jreuteler/bahareque-modular/de/14-akustik-upgrade.md

# Akustik-Upgrade — Lärmexponierte Wände

> *Dieses Kapitel wurde durch einen Vorschlag von Kim Hansson angeregt — vielen Dank für den Anstoss, das Design an reale städtische Bedingungen anzupassen.*

Das Standardpaneel (STC 40–45) ist für ruhige Wohngebiete ausreichend. Für Gebäude an stark befahrenen Strassen, in der Nähe von Autobahnen oder neben Gewerbe- und Industriezonen können die lärmexponierten Wände einzeln aufgerüstet werden. Es ist nicht nötig, jede Wand aufzurüsten — die meisten Gebäude haben nur eine oder zwei Seiten, die starkem Lärm ausgesetzt sind. Die ruhigen Wände bleiben Standardpaneele.

## Lärmexpositions-Leitfaden

| Situation | Empfohlene Massnahme | Ziel-STC |
|---|---|---|
| Ruhige Wohnstrasse | Standardpaneel — kein Upgrade nötig | 40–45 |
| Mässiger Strassenverkehr | Dichter Mörtel + Lehm-Dämpfungsschicht | 48–52 |
| Stark befahrene Stadtstrasse, Buslinien | Doppelpaneel mit Faser-Hohlraum | 55–62 |
| Autobahn, Industrie, Ausgehviertel | Doppelpaneel mit Faser-Hohlraum + Lehmschicht | 58–65 |

**Das Upgrade nur dort anwenden, wo es nötig ist.** Ein typisches Haus an einer belebten Strasse hat ein oder zwei lärmexponierte Wände (10–15 m²). Die übrigen Wände zeigen zum Garten, Innenhof oder zur ruhigen Seite und verwenden Standardpaneele. So bleibt der Mehraufwand proportional zum tatsächlichen Lärmproblem.

## Option 1: Dichtere Mörtelmischung (günstigste Variante, +3–5 STC)

Der Standard-Flusssand wird durch schwerere Zuschlagstoffe in der Mörtelmischung ersetzt. Gleicher Produktionsprozess, gleicher Rahmen, gleicher Rütteltisch-Guss. Das Paneel ist einfach schwerer.

| Zuschlagstoff | Dichtezunahme | Kosten vs. Standardsand | Verfügbarkeit |
|---|---|---|---|
| Gebrochener Basalt oder Granitfeinteile | +15–20% | Ähnlich | Überall — jeder Steinbruch |
| Eisenschlacke (*escoria*) | +25–30% | Oft gratis | In der Nähe von Stahlwerken, Giessereien |
| Magnetitsand (*arena negra*) | +40% | Gering | Vulkanische Flussbetten (Anden, Zentralamerika) |

- **Paneelgewicht:** fertig ~490–530 kg Basismischung (vs. ~440 kg Standard-Basis) / ~405–440 kg optimierte Mischung (vs. ~360 kg Standard-optimiert). Trockenmontage-Gewicht unverändert bei ~75 kg (dichter Zuschlagstoff wird beim Vor-Ort-Guss zugegeben, nicht in der Werkstattmontage)
- **Mehrkosten:** ~$1–2 pro Paneel
- **STC:** ~43–48
- **Produktionsänderung:** Keine — nur den Zuschlagstoff austauschen. Mischverhältnis bleibt 1:4 Zement:Zuschlag.

**Ideal für:** Seitenwände, die eine moderate Verbesserung brauchen, ohne die Wandstärke oder den Bauprozess zu ändern.

## Option 2: Lehm-Dämpfungsschicht (+5–8 STC)

Eine 10–15 mm dicke Schicht aus **Lehm-Stroh-Putz** wird auf der Innenseite der lärmexponierten Wand aufgetragen, vor Ort zwischen der Mörteloberfläche und dem Kalkputz-Finish.

### Warum Lehm funktioniert

Lehm hat eine überlegene akustische Dämpfung im Vergleich zu Zementmörtel. Wenn Schallwellen auf eine Lehmschicht treffen, wird mehr Energie in Wärme umgewandelt (innere Reibung in den Lehmpartikeln), statt durch die Wand übertragen zu werden. Gehäckselte Strohfasern im Lehm erzeugen zusätzliche innere Reibung.

Das ist die traditionellste Bahareque-Technik — Lehmputz (*pañete de tierra*) wird seit Jahrhunderten auf Bambuswänden eingesetzt. Er funktioniert akustisch aus dem gleichen Grund wie thermisch: Lehm ist ein natürlicher Energieabsorber.

### Verarbeitung

1. Lehm-Stroh-Mischung herstellen: lokaler Lehm + gehäckseltes trockenes Gras oder Stroh (5–10 cm Länge), zu einer dicken Paste gemischt
2. 10–15 mm auf die Innenseite der lärmexponierten Wand auftragen, über der Mörteloberfläche
3. Trocknen lassen (3–7 Tage je nach Luftfeuchtigkeit)
4. Kalkputz (3–5 mm) als Deckschicht über die Lehmschicht auftragen
5. Kalkanstrich wie gewohnt

### Spezifikationen

- **Gesamtwandstärke:** ~100 mm (vs. 85 mm Standard)
- **Mehrkosten:** ~$2–4 pro Paneelfläche (Lehm ist normalerweise gratis — beim Aushub der Fundamente gewonnen)
- **STC:** ~45–50
- **Produktionsänderung:** Keine am Paneel selbst. Die Lehmschicht wird vor Ort nach der Montage aufgetragen.

**Ideal für:** Kostengünstiges Upgrade. Verwendet kostenloses lokales Material. Keine Änderung der Paneelproduktion. Verbessert nebenbei die Feuchtigkeitsregulierung.

## Option 3: Doppelpaneel mit Faser-Hohlraum (beste Akustikleistung, +15–20 STC)

Zwei Standardpaneele mit einem 50–100 mm Hohlraum dazwischen, gefüllt mit loser organischer Faser. Das ist die Hochleistungsoption für wirklich laute Umgebungen.

### Warum das funktioniert

Drei akustische Prinzipien wirken zusammen:

1. **Doppelte Masse** — zwei Mörtelwände statt einer. Das Massegesetz besagt, dass eine Verdoppelung der Masse ~6 dB Schalldämmung hinzufügt.
2. **Entkopplung** — der Lufthohlraum unterbricht den Schwingungsweg. Schall überträgt sich effizient durch feste Materialien, aber schlecht über einen Luftspalt. Die beiden Paneele schwingen unabhängig voneinander.
3. **Absorption** — lose Faser im Hohlraum absorbiert Schallenergie, die sonst zwischen den beiden Paneelen hin- und herreflektiert würde (stehende Wellenresonanz).

### Hohlraumfüllung

Verwenden Sie, was lokal verfügbar und günstig ist. Die Füllung sollte **lose, nicht verdichtet** sein — die Lufteinschlüsse in der Faser sind es, die den Schall absorbieren.

| Material | Akustische Qualität | Kosten | Regionale Verfügbarkeit |
|---|---|---|---|
| **Reishülsen** (*cascarilla de arroz*) | Hervorragend | Gratis–$2/Sack | Reisanbaugebiete (Asien, Lateinamerika) |
| **Kokosfaser** (*fibra de coco*) | Hervorragend | $3–5/Sack | Tropische Küstenregionen |
| **Getrocknetes Sterngras** (*pasto estrella*) | Gut | Gratis | Tropisches Amerika (invasiv, wird von Feldern entfernt) |
| **Holzspäne** (*viruta*) | Gut | Gratis–$1/Sack | Schreinereien |
| **Loser Vulkankies** (*gravilla volcánica*) | Gut (massebasiert) | $2–3/Sack | Vulkanregionen (Anden, Zentralamerika, SO-Asien) |
| **Getrocknete Bananblattfaser** | Gut | Gratis | Bananenanbaugebiete |

**Reishülsen sind die beste Allround-Option**, wo verfügbar: leicht, verdichten sich nicht über die Zeit, von Natur aus feuerbeständig (hoher Siliziumgehalt) und extrem günstig oder gratis von Reismühlen.

### Konstruktion

1. Das äussere Paneel wie gewohnt montieren (an Gebäuderahmen oder Ringbalken verschraubt)
2. Einen 50–100 mm Spalt lassen (durch Abstandhalter oder eine breitere Stütze/Montagehalterung)
3. Den Hohlraum lose mit Fasermaterial füllen — nicht verdichten
4. Das innere Paneel montieren und den Hohlraum schliessen
5. Beide Paneele werden an derselben Tragstruktur verschraubt

Die Hohlraumbreite hängt vom verfügbaren Platz und der gewünschten Leistung ab:

| Hohlraumbreite | STC-Verbesserung | Gesamtwandstärke |
|---|---|---|
| 50 mm | +12–15 STC | ~220 mm |
| 75 mm | +15–18 STC | ~245 mm |
| 100 mm | +18–20 STC | ~270 mm |

### Spezifikationen

- **Gesamtwandstärke:** 220–270 mm (vs. 85 mm Standard)
- **Mehrkosten:** ~$65–70 pro m² (ein zusätzliches Paneel) + $2–5 für Hohlraumfüllung = ~$70–75 extra pro m²
- **STC:** 55–62
- **Produktionsänderung:** Keine — verwendet zwei Standardpaneele

**Ideal für:** Strassenfronten an belebten Strassen, Gebäude an Autobahnen, Schlafzimmer an lauten Strassen, Musikräume, Werkstätten neben Wohnräumen.

## Kombinierte Optionen

Die Optionen lassen sich stapeln. Für maximale Akustikleistung an einer kritischen Wand:

| Kombination | STC | Mehrkosten/m² | Einsatzfall |
|---|-----|---|---|
| Standardpaneel | 40–45 | Basis | Ruhige Seite |
| Nur dichter Mörtel | 43–48 | +$1–2 | Leichter Lärm, günstigstes Upgrade |
| Dichter Mörtel + Lehmschicht | 48–52 | +$3–6 | Mässiger Strassenlärm, Einzelwand |
| Doppelpaneel + Faser-Hohlraum | 55–62 | +$70–75 | Stark befahrene Strasse |
| Doppelpaneel (dichter Mörtel) + Faser-Hohlraum + Lehm innen | 58–65 | +$75–80 | Autobahn, Industrie, Nachtclub nebenan |

## Typisches Gebäudebeispiel

Ein einstöckiges Haus an einer belebten Strassenecke, mit Garten auf zwei Seiten:

| Wand | Ausrichtung | Massnahme | STC | Mehrkosten |
|---|---|---|-----|---|
| Nordwand (10 m²) | Stark befahrene Strasse | Doppelpaneel + Reishülsen | 55–60 | ~$700–750 |
| Ostwand (6 m²) | Nebenstrasse | Dichter Mörtel + Lehmschicht | 48–52 | ~$20–36 |
| Südwand (10 m²) | Garten | Standardpaneel | 42–45 | $0 |
| Westwand (6 m²) | Nachbargarten | Standardpaneel | 42–45 | $0 |
| **Gesamte Mehrkosten** | | | | **~$720–790** |

Für ~$750 erhält die lauteste Wand eine professionelle Schalldämmung, während die ruhigen Wände Standard bleiben. Das Akustik-Upgrade macht weniger als 10% der Gesamthauskosten aus der [Kostenschätzung](09-kostenschaetzung.md) aus.

## Materialhinweise

### Brandschutz der Hohlraumfüllung

- **Reishülsen:** Hoher Siliziumgehalt, von Natur aus feuerbeständig. Unterhält keine Flamme. Glimmt, erlischt aber von selbst.
- **Kokosfaser:** Entzündet sich langsam, erlischt von selbst wenn lose.
- **Getrocknetes Gras/Stroh:** Leichter entflammbar. Mit Boratlösung behandeln (gleiche Behandlung wie für Bambus) für Feuerbeständigkeit bei Verwendung im Hohlraum. Der Hohlraum ist zwischen zwei Mörtelpaneelen versiegelt, daher ist das Entzündungsrisiko ohnehin sehr gering.
- **Vulkankies:** Nicht brennbar.

### Feuchtigkeit im Hohlraum

Der Hohlraum muss trocken bleiben. Beide Paneele sind mörtelversiegelt und kalkverputzt — Feuchtigkeit sollte nicht eindringen. Trotzdem:

- Das Doppelpaneel-System nicht unter Geländeniveau oder in hochwassergefährdeten Bereichen verwenden
- Sicherstellen, dass die Oberseite des Hohlraums versiegelt ist (Ringbalken oder Mörtelkappe)
- In extrem feuchten Klimazonen kleine Belüftungsöffnungen oben und unten am Hohlraum lassen (mit Gitter gegen Insekten abgedeckt), um Luftzirkulation zu ermöglichen

### Nachrüstung

Das Akustik-Upgrade kann **nachträglich** an einer bestehenden Standardpaneel-Wand angebracht werden:

1. Eine zweite Paneelwand 50–100 mm innerhalb der bestehenden Wand errichten
2. Den Hohlraum mit Faser füllen
3. Der Innenraum verkleinert sich um die Hohlraumbreite + Paneelstärke (~135–185 mm pro aufgerüsteter Wand)

So ist es möglich, jetzt Standardpaneele zu bauen und bestimmte Wände später aufzurüsten, falls Lärm zum Problem wird — zum Beispiel, wenn eine ruhige Strasse nach einer Erschliessung stark befahren wird.
