jreuteler/bahareque-modular/en/01-philosophy.md

# BaharequeModular — Design Philosophy

## Origin — Learning by Doing

This system was not designed at a desk. It grew out of hands-on experience with permaculture and bioconstruction courses in rural Colombia — building with guadua, mixing mortar, plastering walls, and seeing firsthand what works, what fails, and why.

In those courses, you learn to appreciate the extraordinary qualities of natural materials: the strength of guadua bamboo, the breathability of lime, the thermal comfort of earthen walls, the beauty of hand-finished surfaces. You also learn the limits. Bioconstruction projects — however well-intentioned — often struggle with:

- **Durability.** Earth walls erode in heavy tropical rain. Untreated bamboo is eaten by insects within years. Buildings that took months of community effort start degrading within a decade.
- **Structural safety.** Traditional bahareque and adobe perform poorly in earthquakes unless carefully engineered. Most community-built projects don't have access to structural engineers. The 1999 Armenia earthquake in Colombia killed over 1,000 people — many in unreinforced masonry and poorly built traditional structures.
- **Building permits and insurance.** In most countries, earth and bamboo buildings cannot be formally permitted or insured. Families who build with natural materials often have no legal protection for their home.
- **Finish quality.** Bioconstruction workshops produce beautiful demonstration walls. But scaling to a full house — with consistent surfaces, integrated electrical, plumbing, and a finish that withstands years of weather — is a different challenge. Many projects look rough compared to conventional construction, reinforcing the perception that "natural = poor quality."
- **Reproducibility.** Each bioconstruction project depends on the skill of the builders present. There is no standardized panel, no production line, no quality control process. When the experienced builder leaves, the quality drops.

These are not failures of the materials or the philosophy — they are failures of the system around them. Guadua is as strong as steel in tension. Lime plaster has protected buildings for millennia. The problem is not the ingredients. The problem is that no one had packaged them into a **repeatable, quality-controlled, structurally engineered, code-compliant system** that a community can produce without depending on a master builder.

That is what this project attempts to solve.

## The Problem

Most "affordable housing" in the developing world faces a difficult trade-off:

- **Traditional construction** (bamboo, adobe, wattle-and-daub) is beautiful, breathable, culturally meaningful, and uses local materials — but it cracks in earthquakes, degrades in heavy rain, and rarely gets building permits or insurance.
- **Modern construction** (concrete block, reinforced concrete frame) gets permits and survives earthquakes — but it's expensive, requires specialized labor, looks identical everywhere, and has no connection to place or culture.

The result: billions live in buildings that either fail structurally or fail the people who inhabit them.

## A Worldwide Tradition

This system stands on the shoulders of millennia of building knowledge. Across every continent, cultures developed frame-and-infill construction — a structural frame filled with natural materials. These techniques evolved independently because they work. They are earthquake-resistant, thermally comfortable, repairable, and beautiful.

### Bahareque (Colombia, Ecuador, Central America)

Bamboo frame (guadua) filled with mud, mortar, or wattle. The traditional building method of Colombia's Eje Cafetero region, recognized by UNESCO as cultural heritage. Bahareque buildings survived the 1999 Armenia earthquake far better than unreinforced masonry. The Coffee Cultural Landscape of Colombia — a UNESCO World Heritage site — is defined by its bahareque architecture. This panel system is a direct evolution of bahareque: same materials, same philosophy, engineered for modern performance.

### Quincha (Peru, Chile, Argentina)

Bamboo or cane frame with mud plaster, used since pre-Columbian times. Lima's colonial center was rebuilt in quincha after the 1746 earthquake — the flexible frames survived subsequent earthquakes that destroyed rigid masonry buildings. Quincha is still used in rural Peru and is experiencing a revival in sustainable architecture circles.

### Wattle-and-Daub (Global — Europe, Africa, Asia, Americas)

The oldest known building technique, dating back 6,000+ years. Woven sticks (wattle) coated with mud or clay (daub). Found in medieval English cottages, West African compounds, Japanese *tsuchikabe* walls, and Mesoamerican structures. Many wattle-and-daub buildings in Europe have stood for 500+ years. The principle — a lattice of organic material encased in a mineral matrix — is exactly what this panel system uses.

### Fachwerk / Colombage (Germany, France, Northern Europe)

Timber frame with infill panels (brick, straw, or mud). Known as *Fachwerk* in Germany, *colombage* in France, *half-timbering* in England. Thousands of buildings from the 14th–18th century still stand and are inhabited today. The key insight: the frame carries the structure, the infill provides enclosure. This is the same principle as the steel frame + bahareque panel.

### Dhajji-Dewari (Kashmir, Pakistan, Northern India)

Timber frame with stone or mud infill, used in the Himalayan seismic zone. The word means "patchwork quilt wall" in Kashmiri. Dhajji-dewari buildings survived the devastating 2005 Kashmir earthquake while modern concrete structures collapsed. The closely spaced timber members and diagonal bracing create a ductile, energy-absorbing structure — the same principle behind the diagonal bamboo bracing in this panel system.

### Gaiola Pombalina (Lisbon, Portugal)

After the catastrophic 1755 Lisbon earthquake and tsunami, the Marquis of Pombal commissioned a new building system: a timber cage (*gaiola*) with diagonal bracing inside masonry walls. This was the world's first engineered seismic construction standard. The diagonal bracing — converting shear forces to tension — is a direct ancestor of the diagonal bamboo strips in this panel system. Buildings with the Pombaline cage survived subsequent earthquakes for over 250 years.

### Bajareque (Honduras, El Salvador, Guatemala)

Central American variant of bahareque, using local bamboo or cane with mud infill. Bajareque is experiencing renewed interest as communities seek earthquake-resistant, affordable alternatives to concrete block.

### Taquezal (Nicaragua)

Similar to bahareque — timber or bamboo frame filled with mud/straw mixture. Traditional in Nicaraguan colonial architecture. León and Granada's historic centers feature taquezal construction.

### Tabique (Mexico, Philippines)

In Mexico: bamboo or reed frame (*carrizo*) with mud plaster, common in Oaxaca, Guerrero, and Chiapas. In the Philippines: bamboo-framed walls (*tabique pampanga*) used in colonial-era buildings. Both demonstrate the universality of bamboo-frame construction across tropical regions.

### Tsuchikabe (Japan)

Traditional Japanese earthen walls built on a bamboo lattice (*komai*). Multiple layers of earth plaster are applied over the woven bamboo — coarse base coat, intermediate coat, and fine finish coat. The same layered approach (structural lattice + mineral encasement + fine plaster finish) used in this panel system.

### Pau-a-Pique (Brazil)

Brazilian wattle-and-daub using wooden stakes (*paus*) woven with bamboo or vines and plastered with earth. Common in rural Brazil since colonial times. Known for thermal comfort in Brazil's varied climates.

---

**This panel system takes the core insight shared by all these traditions — a lattice of organic material encased in a mineral matrix, supported by a structural frame — and engineers it for modern performance: galvanized steel instead of raw timber, treated bamboo instead of untreated cane, pozzolanic mortar instead of raw mud, screw-clamping instead of rope binding. The wisdom is ancient. The execution is modern. The result lasts 80–100 years.**

## The Hybrid Approach

This panel system resolves the trade-off between traditional and modern construction:

**Traditional where it's seen.** The exterior surface is lime plaster over bamboo and mortar — the same materials used in bahareque, quincha, wattle-and-daub, and tsuchikabe for centuries. The texture is handmade. The surface breathes. The building belongs to its place.

**Modern where it matters.** Inside each panel is a hot-dip galvanized steel L-angle frame engineered for seismic loads. This frame is invisible once the panel is finished. It carries the structural reality while the traditional materials carry the human experience.

## Permaculture Integration

The system embodies permaculture principles:

- **Use local resources:** Guadua angustifolia grows naturally across tropical Latin America at 0–2,000 m altitude. It reaches harvest size in 4–5 years. One hectare can supply enough guadua for dozens of panels annually.
- **Turn problems into solutions:** Invasive star grass (*Cynodon nlemfuensis*), a common agricultural pest, is dried, chopped, and used as fiber reinforcement in lime plaster. Removing the invasive species improves the land; using it in construction closes the loop.
- **Build soil, not waste:** Excavated volcanic ash soil (Andisol) from foundations becomes premium growing medium for raised beds and food forest terracing.
- **Design for succession:** An 80–100 year building outlasts the builder. The next generation inherits a home, not a rebuild project.

## Bioconstruction, Engineered

Bioconstruction is not nostalgia. It is the recognition that natural materials — bamboo, lime, earth, stone — have physical properties that modern materials struggle to match:

- **Lime plaster** is antifungal, breathable, self-healing (carbonation fills micro-cracks), and beautiful. No paint needed.
- **Guadua bamboo** has a tensile strength comparable to mild steel, grows without irrigation, and sequesters carbon as it grows.
- **Mortar with pozzolanic admixture** (volcanic ash, rice husk ash, or metakaolin) reduces alkalinity over time, extending the life of embedded organic materials.

The steel frame doesn't replace these materials — it supports them. The frame handles what bamboo and mortar cannot: concentrated point loads, moment connections, and code-compliant seismic resistance.

## Not Just Affordable — Beautiful

This is not a compromise system. The finished wall — hand-troweled lime plaster over dense mortar — produces a surface quality that competes with construction techniques costing 5–10× more.

- **Lime plaster** has been the finish of choice for palaces, cathedrals, and luxury villas for millennia. The same material covering a Tuscan farmhouse or a Colombian hacienda covers these panels. Each wall has the subtle texture of handwork — no two surfaces are identical.
- **Lime wash** develops a depth and warmth that paint cannot match. It interacts with light differently at every hour. It ages gracefully — gathering a patina rather than peeling.
- **The wall is solid.** Knock on it — it sounds and feels like stone. There is no hollow cavity, no drywall flex. The 85 mm mortar core gives the wall a permanence that lightweight construction cannot replicate.
- **No visible fasteners, joints, or seams.** Once plastered, the wall is continuous. No one can tell where one panel ends and the next begins. No one can tell there is a steel frame inside. The building looks and feels like traditional masonry construction.

Someone entering a building made with these panels would not know — or care — that the walls were prefabricated in a workshop by a community team. They would see smooth plaster, feel solid walls, and experience a building with the character of handmade construction. That the building also survives earthquakes, lasts 80–100 years, and was built at a fraction of the cost of conventional construction is invisible.

**This is the point:** affordable and beautiful are not opposites. The same techniques that kept the cost low — lime instead of paint, mortar instead of drywall, bamboo instead of steel studs — are the techniques that produce the most beautiful result.

## Build Once — 80–100 Year Lifespan

A house that lasts 15 years is not affordable. It is a debt trap with a roof.

A house that lasts 80–100 years is built once. The family invests once. The community builds once. The materials are consumed once. Everything after that is maintenance — lime wash every 5–10 years, plaster inspection every 15–20 years.

The cost per year of a 100-year building is a fraction of a 15-year building, even if the initial construction costs more.

## Community Production

The screw-clamping system was designed specifically for community production:

- **No welding required** during panel assembly (frames are pre-welded in a workshop, but assembly is screws only)
- **No specialized tools** — drill, screwdriver, basic hand tools
- **Self-adjusting** — the clamping strip flexes to accommodate natural thickness variation in guadua strips
- **Teachable in days** — a community team can learn to produce panels with 2–3 days of training
- **Production rate** — a team of 4–6 people with 2 vibration tables produces 3–4 panels per day

## Prior Art & Related Systems

This project does not exist in a vacuum. Several systems have explored bamboo-based prefabricated or engineered construction. We build on their work and acknowledge their contributions.

### Engineered Bahareque — Sebastian Kaminski (Arup / INBAR)

The most cited academic work on modern bahareque. Kaminski's [Design Guide for Engineered Bahareque Housing](https://www.researchgate.net/publication/311583390_Design_Guide_for_Engineered_Bahareque_Housing) (published with INBAR and Fundación Redes) provides the structural engineering foundation for cemented bahareque walls — guadua skeleton frames with bamboo mat infill, wire mesh reinforcement, and cement mortar render. His work underpins the Colombian NSR-10 building code for bahareque encementado (Chapter G-1). Over 4,000 homes built across Colombia, Costa Rica, Nepal, Ecuador, Peru, Mexico, El Salvador, and the Philippines.

**How this system differs:** Kaminski's approach is in-situ construction — walls are built on-site by skilled craftspeople, one layer at a time. The finish depends heavily on workmanship. Our system industrializes this into standardized prefabricated panels: steel T-bar frame (not timber/bamboo), screw-clamped strips (not nailed mats), vibration-table mortar pour (not troweled on-site), and integrated snap-connect electrical. The goal is consistent quality at community-production speed, with a finished wall surface suitable for residential and commercial buildings.

### Cement Bamboo Frame Technology (CBFT) — BASE Bahay / Hilti Foundation

The most scaled bamboo construction system in the world: 2,400+ housing units built in the Philippines, Nepal, India, and Sri Lanka. CBFT uses treated bamboo frames with metal connections, flattened bamboo (esterilla) infill, wire mesh, and cement mortar. Panels are prefabricated in workshops. Designed for typhoon winds up to 300 km/h and earthquakes up to magnitude 7–8. Target lifespan: ~60 years. Training provided through the Bamboo Academy.

**How this system differs:** CBFT uses bamboo/wood as the frame structure. Our system uses galvanized steel L-angle — providing higher axial capacity, longer corrosion-protected lifespan (80–100 years vs. 60), and a consistent clamping surface for the screw system. CBFT does not include integrated electrical. CBFT is proprietary (training-based access); our system is open hardware.

- [BASE Bahay — Hilti Foundation](https://www.hiltifoundation.org/basebahaybamboo)
- [BASE Builds](https://base-builds.com/tag/cement-bamboo-frame-technology-2/)

### Bamboo Composite Shear Walls — Chinese Academic Research

Recent research from Chinese universities has tested sprayed composite mortar walls with original bamboo studs and **diagonal bamboo bracing** — structurally the closest match to our panel's diagonal bracing concept. Quasi-static cyclic loading tests showed good energy dissipation and ductile failure behavior with diagonal strips. The mortar is sprayed rather than vibration-poured, and there is no steel frame.

**How this system differs:** Our in-situ vertical pour (or optional workshop vibration-table pour) achieves more complete mortar fill (zero voids) without spray equipment. The steel L-angle frame adds axial load capacity and provides a standardized clamping surface. However, the Chinese research provides the best published validation that diagonal bamboo bracing in mortar composite works structurally — we build on this evidence.

- [Diagonal bamboo strips seismic study (ScienceDirect)](https://www.sciencedirect.com/science/article/abs/pii/S2352710223020090)

### Housing NOW / Blue Temple — Myanmar

Modular bamboo housing using interlocking arched bundled bamboo frames. 26 homes built with community labor at ~$1,000 per unit. In March 2025, all 26 survived a magnitude 7.7 earthquake with **zero structural damage** — the most impressive real-world seismic validation of any bamboo housing system to date.

**How this system differs:** Completely different structural approach (arched bundled bamboo, no mortar, no steel). But their community-production model and proven earthquake survival are powerful validation of bamboo's seismic potential. If bundled bamboo arches survive M7.7, mortar-encased bamboo strips in a steel frame should perform at least as well.

- [Housing NOW](https://www.housing-now.org/)
- [Dezeen — Blue Temple bamboo housing](https://www.dezeen.com/2025/12/30/blue-temple-housing-now-bamboo-housing-myanmar/)

### WikiHouse — UK

Open-source CNC-cut plywood construction system. Creative Commons licensed blueprints on GitHub. Community-assembled. Not bamboo-based, but the closest model for how an open-source construction system can be documented, licensed, and distributed. WikiHouse demonstrates that open-source building is viable.

**How this system differs:** Different materials (plywood vs. bamboo+mortar+steel), different climate target (temperate vs. tropical), different production method (CNC vs. workshop). But WikiHouse's licensing approach (CC files on GitHub) and community model informed the structure of this repository.

- [WikiHouse](https://www.wikihouse.cc/faq)

### Quincha Prefabricada — Peru

Prefabricated quincha panels — sawn timber frames filled with woven round cane in interlocking patterns (no nails needed for infill), plastered with mud-straw mix. Construction manuals publicly available (PREDES). Lima's colonial center was rebuilt in quincha after the 1746 earthquake — these flexible frames survived subsequent earthquakes that destroyed rigid masonry.

**How this system differs:** Quincha uses timber frames (not steel), mud plaster (not pozzolanic mortar), and woven cane (not screw-clamped strips). No integrated electrical. But quincha prefabricada proves that prefabricated bamboo/cane panels with plaster infill are a viable, earthquake-resistant construction method — a direct ancestral validation of this system's approach.

- [Quincha Prefabricada (ResearchGate)](https://www.researchgate.net/publication/270074951_Sistema_constructivo_Quincha_Prefabricada)
- [Manual Quincha Mejorada (PREDES)](https://www.predes.org.pe/wp-content/uploads/2017/11/manual_quincha_mejorada.pdf)

### Colombian NSR-10 — Bahareque Encementado Standard

Not a system but the regulatory framework: Colombian seismic code NSR-10, Chapter G-1 (formerly E-7), governs cemented bahareque construction. Any building using this panel system in Colombia would reference this standard. The code recognizes guadua frame + bamboo mat + wire mesh + cement mortar as a code-compliant wall system.

- [Manual Bahareque Encementado (PDF)](https://www.desenredando.org/public/libros/2001/csrvbe/guadua_lared.pdf)

---

### What's New in This System

For clarity, the following features have **no documented equivalent** in any existing system:

| Feature | Status |
|---|---|
| Galvanized steel L-angle frame for bamboo panels (commodity stock profile) | Novel |
| Screw-clamping system (self-adjusting for thickness variation) | Novel |
| Vibration table mortar pour on sand bed | Novel |
| Integrated 12V + 120V snap-connect electrical | Novel |
| Open hardware license (CERN-OHL-S) for bamboo construction | Novel |
| 80–100 year design lifespan for bamboo-mortar panels | Novel (CBFT targets 60) |
| )( flex profile from HDPE spacer blocks | Novel |
| Diagonal bamboo bracing through corner-notched spacer blocks | Novel combination |

This system is an evolution, not an invention from scratch. It combines proven principles from bahareque, quincha, Fachwerk, and Pombaline construction with modern engineering, materials science, and open-source distribution.

## Open Source

This system is open source because:

1. Housing is a human right. The knowledge to build safe, dignified shelter should not be a commercial secret.
2. The system gets better with every community that builds. A carpenter in Manizales, a builder in Indonesia, an engineer in Nepal — each can improve the design and share it back.
3. Patents on construction techniques create artificial scarcity of knowledge. Publishing the design as open hardware creates permanent prior art that no one can close.
4. The best construction systems in history spread through open sharing — vernacular architecture evolved over centuries through exactly this process. We're just doing it with version control.

This project is licensed under CERN-OHL-S v2 (hardware) and CC BY-SA 4.0 (documentation). This means all derivatives must remain open. The knowledge stays free, forever.
