jreuteler/bahareque-modular/en/11-transport-handling.md

# Transport & Handling

## Panel Specifications for Handling

| Property | Value |
|---|---|
| Dimensions | 1.0 m × 2.5 m × 85 mm |
| Dry assembly weight (as shipped to site) | **~75 kg** |
| Finished panel weight (baseline mix, after in-situ pour + cure + plaster) | ~440 kg |
| Finished panel weight (optimized bahareque mix) | ~360 kg |
| Center of gravity | Center (symmetric construction) |
| Fragile areas | Corners, edges (mortar can chip if impacted once poured) |
| Minimum cure before handling | 7 days after in-situ pour |
| Minimum cure before installation | 14 days recommended — but note: in the in-situ pour model, the panel is erected and mortar is poured in place, so "installation" and "pour" happen together on-site, not sequentially |

## Primary Production Model: In-Situ Pour

**The primary production model is to ship the dry assembly (~75 kg) to the site and pour mortar in-situ against formwork.** The finished ~440 kg panel is never moved as a unit — it becomes part of the building wall directly, saving heavy-lift equipment cost and eliminating transport-cracking risk. See [Construction Process](04-construction-process.md) for the vertical in-situ pour protocol.

Cured-panel handling (sections below) applies to the alternative production model: workshop mortar-pour on a vibration table, with fully cured panels shipped to site as finished elements. This approach is retained as a documented option for builders who prefer workshop production, but adds significant lifting, transport, and rejection-rate overhead.

## Carrying by Hand — Dry Assembly (~75 kg)

The dry assembly (steel L-angle frame + bamboo esterilla + mesh + services, pre-mortar) is lifted and positioned by **2 people with a simple webbing strap**. No carrying jig, no crane, no forklift required — this is one of the core operational advantages of the in-situ pour production model.

### Simple webbing-strap carry (dry assembly)

1. Wrap a single 50 mm × 500+ kg rated webbing strap around the dry panel at mid-height (~125 cm from the bottom)
2. Each carrier grips one end of the strap with both hands, standing on opposite long sides of the panel
3. Lift together; the panel hangs vertically between them
4. Walk at normal pace; panel can be carried 30–50 m before a rest is needed

**Weight per person: ~38 kg** — entirely manageable for short-distance carries typical of workshop-to-truck, truck-to-site-storage, and storage-to-installation moves.

## Carrying by Hand — Cured Finished Panel (alternative workshop-pour model)

A finished panel at ~360–440 kg **cannot be carried by hand**. It requires mechanical lift (chain hoist, skid-steer, or small mobile crane). This is the core reason the in-situ pour model is preferred.

If workshop-poured panels must be moved (e.g., pilot-phase production before the in-situ protocol is validated), use:

### Simple Carrying Jig (cured panel, ~360–440 kg)

Two bamboo poles (3 m long, 8–10 cm diameter) threaded through loops of heavy webbing strap wrapped around the panel at 1/4 and 3/4 height:

1. Lay panel flat
2. Wrap two webbing straps (50 mm wide, rated 1 000+ kg) around the panel at ~60 cm and ~190 cm from the bottom
3. Thread a bamboo pole through both strap loops on each side
4. **4 people per pole, 8 carriers total** for a baseline-mix panel at ~440 kg, or 6 carriers for an optimized-mix panel at ~360 kg
5. Panel hangs vertically between the poles

**Weight per person: ~55 kg (baseline) / ~45 kg (optimized)** — at the upper edge of safe manual handling. Long distances or stairs should use mechanical lift instead.

For any routine production workflow, **use a forklift, skid-steer, or chain hoist rather than manual carry** for cured panels. Manual carry of cured panels is an emergency/pilot-only option.

### Lifting and Tilting

- **Never lift a panel by one edge** — the mortar can crack under its own weight if cantilevered
- **Always lift from two points** symmetrically, or from the bottom while supported at the back
- **Tilting from flat to vertical:** Two people hold the top edge, two people lift the bottom. Rotate slowly. Support the bottom on a padded block during rotation.

## Workshop Storage

After curing, panels are stored **vertically (on edge)** in an A-frame rack:

- Lean panels against both sides of an angled frame (like an open book)
- 10–15 panels per side of the rack
- Separate panels with small wooden spacers to allow air circulation
- Cover with tarp or roof to protect from direct rain (curing mortar can be washed out if hit by heavy rain before full cure)
- Keep off the ground — place bottom edge on gravel or wooden rail

**Space required:** ~3 m × 1 m floor area per 20–30 panels stored.

## Truck Transport

### Loading

1. Stand panels vertically in the truck bed, leaning against one side wall
2. Place wooden spacers (offcuts, bamboo, or foam) between each panel
3. Strap panels to the truck side wall using ratchet straps at 1/3 and 2/3 height
4. Never stack panels flat on top of each other — the bottom panel will crack under the weight of the stack
5. Maximum ~15–20 panels per standard pickup truck (depending on truck capacity and road conditions)

### Road Considerations

- **Paved roads:** No special precautions beyond strapping
- **Unpaved/rough roads:** Reduce speed. Add foam or cardboard padding between panels. Strap tightly — panels can shift and chip edges on bumps.
- **Steep grades:** Ensure panels lean into the hill (not away from it) to prevent toppling
- **Distance:** No limit. Panels are fully cured and self-contained. They can travel any distance.

### Unloading

1. Remove straps from the top down
2. Two people per panel — one at top edge, one supporting bottom
3. Walk each panel to the A-frame storage rack at the site
4. Never drop or slide panels — mortar edges chip easily

## Crane / Hoist (for upper floors)

For two-story buildings, panels must be lifted to the second floor:

- **Simple gin pole:** A bamboo or steel pole with a rope and pulley. Two people pull the rope, one guides the panel. Works for low volumes.
- **Chain hoist on beam:** Attach a **1 000 kg** chain hoist to the building's steel beam (500 kg hoists are insufficient for cured-panel lifts). Clip to the panel's carrying strap. One person operates, one guides. Fast and controlled. For dry-assembly lifts (~75 kg) a 500 kg hoist is ample.
- **Forklift (if available):** Fork under the panel (protected with cardboard). Lift and place directly into position.

**Do not throw, roll, or drag panels.** The mortar is strong in compression but can crack on point impact.

## Damage and Repair

| Damage type | Cause | Repair |
|---|---|---|
| Corner chip (small) | Impact during transport | Fill with mortar, plaster over. Cosmetic only. |
| Edge crack (surface) | Bumping during handling | Fill with lime plaster. Does not affect structure. |
| Through-crack (mortar) | Dropped or severe impact | Panel may be compromised. Assess: if steel frame is intact and crack is <2 mm, mortar-fill and monitor. If crack is >5 mm or frame is bent, reject panel. |
| Broken snap connector | Snagged during transport | Replace connector (soldered or crimped). |

**Rejection rate:** With reasonable care, expect <5% of panels to suffer any damage during transport and handling, and <1% to require rejection. Rejected panels can be stripped of electrical components and recycled as fill material.

## Checklist Before Transport

- [ ] Panel cured minimum 7 days (14 recommended)
- [ ] Panel marked with type (P/O/S/W) and production date
- [ ] Electrical circuits tested (12V + 120V continuity check)
- [ ] No visible cracks >1 mm
- [ ] Corners intact
- [ ] Carrying straps or jig prepared
- [ ] Truck bed clean, spacers ready, straps available
- [ ] Route checked for road conditions (bridges, clearance, grade)
