jreuteler/bahareque-modular/en/14-acoustic-upgrade.md

# Acoustic Upgrade — Noise-Facing Walls

> *This chapter was inspired by a suggestion from Kim Hansson — thank you for pushing the design to address real-world urban conditions.*

The standard panel (STC 40–45) is adequate for quiet residential areas. For buildings on busy streets, near highways, or adjacent to commercial/industrial zones, the noise-facing walls can be upgraded individually. There is no need to upgrade every wall — most buildings only have one or two sides exposed to significant noise. The quiet-facing walls remain standard panels.

## Noise Exposure Guide

| Situation | Recommended treatment | Target STC |
|---|---|---|
| Quiet residential street | Standard panel — no upgrade needed | 40–45 |
| Moderate street traffic | Dense mortar + clay damping layer | 48–52 |
| Busy urban road, bus routes | Double panel with fiber cavity | 55–62 |
| Highway, industrial, nightlife district | Double panel with fiber cavity + clay layer | 58–65 |

**Apply the upgrade only where needed.** A typical house on a busy street has one or two noise-facing walls (10–15 m²). The remaining walls face a garden, courtyard, or quiet side and use standard panels. This keeps the cost increase proportional to the actual noise problem.

## Option 1: Denser Mortar Mix (cheapest, +3–5 STC)

Replace standard river sand with heavier aggregates in the mortar mix. Same production process, same frame, same vibration table pour. The panel is simply heavier.

| Aggregate | Density increase | Cost vs standard sand | Availability |
|---|---|---|---|
| Crushed basalt or granite fines | +15–20% | Similar | Universal — any quarry |
| Iron slag (*escoria*) | +25–30% | Often free | Near steel mills, foundries |
| Magnetite sand (*arena negra*) | +40% | Low | Volcanic river beds (Andes, Central America) |

- **Panel weight:** finished ~490–530 kg baseline mix (vs ~440 kg standard baseline) / ~405–440 kg optimized mix (vs ~360 kg standard optimized). Dry assembly weight unchanged at ~75 kg (dense aggregate added at in-situ pour, not at workshop assembly)
- **Extra cost:** ~$1–2 per panel
- **STC:** ~43–48
- **Production change:** None — just substitute the aggregate. Mix ratio remains 1:4 cement:aggregate.

**Best for:** Side walls that need a modest improvement without any change to wall thickness or construction process.

## Option 2: Clay Damping Layer (+5–8 STC)

Add a 10–15 mm layer of **clay-straw plaster** on the interior face of the noise-facing wall, applied on-site between the mortar surface and the lime plaster finish.

### Why Clay Works

Clay has superior acoustic damping compared to cement mortar. When sound waves hit a clay layer, more energy is converted to heat (internal friction in the clay particles) rather than being transmitted through the wall. Chopped straw fibers within the clay add additional internal friction.

This is the most traditional bahareque technique — clay plaster (*pañete de tierra*) has been used on bamboo walls for centuries. It works acoustically for the same reason it works thermally: clay is a natural energy absorber.

### Application

1. Prepare a clay-straw mix: local clay + chopped dried grass or straw (5–10 cm lengths), mixed to a thick paste
2. Apply 10–15 mm to the interior face of the noise-facing wall, over the mortar surface
3. Allow to dry (3–7 days depending on humidity)
4. Apply lime plaster (3–5 mm) over the clay layer as the finish coat
5. Lime wash as usual

### Specifications

- **Total wall thickness:** ~100 mm (vs 85 mm standard)
- **Extra cost:** ~$2–4 per panel area (clay is typically free — excavated during foundation work)
- **STC:** ~45–50
- **Production change:** None to the panel itself. Clay layer is applied on-site after installation.

**Best for:** Budget-conscious upgrade. Uses free local material. No change to panel production. Adds humidity regulation as a bonus.

## Option 3: Double Panel with Fiber Cavity (best acoustic performance, +15–20 STC)

Two standard panels with a 50–100 mm cavity between them, filled with loose organic fiber. This is the high-performance option for genuinely noisy environments.

### Why This Works

Three acoustic principles combine:

1. **Double mass** — two mortar walls instead of one. The mass law says doubling mass adds ~6 dB of sound reduction.
2. **Decoupling** — the air cavity breaks the vibration path. Sound transmits efficiently through solid materials but poorly across an air gap. The two panels vibrate independently.
3. **Absorption** — loose fiber inside the cavity absorbs sound energy that would otherwise bounce between the two panels (standing wave resonance).

### Cavity Fill Materials

Use whatever is locally available and cheap. The fill should be **loose, not compacted** — air pockets within the fiber are what absorb sound.

| Material | Acoustic quality | Cost | Regional availability |
|---|---|---|---|
| **Rice husk** (*cascarilla de arroz*) | Excellent | Free–$2/bag | Rice-growing regions (Asia, Latin America) |
| **Coconut coir** (*fibra de coco*) | Excellent | $3–5/bag | Tropical coastal regions |
| **Dried star grass** (*pasto estrella*) | Good | Free | Tropical Americas (invasive, removed from fields) |
| **Wood shavings** (*viruta*) | Good | Free–$1/bag | Carpentry workshops |
| **Loose volcanic gravel** (*gravilla volcánica*) | Good (mass-based) | $2–3/bag | Volcanic regions (Andes, Central America, SE Asia) |
| **Dried banana leaf fiber** | Good | Free | Banana-growing regions |

**Rice husk is the best all-round option** where available: lightweight, doesn't compact over time, naturally fire-resistant (high silica content), and extremely cheap or free from rice mills.

### Construction

1. Install the exterior panel as usual (bolted to building frame or ring beam)
2. Leave a 50–100 mm gap (set by spacers or a wider column/mounting bracket)
3. Fill the cavity loosely with fiber material — do not compact
4. Install the interior panel, closing the cavity
5. Both panels bolt to the same structural frame

The cavity width depends on the available space and desired performance:

| Cavity width | STC improvement | Total wall thickness |
|---|---|---|
| 50 mm | +12–15 STC | ~220 mm |
| 75 mm | +15–18 STC | ~245 mm |
| 100 mm | +18–20 STC | ~270 mm |

### Specifications

- **Total wall thickness:** 220–270 mm (vs 85 mm standard)
- **Extra cost:** ~$65–70 per m² (one additional panel) + $2–5 for cavity fill = ~$70–75 extra per m²
- **STC:** 55–62
- **Panel production change:** None — uses two standard panels

**Best for:** Busy street frontage, highway-adjacent buildings, bedrooms facing noisy roads, music rooms, workshops adjacent to living spaces.

## Combined Options

The options stack. For maximum acoustic performance on a critical wall:

| Combination | STC | Extra cost/m² | Use case |
|---|-----|---|---|
| Standard panel | 40–45 | Baseline | Quiet side |
| Dense mortar only | 43–48 | +$1–2 | Mild noise, cheapest upgrade |
| Dense mortar + clay layer | 48–52 | +$3–6 | Moderate street noise, single wall |
| Double panel + fiber cavity | 55–62 | +$70–75 | Busy road |
| Double panel (dense mortar) + fiber cavity + clay interior | 58–65 | +$75–80 | Highway, industrial, nightclub next door |

## Typical Building Example

A single-story house on a busy street corner, with garden on two sides:

| Wall | Faces | Treatment | STC | Extra cost |
|---|---|---|-----|---|
| North wall (10 m²) | Busy road | Double panel + rice husk | 55–60 | ~$700–750 |
| East wall (6 m²) | Side street | Dense mortar + clay layer | 48–52 | ~$20–36 |
| South wall (10 m²) | Garden | Standard panel | 42–45 | $0 |
| West wall (6 m²) | Neighbor's garden | Standard panel | 42–45 | $0 |
| **Total extra cost** | | | | **~$720–790** |

For ~$750, the noisiest wall gets professional-grade sound insulation while the quiet walls stay standard. The acoustic upgrade adds less than 10% to the total house cost from the [cost estimate](09-cost-estimate.md).

## Material Notes

### Fire Safety of Cavity Fill

- **Rice husk:** High silica content, naturally fire-resistant. Does not sustain flame. Smolders but self-extinguishes.
- **Coconut coir:** Slow to ignite, self-extinguishing when loose.
- **Dried grass/straw:** More flammable. Treat with borate solution (same as bamboo treatment) for fire resistance if using in the cavity. The cavity is sealed between two mortar panels, so ignition risk is very low regardless.
- **Volcanic gravel:** Non-combustible.

### Moisture in the Cavity

The cavity must stay dry. Both panels are mortar-sealed and lime-plastered — moisture should not enter. However:

- Do not use the double-panel system below grade or in flood-prone areas
- Ensure the top of the cavity is sealed (ring beam or mortar cap)
- In extremely humid climates, leave small ventilation gaps at the top and bottom of the cavity (covered with mesh to prevent insect entry) to allow air circulation

### Retrofit

The acoustic upgrade can be **added later** to an existing standard-panel wall:

1. Build a second panel wall 50–100 mm inside the existing wall
2. Fill the cavity with fiber
3. The interior room shrinks by the cavity width + panel thickness (~135–185 mm per upgraded wall)

This makes it possible to build standard panels now and upgrade specific walls later if noise becomes a problem — for example, if a quiet road becomes busy after development.
