jreuteler/bahareque-modular/es/05-desempeno-estructural.md

# Desempeño Estructural

## Arquitectura del Sistema

Este sistema de paneles fue diseñado para funcionar **con un marco de acero de columnas y vigas** — la configuración que recomendamos para edificaciones de varios pisos en zonas sísmicas. En esa configuración, el marco de acero soporta las cargas gravitacionales y sísmicas mientras los paneles proporcionan arriostramiento lateral, cerramiento climático, masa térmica y servicios integrados.

Sin embargo, los paneles son **estructuralmente capaces de funcionar sin un marco de acero**. Con capacidad de compresión que excede ampliamente las cargas residenciales típicas (dos postes laterales de ángulo L L 40×40×4), una fila de paneles puede soportar cómodamente un segundo piso y techo sin una estructura de acero independiente. Una viga de coronación simple de madera o bambú en la parte superior conecta los paneles y distribuye la carga del techo.

**Dos configuraciones:**

| Configuración | Caso de uso | Rol del panel |
|---|---|---|
| **Con marco de acero** (recomendado) | Varios pisos, zonas de alta sismicidad, comercial/institucional | Relleno — los paneles se empernan al marco, el acero soporta las cargas principales |
| **Sin marco de acero** (más simple, menor costo) | Un piso + altillo/mezzanine, zonas de sismicidad moderada, residencial | Portante — los paneles soportan el techo y el piso superior directamente |

Las estimaciones de capacidad de carga a continuación aplican para ambas configuraciones. El marco de acero agrega redundancia y resistencia a momento, pero no es requerido para que los paneles funcionen estructuralmente.

## Desempeño Sísmico

### Arriostramiento Diagonal

Cada panel contiene dos tiras diagonales de bambú (una por lado, en esquinas opuestas), formando una X vista de frente. Bajo carga sísmica:

1. **Conversión de corte a tracción:** Cuando el marco de la edificación se desplaza lateralmente, una diagonal entra en tracción mientras la opuesta entra en compresión. La diagonal de bambú en tracción resiste la fuerza de desplazamiento eficientemente — el bambú tiene excelente resistencia a la tracción (150–200 MPa para Guadua angustifolia).
2. **Pre-tensión:** Las diagonales se instalan con ligera pre-tensión, eliminando la holgura y asegurando activación inmediata bajo carga.
3. **Cuadrícula de amarres de alambre:** Los amarres de alambre galvanizado en cada cruce diagonal-vertical (~16–20 amarres en total) distribuyen la fuerza diagonal a lo largo de toda la cara del panel, previniendo falla localizada.

**Mejora estimada: 3–5× en resistencia al volcamiento** comparado con paneles sin arriostramiento diagonal.

### El Perfil )(

Los bloques de HDPE mantienen las tiras de bambú a 30 mm del alma en la parte superior e inferior. A media altura, las tiras se flexionan hacia adentro acercándose al alma. El mortero llena este espacio variable, creando una sección transversal de arco natural:

- **Resistencia fuera de plano:** El arco de mortero actúa como una bóveda poco profunda, distribuyendo eficientemente las cargas de viento o impacto hacia los bordes rígidos del marco.
- **Traba mecánica:** El mortero de espesor variable traba las tiras de bambú en su posición — no se pueden sacar sin romper el mortero.

### Modo de Falla Dúctil

La combinación de tiras de bambú, amarres de alambre y mortero crea un compuesto que falla gradualmente:

1. Primero: el mortero se agrieta (advertencia visible)
2. Luego: los amarres de alambre se estiran (absorción de energía)
3. Luego: las tiras de bambú se deforman (alta ductilidad)
4. El marco de acero permanece intacto durante todo el proceso — la edificación no colapsa

Esto es fundamentalmente diferente de la mampostería sin refuerzo, que falla de forma frágil (colapso súbito sin advertencia).

## Resistencia al Fuego

- **Encapsulamiento en mortero:** Las tiras de bambú están completamente encapsuladas en mortero (~85 mm de espesor de muro). El mortero es incombustible y actúa como aislante térmico para el bambú.
- **Carbonización del bambú:** Incluso si el fuego penetra el mortero, el bambú se carboniza lenta y predeciblemente (similar a la construcción en madera). El marco de acero detrás mantiene la integridad estructural.
- **Acabado de pañete de cal:** Incombustible. Proporciona protección adicional contra incendios.
- **Sin bambú expuesto:** Una vez instalado y terminado, ningún bambú es visible o accesible a las llamas.

## Desempeño Térmico

- **Masa térmica:** ~85 mm de mortero proporcionan masa térmica significativa — absorbe calor durante el día, lo libera de noche. Reduce las oscilaciones de temperatura en climas tropicales.
- **Transpirabilidad:** El pañete de cal es permeable al vapor. La humedad pasa a través del muro en vez de quedar atrapada, previniendo condensación y moho.
- **Sin capa de aislamiento:** El sistema no incluye una capa de aislamiento térmico. En climas tropicales (el objetivo principal), la masa térmica es más valiosa que el aislamiento. Para climas templados, se puede agregar una capa de aislamiento exterior por fuera del pañete de cal.

## Desempeño Acústico

El núcleo denso de mortero proporciona buena atenuación sonora:

- **STC estimado (Sound Transmission Class):** 40–45 para un muro de un solo panel
- **Con pañete de cal en ambos lados:** STC 42–48
- **Comparación:** Muro estándar de bloque de concreto: STC 40–45. El sistema de paneles es comparable.

## Capacidad de Carga

> **Advertencia:** Los valores a continuación son estimaciones analíticas conservadoras basadas en propiedades de materiales y geometría. NO están basados en pruebas de laboratorio. No use estos valores para ingeniería estructural sin verificación independiente. El desempeño real depende de la calidad de los materiales, la mano de obra y los detalles de conexión. Ver [Pruebas Necesarias](#pruebas-necesarias) más adelante.

### Peso Propio del Panel

| Componente | Peso |
|---|---|
| Marco de acero ángulo L (L 40×40×4, 7 m a 2,42 kg/m + tiras de sujeción + cartelas) | ~22 kg |
| Mortero del núcleo (base: cemento-arena, ~0,147 m³, densidad curada ~2 000 kg/m³) | ~294 kg |
| Tiras de bambú + diagonales (~30 % densidad de cavidad) | ~38 kg |
| Bloques de HDPE, alambre, malla, conducto, cables | ~6 kg |
| Pañete de cal (10 mm en ambas caras) | ~100 kg |
| **Peso total del panel, mezcla base** | **~460 kg** |
| **Peso por m² de muro, base** | **~184 kg/m²** |
| Peso total del panel, mezcla bahareque optimizada (cal puzolánica + pasto estrella + 5 mm de pañete) | ~380 kg |
| Peso por m² de muro, optimizado | ~152 kg/m² |
| Peso de envío del montaje en seco (marco + bambú + malla + instalaciones, antes del vertido del mortero) | ~75 kg |

Para comparación: muro de bloque de concreto de 150 mm ≈ 180 kg/m². El sistema de paneles (mezcla base) tiene aproximadamente el mismo peso que la mampostería convencional por unidad de área, y la mezcla bahareque optimizada es ~15 % más ligera. Crítico para la logística: el **peso de envío del montaje en seco (~75 kg)** es la forma en la que el panel se transporta del taller a la obra (el mortero se vierte in situ).

### Carga Axial (Vertical)

Cada panel tiene dos postes laterales verticales de ángulo L que pueden soportar cargas de compresión significativas:

| Elemento | Sección transversal | Capacidad axial conservadora |
|---|---|---|
| Poste lateral de ángulo L (L 40×40×4 mm) | A ≈ 304 mm² | ~36 kN por poste (a σ = 120 MPa, ~50 % de la fluencia A36) |
| Dos postes laterales por panel | 2 × 304 mm² | ~72 kN por panel (~7 200 kg) |

**Qué significa esto en la práctica:**

Una casa típica de un piso con altillo y techo de teja de barro impone aproximadamente 200–400 kg de carga por metro lineal de muro (techo + cielo raso + entrepiso del altillo + carga viva). Un solo panel de 1 m puede soportar **18–36× este requerimiento**. **Los paneles no necesitan un marco de acero separado para soportar un segundo piso y techo.**

Cuando se usan **con un marco de acero**, esta capacidad axial es puro margen de reserva — el acero soporta las cargas gravitacionales. Cuando se usan **sin un marco de acero**, los paneles son la estructura portante. En ese caso, una viga de coronación de madera o bambú en la parte superior del muro distribuye la carga del techo uniformemente entre todos los paneles y los amarra.

El pandeo no es una preocupación a estos niveles de carga **cuando el ángulo L está embebido en el composite del panel**: el espesor del muro de mortero de 85 mm proporciona al marco de ángulo rigidez lateral continua, y la relación altura-espesor del panel (~2 500/85 ≈ 29) está bien dentro de los límites de esbeltez aceptados para muros reforzados.

**Importante: limitación del eje débil de perfiles abiertos.** Los perfiles estructurales abiertos — ángulos L, perfiles T, perfiles C — tienen rigidez mínima alrededor de su eje débil. Un poste L 40×40×4 independiente sin arriostramiento del panel (I_min ≈ 3,8 × 10⁴ mm⁴ alrededor del eje débil que pasa por el talón) pandearía bajo carga moderada. La capacidad de 36 kN por ángulo L indicada arriba es la **capacidad axial de fluencia** y SOLO es alcanzable cuando el ángulo está continuamente arriostrado por el relleno del panel (mortero + guadua). Esta distinción es crítica para la secuencia constructiva — el marco de ángulo L no debe cargarse axialmente antes de que los paneles sean vertidos, curados y carguen como composite. Para columnas independientes en edificios de varios pisos los perfiles abiertos no son apropiados — usar perfil hueco cuadrado (SHS) en su lugar.

### Carga Lateral (En Plano / Volcamiento)

Esta es la contribución estructural principal del panel — resistir fuerzas horizontales de viento y sismos.

**Sin arriostramiento diagonal (solo mortero + tiras verticales):**

Estimación conservadora basada en la resistencia al corte del mortero (τ ≈ 0,3 MPa para mortero 1:4 cemento:arena) a lo largo de la sección transversal del panel:

- Área de corte: ~85 mm × 1.000 mm = 85.000 mm²
- Capacidad conservadora de corte: 85.000 × 0,3 = ~25 kN por panel
- Con factor de seguridad 3: **~8 kN de carga de trabajo por panel**

**Con arriostramiento diagonal (la configuración diseñada):**

La tira diagonal de bambú (60 × 20 mm, Guadua angustifolia) en tracción:

- Sección transversal: 1.200 mm²
- Resistencia a tracción conservadora: 80 MPa (usando ~50% de los 150–200 MPa publicados)
- Capacidad de tracción de la diagonal: 1.200 × 80 = ~96 kN
- Componente horizontal (cos 69°): ~96 × 0,36 = ~34 kN por diagonal
- Dos diagonales (una por lado, una en tracción): ~34 kN
- Los amarres de alambre y la traba del mortero agregan resistencia adicional
- Con factor de seguridad 3: **~12–15 kN de carga de trabajo de volcamiento por panel**

**Para contexto:** Una sección de muro de 3 m de ancho (3 paneles) proporciona ~36–45 kN de resistencia al volcamiento. Una edificación residencial de un piso en una zona sísmica moderada (PGA 0,2g) con 30 kN de masa sísmica sobre el muro necesita aproximadamente 6 kN de resistencia al corte basal por metro lineal de muro. Tres paneles por metro proporcionan 4–5× este requerimiento.

Estos son números muy conservadores. La matriz de mortero, la cuadrícula de amarres de alambre y el perfil )( contribuyen resistencia adicional no contemplada arriba.

### Carga Fuera de Plano (Viento / Impacto)

El panel resiste presión perpendicular a la cara del muro (succión/presión de viento, impacto):

- El arco de mortero creado por el perfil )( actúa como una bóveda poco profunda entre los perfiles T superior e inferior rígidos
- Estimación conservadora para presión uniforme de viento, tratando el panel como una losa simplemente apoyada:

| Parámetro | Valor |
|---|---|
| Luz del panel (entre perfiles T superior/inferior) | 2,5 m |
| Ancho del panel | 1,0 m |
| Espesor del mortero (mínimo, en el centro) | ~55 mm |
| Resistencia a flexión del mortero (conservadora) | 1,0 MPa |
| Capacidad estimada a presión uniforme | ~0,7 kPa |
| Con factor de seguridad 2 | **~0,35 kPa carga de trabajo** |

**Para contexto:** 0,35 kPa ≈ velocidad de viento ~25 m/s (90 km/h). Para zonas de viento más alto, el marco de acero (no el panel) soporta la carga de viento a través de las conexiones viga-columna. El panel solo necesita resistir la presión local entre los elementos de su propio marco.

La cuadrícula de tiras de bambú y los amarres de alambre proporcionan resistencia fuera de plano adicional significativa no capturada en el modelo simple de losa — el panel es un compuesto, no una losa de mortero simple.

### Cargas Puntuales (Accesorios, Repisas, Gabinetes)

| Tipo de accesorio | Método de anclaje | Capacidad conservadora |
|---|---|---|
| Elementos livianos (cuadros, relojes, ganchos de toalla) | Clavo de mampostería o tornillo en mortero | 5–10 kg por anclaje |
| Elementos medianos (repisas, espejos, gabinetes pequeños) | Anclaje de expansión plástico en mortero (6–8 mm) | 15–25 kg por anclaje |
| Elementos pesados (gabinetes de cocina, calentador de agua, soporte de TV) | Perno pasante al alma del ángulo L de acero | 50–100 kg por anclaje |
| Elementos muy pesados (biblioteca, alacena llena) | Múltiples pernos pasantes al ángulo L + placa de distribución | 200+ kg por punto de montaje |

**Consejo:** El alma del ángulo L está en una posición conocida (a lo largo de un costado del panel, en la profundidad del muro). Un detector de vigas o imán la localiza fácilmente. El empernado pasante al alma proporciona anclaje confiable y de alta capacidad comparable a la estructura de perfiles de acero.

### Resumen — Capacidad Conservadora en kg por Panel

Para constructores y no ingenieros, aquí están los mismos números expresados en kilogramos. Estas son **cargas de trabajo muy conservadoras** (ya divididas por factores de seguridad de 2–3). Las cargas reales de falla son 2–3× mayores.

| Tipo de carga | Dirección | Capacidad conservadora de trabajo | Qué significa en la práctica |
|---|---|---|---|
| **Volcamiento (sismo/viento)** | Horizontal, en el plano del muro | **~1.200–1.500 kg por panel** | Una fuerza horizontal de 1,2–1,5 toneladas aplicada en la parte superior de un solo panel antes de que deba considerarse en su límite de trabajo. Una casa típica de un piso necesita ~600 kg de resistencia al volcamiento por metro de muro — un panel proporciona 2× eso. |
| **Fuera de plano (presión de viento)** | Perpendicular a la cara del muro | **~90 kg distribuidos sobre la cara del panel** | Equivalente a ~36 kg/m² de presión uniforme. Una persona recargándose con fuerza contra el muro (~80 kg en ~0,3 m²) está bien dentro de la capacidad. |
| **Axial (vertical)** | Hacia abajo, a través del panel | **Excede ampliamente las cargas residenciales (~7 200 kg de fluencia axial por panel en composite)** | Los dos ángulos L laterales soportan mucho más que un techo típico + piso superior por metro de muro. Los paneles pueden soportar un segundo piso y techo sin marco de acero separado. |
| **Carga puntual en mortero** | Extracción / corte en anclaje | **~15–25 kg por anclaje** | Una ménsula de repisa con 2 anclajes sostiene 30–50 kg de forma segura. |
| **Carga puntual en ángulo L** | Perno pasante | **~50–100 kg por perno** | Un gabinete de cocina con 4 pernos pasantes sostiene 200–400 kg de forma segura. |

> **Importante:** Estas son estimaciones, no valores probados. Serán validadas mediante pruebas físicas. No usar para ingeniería estructural sin verificación independiente. En caso de duda, fijar los elementos pesados al marco de acero de la edificación, no al panel.

## Durabilidad (Vida Útil de Diseño de 80–100 Años)

| Componente | Mecanismo de degradación | Prevención | Vida esperada |
|---|---|---|---|
| Marco de acero | Corrosión | Galvanizado en caliente (85 μm+) | 80–100 años (no costero) |
| Tiras de bambú | Ataque de insectos, descomposición fúngica | Tratamiento con borato + encapsulamiento en mortero (alcalino, anaeróbico) | 80+ años |
| Mortero | Carbonatación, meteorización | Protegido por pañete de cal (capa sacrificial) | 100+ años |
| Pañete de cal | Erosión superficial, microfisuración | Autoreparable (la carbonatación rellena las grietas), lechada de cal renovable | Indefinido con mantenimiento |
| Lechada de cal | Degradación UV, erosión por lluvia | Reaplicar cada 5–10 años | 5–10 años por capa |
| Instalación eléctrica | Degradación del aislamiento | El conducto de PVC permite reemplazo de cables sin abrir el muro | Cables: 30–50 años, reemplazables |
| Bloques de HDPE | Ninguno significativo | Protegido de UV (dentro del muro) | 100+ años |

### Programa de Mantenimiento

| Intervalo | Acción | Costo estimado |
|---|---|---|
| Cada 5–10 años | Renovación de lechada de cal | $50–100 por edificación |
| Cada 15–20 años | Inspeccionar pañete de cal, reparar grietas | $100–300 por edificación |
| Cada 30–40 años | Inspeccionar instalación eléctrica, reemplazar cables si es necesario | $200–500 por edificación |
| A los 40 años | Inspeccionar marco de acero en puntos accesibles (re-galvanizar puntualmente si es necesario) | $200–400 |
| **Total en vida útil** | | **$1.400–2.000** |

## Pruebas Necesarias

**Todos los valores de capacidad de carga anteriores son estimaciones analíticas.** Serán validados mediante pruebas físicas como parte del desarrollo de este proyecto. Los primeros paneles serán construidos y probados antes de que se ocupe cualquier edificación.

Programa de pruebas planificado:

- [ ] **Pruebas de corte por volcamiento** (ASTM E564 o equivalente) — paneles con y sin diagonales, para validar la mejora estimada de 3–5×
- [ ] **Pruebas de carga fuera de plano** — presión uniforme e impacto puntual, para validar el beneficio del perfil )(
- [ ] **Pruebas de resistencia al fuego** (ASTM E119 o equivalente) — tiempo hasta falla estructural
- [ ] **Pruebas sísmicas cíclicas** — mesa de vibración a escala real o carga cíclica cuasiestática, para verificar el modo de falla dúctil
- [ ] **Pruebas de conexiones** — capacidad de la pestaña de perno panel-columna, durabilidad del conector rápido
- [ ] **Pruebas de envejecimiento a largo plazo** — envejecimiento acelerado de muestras de bambú encapsulado en mortero
- [ ] **Pruebas de transmisión acústica** (ASTM E90) — medición de STC
- [ ] **Pruebas de extracción de carga puntual** — capacidad de anclaje de mampostería y perno pasante en mortero + ángulo L

Los resultados de las pruebas se publicarán en este repositorio a medida que estén disponibles. Si tiene acceso a instalaciones de prueba y quiere contribuir, contáctenos — las pruebas colaborativas con diferentes especies de bambú y mezclas de mortero harán este sistema más robusto para todos.
