jreuteler/bahareque-modular/es/09-estimacion-costos.md

# Estimación de Costos

> **Aviso:** Estas son estimaciones de costos de materiales únicamente, basadas en precios de 2025 en Colombia (región del Eje Cafetero). La mano de obra no está incluida — el sistema está diseñado para producción comunitaria donde la mano de obra se aporta, no se compra. Los precios varían significativamente por región, moneda y cadena de suministro. Use estos como punto de partida, no como presupuesto.

A lo largo de este proyecto se documentan dos especificaciones de mezcla de mortero: la **mezcla base** (mortero de cemento-arena + 30 % de contenido de guadua + pañete de cal de 10 mm en ambas caras) y la **mezcla bahareque optimizada** (cal puzolánica + fibras de pasto estrella + 30 % de guadua + pañete de cal de 5 mm). Ambas estimaciones se muestran a continuación.

## Costo Por Panel — Mezcla Base (solo materiales)

| Material | Especificación | Cant. por panel | Costo unitario (USD) | Total (USD) |
|---|---|---|---|---|
| Ángulo L de acero | L 40×40×4 mm, ASTM A36 | 7,0 m | $4,00/m | $28,00 |
| Galvanizado | En caliente, proceso por lotes | 1 marco | $2,00 | $2,00 |
| Tiras de sujeción | Platina 40×3 mm, galv. | 4,0 m | $1,00/m | $4,00 |
| Cartelas + tornillería de esquina | Platina + M12/M8 | 1 juego | $3,00 | $3,00 |
| Tornillos inox. | Autorroscantes, A2 | 40 pzas | $0,08 | $3,20 |
| Bloques de HDPE | Reciclado, 30×30 mm | 2,0 m | $1,50/m | $3,00 |
| Tiras de bambú (verticales + horizontales, 30 % densidad de cavidad) | Guadua tratada con borato | ~400 m en total | $0,05/m | $20,00 |
| Tiras de bambú (diagonal) | 60×20 mm, tratada | ~5,4 m | $0,30/m | $1,60 |
| Amarres de alambre | Galvanizado | 5 m | $0,10/m | $0,50 |
| Conducto de PVC | Eléctrico 16 mm | 5 m | $0,30/m | $1,50 |
| Cable 12V + portalámparas | 2 conductores + 6× E10 | 1 juego | $3,00 | $3,00 |
| Cable 120V + conectores | 3 conductores + conectores rápidos | 1 juego | $4,00 | $4,00 |
| Malla de gallinero | Hexagonal galv., 25 mm | 5,5 m² | $0,80/m² | $4,40 |
| Cemento | Portland Tipo I | ~54 kg | $0,15/kg | $8,10 |
| Arena (mortero) | Arena de río limpia | ~240 kg | $0,02/kg | $4,80 |
| Fibra de PP | Picada 6–12 mm | 200 g | $5,00/kg | $1,00 |
| Adición puzolánica | Ceniza volcánica o CCA | 2 kg | $0,50/kg | $1,00 |
| **Subtotal panel — base** | | | | **~$93** |

### Acabado en obra, base (por área de panel)

| Material | Cant. por panel | Costo (USD) |
|---|---|---|
| Pañete de cal (10 mm en cada cara) | ~25 kg de cal + ~65 kg de arena | $6,50 |
| Lechada de cal (ambas caras) | ~2 kg de cal | $0,50 |
| **Subtotal acabado — base** | | **$7,00** |

### **Costo total de materiales por panel — base: ~$100 USD**

### Costo por m² de muro terminado — base

- Área del panel: 1,0 m × 2,5 m = 2,5 m²
- Costo de materiales por m²: **~$40 USD/m²**

## Costo Por Panel — Mezcla Bahareque Optimizada (solo materiales)

La mezcla optimizada reemplaza el mortero de cemento Portland-arena con cal hidráulica + puzolana, reemplaza la fibra de PP con pasto estrella (gratis, recolectado en sitio) y usa pañete de cal más delgado de 5 mm. Mismo marco de ángulo L, mismo contenido de bambú, mismos componentes eléctricos y estructurales.

| Material | Especificación | Cant. por panel | Costo unitario (USD) | Total (USD) |
|---|---|---|---|---|
| Ángulo L de acero + galvanizado + tiras de sujeción + cartelas | (igual que base) | | | $37,20 |
| Tornillos inox., HDPE, bambú, alambres, conducto, cables, malla | (igual que base) | | | $41,20 |
| Cal hidráulica (aglutinante principal) | NHL 3.5 o NHL 5 | ~42 kg | $0,30/kg | $12,60 |
| Cenizas volantes o cascarilla de arroz (puzolana, 30 % equivalente a cemento) | FA o CCA | ~15 kg | $0,10/kg | $1,50 |
| Arena (mortero) | Arena de río limpia | ~200 kg | $0,02/kg | $4,00 |
| Fibra de pasto estrella (seca) | Recolectada en sitio | ~3 kg | gratis | $0,00 |
| **Subtotal panel — optimizado** | | | | **~$96** |

### Acabado en obra, optimizado (por área de panel)

| Material | Cant. por panel | Costo (USD) |
|---|---|---|
| Pañete de cal (5 mm en cada cara) | ~12 kg de cal + ~33 kg de arena | $3,30 |
| Lechada de cal (ambas caras) | ~2 kg de cal | $0,50 |
| **Subtotal acabado — optimizado** | | **$3,80** |

### **Costo total de materiales por panel — optimizado: ~$100 USD**

### Costo por m² de muro terminado — optimizado

- Costo de materiales por m²: **~$40 USD/m²**

> **Ambas mezclas tienen aproximadamente el mismo costo de materiales** (~$100/panel, ~$40/m²). La mezcla optimizada cambia un costo de ingredientes ligeramente más alto en cal/puzolana (vs. cemento Portland más barato) por menor costo de pañete de cal (más delgado), cero costo de fibra de PP y CO₂ embebido sustancialmente menor (ver [Impacto Ambiental](10-impacto-ambiental.md)). La mezcla optimizada es por lo tanto **una clara ganancia en carbono y autenticidad patrimonial a costo prácticamente igual**.

## Comparación con Construcción Convencional

| Sistema de muro | Costo de materiales por m² (USD) | Vida útil | Notas |
|---|---|---|---|
| **Este sistema de paneles — base** | **~$40** | **80–100 años** | Incluye estructura, eléctrica, acabado |
| **Este sistema de paneles — optimizado** | **~$40** | **80–100 años** | Mismo precio, menos carbono |
| Bloque de concreto (15 cm) | $25–35 | 40–60 años | Requiere varilla, concreto de relleno, pañete, pintura, eléctrica aparte |
| Ladrillo cocido | $30–45 | 60–80 años | Requiere mortero, pañete, pintura, eléctrica aparte |
| Drywall sobre perfiles de acero | $20–30 | 20–30 años | Sin masa térmica, no portante, requiere pintura, eléctrica aparte |
| Bahareque convencional (in situ) | $15–25 | 15–30 años | Sin eléctrica, calidad de acabado variable, vida útil corta sin ingeniería |
| Adobe | $10–20 | 20–40 años | Mal desempeño sísmico, sin eléctrica, requiere muros gruesos |

**Idea clave:** El sistema de paneles cuesta aproximadamente **20–35 % más por m² que el bloque de concreto** — pero incluye instalación eléctrica integrada, tiene 1,5–2× la vida útil, proporciona mejor desempeño térmico y acústico, y produce un acabado superior. Cuando se suma el costo de cablear una casa de bloque de concreto por separado (~$8–15/m² para conductos, cables, tomacorrientes y su instalación), el sistema de paneles es competitivo en costo en una base de muro-completo-listo-para-habitar.

## Costo Por Casa (estimación aproximada)

Una casa sencilla de un piso con altillo (50 m² de huella, ~70 m² habitables incluyendo altillo):

| Componente | Cantidad | Costo (USD) |
|---|---|---|
| Paneles de muro | ~40 paneles (100 m² de muro) | $2.600–2.800 |
| Cimentación (concreto, varilla) | ~5 m³ de concreto | $800–1.200 |
| Viga de coronación (madera/bambú) | ~30 m | $200–400 |
| Techo (teja de barro + correas) | ~65 m² | $1.200–1.800 |
| Piso (losa de concreto o de tierra) | ~50 m² | $400–800 |
| Ventanas + puertas | ~8 aberturas | $600–1.200 |
| Tablero eléctrico + transformador | 1 juego | $200–400 |
| Plomería (básica) | Cocina + baño | $300–600 |
| **Total materiales** | | **$6.300–9.200** |

Esto es solo materiales. En un modelo de construcción comunitaria, la mano de obra se aporta. En un modelo de contratista, agregue 40–60% por mano de obra.

**Para contexto:** Una casa comparable de bloque de concreto en la Colombia rural cuesta $12.000–20.000 (materiales + mano de obra) y dura 40–60 años. Este sistema logra calidad similar o mejor a aproximadamente la mitad del costo con el doble de vida útil.

## Estrategias de Reducción de Costos

| Estrategia | Ahorro | Notas |
|---|---|---|
| Cosechar bambú propio | 30–40% del costo de bambú | Requiere 1+ hectáreas de guadual, 4–5 años de maduración |
| Reciclar HDPE de residuos | 100% del costo de HDPE | Tablas de cortar, retazos de tubería, residuos industriales |
| Usar ceniza volcánica (gratis) | 100% del costo de puzolana | Disponible en regiones andinas, recolectar y tamizar |
| Usar fibra de pasto estrella en vez de PP | 100% del costo de fibra | Pasto invasivo, gratis, uso circular |
| Galvanizado por lotes (50+ marcos) | 15–20% del costo de galv. | Descuento por volumen en planta de galvanizado |
| Cantera comunitaria de arena | 50–80% del costo de arena | Si hay acceso local a arena de río |
| Producir cal propia de piedra caliza | 50–70% del costo de cal | Requiere horno (construcción única), piedra caliza local |

## Variaciones Regionales de Precio

Los costos de materiales varían dramáticamente por región. Las estimaciones anteriores son para Colombia. Multiplicadores aproximados:

| Región | Multiplicador | Notas |
|---|---|---|
| Colombia (Eje Cafetero) | 1,0× (línea base) | Guadua abundante, ceniza volcánica disponible |
| Ecuador, Perú | 0,8–1,1× | Materiales similares, caña guadua disponible |
| Centroamérica | 1,0–1,3× | Bambú disponible, acero puede costar más |
| Filipinas, Indonesia | 0,7–1,0× | Bambú abundante y barato, mano de obra muy baja |
| India | 0,6–0,9× | Bambú y mano de obra muy bajos, acero asequible |
| África Subsahariana | 0,8–1,2× | Especies de bambú varían, cemento puede ser costoso |
| Sur de Europa | 2,0–3,0× | Materiales disponibles pero más costosos |

Estos multiplicadores son guías aproximadas. La mayor variable es el costo del bambú — si cultiva el propio, es casi gratis.
