jreuteler/bahareque-modular/es/10-impacto-ambiental.md

# Impacto Ambiental

## Huella de Carbono Por Panel — Mezcla Base

Las cifras a continuación reflejan la especificación base actual: marco de acero L 40×40×4 + 30 % de contenido de guadua en la cavidad + mortero de cemento-arena (base) + pañete de cal de 10 mm en ambas caras. Ver [Anatomía del Panel](02-anatomia-del-panel.md) y [Materiales](03-materiales.md) para detalles.

| Material | Cant. por panel | CO₂ incorporado (kg) | Fuente de emisión |
|---|---|---|---|
| Cemento Portland (~18 % de la masa del mortero) | ~54 kg | 43,2 | Calcinación + combustible del horno (~0,8 kg CO₂/kg cemento) |
| Marco de acero ángulo L + tiras de sujeción | ~22 kg de acero | 39,6 | Producción de acero (~1,8 kg CO₂/kg acero) |
| Galvanizado (zinc) | ~0,7 kg de zinc | 2,8 | Fundición de zinc (~4 kg CO₂/kg zinc) |
| Arena (~82 % de la masa del mortero) | ~240 kg | 1,2 | Extracción + transporte |
| Malla de gallinero + malla de aluminio | ~2 kg | 3,6 | Producción de alambre de acero |
| Conducto de PVC | ~0,3 kg | 0,6 | Manufactura de PVC (~2 kg CO₂/kg) |
| Cables + conectores | ~0,5 kg | 1,5 | Cobre + plástico |
| Bloques de HDPE | ~0,5 kg | 0,5 | Si es reciclado: ~1 kg CO₂/kg (vs 3 para virgen) |
| Cal (en pañete, calcinación) | ~22 kg de cal | 18,0 | Calcinación de piedra caliza (~0,8 kg CO₂/kg cal) |
| Fibra de PP (aditivo del mortero) | ~0,2 kg | 0,4 | Producción de polipropileno |
| **Subtotal emisiones** | | **~111 kg CO₂** | |
| Bambú (carbono capturado durante crecimiento) | ~38 kg peso seco (30 % contenido cavidad) | **−60 a −75 kg CO₂** | El bambú captura ~1,6–2,0 kg CO₂ por kg de masa seca |
| Pañete de cal (reabsorbe CO₂ durante carbonatación) | ~22 kg de cal | **−6 a −9 kg CO₂** | La carbonatación de la cal recaptura ~30–50 % del CO₂ de calcinación a lo largo de décadas |
| **CO₂ neto por panel, mezcla base** | | **~30–45 kg CO₂** | |
| **CO₂ neto por m² de muro, base** | | **~12–18 kg CO₂/m²** | |

## Huella de Carbono Por Panel — Mezcla Bahareque Optimizada

La mezcla optimizada (cal puzolánica + pasto estrella + 30 % de guadua + pañete de 5 mm) entrega menor carbono incorporado a través de múltiples palancas:

| Palanca | CO₂ delta por panel vs base |
|---|---|
| Reemplazar 30 % del cemento con cenizas volantes o CCA | −10 a −13 kg |
| Reemplazar mortero de cemento Portland con base de cal hidráulica + puzolana | −8 a −12 kg |
| Reemplazar fibra de PP con pasto estrella | −0,5 kg |
| Pañete de cal más delgado de 5 mm en ambas caras (−50 % volumen de cal) | −9 kg de calcinación, +4 kg de menor recuperación por carbonatación = **−5 kg neto** |
| **Reducción total** | **−24 a −30 kg CO₂ por panel** |
| **CO₂ neto por panel, mezcla optimizada** | **~6 a 20 kg CO₂** |
| **CO₂ neto por m² de muro, optimizada** | **~3 a 8 kg CO₂/m²** |

Con puzolanas disponibles localmente (ceniza volcánica en la región cafetera colombiana, cascarilla de arroz de Tolima/Valle del Cauca) y fibra de pasto estrella de la propia finca, la mezcla bahareque optimizada se acerca a **carbono-neutra** por panel. Si el guadual se maneja como sumidero de carbono gestionado (rotación de rebrotes con permanencia de biomasa), el sistema se vuelve **carbono-negativo**: el muro absorbe más CO₂ durante su vida que el que se emitió para construirlo.

## Comparación con Sistemas de Muro Convencionales

| Sistema de muro | kg CO₂ por m² | Proporción vs panel base |
|---|---|---|
| **Este sistema de paneles — mezcla base** | **12–18** | **1× (línea base)** |
| **Este sistema de paneles — mezcla bahareque optimizada** | **3–8** | **~0,4× base** |
| Bloque de concreto (15 cm, pañetado) | 40–60 | 3–4× base |
| Ladrillo de arcilla cocida (pañetado) | 50–80 | 3–5× base |
| Muro de concreto reforzado (15 cm) | 70–100 | 5–7× base |
| Drywall sobre perfiles de acero | 15–25 | 1–1,5× base |
| Bahareque convencional (revoque de barro, sin marco de acero) | 3–8 | 0,3–0,5× base |
| Adobe | 5–10 | 0,4–0,7× base |

La mezcla base del sistema de paneles produce **~3× menos CO₂ que el bloque de concreto o el ladrillo** — los dos materiales de muro más comunes en los países en desarrollo. La mezcla bahareque optimizada se acerca a los niveles de la construcción tradicional en tierra, proporcionando desempeño estructural y vida útil vastamente superiores.

## Carbono Por Año de Servicio

Cuando se incluye la vida útil, la comparación se vuelve aún más favorable (a 80–100 años de vida útil de diseño para este sistema):

| Sistema de muro | kg CO₂/m² | Vida útil (años) | kg CO₂/m²/año |
|---|---|---|---|
| **Este sistema de paneles — base** | 15 | 90 | **0,17** |
| **Este sistema de paneles — optimizado** | 5 | 90 | **0,06** |
| Bloque de concreto | 50 | 50 | 1,00 |
| Ladrillo cocido | 65 | 70 | 0,93 |
| Drywall sobre perfiles de acero | 20 | 25 | 0,80 |
| Bahareque convencional | 5 | 20 | 0,25 |

**A lo largo de su vida útil, este sistema de paneles produce ~5–15× menos carbono por año de servicio que el bloque de concreto.**

## Camino hacia la Neutralidad o Negatividad en Carbono

El sistema de paneles ya es bajo en carbono en la base. Con la mezcla bahareque optimizada y las siguientes sustituciones adicionales, se vuelve **carbono-negativo**:

| Sustitución | CO₂ ahorrado por panel | Viabilidad |
|---|---|---|
| Usar mortero de cal puzolánica (mezcla optimizada) | −20 a −25 kg | Especificación central — ver arriba |
| Usar acero reciclado (horno de arco eléctrico) | −8 a −12 kg | Depende de la cadena de suministro local de acero |
| Aumentar contenido de bambú aún más (45 % de cavidad) | −5 a −8 kg de captura adicional | Material gratis/económico |
| Usar cal artesanal (horno de leña con manejo de rebrotes) | −5 kg | Método tradicional de producción de cal |
| Pañete más delgado (5 mm → 3 mm) | −5 kg | Práctica tradicional bahareque |
| **Reducción potencial total más allá del optimizado** | **−43 a −55 kg** | |

A reducción máxima, el CO₂ neto por panel cae al rango de **−5 a +5 kg** — carbono-neutro a ligeramente negativo. Si el guadual se maneja como sumidero permanente de carbono, el sistema es confiablemente **carbono-negativo a lo largo de su vida útil**.

## Uso de Agua

- **Mezcla de mortero:** ~15–20 litros por panel (agua de curado reutilizada donde sea posible)
- **Curado:** ~50 litros durante 7 días (método de nebulización/arpillera)
- **Mezcla de pañete de cal:** ~10 litros por panel
- **Total:** ~75–80 litros por panel, o ~30 litros por m² de muro

Para comparación: la producción de bloque de concreto usa ~40–50 litros por m² de muro. La producción de ladrillo cocido usa ~100+ litros por m² (incluyendo enfriamiento del horno).

## Residuos

- **Retazos de acero:** Reciclados (valor como chatarra)
- **Retazos de bambú:** Compostados o usados como tutores de jardín/mulch
- **Residuos de mortero:** Mínimos — el vertido en mesa vibradora es preciso. Cualquier exceso se reutiliza en el siguiente panel.
- **Cama de arena:** Se reutiliza indefinidamente (la arena no se consume, solo se comprime y afloja)
- **Retazos de HDPE:** Reciclados o reutilizados para bloques más pequeños
- **Residuos de empaque:** Mínimos — la mayoría de los materiales llegan a granel

El sistema produce **casi cero residuos de construcción**. Esta es una consecuencia directa de la prefabricación en taller — cada corte se planifica, cada material se mide.

## Fin de Vida (después de 80–100 años)

Cuando un panel eventualmente llega al fin de su vida útil:

| Material | Disposición | Impacto ambiental |
|---|---|---|
| Marco de acero | Reciclar (100% reciclable) | Positivo — la chatarra de acero tiene valor |
| Mortero + bambú | Triturar y usar como agregado o relleno | Inerte — el mortero es calcio/sílice/arena, el bambú es orgánico |
| Pañete de cal | Retorna a carbonato de calcio (piedra caliza) | Carbono-neutro — el CO₂ absorbido durante la carbonatación se re-libera, neto cero |
| Bloques de HDPE | Reciclar | Reciclable |
| Cables de cobre | Reciclar (alto valor como chatarra) | Positivo |
| Conducto de PVC | Reciclar donde existan instalaciones | Reciclable en principio |

**Sin residuos peligrosos.** Sin asbesto, sin pintura con plomo, sin espuma de aislamiento sintético, sin químicos de madera tratada a presión. El panel está hecho de acero, bambú, arena, cemento y cal — retorna a la tierra o al flujo de reciclaje de forma limpia.
