jreuteler/bahareque-modular/es/11-transporte-manejo.md

# Transporte y Manejo

## Especificaciones del Panel para Manejo

| Propiedad | Valor |
|---|---|
| Dimensiones | 1,0 m × 2,5 m × 85 mm |
| Peso del montaje en seco (tal como se envía a obra) | **~75 kg** |
| Peso del panel terminado (mezcla base, después de vertido in situ + curado + pañete) | ~440 kg |
| Peso del panel terminado (mezcla bahareque optimizada) | ~360 kg |
| Centro de gravedad | Centro (construcción simétrica) |
| Áreas frágiles | Esquinas, bordes (el mortero puede astillarse con impacto una vez vertido) |
| Curado mínimo antes de manipular | 7 días después del vertido in situ |
| Curado mínimo antes de instalación | 14 días recomendado — nota: en el modelo de vertido in situ el panel se erige y el mortero se vierte en el lugar, así que "instalación" y "vertido" ocurren juntos en obra, no secuencialmente |

## Modelo de Producción Primario: Vertido In Situ

**El modelo de producción primario es enviar el montaje en seco (~75 kg) a la obra y verter el mortero in situ contra encofrado.** El panel terminado de ~440 kg nunca se mueve como unidad — se convierte directamente en parte del muro de la edificación, ahorrando costos de equipos de izaje pesado y eliminando el riesgo de fisuración por transporte. Ver [Proceso Constructivo](04-proceso-constructivo.md) para el protocolo de vertido vertical in situ.

El manejo de paneles curados (secciones siguientes) aplica al modelo de producción alternativo: vertido del mortero en taller sobre mesa vibradora, con paneles totalmente curados enviados a obra como elementos terminados. Este enfoque se conserva como opción documentada para constructores que prefieren producción en taller, pero añade un sobrecoste significativo de izaje, transporte y tasa de rechazo.

## Transporte Manual — Montaje en Seco (~75 kg)

El montaje en seco (marco de acero ángulo L + esterilla de bambú + malla + instalaciones, antes del mortero) lo levantan y posicionan **2 personas con una simple correa de cinta**. Sin plantilla de carga, sin grúa, sin montacarga — esta es una de las ventajas operativas centrales del modelo de producción de vertido in situ.

### Carga sencilla con correa (montaje en seco)

1. Enrollar una sola correa de 50 mm × capacidad 500+ kg alrededor del panel seco a media altura (~125 cm desde la base)
2. Cada cargador agarra un extremo de la correa con ambas manos, parados en lados largos opuestos del panel
3. Levantar juntos; el panel cuelga verticalmente entre ellos
4. Caminar a paso normal; el panel puede llevarse 30–50 m antes de necesitar un descanso

**Peso por persona: ~38 kg** — completamente manejable para los acarreos cortos típicos de taller-a-camión, camión-a-acopio-en-obra y acopio-a-instalación.

## Transporte Manual — Panel Terminado Curado (modelo alternativo de vertido en taller)

Un panel terminado de ~360–440 kg **no puede llevarse a mano**. Requiere izaje mecánico (polipasto de cadena, minicargador o pequeña grúa móvil). Esta es la razón central por la que se prefiere el modelo de vertido in situ.

Si los paneles vertidos en taller deben moverse (p. ej. producción en fase piloto antes de validar el protocolo in situ), use:

### Plantilla de Carga Sencilla (panel curado, ~360–440 kg)

Dos varas de bambú (3 m de largo, 8–10 cm de diámetro) pasadas a través de lazos de cinta de carga pesada enrollados alrededor del panel a 1/4 y 3/4 de la altura:

1. Colocar el panel plano
2. Enrollar dos cintas de carga (50 mm de ancho, capacidad 1 000+ kg) alrededor del panel a ~60 cm y ~190 cm desde la base
3. Pasar una vara de bambú por los lazos de las cintas a cada lado
4. **4 personas por vara, 8 cargadores en total** para un panel de mezcla base a ~440 kg, o 6 cargadores para un panel de mezcla optimizada a ~360 kg
5. El panel queda colgando verticalmente entre las varas

**Peso por persona: ~55 kg (base) / ~45 kg (optimizada)** — al borde superior del manejo manual seguro. Distancias largas o escaleras deben usar izaje mecánico en su lugar.

Para cualquier flujo de producción rutinario, **use montacarga, minicargador o polipasto de cadena en lugar del transporte manual** para paneles curados. El transporte manual de paneles curados es solo una opción para emergencias/piloto.

### Levantamiento e Inclinación

- **Nunca levante un panel por un solo borde** — el mortero puede agrietarse bajo su propio peso si queda en voladizo
- **Siempre levante desde dos puntos** simétricamente, o desde la base mientras se soporta por la espalda
- **Inclinación de plano a vertical:** Dos personas sostienen el borde superior, dos personas levantan la base. Rotar lentamente. Soportar la base sobre un bloque acolchado durante la rotación.

## Almacenamiento en Taller

Después del curado, los paneles se almacenan **verticalmente (de canto)** en un bastidor en A:

- Inclinar paneles contra ambos lados de un marco inclinado (como un libro abierto)
- 10–15 paneles por lado del bastidor
- Separar paneles con pequeños espaciadores de madera para permitir circulación de aire
- Cubrir con lona o techo para proteger de la lluvia directa (el mortero en curado puede lavarse si recibe lluvia fuerte antes del curado completo)
- Mantener fuera del suelo — colocar el borde inferior sobre gravilla o riel de madera

**Espacio requerido:** ~3 m × 1 m de área de piso por cada 20–30 paneles almacenados.

## Transporte en Camión

### Carga

1. Parar los paneles verticalmente en la cama del camión, recostados contra un costado
2. Colocar separadores de madera (retazos, bambú o espuma) entre cada panel
3. Asegurar paneles al costado del camión usando correas con trinquete a 1/3 y 2/3 de la altura
4. Nunca apilar paneles planos uno encima de otro — el panel inferior se agrietará bajo el peso de la pila
5. Máximo ~15–20 paneles por camioneta estándar (dependiendo de la capacidad del vehículo y las condiciones del camino)

### Consideraciones del Camino

- **Carreteras pavimentadas:** Sin precauciones especiales aparte de las correas
- **Carreteras destapadas:** Reducir velocidad. Agregar acolchamiento de espuma o cartón entre paneles. Asegurar bien — los paneles pueden desplazarse y astillar bordes con los baches.
- **Pendientes fuertes:** Asegurar que los paneles se inclinen hacia la montaña (no hacia el vacío) para evitar volcamiento
- **Distancia:** Sin límite. Los paneles están completamente curados y son autosuficientes. Pueden viajar cualquier distancia.

### Descarga

1. Quitar correas de arriba hacia abajo
2. Dos personas por panel — una en el borde superior, otra soportando la base
3. Llevar cada panel al bastidor de almacenamiento en A del sitio
4. Nunca dejar caer ni deslizar paneles — los bordes de mortero se astillan fácilmente

## Grúa / Polipasto (para pisos superiores)

Para edificaciones de dos pisos, los paneles deben levantarse al segundo piso:

- **Poste de carga simple:** Una vara de bambú o acero con cuerda y polea. Dos personas jalan la cuerda, una guía el panel. Funciona para volúmenes bajos.
- **Polipasto de cadena en viga:** Fijar un polipasto de cadena de **1 000 kg** a la viga de acero de la edificación (los polipastos de 500 kg son insuficientes para izajes de paneles curados). Enganchar a la cinta de carga del panel. Una persona opera, una guía. Rápido y controlado. Para izajes del montaje en seco (~75 kg) basta un polipasto de 500 kg.
- **Montacarga (si está disponible):** Horquilla debajo del panel (protegido con cartón). Levantar y colocar directamente en posición.

**No lance, ruede ni arrastre los paneles.** El mortero es fuerte en compresión pero puede agrietarse con impacto puntual.

## Daños y Reparación

| Tipo de daño | Causa | Reparación |
|---|---|---|
| Astillamiento de esquina (pequeño) | Impacto durante transporte | Rellenar con mortero, pañetar encima. Solo cosmético. |
| Grieta de borde (superficial) | Golpe durante manejo | Rellenar con pañete de cal. No afecta la estructura. |
| Grieta pasante (mortero) | Caída o impacto severo | El panel puede estar comprometido. Evaluar: si el marco de acero está intacto y la grieta es <2 mm, rellenar con mortero y monitorear. Si la grieta es >5 mm o el marco está torcido, rechazar el panel. |
| Conector rápido roto | Enganche durante transporte | Reemplazar conector (soldado o crimpado). |

**Tasa de rechazo:** Con cuidado razonable, espere <5% de paneles con algún daño durante transporte y manejo, y <1% que requiera rechazo. Los paneles rechazados pueden despojarse de componentes eléctricos y reciclarse como material de relleno.

## Lista de Verificación Antes del Transporte

- [ ] Panel curado mínimo 7 días (14 recomendado)
- [ ] Panel marcado con tipo (P/O/S/W) y fecha de producción
- [ ] Circuitos eléctricos probados (verificación de continuidad 12V + 120V)
- [ ] Sin grietas visibles >1 mm
- [ ] Esquinas intactas
- [ ] Cintas de carga o plantilla preparadas
- [ ] Cama del camión limpia, separadores listos, correas disponibles
- [ ] Ruta verificada en cuanto a condiciones del camino (puentes, gálibo, pendiente)
