jreuteler/bahareque-modular/es/14-mejora-acustica.md

# Mejora acústica — Muros expuestos al ruido

> *Este capítulo fue inspirado por una sugerencia de Kim Hansson — gracias por impulsar el diseño para abordar condiciones urbanas reales.*

El panel estándar (STC 40–45) es adecuado para zonas residenciales tranquilas. Para edificaciones en calles concurridas, cerca de autopistas o junto a zonas comerciales o industriales, los muros expuestos al ruido pueden mejorarse individualmente. No es necesario mejorar todos los muros — la mayoría de las edificaciones solo tienen uno o dos lados expuestos a ruido significativo. Los muros que dan al lado tranquilo se mantienen con paneles estándar.

## Guía de exposición al ruido

| Situación | Tratamiento recomendado | STC objetivo |
|---|---|---|
| Calle residencial tranquila | Panel estándar — no requiere mejora | 40–45 |
| Tráfico vehicular moderado | Mortero denso + capa de amortiguación en arcilla | 48–52 |
| Vía urbana concurrida, rutas de bus | Panel doble con cavidad de fibra | 55–62 |
| Autopista, zona industrial, zona de rumba | Panel doble con cavidad de fibra + capa de arcilla | 58–65 |

**Aplique la mejora solo donde sea necesario.** Una casa típica sobre una calle concurrida tiene uno o dos muros expuestos al ruido (10–15 m²). Los muros restantes dan al jardín, patio o lado tranquilo y usan paneles estándar. Esto mantiene el sobrecosto proporcional al problema real de ruido.

## Opción 1: Mezcla de mortero más densa (la más económica, +3–5 STC)

Se reemplaza la arena de río estándar por agregados más pesados en la mezcla de mortero. Mismo proceso de producción, mismo marco, mismo vaciado en mesa vibratoria. El panel simplemente queda más pesado.

| Agregado | Aumento de densidad | Costo vs. arena estándar | Disponibilidad |
|---|---|---|---|
| Triturado de basalto o finos de granito | +15–20% | Similar | Universal — cualquier cantera |
| Escoria de hierro | +25–30% | A menudo gratis | Cerca de siderúrgicas, fundiciones |
| Arena magnetítica (arena negra) | +40% | Bajo | Lechos de ríos volcánicos (Andes, Centroamérica) |

- **Peso del panel:** terminado ~490–530 kg mezcla base (vs. ~440 kg base estándar) / ~405–440 kg mezcla optimizada (vs. ~360 kg optimizada estándar). Peso de ensamble en seco sin cambios a ~75 kg (el agregado denso se añade en el vertido in-situ, no en el ensamble en taller)
- **Sobrecosto:** ~$1–2 por panel
- **STC:** ~43–48
- **Cambio en producción:** Ninguno — solo se sustituye el agregado. La proporción de mezcla se mantiene en 1:4 cemento:agregado.

**Ideal para:** Muros laterales que necesitan una mejora modesta sin cambiar el espesor del muro ni el proceso constructivo.

## Opción 2: Capa de amortiguación en arcilla (+5–8 STC)

Se agrega una capa de 10–15 mm de **pañete de tierra con paja** en la cara interior del muro expuesto al ruido, aplicada en obra entre la superficie de mortero y el acabado de pañete de cal.

### Por qué funciona la arcilla

La arcilla tiene una amortiguación acústica superior al mortero de cemento. Cuando las ondas sonoras golpean una capa de arcilla, más energía se convierte en calor (fricción interna en las partículas de arcilla) en lugar de transmitirse a través del muro. Las fibras de paja picada dentro de la arcilla generan fricción interna adicional.

Esta es la técnica de bahareque más tradicional — el pañete de tierra se ha usado sobre muros de guadua durante siglos. Funciona acústicamente por la misma razón que funciona térmicamente: la arcilla es un absorbente natural de energía.

### Aplicación

1. Preparar la mezcla de arcilla y paja: arcilla local + pasto seco o paja picada (trozos de 5–10 cm), mezclados hasta obtener una pasta espesa
2. Aplicar 10–15 mm en la cara interior del muro expuesto al ruido, sobre la superficie de mortero
3. Dejar secar (3–7 días dependiendo de la humedad)
4. Aplicar pañete de cal (3–5 mm) sobre la capa de arcilla como acabado final
5. Encalar como de costumbre

### Especificaciones

- **Espesor total del muro:** ~100 mm (vs. 85 mm estándar)
- **Sobrecosto:** ~$2–4 por área de panel (la arcilla normalmente es gratis — se extrae durante la excavación de cimentaciones)
- **STC:** ~45–50
- **Cambio en producción:** Ninguno al panel mismo. La capa de arcilla se aplica en obra después de la instalación.

**Ideal para:** Mejora económica. Usa material local gratuito. Sin cambios en la producción del panel. Además mejora la regulación de humedad.

## Opción 3: Panel doble con cavidad de fibra (mejor desempeño acústico, +15–20 STC)

Dos paneles estándar con una cavidad de 50–100 mm entre ellos, rellena con fibra orgánica suelta. Esta es la opción de alto rendimiento para ambientes realmente ruidosos.

### Por qué funciona

Se combinan tres principios acústicos:

1. **Doble masa** — dos muros de mortero en vez de uno. La ley de masa dice que duplicar la masa agrega ~6 dB de reducción sonora.
2. **Desacoplamiento** — la cavidad de aire interrumpe la trayectoria de vibración. El sonido se transmite eficientemente a través de materiales sólidos pero con dificultad a través de una cámara de aire. Los dos paneles vibran de forma independiente.
3. **Absorción** — la fibra suelta dentro de la cavidad absorbe la energía sonora que de otro modo rebotaría entre los dos paneles (resonancia de onda estacionaria).

### Materiales de relleno para la cavidad

Use lo que esté disponible localmente y sea económico. El relleno debe estar **suelto, no compactado** — las bolsas de aire dentro de la fibra son las que absorben el sonido.

| Material | Calidad acústica | Costo | Disponibilidad regional |
|---|---|---|---|
| **Cascarilla de arroz** | Excelente | Gratis–$2/bulto | Zonas arroceras (Asia, Latinoamérica) |
| **Fibra de coco** | Excelente | $3–5/bulto | Regiones costeras tropicales |
| **Pasto estrella seco** | Buena | Gratis | América tropical (invasivo, se retira de los potreros) |
| **Viruta de madera** | Buena | Gratis–$1/bulto | Carpinterías |
| **Gravilla volcánica suelta** | Buena (por masa) | $2–3/bulto | Regiones volcánicas (Andes, Centroamérica, SE asiático) |
| **Fibra de hoja de plátano seca** | Buena | Gratis | Zonas plataneras y bananeras |

**La cascarilla de arroz es la mejor opción general** donde esté disponible: liviana, no se compacta con el tiempo, naturalmente resistente al fuego (alto contenido de sílice) y extremadamente económica o gratis en los molinos arroceros.

### Construcción

1. Instalar el panel exterior como de costumbre (empernado al marco de la estructura o viga de amarre)
2. Dejar un espacio de 50–100 mm (definido por separadores o una columna/soporte de montaje más ancho)
3. Rellenar la cavidad con el material de fibra de forma suelta — no compactar
4. Instalar el panel interior, cerrando la cavidad
5. Ambos paneles se empernan a la misma estructura portante

El ancho de la cavidad depende del espacio disponible y del desempeño deseado:

| Ancho de cavidad | Mejora STC | Espesor total del muro |
|---|---|---|
| 50 mm | +12–15 STC | ~220 mm |
| 75 mm | +15–18 STC | ~245 mm |
| 100 mm | +18–20 STC | ~270 mm |

### Especificaciones

- **Espesor total del muro:** 220–270 mm (vs. 85 mm estándar)
- **Sobrecosto:** ~$65–70 por m² (un panel adicional) + $2–5 para relleno de cavidad = ~$70–75 extra por m²
- **STC:** 55–62
- **Cambio en producción:** Ninguno — usa dos paneles estándar

**Ideal para:** Fachadas sobre calles concurridas, edificaciones junto a autopistas, alcobas frente a vías ruidosas, salones de música, talleres adyacentes a espacios de vivienda.

## Opciones combinadas

Las opciones se acumulan. Para el máximo desempeño acústico en un muro crítico:

| Combinación | STC | Sobrecosto/m² | Caso de uso |
|---|-----|---|---|
| Panel estándar | 40–45 | Base | Lado tranquilo |
| Solo mortero denso | 43–48 | +$1–2 | Ruido leve, mejora más económica |
| Mortero denso + capa de arcilla | 48–52 | +$3–6 | Ruido de tráfico moderado, muro individual |
| Panel doble + cavidad de fibra | 55–62 | +$70–75 | Vía concurrida |
| Panel doble (mortero denso) + cavidad de fibra + arcilla interior | 58–65 | +$75–80 | Autopista, industria, discoteca al lado |

## Ejemplo típico de edificación

Una casa de un piso en una esquina concurrida, con jardín por dos lados:

| Muro | Da hacia | Tratamiento | STC | Sobrecosto |
|---|---|---|-----|---|
| Muro norte (10 m²) | Vía concurrida | Panel doble + cascarilla de arroz | 55–60 | ~$700–750 |
| Muro este (6 m²) | Calle secundaria | Mortero denso + capa de arcilla | 48–52 | ~$20–36 |
| Muro sur (10 m²) | Jardín | Panel estándar | 42–45 | $0 |
| Muro oeste (6 m²) | Jardín del vecino | Panel estándar | 42–45 | $0 |
| **Sobrecosto total** | | | | **~$720–790** |

Por ~$750, el muro más ruidoso obtiene aislamiento acústico de nivel profesional mientras los muros tranquilos se mantienen estándar. La mejora acústica agrega menos del 10% al costo total de la casa según el [presupuesto estimado](09-presupuesto-estimado.md).

## Notas sobre materiales

### Seguridad contra incendio del relleno de cavidad

- **Cascarilla de arroz:** Alto contenido de sílice, naturalmente resistente al fuego. No sostiene la llama. Se carboniza pero se autoextingue.
- **Fibra de coco:** Lenta para encenderse, se autoextingue cuando está suelta.
- **Pasto/paja seca:** Más inflamable. Tratar con solución de borato (mismo tratamiento que para la guadua) para resistencia al fuego si se usa en la cavidad. La cavidad está sellada entre dos paneles de mortero, por lo que el riesgo de ignición es muy bajo de todas formas.
- **Gravilla volcánica:** Incombustible.

### Humedad en la cavidad

La cavidad debe mantenerse seca. Ambos paneles están sellados con mortero y pañete de cal — la humedad no debería entrar. Sin embargo:

- No usar el sistema de panel doble bajo el nivel del terreno o en zonas inundables
- Asegurar que la parte superior de la cavidad esté sellada (viga de amarre o remate en mortero)
- En climas extremadamente húmedos, dejar pequeñas aberturas de ventilación arriba y abajo de la cavidad (cubiertas con malla para evitar el ingreso de insectos) para permitir circulación de aire

### Instalación posterior

La mejora acústica se puede **agregar después** a un muro existente de panel estándar:

1. Construir un segundo muro de panel 50–100 mm por dentro del muro existente
2. Rellenar la cavidad con fibra
3. El espacio interior se reduce por el ancho de la cavidad + el espesor del panel (~135–185 mm por muro mejorado)

Esto permite construir con paneles estándar ahora y mejorar muros específicos después si el ruido se vuelve un problema — por ejemplo, si una calle tranquila se vuelve concurrida después de una urbanización.
