jreuteler/bahareque-modular/fr/03-materiaux.md

# Materiaux

## Liste des materiaux (par panneau)

| Materiau | Specification | Quantite | Notes |
|---|---|---|---|
| Corniere L en acier | L 40x40x4 mm, galvanise a chaud (ASTM A36 / equivalent ICONTEC NTC 2542) | 2x 1,0 m + 2x 2,5 m = 7,0 m | Stock courant colombien (Gerdau Diaco, Aceros Arequipa, Acesco, Ferrasa). Barres standard de 6 m, decoupe a la tronconneuse |
| Bandes de serrage | Plat 40x3 mm, galvanise, trous correspondants | 4x 1,0 m = 4,0 m | Haut + bas, les deux faces |
| Goussets d'angle + boulonnerie | Plat de renfort + boulons M12/M8 | 1 jeu | Liaison d'angle plus rigide qu'une simple soudure |
| Vis | Acier inoxydable, autotaraudeuses | ~28 par panneau | A travers bande de serrage → bambou → PEHD → ame (tous les ~70 mm, une pour deux lattes) |
| Blocs en PEHD | Section 30x30 mm, recycle | 2x 1,0 m = 2,0 m | Sur les ames des cornieres L superieure + inferieure |
| Lattes de bambou (verticales) | Traitees au borate, ~20 mm de large | ~54 lattes x 2,5 m | ~27 par face |
| Latte de bambou (diagonale) | Traitee au borate, 60x20 mm | 2x ~2,69 m | 1 par face, coins opposes |
| Fil galvanise | Fil de ligature | ~5 m | ~16-20 ligatures aux croisements |
| Gaine PVC | Electrique 16 mm | ~5 m | Protection des cables |
| Cable 12V | Bipolaire | ~6 m | Circuit d'eclairage |
| Cable 120V | Tripolaire (P+N+T) | ~6 m | Circuit secteur |
| Douilles E10 | Supports de lampe a vis | 6 | 3 par face |
| Connecteurs rapides | 2 broches (12V) + 3 broches (120V) | 2 + 2 | Aux deux bords verticaux |
| Grillage a poule | Grillage hexagonal galvanise, 25 mm | ~5,5 m2 | Les deux faces + recouvrement |
| Mortier de ciment (de base) | 1:4 ciment:sable + additifs | ~0,147 m3 cavite nette (apres 30 % guadua + acier) | ~310 kg humide / ~294 kg durci (densite ~2 000 kg/m3) |
| Mortier a la chaux pouzzolanique au pasto estrella (optimise) | Chaux hydraulique + 30 % cendres volantes/RHA + fibres pasto estrella | ~0,147 m3 meme cavite | ~270 kg humide / ~257 kg durci (densite ~1 750 kg/m3) |
| Fibre PP | Hachee 6-12 mm | ~200 g | Prevention des fissures de retrait |
| Adjuvant pouzzolanique | Cendre volcanique / cendre de balle de riz / metakaolin | ~2 kg | Reduction du pH, durabilite |

**L'enduit a la chaux et le badigeon de chaux sont appliques sur site apres l'installation du panneau -- ils ne font pas partie du panneau lui-meme.**

---

## Details des materiaux

### Bambou structurel

Le systeme utilise des lattes de bambou structurel fendu comme materiau de remplissage principal. L'espece de reference est la **Guadua angustifolia** (connue sous le nom de *guadua* en Amerique latine, *cana guadua* en Equateur, *tacuara* dans certaines regions) -- le bambou structurel le plus resistant des Ameriques. Cependant, toute espece de bambou structurel a grand diametre peut etre adaptee.

Proprietes cles de la Guadua angustifolia :

- **Resistance en traction :** 150-200 MPa (comparable a l'acier doux)
- **Croissance :** Atteint le diametre de recolte (10-15 cm) en 4 a 5 ans
- **Aire de repartition :** 0-2 000 m d'altitude dans les Ameriques tropicales (Colombie, Equateur, Amerique centrale)
- **Recolte :** Coupee a 4-6 ans (lignification maximale). Les chaumes plus jeunes sont trop tendres ; les plus vieux deviennent cassants.
- **Traitement :** Solution de borate (borax + acide borique) par methode Boucherie modifiee ou trempage. Previent les attaques d'insectes et la degradation fongique. Non toxique, efficace pendant plus de 20 ans lorsqu'enrobe dans le mortier.

#### Alternatives pour d'autres regions

| Espece | Region | Notes |
|---|---|---|
| *Dendrocalamus asper* | Asie du Sud-Est | Grand diametre, resistant. Substitut direct. |
| *Bambusa bambos* | Asie du Sud/Sud-Est | Epineux, resistant. Necessite des lattes plus larges. |
| *Phyllostachys edulis* (Moso) | Chine, zones temperees | Plus petit diametre. Utiliser des lattes plus larges et plus fines. |
| *Phyllostachys bambusoides* | Japon, zones temperees | Bonne resistance. Chaumes plus petits. |
| *Guadua chacoensis* | Argentine, Paraguay | Proche parente de G. angustifolia. |

Le systeme fonctionne avec tout bambou structurel pouvant etre fendu en lattes. Ajuster la largeur et l'espacement des lattes selon l'espece disponible.

### Cadre en corniere L en acier

- **Profil :** L 40x40x4 mm corniere a ailes egales (ASTM A36 / ICONTEC NTC 2542)
- **Masse :** ~2,42 kg/m ; cadre du panneau au total ~17 kg + ~4 kg de bandes de serrage + ~1 kg de goussets/boulonnerie = **~22 kg par panneau**
- **Galvanisation :** A chaud selon ISO 1461, revetement de zinc minimum de 85 um
- **Duree de vie :** 80-100 ans en environnement tropical non cotier a l'epaisseur de zinc specifiee (le panneau en service est continument contrevente dans la matrice alcaline du mortier, qui auto-passive l'acier expose)
- **Approvisionnement :** Article courant a l'echelle mondiale. En Colombie : Gerdau Diaco, Aceros Arequipa, Acesco, Ferrasa, Colmena/Sidenal, Perfilamos del Cauca. Stock en barres de 6 m chez pratiquement tout marchand d'acier de construction. Pas de commande speciale, pas de fabrication sur mesure, pas d'ame asymetrique
- **Profils alternatifs :** L 50x50x4 ou L 50x50x5 (un peu plus lourds, egalement stock courant) sont des substituts directs. Le tube carre (SHS) 40x40x2 fonctionne aussi structurellement, mais necessite que les bandes de serrage soient soudees plutot que vissees a travers l'ame
- **Pourquoi pas un profile en T ?** Les versions anterieures de ce document specifiaient T 60×60×7 mm (~45 kg par panneau). Le panneau en service continument contrevente n'a pas besoin de l'ame symetrique du profile en T -- une ame de corniere L unilaterale est structurellement equivalente avec environ la moitie de la masse d'acier, la moitie du cout et une disponibilite radicalement meilleure. Les profiles en T ouverts restent le bon choix uniquement la ou la resistance au flambage selon l'axe faible compte (par ex. colonnes autoportantes -- le tube carre ferme est prefere au profile en T dans ce systeme).

### Blocs d'espacement en PEHD

- **Source :** Planches a decouper en PEHD recycle, sections de tuyaux, ou plaques
- **Proprietes :** Zero absorption d'eau, imputrescible, dimensionnellement stable, facile a usiner
- **Usinage :** Scie a table ou scie a ruban pour la decoupe. Defonceuse ou ciseau pour les encoches d'angle.

#### Alternatives au PEHD

| Materiau | Avantages | Inconvenients |
|---|---|---|
| **PEHD recycle** (prefere) | Imputrescible, zero absorption d'eau, largement disponible a partir du flux de dechets | Necessite des outils de coupe |
| **Bois dur de qualite marine** (teck, ipe, greenheart) | Resistant, naturellement imputrescible, facile a usiner | Couteux, se degrade tout de meme sur des decennies en milieu humide |
| **Bois tendre traite** (pin traite au CCA ou au borate) | Bon marche, largement disponible | Duree de vie plus courte (20-40 ans), peut necessiter un remplacement |
| **Blocs de caoutchouc dense** (caoutchouc de pneus recycles) | Imputrescible, amortissant, gratuit a partir de pneus usages | Plus difficile a usiner avec precision, peut se comprimer avec le temps |
| **Blocs de beton/mortier** | Cout nul, coules dans des moules, permanents | Fragiles, plus difficiles a entailler pour les diagonales, lourds |
| **Blocs imprimes en 3D** (PETG ou ASA) | Geometrie precise incluant les encoches, reproductible | Necessite une imprimante 3D, degradation UV si expose |

L'exigence critique est : le bloc doit maintenir sa dimension de 30 mm pendant toute la duree de vie du batiment pour preserver le profil )( des lattes. Le PEHD remplit le mieux cette condition, mais tout materiau resistant a l'humidite et a la compression fonctionnera.

### Mortier

- **Dosage de base :** 1 part de ciment Portland type I : 4 parts de sable de riviere propre (bien gradue, 0-4 mm)
- **Fibre PP :** 200 g par panneau (~1 kg par m3). Previent les fissures de retrait plastique pendant le durcissement.
- **Adjuvant pouzzolanique :** 5-10% de remplacement du ciment.
  - **Cendre volcanique** -- disponible dans les regions andines, naturellement pouzzolanique
  - **Cendre de balle de riz (CBR)** -- disponible dans les regions rizieres (Asie, Amerique latine)
  - **Metakaolin** -- argile kaolinique transformee, disponible mondialement mais plus couteux
  - **Fonction :** Reagit avec l'hydroxyde de calcium du ciment, reduisant le pH de ~12,5 a ~10-11 au fil du temps. Cela ralentit la degradation de la guadua enrobee.
- **Eau :** Propre, potable. Rapport E/C ~0,45-0,50 pour une consistance coulable sur table vibrante.

### Enduit a la chaux (sur site)

- **Type :** Chaux hydraulique (NHL 3,5 ou NHL 5) ou chaux eteinte (chaux en pate) + sable
- **Dosage :** 1:2,5 a 1:3 chaux:sable
- **Fibre optionnelle :** Herbe sechee hachee (herbe etoile, sisal, chanvre) a ~1 cm de longueur. Ajoute de la resistance en traction et aux fissures. La cellulose naturelle dure plus de 30 ans dans la chaux (pH ~10, bien moins agressif que le ciment).
- **Application :** A la truelle, 3-5 mm. La texture fait la beaute -- la perfection mecanique n'est pas l'objectif.

### Badigeon de chaux (sur site)

- Chaux eteinte + eau, applique au pinceau en couches fines
- Penetre et se lie chimiquement a l'enduit a la chaux (carbonatation)
- Renouveler tous les 5 a 10 ans en entretien
- Peut etre teinte avec des pigments naturels (oxydes de terre) pour la couleur

### Grillage a poule

- Grillage hexagonal galvanise, ouverture de 25 mm, fil de 0,7-0,9 mm
- Agrafe ou ligature sur la face du panneau avant l'application du mortier
- Fournit un accrochage mecanique pour l'adherence du mortier
- Les deux faces

### Grillage fin en aluminium (optionnel)

- Moustiquaire standard anti-insectes/poussieres, ouverture de 1-1,5 mm, aluminium
- Place sous le grillage a poule sur les deux faces
- Bloque insectes, poussieres fines et pollen
- Comme propriete secondaire, fournit egalement une attenuation mesurable des radiofrequences
- Non requis pour la fonction structurelle -- a ajouter selon les conditions locales d'insectes/poussieres
