jreuteler/bahareque-modular/fr/09-estimation-couts.md

# Estimation des couts

> **Avertissement :** Il s'agit d'estimations de couts de materiaux uniquement, basees sur les prix de 2025 en Colombie (region du Eje Cafetero). La main-d'oeuvre n'est pas incluse -- le systeme est concu pour la production communautaire ou la main-d'oeuvre est contribuee, non achetee. Les prix varient significativement selon la region, la devise et la chaine d'approvisionnement. Utilisez ces chiffres comme point de depart, pas comme un budget.

Deux specifications de melange de mortier sont documentees dans ce projet : le **melange de base** (mortier ciment-sable + 30 % de teneur en guadua + enduit a la chaux 10 mm les deux faces) et le **melange bahareque optimise** (chaux pouzzolanique + fibres pasto estrella + 30 % de guadua + enduit a la chaux 5 mm). Les deux ventilations de couts sont presentees ci-dessous.

## Cout par panneau -- melange de base (materiaux uniquement)

| Materiau | Specification | Qte par panneau | Cout unitaire (USD) | Total (USD) |
|---|---|---|---|---|
| Acier en corniere L | L 40x40x4 mm, ASTM A36 | 7,0 m | 4,00 $/m | 28,00 $ |
| Galvanisation | A chaud, processus par lot | 1 cadre | 2,00 $ | 2,00 $ |
| Bandes de serrage | Plat 40x3 mm, galv. | 4,0 m | 1,00 $/m | 4,00 $ |
| Goussets d'angle + boulonnerie | Plat + M12/M8 | 1 jeu | 3,00 $ | 3,00 $ |
| Vis inox | Autotaraudeuses, A2 | 40 pcs | 0,08 $ | 3,20 $ |
| Blocs en PEHD | Recycle, 30x30 mm | 2,0 m | 1,50 $/m | 3,00 $ |
| Lattes de bambou (verticales + horizontales, 30 % densite de cavite) | Guadua traitee au borate | ~400 m au total | 0,05 $/m | 20,00 $ |
| Lattes de bambou (diagonales) | 60x20 mm, traitee | ~5,4 m | 0,30 $/m | 1,60 $ |
| Ligatures en fil | Galvanise | 5 m | 0,10 $/m | 0,50 $ |
| Gaine PVC | Electrique 16 mm | 5 m | 0,30 $/m | 1,50 $ |
| Cable 12V + douilles | Bipolaire + 6x E10 | 1 ensemble | 3,00 $ | 3,00 $ |
| Cable 120V + connecteurs | Tripolaire + connecteurs rapides | 1 ensemble | 4,00 $ | 4,00 $ |
| Grillage a poule | Hex. galv., 25 mm | 5,5 m2 | 0,80 $/m2 | 4,40 $ |
| Ciment | Portland type I | ~54 kg | 0,15 $/kg | 8,10 $ |
| Sable (mortier) | Sable de riviere propre | ~240 kg | 0,02 $/kg | 4,80 $ |
| Fibre PP | Hachee 6-12 mm | 200 g | 5,00 $/kg | 1,00 $ |
| Adjuvant pouzzolanique | Cendre volcanique ou CBR | 2 kg | 0,50 $/kg | 1,00 $ |
| **Sous-total panneau -- base** | | | | **~93 $** |

### Finitions sur site, base (par surface de panneau)

| Materiau | Qte par panneau | Cout (USD) |
|---|---|---|
| Enduit a la chaux (10 mm chaque face) | ~25 kg chaux + ~65 kg sable | 6,50 $ |
| Badigeon de chaux (les deux faces) | ~2 kg chaux | 0,50 $ |
| **Sous-total finitions -- base** | | **7,00 $** |

### **Cout total des materiaux par panneau -- base : ~100 USD**

### Cout par m2 de mur fini -- base

- Surface du panneau : 1,0 m x 2,5 m = 2,5 m2
- Cout des materiaux par m2 : **~40 USD/m2**

## Cout par panneau -- melange bahareque optimise (materiaux uniquement)

Le melange optimise remplace le mortier ciment Portland-sable par une chaux hydraulique + pouzzolane, remplace la fibre PP par du pasto estrella (gratuit, collecte sur place) et utilise un enduit a la chaux plus mince de 5 mm. Meme cadre en corniere L, meme contenu de bambou, memes composants electriques et structurels.

| Materiau | Specification | Qte par panneau | Cout unitaire (USD) | Total (USD) |
|---|---|---|---|---|
| Acier en corniere L + galvanisation + bandes de serrage + goussets | (comme la base) | | | 37,20 $ |
| Vis inox, PEHD, bambou, ligatures, gaine, cables, grillage | (comme la base) | | | 41,20 $ |
| Chaux hydraulique (liant principal) | NHL 3.5 ou NHL 5 | ~42 kg | 0,30 $/kg | 12,60 $ |
| Cendres volantes ou cendre de balle de riz (pouzzolane, 30 % equivalent ciment) | FA ou CBR | ~15 kg | 0,10 $/kg | 1,50 $ |
| Sable (mortier) | Sable de riviere propre | ~200 kg | 0,02 $/kg | 4,00 $ |
| Fibre de pasto estrella (herbe etoile sechee) | Collectee sur place | ~3 kg | gratuit | 0,00 $ |
| **Sous-total panneau -- optimise** | | | | **~96 $** |

### Finitions sur site, optimise (par surface de panneau)

| Materiau | Qte par panneau | Cout (USD) |
|---|---|---|
| Enduit a la chaux (5 mm chaque face) | ~12 kg chaux + ~33 kg sable | 3,30 $ |
| Badigeon de chaux (les deux faces) | ~2 kg chaux | 0,50 $ |
| **Sous-total finitions -- optimise** | | **3,80 $** |

### **Cout total des materiaux par panneau -- optimise : ~100 USD**

### Cout par m2 de mur fini -- optimise

- Cout des materiaux par m2 : **~40 USD/m2**

> **Les deux melanges aboutissent au meme cout materiaux** (~100 $/panneau, ~40 $/m2). Le melange optimise echange un cout d'ingredients chaux/pouzzolane legerement superieur (vs. ciment Portland moins cher) contre un cout d'enduit moindre (plus mince), un cout nul de fibre PP et un CO₂ incorpore nettement inferieur (voir [Impact environnemental](10-impact-environnemental.md)). Le melange optimise est donc un **gain net en carbone et en authenticite patrimoniale a cout pratiquement equivalent**.

## Comparaison avec la construction conventionnelle

| Systeme de mur | Cout materiaux par m2 (USD) | Duree de vie | Notes |
|---|---|---|---|
| **Ce systeme de panneaux -- base** | **~40 $** | **80-100 ans** | Inclut structure, electricite, finition |
| **Ce systeme de panneaux -- optimise** | **~40 $** | **80-100 ans** | Meme prix, moins de carbone |
| Bloc de beton (15 cm) | 25-35 $ | 40-60 ans | Necessite armature, coulis, enduit, peinture, electricite separee |
| Brique cuite | 30-45 $ | 60-80 ans | Necessite mortier, enduit, peinture, electricite separee |
| Plaques de platre sur montants acier | 20-30 $ | 20-30 ans | Pas de masse thermique, non porteur, necessite peinture, electricite separee |
| Bahareque conventionnel (in situ) | 15-25 $ | 15-30 ans | Pas d'electricite, qualite de finition variable, duree de vie courte sans ingenierie |
| Bloc d'adobe | 10-20 $ | 20-40 ans | Mauvaise performance sismique, pas d'electricite, murs epais necessaires |

**Constat cle :** Le systeme de panneaux coute **20-35 % de plus par m2 que le bloc de beton** -- mais inclut l'electricite integree, a une duree de vie 1,5-2 fois superieure, offre de meilleures performances thermiques et acoustiques, et produit une finition superieure. Lorsqu'on prend en compte le cout du cablage electrique separee d'une maison en bloc de beton (~8-15 $/m2 pour gaines, cables, prises et leur pose), le systeme de panneaux est competitif sur la base mur-complet-pret-a-occuper.

## Cout par maison (estimation approximative)

Une maison simple a un etage avec mezzanine (50 m2 d'emprise au sol, ~70 m2 habitables mezzanine incluse) :

| Composant | Quantite | Cout (USD) |
|---|---|---|
| Panneaux muraux | ~40 panneaux (100 m2 de mur) | 2 600-2 800 $ |
| Fondation (beton, armature) | ~5 m3 de beton | 800-1 200 $ |
| Lisse haute (bois/bambou) | ~30 m | 200-400 $ |
| Toiture (tuiles terre cuite + pannes) | ~65 m2 | 1 200-1 800 $ |
| Plancher (dalle beton ou terre battue) | ~50 m2 | 400-800 $ |
| Fenetres + portes | ~8 ouvertures | 600-1 200 $ |
| Tableau electrique + transformateur | 1 ensemble | 200-400 $ |
| Plomberie (basique) | Cuisine + salle de bain | 300-600 $ |
| **Total materiaux** | | **6 300-9 200 $** |

Il s'agit uniquement des materiaux. Dans un modele de construction communautaire, la main-d'oeuvre est contribuee. Dans un modele avec entrepreneur, ajouter 40-60% pour la main-d'oeuvre.

**En contexte :** Une maison comparable en bloc de beton en Colombie rurale coute 12 000-20 000 $ (materiaux + main-d'oeuvre) et dure 40-60 ans. Ce systeme atteint une qualite similaire ou superieure a environ la moitie du cout avec le double de la duree de vie.

## Strategies de reduction des couts

| Strategie | Economies | Notes |
|---|---|---|
| Recolter son propre bambou | 30-40% du cout du bambou | Necessite 1+ hectares de peuplement de guadua, 4-5 ans de maturite |
| Recycler le PEHD a partir de dechets | 100% du cout du PEHD | Planches a decouper, chutes de tuyaux, dechets industriels |
| Utiliser de la cendre volcanique (gratuite) | 100% du cout de la pouzzolane | Disponible dans les regions andines, collecter et tamiser |
| Utiliser de la fibre d'herbe etoile au lieu du PP | 100% du cout de la fibre | Herbe invasive, gratuite, utilisation circulaire |
| Galvanisation par lots (50+ cadres) | 15-20% du cout de galv. | Remise de volume aupres de l'usine de galvanisation |
| Carriere de sable communautaire | 50-80% du cout du sable | Si un acces au sable de riviere est disponible localement |
| Produire sa propre chaux a partir de calcaire | 50-70% du cout de la chaux | Necessite un four (construction unique), calcaire local |

## Variations regionales des prix

Les couts des materiaux varient considerablement selon les regions. Les estimations ci-dessus concernent la Colombie. Multiplicateurs approximatifs :

| Region | Multiplicateur | Notes |
|---|---|---|
| Colombie (Eje Cafetero) | 1,0x (reference) | Guadua abondante, cendre volcanique disponible |
| Equateur, Perou | 0,8-1,1x | Materiaux similaires, cana guadua disponible |
| Amerique centrale | 1,0-1,3x | Bambou disponible, l'acier peut couter plus cher |
| Philippines, Indonesie | 0,7-1,0x | Bambou abondant et bon marche, main-d'oeuvre tres faible |
| Inde | 0,6-0,9x | Bambou et main-d'oeuvre tres faibles, acier abordable |
| Afrique subsaharienne | 0,8-1,2x | Especes de bambou variables, le ciment peut etre cher |
| Europe du Sud | 2,0-3,0x | Materiaux disponibles mais plus chers |

Ces multiplicateurs sont des guides approximatifs. La variable la plus importante est le cout du bambou -- si vous cultivez le votre, il est pratiquement gratuit.
