jreuteler/bahareque-modular/fr/10-impact-environnemental.md

# Impact environnemental

## Empreinte carbone par panneau -- melange de base

Les chiffres ci-dessous refletent la specification de base actuelle : cadre acier L 40x40x4 + 30 % de teneur en guadua dans la cavite + mortier ciment-sable (de base) + enduit a la chaux 10 mm sur les deux faces. Voir [Anatomie du panneau](02-anatomie-du-panneau.md) et [Materiaux](03-materiaux.md) pour les details.

| Materiau | Qte par panneau | CO2 incorpore (kg) | Source d'emission |
|---|---|---|---|
| Ciment Portland (~18 % de la masse du mortier) | ~54 kg | 43,2 | Calcination + combustible du four (~0,8 kg CO2/kg ciment) |
| Cadre acier en corniere L + bandes de serrage | ~22 kg acier | 39,6 | Siderurgie (~1,8 kg CO2/kg acier) |
| Galvanisation (zinc) | ~0,7 kg zinc | 2,8 | Fonderie de zinc (~4 kg CO2/kg zinc) |
| Sable (~82 % de la masse du mortier) | ~240 kg | 1,2 | Extraction + transport |
| Grillage a poule + grillage aluminium | ~2 kg | 3,6 | Production de fil d'acier |
| Gaine PVC | ~0,3 kg | 0,6 | Fabrication PVC (~2 kg CO2/kg) |
| Cables + connecteurs | ~0,5 kg | 1,5 | Cuivre + plastique |
| Blocs en PEHD | ~0,5 kg | 0,5 | Si recycle : ~1 kg CO2/kg (contre 3 pour le vierge) |
| Chaux (dans l'enduit, calcination) | ~22 kg chaux | 18,0 | Calcination du calcaire (~0,8 kg CO2/kg chaux) |
| Fibre PP (additif du mortier) | ~0,2 kg | 0,4 | Production de polypropylene |
| **Sous-total emissions** | | **~111 kg CO2** | |
| Bambou (carbone sequestre pendant la croissance) | ~38 kg poids sec (30 % cavite) | **-60 a -75 kg CO2** | Le bambou sequestre ~1,6-2,0 kg CO2 par kg de masse seche |
| Enduit a la chaux (reabsorbe le CO2 par carbonatation) | ~22 kg chaux | **-6 a -9 kg CO2** | La carbonatation de la chaux recapture ~30-50 % du CO2 de calcination sur des decennies |
| **CO2 net par panneau, melange de base** | | **~30-45 kg CO2** | |
| **CO2 net par m2 de mur, base** | | **~12-18 kg CO2/m2** | |

## Empreinte carbone par panneau -- melange bahareque optimise

Le melange optimise (chaux pouzzolanique + pasto estrella + 30 % guadua + enduit 5 mm) abaisse le carbone incorpore par plusieurs leviers cumules :

| Levier | Delta CO2 par panneau vs base |
|---|---|
| Remplacer 30 % du ciment par cendres volantes ou CBR | -10 a -13 kg |
| Remplacer le mortier de ciment Portland par chaux hydraulique + pouzzolane | -8 a -12 kg |
| Remplacer la fibre PP par du pasto estrella | -0,5 kg |
| Enduit a la chaux 5 mm les deux faces (-50 % de volume de chaux) | -9 kg de calcination, +4 kg de moindre recuperation par carbonatation = **-5 kg net** |
| **Reduction totale** | **-24 a -30 kg CO2 par panneau** |
| **CO2 net par panneau, melange optimise** | **~6 a 20 kg CO2** |
| **CO2 net par m2 de mur, optimise** | **~3 a 8 kg CO2/m2** |

Avec des pouzzolanes disponibles localement (cendre volcanique dans la region cafetiere colombienne, cendre de balle de riz du Tolima/Valle del Cauca) et de la fibre de pasto estrella issue de la propriete elle-meme, le melange bahareque optimise s'approche du **neutre carbone** par panneau. Si le peuplement de bambou est gere comme puits de carbone (rotation par taillis avec permanence de la biomasse), le systeme devient **carbone-negatif** : le mur absorbe plus de CO2 sur sa duree de vie qu'il n'en a fallu pour le construire.

## Comparaison avec les systemes de murs conventionnels

| Systeme de mur | kg CO2 par m2 | Ratio par rapport au panneau de base |
|---|---|---|
| **Ce systeme de panneaux -- melange de base** | **12-18** | **1x (reference)** |
| **Ce systeme de panneaux -- melange bahareque optimise** | **3-8** | **~0,4x base** |
| Bloc de beton (15 cm, enduit) | 40-60 | 3-4x base |
| Brique cuite (enduite) | 50-80 | 3-5x base |
| Mur en beton arme (15 cm) | 70-100 | 5-7x base |
| Plaques de platre sur montants acier | 15-25 | 1-1,5x base |
| Bahareque conventionnel (enduit terre, sans cadre acier) | 3-8 | 0,3-0,5x base |
| Bloc d'adobe | 5-10 | 0,4-0,7x base |

Le melange de base du systeme de panneaux produit **~3 fois moins de CO2 que le bloc de beton ou la brique** -- les deux materiaux de mur les plus courants dans le monde en developpement. Le melange bahareque optimise s'approche des niveaux de la construction traditionnelle en terre tout en offrant des performances structurelles et une duree de vie tres superieures.

## Carbone par annee de service

Lorsque la duree de vie est prise en compte, la comparaison devient encore plus favorable (a 80-100 ans de duree de vie de conception pour ce systeme) :

| Systeme de mur | kg CO2/m2 | Duree de vie (annees) | kg CO2/m2/an |
|---|---|---|---|
| **Ce systeme de panneaux -- base** | 15 | 90 | **0,17** |
| **Ce systeme de panneaux -- optimise** | 5 | 90 | **0,06** |
| Bloc de beton | 50 | 50 | 1,00 |
| Brique cuite | 65 | 70 | 0,93 |
| Plaques de platre sur montants acier | 20 | 25 | 0,80 |
| Bahareque conventionnel | 5 | 20 | 0,25 |

**Sur sa duree de vie, ce systeme de panneaux produit ~10 fois moins de carbone par annee de service que le bloc de beton.**

## Vers la neutralite ou la negativite carbone

Le systeme de panneaux est deja a faible empreinte carbone. Avec les substitutions suivantes, il approche la neutralite carbone :

| Substitution | CO2 economise par panneau | Faisabilite |
|---|---|---|
| Remplacer 50% du ciment par de la pouzzolane (cendre volcanique, CBR) | -10 kg | Disponible dans les regions volcaniques et rizieres |
| Utiliser de l'acier recycle (four a arc electrique) | -7 kg | Depend de la chaine d'approvisionnement locale en acier |
| Remplacer la fibre PP par de l'herbe etoile | -0,5 kg | Disponible partout ou l'herbe pousse |
| Augmenter la teneur en bambou (lattes plus epaisses, plus de diagonales) | -3 a -5 kg sequestration supplementaire | Materiau gratuit/bon marche |
| Utiliser de la chaux bio (four a bois avec combustible de taillis) | -3 kg | Methode traditionnelle de production de chaux |
| **Reduction potentielle totale** | **-20 a -25 kg** | |

Avec ces substitutions, le CO2 net par panneau descend a **~0-5 kg** -- effectivement neutre en carbone. Si la teneur en bambou est encore augmentee ou si le peuplement de bambou est gere comme un puits de carbone, le systeme devient **negatif en carbone** : le mur absorbe plus de CO2 pendant sa vie que n'en a emis sa construction.

## Utilisation de l'eau

- **Preparation du mortier :** ~15-20 litres par panneau (eau de cure reutilisee autant que possible)
- **Cure :** ~50 litres sur 7 jours (methode par brumisation/toile de jute)
- **Preparation de l'enduit a la chaux :** ~10 litres par panneau
- **Total :** ~75-80 litres par panneau, soit ~30 litres par m2 de mur

Pour comparaison : la production de blocs de beton utilise ~40-50 litres par m2 de mur. La production de briques cuites utilise ~100+ litres par m2 (refroidissement du four inclus).

## Dechets

- **Chutes d'acier :** Recyclees (valeur de ferraille)
- **Chutes de bambou :** Compostees ou utilisees comme tuteurs de jardin/paillis
- **Dechets de mortier :** Minimaux -- le coulage sur table vibrante est precis. Tout exces est reutilise pour le panneau suivant.
- **Lit de sable :** Reutilise indefiniment (le sable n'est pas consomme, juste comprime et aere)
- **Chutes de PEHD :** Recyclees ou reutilisees pour des blocs plus petits
- **Dechets d'emballage :** Minimaux -- la plupart des materiaux arrivent en vrac

Le systeme produit **quasi zero dechet de construction**. C'est une consequence directe de la prefabrication en atelier -- chaque coupe est planifiee, chaque materiau est mesure.

## Fin de vie (apres 80-100 ans)

Lorsqu'un panneau atteint sa fin de vie :

| Materiau | Elimination | Impact environnemental |
|---|---|---|
| Ossature en acier | Recyclage (100% recyclable) | Positif -- la ferraille a de la valeur |
| Mortier + bambou | Concasser et utiliser comme granulat ou remblai | Inerte -- le mortier est du calcium/silice/sable, le bambou est organique |
| Enduit a la chaux | Retourne au carbonate de calcium (calcaire) | Neutre en carbone -- le CO2 absorbe pendant la carbonatation est re-emis, bilan net zero |
| Blocs en PEHD | Recyclage | Recyclable |
| Cables en cuivre | Recyclage (haute valeur de ferraille) | Positif |
| Gaines PVC | Recyclage la ou des installations existent | Recyclable en principe |

**Aucun dechet dangereux.** Pas d'amiante, pas de peinture au plomb, pas de mousse isolante synthetique, pas de produits chimiques de bois traite sous pression. Le panneau est fait d'acier, de bambou, de sable, de ciment et de chaux -- il retourne a la terre ou au circuit de recyclage proprement.
