jreuteler/bahareque-modular/fr/11-transport-manutention.md

# Transport et manutention

## Specifications du panneau pour la manutention

| Propriete | Valeur |
|---|---|
| Dimensions | 1,0 m x 2,5 m x 85 mm |
| Poids de l'assemblage a sec (tel qu'expedie sur site) | **~75 kg** |
| Poids du panneau fini (melange de base, apres coulage in situ + cure + enduit) | ~440 kg |
| Poids du panneau fini (melange bahareque optimise) | ~360 kg |
| Centre de gravite | Centre (construction symetrique) |
| Zones fragiles | Angles, aretes (le mortier peut s'ecailler une fois coule en cas d'impact) |
| Cure minimale avant manutention | 7 jours apres coulage in situ |
| Cure minimale avant installation | 14 jours recommandes -- noter qu'en modele de coulage in situ, le panneau est dresse et le mortier coule sur place, donc « installation » et « coulage » se font ensemble sur site |

## Modele de production primaire : coulage in situ

**Le modele de production primaire consiste a expedier l'assemblage a sec (~75 kg) sur site et a couler le mortier in situ contre coffrage.** Le panneau fini de ~440 kg n'est jamais deplace en tant qu'unite -- il devient directement partie du mur, evitant les couts d'engins de levage lourds et le risque de fissuration au transport. Voir [Processus de construction](04-processus-construction.md) pour le protocole de coulage vertical in situ.

La manutention de panneaux durcis (sections suivantes) s'applique au modele alternatif : coulage du mortier en atelier sur table vibrante, panneaux entierement durcis livres comme elements finis. Cette approche reste documentee comme option pour les constructeurs preferant la production en atelier, mais ajoute des couts significatifs de levage, transport et taux de rebut.

## Portage a la main -- assemblage a sec (~75 kg)

L'assemblage a sec (cadre acier corniere L + esterilla de bambou + grillage + equipements, avant mortier) est leve et positionne par **2 personnes avec une simple sangle**. Aucun dispositif de portage, pas de grue, pas de chariot elevateur -- c'est l'un des avantages operationnels centraux du modele de coulage in situ.

### Sangle simple (assemblage a sec)

1. Enrouler une seule sangle (50 mm x capacite 500+ kg) autour du panneau a mi-hauteur (~125 cm du bas)
2. Chaque porteur saisit une extremite de la sangle a deux mains, sur les longs cotes opposes
3. Soulever ensemble ; le panneau pend verticalement entre eux
4. Marcher a allure normale ; le panneau peut etre porte 30-50 m avant pause

**Poids par personne : ~38 kg** -- entierement gerable pour les portages courts typiques atelier-camion, camion-stock-site, stock-pose.

## Portage a la main -- panneau fini durci (modele atelier alternatif)

Un panneau fini a ~360-440 kg **ne peut pas etre porte a la main**. Levage mecanique requis (palan a chaine, mini-pelle, ou petite grue mobile). C'est la raison principale pour laquelle le modele de coulage in situ est prefere.

Si des panneaux coules en atelier doivent etre deplaces (par ex. production de phase pilote avant validation du protocole in situ), utiliser :

### Dispositif de portage (panneau durci, ~360-440 kg)

Deux perches de bambou (3 m de long, 8-10 cm de diametre) passees dans des boucles de sangle robuste enroulees autour du panneau a 1/4 et 3/4 de la hauteur :

1. Poser le panneau a plat
2. Enrouler deux sangles (50 mm de large, capacite 1 000+ kg) autour du panneau a ~60 cm et ~190 cm du bas
3. Passer une perche de bambou dans les boucles de sangle de chaque cote
4. **4 personnes par perche, 8 porteurs au total** pour un panneau melange de base a ~440 kg, ou 6 porteurs pour un panneau melange optimise a ~360 kg
5. Le panneau pend verticalement entre les perches

**Poids par personne : ~55 kg (base) / ~45 kg (optimise)** -- au bord superieur de la manutention manuelle sure. Longues distances ou escaliers : utiliser plutot un levage mecanique.

### Levage et basculement

- **Ne jamais soulever un panneau par un seul bord** -- le mortier peut fissurer sous son propre poids en porte-a-faux
- **Toujours soulever depuis deux points** symetriques, ou depuis le bas en soutenant l'arriere
- **Basculement de l'horizontale a la verticale :** Deux personnes tiennent le bord superieur, deux personnes soulevent le bas. Pivoter lentement. Soutenir le bas sur une cale rembourree pendant la rotation.

## Stockage en atelier

Apres durcissement, les panneaux sont stockes **verticalement (sur chant)** dans un ratelier en A :

- Appuyer les panneaux des deux cotes d'un cadre incline (comme un livre ouvert)
- 10-15 panneaux par cote du ratelier
- Separer les panneaux avec de petites cales en bois pour permettre la circulation d'air
- Couvrir avec une bache ou un toit pour proteger de la pluie directe (le mortier en cours de durcissement peut etre lessiver par la pluie forte avant la cure complete)
- Maintenir hors du sol -- poser le bord inferieur sur du gravier ou un rail en bois

**Espace necessaire :** ~3 m x 1 m de surface au sol pour 20-30 panneaux stockes.

## Transport par camion

### Chargement

1. Mettre les panneaux debout verticalement dans la benne du camion, appuyes contre un cote
2. Placer des cales en bois (chutes, bambou ou mousse) entre chaque panneau
3. Sangles les panneaux a la paroi laterale du camion avec des sangles a cliquet a 1/3 et 2/3 de la hauteur
4. Ne jamais empiler les panneaux a plat les uns sur les autres -- le panneau du bas se fissurera sous le poids de la pile
5. Maximum ~15-20 panneaux par camionnette standard (selon la capacite du vehicule et l'etat des routes)

### Considerations routieres

- **Routes goudronnees :** Pas de precautions particulieres au-dela du sanglage
- **Routes non goudronnees/difficiles :** Reduire la vitesse. Ajouter du rembourrage en mousse ou carton entre les panneaux. Sangler fermement -- les panneaux peuvent glisser et s'ecailler sur les bosses.
- **Pentes raides :** S'assurer que les panneaux penchent vers le haut de la pente (pas en sens inverse) pour eviter le basculement
- **Distance :** Pas de limite. Les panneaux sont entierement durcis et autonomes. Ils peuvent voyager sur n'importe quelle distance.

### Dechargement

1. Retirer les sangles de haut en bas
2. Deux personnes par panneau -- une au bord superieur, une soutenant le bas
3. Accompagner chaque panneau jusqu'au ratelier de stockage en A sur le site
4. Ne jamais laisser tomber ou faire glisser les panneaux -- les aretes de mortier s'ecaillent facilement

## Grue / palan (pour les etages superieurs)

Pour les batiments a deux etages, les panneaux doivent etre hisses au deuxieme etage :

- **Mat de levage simple :** Un poteau en bambou ou en acier avec une corde et une poulie. Deux personnes tirent la corde, une guide le panneau. Convient pour de faibles volumes.
- **Palan a chaine sur poutre :** Fixer un palan a chaine de 500 kg a la poutre en acier du batiment. Accrocher a la sangle de portage du panneau. Une personne opere, une guide. Rapide et controle.
- **Chariot elevateur (si disponible) :** Fourches sous le panneau (protege avec du carton). Lever et placer directement en position.

**Ne pas jeter, rouler ou trainer les panneaux.** Le mortier est resistant en compression mais peut se fissurer sur un impact ponctuel.

## Dommages et reparation

| Type de dommage | Cause | Reparation |
|---|---|---|
| Ecaillage d'angle (petit) | Impact pendant le transport | Reboucher au mortier, enduire par-dessus. Cosmetique uniquement. |
| Fissure d'arete (surface) | Choc pendant la manutention | Reboucher a l'enduit a la chaux. N'affecte pas la structure. |
| Fissure traversante (mortier) | Chute ou impact severe | Le panneau peut etre compromis. Evaluer : si l'ossature en acier est intacte et la fissure est <2 mm, reboucher au mortier et surveiller. Si la fissure est >5 mm ou l'ossature est deformee, rejeter le panneau. |
| Connecteur rapide casse | Accrochage pendant le transport | Remplacer le connecteur (soude ou serti). |

**Taux de rejet :** Avec un soin raisonnable, prevoir <5% des panneaux subissant un dommage quelconque pendant le transport et la manutention, et <1% necessitant un rejet. Les panneaux rejetes peuvent etre depouilles de leurs composants electriques et recycles comme materiau de remblai.

## Liste de controle avant transport

- [ ] Panneau durci depuis minimum 7 jours (14 recommandes)
- [ ] Panneau marque avec le type (P/O/S/W) et la date de production
- [ ] Circuits electriques testes (verification de continuite 12V + 120V)
- [ ] Pas de fissures visibles >1 mm
- [ ] Angles intacts
- [ ] Sangles ou dispositif de portage prepares
- [ ] Benne du camion propre, cales pretes, sangles disponibles
- [ ] Itineraire verifie pour l'etat des routes (ponts, gabarits, pentes)
