jreuteler/bahareque-modular/it/03-materiali.md

# Materiali

## Distinta dei Materiali (per pannello)

| Materiale | Specifica | Quantità | Note |
|---|---|---|---|
| Acciaio angolare L | L 40×40×4 mm, zincato a caldo (ASTM A36 / ICONTEC NTC 2542) | 2× 1,0 m + 2× 2,5 m = 7,0 m | Stock commerciale colombiano (Gerdau Diaco, Aceros Arequipa, Acesco, Ferrasa). Barre da 6 m, taglio con troncatrice |
| Barre di serraggio | Piatto 40×3 mm, zincato, fori corrispondenti | 4× 1,0 m = 4,0 m | Superiore + inferiore, entrambi i lati |
| Cartelle d'angolo + bulloneria | Piatto di rinforzo + bulloni M12/M8 | 1 set | Connessione d'angolo più rigida della sola saldatura |
| Viti | Acciaio inossidabile, autoperforanti | ~28 per pannello | Attraverso barra di serraggio → bambù → HDPE → anima (ogni ~70 mm, una ogni due listelli) |
| Distanziatori in HDPE | Sezione 30×30 mm, riciclati | 2× 1,0 m = 2,0 m | Sulle anime degli angolari L superiore + inferiore |
| Listelli di bambù (verticali) | Trattati con borato, ~20 mm di larghezza | ~54 listelli × 2,5 m | ~27 per lato |
| Listello di bambù (diagonale) | Trattato con borato, 60×20 mm | 2× ~2,69 m | 1 per lato, angoli opposti |
| Filo zincato | Filo per legature | ~5 m | ~16–20 legature agli incroci |
| Tubazione PVC | Elettrica 16 mm | ~5 m | Protezione cavi |
| Cavo 12V | Bipolare | ~6 m | Circuito illuminazione |
| Cavo 120V | Tripolare (L+N+T) | ~6 m | Circuito rete |
| Portalampada E10 | A vite | 6 | 3 per lato |
| Connettori a scatto | Bipolari (12V) + tripolari (120V) | 2 + 2 | Entrambi i bordi verticali |
| Rete a maglia esagonale | Zincata, 25 mm | ~5,5 m² | Entrambe le facce + sovrapposizione |
| Malta cementizia (base) | 1:4 cemento:sabbia + additivi | ~0,147 m³ cavità netta | ~310 kg umida / ~294 kg indurita (densità ~2 000 kg/m³) |
| Malta di calce pozzolanica con pasto estrella (ottimizzata) | Calce idraulica + 30 % cenere volante/CCR + fibre pasto estrella | ~0,147 m³ stessa cavità | ~270 kg umida / ~257 kg indurita (densità ~1 750 kg/m³) |
| Fibra PP | Tagliata 6–12 mm | ~200 g | Prevenzione fessurazioni in presa |
| Aggiunta pozzolanica | Cenere vulcanica / cenere di lolla di riso / metacaolino | ~2 kg | Riduzione pH, durabilità |

**L'intonaco di calce e il latte di calce vengono applicati in cantiere dopo l'installazione del pannello — non fanno parte del pannello stesso.**

---

## Dettagli dei Materiali

### Bambù Strutturale

Il sistema utilizza listelli di bambù strutturale spaccato come materiale di tamponamento primario. La specie di riferimento è la **Guadua angustifolia** (conosciuta come *guadua* in tutta l'America Latina, *caña guadua* in Ecuador, *tacuara* in alcune regioni) — il bambù strutturale più resistente delle Americhe. Tuttavia, qualsiasi specie di bambù strutturale di grande diametro può essere adattata.

Proprietà chiave della Guadua angustifolia:

- **Resistenza a trazione:** 150–200 MPa (paragonabile all'acciaio dolce)
- **Crescita:** Raggiunge il diametro di raccolta (10–15 cm) in 4–5 anni
- **Areale:** 0–2.000 m di altitudine nelle Americhe tropicali (Colombia, Ecuador, America Centrale)
- **Raccolta:** Taglio a 4–6 anni (massima lignificazione). I culmi più giovani sono troppo teneri; quelli più vecchi diventano fragili.
- **Trattamento:** Soluzione di borato (borace + acido borico) con metodo Boucherie modificato o immersione. Previene l'attacco degli insetti e il degrado fungino. Non tossico, efficace per oltre 20 anni quando inglobato nella malta.

#### Alternative per Altre Regioni

| Specie | Regione | Note |
|---|---|---|
| *Dendrocalamus asper* | Sud-est asiatico | Grande diametro, resistente. Sostituto diretto. |
| *Bambusa bambos* | Asia meridionale/sud-orientale | Spinoso, resistente. Richiede listelli più larghi. |
| *Phyllostachys edulis* (Moso) | Cina, zone temperate | Diametro minore. Usare listelli più larghi e sottili. |
| *Phyllostachys bambusoides* | Giappone, zone temperate | Buona resistenza. Culmi più piccoli. |
| *Guadua chacoensis* | Argentina, Paraguay | Parente stretta della G. angustifolia. |

Il sistema funziona con qualsiasi bambù strutturale che possa essere spaccato in listelli. Regolare la larghezza e la spaziatura dei listelli per la specie disponibile.

### Telaio in Angolare L in Acciaio

- **Profilo:** L 40×40×4 mm angolare ad ali uguali (ASTM A36 / ICONTEC NTC 2542)
- **Massa:** ~2,42 kg/m; telaio del pannello totale ~17 kg + ~4 kg barre di serraggio + ~1 kg cartelle/bulloneria = **~22 kg per pannello**
- **Zincatura:** A caldo secondo ISO 1461, rivestimento minimo 85 μm di zinco
- **Durata:** 80–100 anni in ambienti tropicali non costieri allo spessore di zinco specificato (il pannello in servizio è continuamente controventato nella matrice alcalina della malta, che auto-passiva l'acciaio esposto)
- **Approvvigionamento:** Articolo commerciale a livello mondiale. In Colombia: Gerdau Diaco, Aceros Arequipa, Acesco, Ferrasa, Colmena/Sidenal. Stock in barre da 6 m presso praticamente ogni fornitore di acciaio strutturale. Nessun ordine speciale, nessuna fabbricazione su misura, nessuna anima asimmetrica
- **Profili alternativi:** L 50×50×4 o L 50×50×5 (leggermente più pesanti, anch'essi stock commerciale) sono sostituti diretti. Tubo cavo quadrato (SHS) 40×40×2 funziona anche strutturalmente, ma richiede che le barre di serraggio siano saldate invece che avvitate attraverso l'anima
- **Perché non profilo a T:** Versioni precedenti di questo documento specificavano T 60×60×7 mm (~45 kg per pannello). Il pannello in servizio continuamente controventato non richiede l'anima simmetrica del profilo a T — un'anima ad angolare L unilaterale è strutturalmente equivalente con circa metà della massa d'acciaio, metà del costo e disponibilità drammaticamente migliore. I profili a T aperti restano la scelta corretta solo dove conta la resistenza all'instabilità sull'asse debole (es. colonne indipendenti — il tubo quadrato chiuso è preferito al profilo a T in questo sistema).

### Distanziatori in HDPE

- **Provenienza:** Taglieri in HDPE riciclato, sezioni di tubo o lastre
- **Proprietà:** Zero assorbimento d'acqua, non marcescibile, dimensionalmente stabile, facile da lavorare
- **Lavorazione:** Sega circolare o sega a nastro per il taglio. Fresa o scalpello per gli intagli angolari.

#### Alternative all'HDPE

| Materiale | Vantaggi | Svantaggi |
|---|---|---|
| **HDPE riciclato** (preferito) | Non marcescibile, zero assorbimento d'acqua, ampiamente disponibile dal flusso di rifiuti | Richiede utensili da taglio |
| **Legno duro uso marino** (teak, ipe, greenheart) | Resistente, naturalmente resistente alla marcescenza, facile da lavorare | Costoso, si degrada comunque nel corso dei decenni in ambienti umidi |
| **Legno tenero trattato** (pino trattato CCA o con borato) | Economico, ampiamente disponibile | Durata inferiore (20–40 anni), potrebbe richiedere sostituzione |
| **Blocchi di gomma densa** (gomma da pneumatici riciclati) | Non marcescibile, ammortizzante, gratuito dai pneumatici usati | Più difficile da lavorare con precisione, potrebbe comprimersi nel tempo |
| **Blocchi di calcestruzzo/malta** | Costo zero, gettati in stampi, permanenti | Fragili, più difficili da intagliare per le diagonali, pesanti |
| **Blocchi stampati in 3D** (PETG o ASA) | Geometria precisa inclusi gli intagli, riproducibili | Richiede stampante 3D, degrado UV se esposti |

Il requisito critico è: il blocco deve mantenere la sua dimensione di 30 mm per tutta la vita dell'edificio per preservare il profilo )( dei listelli. L'HDPE soddisfa meglio questo requisito, ma qualsiasi materiale che resista all'umidità e alla compressione funzionerà.

### Malta

- **Miscela base:** 1 parte cemento Portland Tipo I : 4 parti sabbia di fiume pulita (ben assortita, 0–4 mm)
- **Fibra PP:** 200 g per pannello (~1 kg per m³). Previene le fessurazioni da ritiro plastico durante la presa.
- **Aggiunta pozzolanica:** 5–10% di sostituzione del cemento.
  - **Cenere vulcanica** — disponibile nelle regioni andine, naturalmente pozzolanica
  - **Cenere di lolla di riso (RHA)** — disponibile nelle regioni risicole (Asia, America Latina)
  - **Metacaolino** — argilla caolinitica lavorata, disponibile globalmente ma più costosa
  - **Funzione:** Reagisce con l'idrossido di calcio nel cemento, riducendo il pH da ~12,5 a ~10–11 nel tempo. Questo rallenta il degrado della guadua incorporata.
- **Acqua:** Pulita, potabile. Rapporto A/C ~0,45–0,50 per consistenza gettabile su tavolo vibrante.

### Intonaco di Calce (in cantiere)

- **Tipo:** Calce idraulica (NHL 3.5 o NHL 5) o calce spenta (calce in pasta) + sabbia
- **Miscela:** 1:2,5 a 1:3 calce:sabbia
- **Fibra opzionale:** Erba essiccata sminuzzata (erba stella, sisal, canapa) a ~1 cm di lunghezza. Aggiunge resistenza a trazione e alle fessurazioni. La cellulosa naturale dura oltre 30 anni nella calce (pH ~10, molto meno aggressivo del cemento).
- **Applicazione:** A cazzuola, 3–5 mm. La texture è la bellezza — la perfezione meccanica non è l'obiettivo.

### Latte di Calce (in cantiere)

- Calce spenta + acqua, applicato a pennello in strati sottili
- Penetra e si lega chimicamente con l'intonaco di calce (carbonatazione)
- Riapplicare ogni 5–10 anni per manutenzione
- Può essere tinto con pigmenti naturali (ossidi di terra) per il colore

### Rete a Maglia Esagonale

- Rete esagonale zincata, apertura 25 mm, filo 0,7–0,9 mm
- Graffettata o legata alla faccia del pannello prima dell'applicazione della malta
- Fornisce aggancio meccanico per l'aderenza della malta
- Entrambe le facce

### Rete Fine in Alluminio (opzionale)

- Rete standard anti-insetti/polvere, apertura 1–1,5 mm, alluminio
- Posizionata sotto la rete a maglia esagonale su entrambe le facce
- Blocca insetti, polvere fine e polline dall'ingresso attraverso la matrice di malta
- Come proprietà secondaria, fornisce anche un'attenuazione misurabile delle radiofrequenze
- Non necessaria per la funzione strutturale — aggiungere in base alle condizioni locali di insetti/polvere
