jreuteler/bahareque-modular/it/04-processo-costruttivo.md

# Processo Costruttivo

> **Aggiornamento SVG in sospeso:** alcuni diagrammi di questo capitolo sono stati generati per la precedente specifica del telaio in profilo a T e sono stati temporaneamente scollegati in attesa di rigenerazione per l'attuale specifica di **angolare L 40×40×4 mm**. Vedere [`SVG-STATUS.md`](../SVG-STATUS.md) nella radice del repository.

## Allestimento del Laboratorio

Tutti i pannelli vengono costruiti in un laboratorio coperto — indipendente dalle condizioni meteorologiche, a qualità controllata, efficiente come una catena di montaggio. Requisiti minimi del laboratorio:

- Area coperta: ~6 × 4 m (tetto, lati aperti accettabili)
- Postazione di saldatura (solo per fabbricazione telai)
- Trapano a colonna o trapano manuale
- 2× tavoli vibranti (~1,2 × 2,7 m ciascuno)
- Fornitura di sabbia per il letto
- Betoniera (elettrica o manuale)
- Utensili manuali di base: cacciaviti, tronchesi, pinze, spillatrice

Sequenza di Assemblaggio

## Fasi di Produzione

### Fase 1: Fabbricazione del Telaio

1. Tagliare l'angolare L 40×40×4 a misura: 2× 1,0 m (superiore/inferiore) + 2× 2,5 m (laterali). Stock commerciale, barre da 6 m
2. Tagliare gli angoli a 45° (oppure tagliare diritti con un'ala sovrapposta all'altra). Saldare in dima — tutti i telai identici. Cartelle d'angolo opzionali per rigidità in fase di movimentazione
3. Forare i fori di serraggio ogni ~70 mm lungo le anime superiore e inferiore dell'angolare (uno ogni due listelli di bambù, ~14 fori per barra, ~28 totali)
4. Zincare a caldo il telaio completato (processo a lotti — inviare 20–50 telai alla volta)

**Tutti i telai sono identici indipendentemente dalla variante del pannello.** La dima garantisce dimensioni costanti. Una dima, un telaio, per sempre.

### Fase 2: Distanziatori in HDPE

1. Tagliare il materiale HDPE a 30 × 30 mm × 1.000 mm (2 per pannello)
2. Tagliare gli intagli angolari: 10 × 10 mm ad ogni estremità (4 intagli per blocco, 8 per pannello)
3. Montare i blocchi sulle anime degli angolari L superiore e inferiore con viti o adesivo

### Fase 3: Impianto Elettrico

1. Infilare il cavo 12V nella tubazione PVC
2. Infilare il cavo 120V in una tubazione PVC separata
3. Montare i portalampada E10 (3 in alto, su ogni lato)
4. Per il Tipo O/S: montare la scatola presa, collegare la derivazione al cavo principale
5. Per il Tipo S: montare la scatola interruttore a 120 cm di altezza
6. Per il Tipo W: montare le colonne montanti dell'acqua (alimentazione CPVC/PEX, scarico PVC) con uscite tappate
7. Fissare i connettori a scatto su entrambi i bordi verticali (bipolari per 12V, tripolari per 120V)

### Fase 4: Listelli di Bambù (Lato 1)

1. Posizionare il telaio del pannello in piano sul tavolo di lavoro, lato 1 in su
2. Disporre i listelli verticali di bambù contro l'anima, tra i distanziatori in HDPE
3. Lasciare ~20 mm di distanza tra i listelli per la penetrazione della malta
4. Posizionare la tubazione PVC con i cavi tra i listelli, contro l'anima
5. Infilare il listello diagonale attraverso l'intaglio in HDPE in basso a sinistra, fino all'intaglio in alto a destra (a livello dell'anima)
6. Pre-tensionare la diagonale e fissare ad entrambe le estremità

Sistema di Serraggio a Vite

### Fase 5: Serraggio a Vite (Lato 1)

1. Posizionare la barra di serraggio in acciaio (2 mm × 30 mm × 1.000 mm) sui listelli di bambù al angolare L superiore
2. Allineare i fori della barra di serraggio con i fori nell'anima del angolare L
3. Avvitare le viti in acciaio inossidabile attraverso: barra di serraggio → listelli di bambù → fori dell'anima
4. La barra di serraggio si flette per adattarsi alla variazione naturale di spessore — autoregolante
5. Ripetere al angolare L inferiore
6. Legare con filo la diagonale ad ogni listello verticale agli incroci (~8–10 legature)

**Tempo: ~5 minuti per lato per il serraggio, ~3 minuti per le legature in filo**

### Fase 6: Capovolgere e Ripetere (Lato 2)

1. Capovolgere il pannello
2. Ripetere le fasi 4–5 sull'altro lato
3. La diagonale sul lato 2 va dall'alto a sinistra al basso a destra (opposta alla diagonale del lato 1 — insieme formano una X)

### Fase 7: Rete

1. Stendere la rete a maglia esagonale sul lato 1, estendendola 20 mm oltre i bordi del telaio (per sovrapposizione con i pannelli adiacenti)
2. Graffettare o legare con filo al telaio e ai listelli di bambù
3. Se si usa la rete anti-insetti in alluminio: posizionarla sotto la rete a maglia esagonale
4. Capovolgere e ripetere sul lato 2

### Fase 8: Getto della Malta

Processo di Getto della Malta

Questa è l'innovazione chiave nel metodo di applicazione:

1. **Preparare il tavolo vibrante:** Superficie livellata, motore montato sotto
2. **Stendere il letto di sabbia:** ~30 mm di sabbia asciutta pulita sulla superficie del tavolo. La sabbia si adatta a qualsiasi irregolarità della faccia del pannello e impedisce l'aderenza della malta al tavolo.
3. **Posizionare il pannello a faccia in giù** sul letto di sabbia (lato rete a maglia esagonale che tocca la sabbia)
4. **Miscelare la malta:** 1:4 cemento:sabbia + fibra PP + aggiunta pozzolanica, A/C ~0,45–0,50 (gettabile ma non liquida)
5. **Versare la malta** sul retro esposto del pannello, riempiendo tra i listelli e coprendo la rete
6. **Avviare la vibrazione:** Far funzionare il tavolo per 30–60 secondi. La vibrazione:
   - Spinge la malta attraverso le fessure tra i listelli
   - Riempie completamente la cavità centrale
   - Elimina i vuoti e le bolle d'aria
   - La malta penetra fino alla rete sulla faccia anteriore (ora appoggiata sulla sabbia)
7. **Staggiare** la malta in eccesso a filo con i bordi del telaio
8. **Lisciare con la cazzuola** (questa diventa la faccia interna)

> **Guida alla costruzione del tavolo vibrante:** Un progetto per un tavolo vibrante fai da te (motore, piattaforma, molle) sarà pubblicato in questo repository una volta che il design sarà stato testato e dimostrato sicuro nella pratica. Fino ad allora, qualsiasi piattaforma piana con un vibratore per calcestruzzo fissato al bordo funzionerà per i primi esperimenti.

**Perché il tavolo vibrante su letto di sabbia?**
- Gravità + vibrazione = riempimento completo, zero vuoti
- Letto di sabbia = nessuna cassaforma necessaria, la sabbia si adatta alla forma del pannello
- Nessuna attrezzatura di spruzzatura necessaria (più economica della malta spruzzata)
- Getto da un solo lato riempie entrambi i lati — la malta fluisce attraverso le fessure tra i listelli
- Qualità costante — la vibrazione elimina l'errore umano

### Fase 9: Stagionatura

1. Coprire il pannello con un telo di plastica per trattenere l'umidità
2. Mantenere umido per almeno 7 giorni (nebulizzazione o tela di juta bagnata)
3. Resistenza piena a 28 giorni
4. I pannelli possono essere impilati verticalmente (di taglio) dopo 7 giorni per risparmiare spazio
5. Marcare ogni pannello con il tipo di variante e la data di produzione

**Ritmo di produzione: 3–4 pannelli al giorno** con 2 tavoli vibranti in parallelo, team di 4–6 persone. Lavoro attivo per pannello: ~15–20 minuti. Stagionatura passiva: 7–28 giorni (i pannelli stagionano mentre se ne producono di nuovi).

### Fase 10: Trasporto e Installazione

1. Trasportare i pannelli al cantiere utilizzando un semplice carrello a cavalletto o un camion
2. Imbullonare i pannelli nel telaio in acciaio dell'edificio alle posizioni dei pilastri (alette imbullonate pre-saldate sui pilastri)
3. I pannelli adiacenti si toccano malta contro malta
4. Connettere a scatto l'impianto elettrico tra pannelli adiacenti (12V + 120V)
5. Testare i circuiti prima della finitura

### Fase 11: Finitura in Cantiere

1. Riempire eventuali giunti tra i pannelli con malta
2. Applicare striscia di rete a maglia esagonale sui giunti (se non già sovrapposta dai bordi del pannello)
3. Applicare intonaco di calce: 3–5 mm, a cazzuola, entrambe le facce
4. Lasciar stagionare (mantenere umido per 3–5 giorni)
5. Applicare latte di calce: 2–3 strati sottili a pennello

La parete finita è continua — nessun giunto visibile, nessun acciaio visibile, nessuna vite visibile. Solo intonaco di calce liscio con la texture di una parete fatta a mano.

## Lista di Controllo Qualità

- [ ] Dimensioni del telaio entro ±2 mm
- [ ] Tutti i fori di serraggio forati e allineati
- [ ] Listelli di bambù trattati con borato (sfumatura verde/blu visibile)
- [ ] Diagonale pre-tensionata (dovrebbe risuonare se colpita)
- [ ] Tutte le legature in filo tese
- [ ] Circuiti elettrici testati prima della malta (12V e 120V)
- [ ] Consistenza della malta corretta (prova di abbassamento)
- [ ] Vibrazione eseguita per tutti i 30–60 secondi
- [ ] Nessun vuoto visibile sulla faccia di getto dopo la vibrazione
- [ ] Pannello marcato con tipo e data
- [ ] Stagionatura di almeno 7 giorni prima della movimentazione
