jreuteler/bahareque-modular/it/05-prestazioni-strutturali.md

# Prestazioni Strutturali

## Architettura del Sistema

Questo sistema di pannelli è stato progettato per funzionare **con un telaio in acciaio a pilastri e travi** — la configurazione che raccomandiamo per edifici multipiano in zone sismiche. In questa configurazione, il telaio in acciaio porta i carichi gravitazionali e sismici mentre i pannelli forniscono controventatura laterale, chiusura alle intemperie, massa termica e servizi integrati.

Tuttavia, i pannelli sono **strutturalmente capaci di funzionare senza un telaio in acciaio**. Con una capacità di compressione che supera ampiamente i carichi residenziali tipici (due montanti laterali in angolare L L 40×40×4), una fila di pannelli può comodamente portare un secondo piano e un tetto senza una struttura in acciaio indipendente. Una semplice trave di coronamento in legno o bambù in sommità collega i pannelli e distribuisce il carico del tetto.

**Due configurazioni:**

| Configurazione | Caso d'uso | Ruolo del pannello |
|---|---|---|
| **Con telaio in acciaio** (raccomandato) | Multipiano, zone ad alta sismicità, commerciale/istituzionale | Tamponamento — i pannelli si imbullonano nel telaio, l'acciaio porta i carichi primari |
| **Senza telaio in acciaio** (più semplice, costo inferiore) | Monoplanare + soppalco/mezzanino, zone a sismicità moderata, residenziale | Portante — i pannelli portano direttamente il tetto e il piano superiore |

Le stime di capacità di carico sotto riportate si applicano a entrambe le configurazioni. Il telaio in acciaio aggiunge ridondanza e resistenza al momento flettente, ma non è necessario perché i pannelli funzionino strutturalmente.

## Prestazioni Sismiche

### Controventatura Diagonale

Ogni pannello contiene due listelli diagonali di bambù (uno per lato, angoli opposti), che formano una X visti frontalmente. Sotto carico sismico:

1. **Conversione taglio → trazione:** Quando il telaio dell'edificio oscilla lateralmente, una diagonale va in trazione mentre l'opposta va in compressione. La diagonale di bambù in trazione resiste alla forza di scorrimento in modo efficiente — il bambù ha un'eccellente resistenza a trazione (150–200 MPa per la Guadua angustifolia).
2. **Pre-tensione:** Le diagonali vengono installate con leggera pre-tensione, eliminando il gioco e garantendo un ingaggio immediato sotto carico.
3. **Reticolo di legature:** Le legature in filo zincato ad ogni incrocio diagonale-verticale (~16–20 legature totali) distribuiscono la forza della diagonale su tutta la faccia del pannello, prevenendo rotture localizzate.

**Miglioramento stimato: 3–5 volte la resistenza al taglio orizzontale** rispetto ai pannelli senza controventatura diagonale.

### Il Profilo )(

I distanziatori in HDPE mantengono i listelli di bambù a 30 mm dall'anima in alto e in basso. A mezza altezza, i listelli si flettono verso l'interno contro l'anima. La malta riempie questa distanza variabile, creando una sezione trasversale ad arco naturale:

- **Resistenza fuori piano:** L'arco di malta agisce come una volta ribassata, distribuendo efficientemente i carichi di vento o impatto verso i bordi rigidi del telaio.
- **Incastro meccanico:** La malta a spessore variabile blocca i listelli di bambù in posizione — non possono essere estratti senza rompere la malta.

### Modalità di Rottura Duttile

La combinazione di listelli di bambù, legature in filo e malta crea un composito che cede gradualmente:

1. Prima: la malta si fessura (segnale di allarme visibile)
2. Poi: le legature in filo si allungano (assorbimento di energia)
3. Poi: i listelli di bambù si deformano (alta duttilità)
4. Il telaio in acciaio resta intatto per tutto il processo — l'edificio non crolla

Questo è fondamentalmente diverso dalla muratura non armata, che cede in modo fragile (crollo improvviso senza preavviso).

## Resistenza al Fuoco

- **Inglobamento nella malta:** I listelli di bambù sono completamente inglobati nella malta (~85 mm di spessore di parete). La malta è incombustibile e funge da isolante termico per il bambù.
- **Carbonizzazione del bambù:** Anche se il fuoco penetra la malta, il bambù carbonizza lentamente e in modo prevedibile (simile alla costruzione in legno). Il telaio in acciaio retrostante mantiene l'integrità strutturale.
- **Finitura in intonaco di calce:** Incombustibile. Fornisce protezione antincendio aggiuntiva.
- **Nessun bambù esposto:** Una volta installato e finito, nessun bambù è visibile o accessibile alla fiamma.

## Prestazioni Termiche

- **Massa termica:** ~85 mm di malta forniscono una significativa massa termica — assorbe il calore durante il giorno, lo rilascia di notte. Riduce le escursioni termiche nei climi tropicali.
- **Traspirabilità:** L'intonaco di calce è permeabile al vapore. L'umidità passa attraverso la parete anziché restare intrappolata, prevenendo condensa e muffe.
- **Nessuno strato isolante:** Il sistema non include uno strato di isolamento termico. Nei climi tropicali (l'obiettivo primario), la massa termica è più preziosa dell'isolamento. Per i climi temperati, è possibile aggiungere uno strato di isolamento esterno sopra l'intonaco di calce.

## Prestazioni Acustiche

Il nucleo denso di malta fornisce una buona attenuazione acustica:

- **STC stimato (Classe di Trasmissione Sonora):** 40–45 per una parete a pannello singolo
- **Con intonaco di calce su entrambi i lati:** STC 42–48
- **Confronto:** Parete standard in blocchi di cemento: STC 40–45. Il sistema a pannelli è comparabile.

## Capacità di Carico

> **Avvertenza:** I valori sotto riportati sono stime analitiche conservative basate sulle proprietà dei materiali e sulla geometria. NON sono basati su test di laboratorio. Non utilizzare questi valori per l'ingegneria strutturale senza verifica indipendente. Le prestazioni effettive dipendono dalla qualità dei materiali, dalla lavorazione e dai dettagli delle connessioni. Vedi [Test Necessari](#test-necessari) qui sotto.

### Peso Proprio del Pannello

| Componente | Peso |
|---|---|
| Telaio in acciaio (angolare L 40×40×4, 7 m totali a 2,42 kg/m + barre di serraggio + cartelle) | ~22 kg |
| Malta del nucleo (cavità ~0,147 m³, indurita, densità ~2 000 kg/m³) | ~294 kg |
| Listelli di bambù + diagonali (~30 % cavità) | ~38 kg |
| Distanziatori HDPE, filo, rete, tubazione, cavi | ~6 kg |
| Intonaco di calce (10 mm su entrambi i lati) | ~100 kg |
| **Peso totale del pannello, miscela base** | **~460 kg** |
| **Peso per m² di parete, base** | **~184 kg/m²** |
| Peso totale del pannello, miscela bahareque ottimizzata (calce pozzolanica + pasto estrella + intonaco 5 mm) | ~380 kg |
| Peso di spedizione dell'assemblaggio a secco (telaio + bambù + rete + impianti, prima del getto) | ~75 kg |

Per confronto: parete in blocchi di cemento da 150 mm ≈ 180 kg/m². Il sistema a pannelli (miscela base) pesa circa quanto la muratura convenzionale per unità di superficie; la miscela bahareque ottimizzata è ~15 % più leggera. Critico per la logistica: il **peso di spedizione dell'assemblaggio a secco (~75 kg)** è la forma in cui il pannello viene trasportato dal laboratorio al cantiere (la malta viene gettata in opera).

### Carico Assiale (Verticale)

Ogni pannello ha due montanti laterali verticali in angolare L che possono portare carichi di compressione significativi:

| Elemento | Sezione trasversale | Capacità assiale conservativa |
|---|---|---|
| Montante laterale in angolare L (L 40×40×4 mm) | A ≈ 304 mm² | ~36 kN per montante (a σ = 120 MPa, ~50 % dello snervamento A36) |
| Due montanti laterali per pannello | 2 × 304 mm² | ~72 kN per pannello (~7 200 kg) |

**Cosa significa nella pratica:**

Una tipica casa monopiano con soppalco e tetto in tegole impone circa 200–400 kg di carico per metro lineare di parete (tetto + soffitto + solaio del mezzanino + carico vivo). Un singolo pannello da 1 m può portare **18–36 volte questo requisito**. **I pannelli non necessitano di un telaio in acciaio separato per portare un secondo piano e un tetto.**

Quando usati **con un telaio in acciaio**, questa capacità assiale è puro margine di riserva — l'acciaio porta i carichi gravitazionali. Quando usati **senza telaio in acciaio**, i pannelli sono la struttura portante. In quel caso, una trave di coronamento in legno o bambù in cima alla parete distribuisce il carico del tetto uniformemente su tutti i pannelli e li lega insieme.

L'instabilità per carico di punta non è una preoccupazione a questi livelli di carico **quando l'angolare L è annegato nel composito del pannello**: lo spessore di 85 mm della parete in malta fornisce al telaio angolare una rigidezza laterale continua. Il rapporto altezza-spessore (~2.500/85 ≈ 29) è ben entro i limiti di snellezza per pareti armate.

**Importante: limitazione dell'asse debole dei profili aperti.** Gli angolari L, profili a T e profili a C hanno rigidezza minima sul loro asse debole. Un montante L 40×40×4 indipendente senza controventatura del pannello (I_min ≈ 3,8 × 10⁴ mm⁴) si svergerebbe sotto carico modesto. La capacità di 36 kN per angolare L è la **capacità di snervamento assiale** ed è raggiungibile SOLO quando l'angolare è continuamente controventato dal riempimento del pannello (malta + guadua). Per colonne indipendenti in edifici multipiano, i profili aperti non sono adatti — usare invece tubo cavo quadrato (SHS).

### Carico Laterale (Nel Piano / Taglio Orizzontale)

Questo è il contributo strutturale primario del pannello — resistere alle forze orizzontali da vento e terremoti.

**Senza controventatura diagonale (solo malta + listelli verticali):**

Stima conservativa basata sulla resistenza al taglio della malta (τ ≈ 0,3 MPa per malta 1:4 cemento:sabbia) sulla sezione trasversale del pannello:

- Area di taglio: ~85 mm × 1.000 mm = 85.000 mm²
- Capacità di taglio conservativa: 85.000 × 0,3 = ~25 kN per pannello
- Con fattore di sicurezza 3: **~8 kN carico di esercizio per pannello**

**Con controventatura diagonale (la configurazione progettata):**

Il listello diagonale di bambù (60 × 20 mm, Guadua angustifolia) in trazione:

- Sezione trasversale: 1.200 mm²
- Resistenza a trazione conservativa: 80 MPa (usando ~50% del valore pubblicato di 150–200 MPa)
- Capacità di trazione della diagonale: 1.200 × 80 = ~96 kN
- Componente orizzontale (cos 69°): ~96 × 0,36 = ~34 kN per diagonale
- Due diagonali (una per lato, una in trazione): ~34 kN
- Le legature in filo e l'incastro della malta aggiungono ulteriore resistenza
- Con fattore di sicurezza 3: **~12–15 kN carico di taglio orizzontale di esercizio per pannello**

**Per contesto:** Una sezione di parete larga 3 m (3 pannelli) fornisce ~36–45 kN di resistenza al taglio orizzontale. Un edificio residenziale monopiano in una zona sismica moderata (PGA 0,2g) con 30 kN di massa sismica sopra la parete necessita di circa 6 kN di resistenza al taglio alla base per metro lineare di parete. Tre pannelli per metro forniscono 4–5 volte questo requisito.

Questi sono numeri molto conservativi. La matrice di malta, il reticolo di legature in filo e il profilo )( contribuiscono tutti con resistenza aggiuntiva non contabilizzata sopra.

### Carico Fuori Piano (Vento / Impatto)

Il pannello resiste alla pressione perpendicolare alla faccia della parete (aspirazione/pressione del vento, impatto):

- L'arco di malta creato dal profilo )( agisce come una volta ribassata tra i angolari L rigidi superiore e inferiore
- Stima conservativa per pressione uniforme del vento, trattando il pannello come una lastra su due appoggi:

| Parametro | Valore |
|---|---|
| Luce del pannello (tra angolari L superiore/inferiore) | 2,5 m |
| Larghezza del pannello | 1,0 m |
| Spessore della malta (minimo, al centro) | ~55 mm |
| Resistenza a flessione della malta (conservativa) | 1,0 MPa |
| Capacità stimata di pressione uniforme | ~0,7 kPa |
| Con fattore di sicurezza 2 | **~0,35 kPa carico di esercizio** |

**Per contesto:** 0,35 kPa ≈ velocità del vento ~25 m/s (90 km/h). Per zone a vento più forte, il telaio in acciaio (non il pannello) porta il carico del vento attraverso le connessioni trave-pilastro. Il pannello deve solo resistere alla pressione locale tra i propri elementi del telaio.

Il reticolo di listelli di bambù e le legature in filo forniscono una significativa resistenza fuori piano aggiuntiva non catturata nel semplice modello a lastra — il pannello è un composito, non una semplice lastra di malta.

### Carichi Puntuali (Accessori, Mensole, Mobili)

| Tipo di accessorio | Metodo di ancoraggio | Capacità conservativa |
|---|---|---|
| Oggetti leggeri (quadri, orologi, portasciugamani) | Chiodo o vite da muratura nella malta | 5–10 kg per ancoraggio |
| Oggetti medi (mensole, specchi, mobiletti) | Tassello a espansione in plastica nella malta (6–8 mm) | 15–25 kg per ancoraggio |
| Oggetti pesanti (pensili da cucina, scaldabagno, supporto TV) | Bullone passante all'anima del angolare L in acciaio | 50–100 kg per ancoraggio |
| Oggetti molto pesanti (libreria, dispensa piena) | Bulloni passanti multipli al angolare L + piastra di distribuzione | 200+ kg per punto di fissaggio |

**Consiglio:** L'anima del angolare L corre in una posizione nota (centro dello spessore della parete). Un cercametalli o una calamita la localizzano facilmente. Il bullonaggio passante all'anima fornisce un ancoraggio affidabile e ad alta capacità paragonabile all'intelaiatura con montanti in acciaio.

### Riepilogo — Capacità Conservativa in kg per Pannello

Per costruttori e non ingegneri, ecco gli stessi numeri espressi in chilogrammi. Questi sono **carichi di esercizio molto conservativi** (già divisi per fattori di sicurezza di 2–3). I carichi di rottura effettivi sono 2–3 volte superiori.

| Tipo di carico | Direzione | Capacità di esercizio conservativa | Cosa significa nella pratica |
|---|---|---|---|
| **Taglio orizzontale (sismico/vento)** | Orizzontale, nel piano della parete | **~1.200–1.500 kg per pannello** | Una forza orizzontale di 1,2–1,5 tonnellate applicata in cima a un singolo pannello prima che debba essere considerato al suo limite di esercizio. Una tipica casa monopiano necessita di ~600 kg di resistenza al taglio per metro di parete — un pannello ne fornisce il doppio. |
| **Fuori piano (pressione del vento)** | Perpendicolare alla faccia della parete | **~90 kg distribuiti sulla faccia del pannello** | Equivalente a ~36 kg/m² di pressione uniforme. Una persona che spinge forte contro la parete (~80 kg su ~0,3 m²) è ben entro la capacità. |
| **Assiale (verticale)** | Verso il basso, attraverso il pannello | **Supera ampiamente i carichi residenziali (~7 200 kg di snervamento assiale per pannello in composito)** | I due angolari L laterali portano molto più del tipico tetto + piano superiore per metro di parete. I pannelli possono portare un secondo piano e un tetto senza telaio in acciaio separato. |
| **Carico puntuale nella malta** | Estrazione / taglio all'ancoraggio | **~15–25 kg per ancoraggio** | Una staffa per mensola con 2 ancoraggi regge 30–50 kg in sicurezza. |
| **Carico puntuale al angolare L** | Bullone passante | **~50–100 kg per bullone** | Un pensile da cucina con 4 bulloni passanti regge 200–400 kg in sicurezza. |

> **Importante:** Queste sono stime, non valori testati. Saranno validate attraverso test fisici. Non utilizzare per l'ingegneria strutturale senza verifica indipendente. In caso di dubbio, fissare gli oggetti pesanti al telaio in acciaio dell'edificio, non al pannello.

## Durabilità (Vita Utile di Progetto 80–100 Anni)

| Componente | Meccanismo di degrado | Prevenzione | Vita attesa |
|---|---|---|---|
| Telaio in acciaio | Corrosione | Zincatura a caldo (85 μm+) | 80–100 anni (non costiero) |
| Listelli di bambù | Attacco insetti, degrado fungino | Trattamento con borato + inglobamento nella malta (alcalino, anaerobico) | 80+ anni |
| Malta | Carbonatazione, aggressione atmosferica | Protetta dall'intonaco di calce (strato sacrificale) | 100+ anni |
| Intonaco di calce | Erosione superficiale, microfessurazione | Autoriparante (la carbonatazione chiude le fessure), latte di calce rinnovabile | Indefinita con manutenzione |
| Latte di calce | Degrado UV, erosione da pioggia | Riapplicare ogni 5–10 anni | 5–10 anni per strato |
| Impianto elettrico | Degrado dell'isolamento | La tubazione PVC consente la sostituzione dei cavi senza aprire la parete | Cavi: 30–50 anni, sostituibili |
| Distanziatori in HDPE | Nessuno significativo | Protetto dai UV (dentro la parete) | 100+ anni |

### Programma di Manutenzione

| Intervallo | Azione | Costo stimato |
|---|---|---|
| Ogni 5–10 anni | Rinnovo del latte di calce | $50–100 per edificio |
| Ogni 15–20 anni | Ispezione dell'intonaco di calce, stuccatura fessure | $100–300 per edificio |
| Ogni 30–40 anni | Ispezione impianto elettrico, sostituzione cavi se necessario | $200–500 per edificio |
| A 40 anni | Ispezione del telaio in acciaio nei punti accessibili (ri-zincatura puntuale se necessario) | $200–400 |
| **Totale sulla vita utile** | | **$1.400–2.000** |

## Test Necessari

**Tutti i valori di capacità di carico sopra riportati sono stime analitiche.** Saranno validati attraverso test fisici come parte dello sviluppo di questo progetto. I primi pannelli saranno costruiti e testati prima che qualsiasi edificio venga occupato.

Programma di test pianificato:

- [ ] **Test di taglio orizzontale** (ASTM E564 o equivalente) — pannelli con e senza diagonali, per validare la stima di miglioramento di 3–5 volte
- [ ] **Test di carico fuori piano** — pressione uniforme e impatto puntuale, per validare il beneficio del profilo )(
- [ ] **Test di resistenza al fuoco** (ASTM E119 o equivalente) — tempo alla rottura strutturale
- [ ] **Test sismici ciclici** — tavola vibrante a scala reale o carico ciclico quasi-statico, per verificare la modalità di rottura duttile
- [ ] **Test delle connessioni** — capacità dell'aletta imbullonata pannello-pilastro, durabilità del connettore a scatto
- [ ] **Test di invecchiamento accelerato** — invecchiamento accelerato di campioni di bambù inglobato nella malta
- [ ] **Test di trasmissione acustica** (ASTM E90) — misura STC
- [ ] **Test di estrazione carichi puntuali** — capacità di tasselli da muratura e bulloni passanti in malta + angolare L

I risultati dei test saranno pubblicati in questo repository man mano che diventano disponibili. Se avete accesso a strutture di test e volete contribuire, fatevi vivo — test collaborativi con diverse specie di bambù e miscele di malta renderanno questo sistema più robusto per tutti.
