jreuteler/bahareque-modular/it/09-stima-costi.md

# Stima dei Costi

> **Avvertenza:** Queste sono stime dei soli costi dei materiali, basate sui prezzi 2025 in Colombia (regione dell'Eje Cafetero). La manodopera non è inclusa — il sistema è progettato per la produzione comunitaria dove il lavoro è contribuito, non acquistato. I prezzi variano significativamente per regione, valuta e catena di approvvigionamento. Usare questi dati come punto di partenza, non come budget.

In questo progetto sono documentate due specifiche di miscela di malta: la **miscela base** (malta cemento-sabbia + 30 % di guadua + intonaco di calce 10 mm su entrambi i lati) e la **miscela bahareque ottimizzata** (calce pozzolanica + fibre pasto estrella + 30 % guadua + intonaco di calce 5 mm).

## Costo per Pannello — miscela base (solo materiali)

| Materiale | Specifica | Qtà per pannello | Costo unitario (USD) | Totale (USD) |
|---|---|---|---|---|
| Acciaio angolare L | L 40×40×4 mm, ASTM A36 | 7,0 m | $4,00/m | $28,00 |
| Zincatura | A caldo, processo a lotti | 1 telaio | $2,00 | $2,00 |
| Barre di serraggio | Piatto 40×3 mm, zinc. | 4,0 m | $1,00/m | $4,00 |
| Cartelle d'angolo + bulloneria | Piatto + M12/M8 | 1 set | $3,00 | $3,00 |
| Viti inox | Autoperforanti, A2 | 40 pz | $0,08 | $3,20 |
| Distanziatori HDPE | Riciclati, 30×30 mm | 2,0 m | $1,50/m | $3,00 |
| Listelli bambù (verticali + orizzontali, 30 % densità cavità) | Guadua trattata con borato | ~400 m totali | $0,05/m | $20,00 |
| Listelli bambù (diagonali) | 60×20 mm, trattato | ~5,4 m | $0,30/m | $1,60 |
| Legature in filo | Zincato | 5 m | $0,10/m | $0,50 |
| Tubazione PVC | Elettrica 16 mm | 5 m | $0,30/m | $1,50 |
| Cavo 12V + portalampada | Bipolare + 6× E10 | 1 set | $3,00 | $3,00 |
| Cavo 120V + connettori | Tripolare + connettori a scatto | 1 set | $4,00 | $4,00 |
| Rete a maglia esagonale | Zincata, 25 mm | 5,5 m² | $0,80/m² | $4,40 |
| Cemento | Portland Tipo I | ~54 kg | $0,15/kg | $8,10 |
| Sabbia (malta) | Sabbia di fiume pulita | ~240 kg | $0,02/kg | $4,80 |
| Fibra PP | Tagliata 6–12 mm | 200 g | $5,00/kg | $1,00 |
| Aggiunta pozzolanica | Cenere vulcanica o RHA | 2 kg | $0,50/kg | $1,00 |
| **Subtotale pannello — base** | | | | **~$93** |

### Finitura in cantiere, base (per area di pannello)

| Materiale | Qtà per pannello | Costo (USD) |
|---|---|---|
| Intonaco di calce (10 mm su ciascuna faccia) | ~25 kg calce + ~65 kg sabbia | $6,50 |
| Latte di calce (entrambe le facce) | ~2 kg calce | $0,50 |
| **Subtotale finitura — base** | | **$7,00** |

### **Costo totale materiali per pannello — base: ~$100 USD**

### Costo per m² di parete finita — base

- Area del pannello: 1,0 m × 2,5 m = 2,5 m²
- Costo dei materiali per m²: **~$40 USD/m²**

## Costo per Pannello — miscela bahareque ottimizzata (solo materiali)

La miscela ottimizzata sostituisce la malta cemento Portland-sabbia con calce idraulica + pozzolana, sostituisce la fibra PP con pasto estrella (gratis, raccolto in loco) e usa intonaco di calce più sottile da 5 mm. Stesso telaio in angolare L, stesso contenuto di bambù, stessi componenti elettrici e strutturali.

| Materiale | Specifica | Qtà per pannello | Costo unitario (USD) | Totale (USD) |
|---|---|---|---|---|
| Acciaio angolare L + zincatura + barre di serraggio + cartelle | (come base) | | | $37,20 |
| Viti inox, HDPE, bambù, legature, tubazione, cavi, rete | (come base) | | | $41,20 |
| Calce idraulica (legante principale) | NHL 3.5 o NHL 5 | ~42 kg | $0,30/kg | $12,60 |
| Cenere volante o di lolla di riso (pozzolana, 30 % equivalente cemento) | FA o RHA | ~15 kg | $0,10/kg | $1,50 |
| Sabbia (malta) | Sabbia di fiume pulita | ~200 kg | $0,02/kg | $4,00 |
| Fibra di pasto estrella (essiccata) | Raccolta in loco | ~3 kg | gratis | $0,00 |
| **Subtotale pannello — ottimizzato** | | | | **~$96** |

### Finitura in cantiere, ottimizzato (per area di pannello)

| Materiale | Qtà per pannello | Costo (USD) |
|---|---|---|
| Intonaco di calce (5 mm su ciascuna faccia) | ~12 kg calce + ~33 kg sabbia | $3,30 |
| Latte di calce (entrambe le facce) | ~2 kg calce | $0,50 |
| **Subtotale finitura — ottimizzato** | | **$3,80** |

### **Costo totale materiali per pannello — ottimizzato: ~$100 USD**

### Costo per m² di parete finita — ottimizzato

- Costo dei materiali per m²: **~$40 USD/m²**

> **Le due miscele costano circa lo stesso in materiali** (~$100/pannello, ~$40/m²). La miscela ottimizzata scambia ingredienti calce/pozzolana leggermente più costosi (vs. cemento Portland più economico) per intonaco di calce meno costoso (più sottile), zero costo di fibra PP, e CO₂ incorporata sostanzialmente inferiore (vedi [Impatto Ambientale](10-impatto-ambientale.md)). La miscela ottimizzata è quindi un **chiaro vantaggio in carbonio e autenticità patrimoniale a costo praticamente uguale**.

## Confronto con l'Edilizia Convenzionale

| Sistema murario | Costo materiali per m² (USD) | Durata | Note |
|---|---|---|---|
| **Questo sistema a pannelli** | **$26–28** | **80–100 anni** | Include struttura, impianto elettrico, finitura |
| Blocchi di cemento (15 cm) | $25–35 | 40–60 anni | Richiede armatura, getto, intonaco, pittura, impianto elettrico separato |
| Mattone cotto | $30–45 | 60–80 anni | Richiede malta, intonaco, pittura, impianto elettrico separato |
| Cartongesso su montanti in acciaio | $20–30 | 20–30 anni | Nessuna massa termica, non portante, richiede pittura, impianto elettrico separato |
| Bahareque convenzionale (in opera) | $15–25 | 15–30 anni | Nessun impianto elettrico, qualità della finitura variabile, breve durata senza ingegnerizzazione |
| Blocco in adobe | $10–20 | 20–40 anni | Scarse prestazioni sismiche, nessun impianto elettrico, richiede pareti spesse |

**Punto chiave:** Il sistema a pannelli costa circa come i blocchi di cemento al m² — ma include impianto elettrico integrato, ha il doppio della durata, offre migliori prestazioni termiche e acustiche e produce una finitura superiore. Considerando il costo dell'impianto elettrico separato di una casa in blocchi di cemento, il sistema a pannelli è più economico.

## Costo per Casa (stima indicativa)

Una semplice casa monopiano con soppalco (50 m² di impronta, ~70 m² abitabili incluso il soppalco):

| Componente | Quantità | Costo (USD) |
|---|---|---|
| Pannelli di parete | ~40 pannelli (100 m² di parete) | $2.600–2.800 |
| Fondazione (calcestruzzo, armatura) | ~5 m³ di calcestruzzo | $800–1.200 |
| Trave di coronamento (legno/bambù) | ~30 m | $200–400 |
| Tetto (tegole in cotto + arcarecci) | ~65 m² | $1.200–1.800 |
| Pavimento (soletta in cls o terra battuta) | ~50 m² | $400–800 |
| Finestre + porte | ~8 aperture | $600–1.200 |
| Quadro elettrico + trasformatore | 1 set | $200–400 |
| Impianto idraulico (base) | Cucina + bagno | $300–600 |
| **Totale materiali** | | **$6.300–9.200** |

Questo comprende solo i materiali. In un modello di costruzione comunitaria, la manodopera è contribuita. In un modello con impresa, aggiungere il 40–60% per la manodopera.

**Per contesto:** Una casa comparabile in blocchi di cemento nella Colombia rurale costa $12.000–20.000 (materiali + manodopera) e dura 40–60 anni. Questo sistema raggiunge una qualità simile o migliore a circa la metà del costo con il doppio della durata.

## Strategie di Riduzione dei Costi

| Strategia | Risparmio | Note |
|---|---|---|
| Raccogliere il proprio bambù | 30–40% del costo del bambù | Richiede 1+ ettari di bambuseto, maturità 4–5 anni |
| Riciclare HDPE dai rifiuti | 100% del costo HDPE | Taglieri, ritagli di tubi, scarti industriali |
| Usare cenere vulcanica (gratuita) | 100% del costo della pozzolana | Disponibile nelle regioni andine, raccogliere e setacciare |
| Usare fibra di erba stella invece di PP | 100% del costo della fibra | Erba invasiva, gratuita, uso circolare |
| Zincatura a lotti (50+ telai) | 15–20% del costo di zincatura | Sconto quantità dall'impianto di zincatura |
| Cava di sabbia comunitaria | 50–80% del costo della sabbia | Se disponibile accesso locale alla sabbia di fiume |
| Produrre la propria calce dal calcare | 50–70% del costo della calce | Richiede forno (costruzione una tantum), calcare locale |

## Variazioni Regionali dei Prezzi

I costi dei materiali variano drasticamente per regione. Le stime sopra sono per la Colombia. Moltiplicatori indicativi:

| Regione | Moltiplicatore | Note |
|---|---|---|
| Colombia (Eje Cafetero) | 1,0× (riferimento) | Guadua abbondante, cenere vulcanica disponibile |
| Ecuador, Perù | 0,8–1,1× | Materiali simili, caña guadua disponibile |
| America Centrale | 1,0–1,3× | Bambù disponibile, acciaio può costare di più |
| Filippine, Indonesia | 0,7–1,0× | Bambù abbondante e economico, manodopera molto bassa |
| India | 0,6–0,9× | Bambù e manodopera molto bassi, acciaio accessibile |
| Africa subsahariana | 0,8–1,2× | Specie di bambù variabili, cemento può essere costoso |
| Europa meridionale | 2,0–3,0× | Materiali disponibili ma più costosi |

Questi moltiplicatori sono indicazioni approssimative. La singola variabile più importante è il costo del bambù — se lo coltivate voi stessi, è quasi gratuito.
