jreuteler/bahareque-modular/it/10-impatto-ambientale.md

# Impatto Ambientale

## Impronta di Carbonio per Pannello — miscela base

I valori sotto riflettono la specifica base attuale: telaio acciaio L 40×40×4 + 30 % di guadua nella cavità + malta cemento-sabbia (base) + intonaco di calce 10 mm su entrambi i lati. Vedere [Anatomia del Pannello](02-anatomia-del-pannello.md) e [Materiali](03-materiali.md) per i dettagli.

| Materiale | Qtà per pannello | CO₂ incorporata (kg) | Fonte dell'emissione |
|---|---|---|---|
| Cemento Portland (~18 % della massa di malta) | ~54 kg | 43,2 | Calcinazione + combustibile del forno (~0,8 kg CO₂/kg cemento) |
| Telaio acciaio angolare L + barre di serraggio | ~22 kg acciaio | 39,6 | Produzione dell'acciaio (~1,8 kg CO₂/kg acciaio) |
| Zincatura (zinco) | ~0,7 kg zinco | 2,8 | Fusione dello zinco (~4 kg CO₂/kg zinco) |
| Sabbia (~82 % della massa di malta) | ~240 kg | 1,2 | Estrazione + trasporto |
| Rete a maglia esagonale + rete in alluminio | ~2 kg | 3,6 | Produzione filo d'acciaio |
| Tubazione PVC | ~0,3 kg | 0,6 | Produzione PVC (~2 kg CO₂/kg) |
| Cavi + connettori | ~0,5 kg | 1,5 | Rame + plastica |
| Distanziatori HDPE | ~0,5 kg | 0,5 | Se riciclato: ~1 kg CO₂/kg (contro 3 per vergine) |
| Calce (in intonaco, calcinazione) | ~22 kg calce | 18,0 | Calcinazione del calcare (~0,8 kg CO₂/kg calce) |
| Fibra PP (additivo malta) | ~0,2 kg | 0,4 | Produzione polipropilene |
| **Subtotale emissioni** | | **~111 kg CO₂** | |
| Bambù (carbonio sequestrato durante la crescita) | ~38 kg peso secco (30 % cavità) | **−60 a −75 kg CO₂** | Il bambù sequestra ~1,6–2,0 kg CO₂ per kg di massa secca |
| Intonaco di calce (riassorbe CO₂ durante la carbonatazione) | ~22 kg calce | **−6 a −9 kg CO₂** | La carbonatazione della calce ricattura ~30–50 % della CO₂ di calcinazione nel corso di decenni |
| **CO₂ netta per pannello, miscela base** | | **~30–45 kg CO₂** | |
| **CO₂ netta per m² di parete, base** | | **~12–18 kg CO₂/m²** | |

## Impronta di Carbonio per Pannello — miscela bahareque ottimizzata

La miscela ottimizzata (calce pozzolanica + pasto estrella + 30 % guadua + intonaco 5 mm) riduce il carbonio incorporato attraverso più leve cumulative:

| Leva | Delta CO₂ per pannello vs base |
|---|---|
| Sostituire 30 % del cemento con cenere volante o RHA | −10 a −13 kg |
| Sostituire malta cemento Portland con calce idraulica + pozzolana | −8 a −12 kg |
| Sostituire fibra PP con pasto estrella | −0,5 kg |
| Intonaco di calce 5 mm su entrambi i lati (−50 % volume calce) | −9 kg di calcinazione, +4 kg di minore recupero da carbonatazione = **−5 kg netto** |
| **Riduzione totale** | **−24 a −30 kg CO₂ per pannello** |
| **CO₂ netta per pannello, miscela ottimizzata** | **~6 a 20 kg CO₂** |
| **CO₂ netta per m² di parete, ottimizzata** | **~3 a 8 kg CO₂/m²** |

Con pozzolane disponibili localmente (cenere vulcanica nella regione caffè colombiana, cenere di lolla di riso da Tolima/Valle del Cauca) e fibra di pasto estrella dalla proprietà stessa, la miscela bahareque ottimizzata si avvicina a **carbonio-neutra** per pannello. Se il bambuseto è gestito come pozzo di carbonio (rotazione con permanenza della biomassa), il sistema diventa **carbonio-negativo**: la parete assorbe più CO₂ nella sua vita di quanto ne sia stato emesso per costruirla.

## Confronto con Sistemi Murari Convenzionali

| Sistema murario | kg CO₂ per m² | Rapporto vs pannello base |
|---|---|---|
| **Questo sistema a pannelli — miscela base** | **12–18** | **1× (riferimento)** |
| **Questo sistema a pannelli — miscela bahareque ottimizzata** | **3–8** | **~0,4× base** |
| Blocchi di cemento (15 cm, intonacati) | 40–60 | 3–4× base |
| Mattone in argilla cotto (intonacato) | 50–80 | 3–5× base |
| Parete in calcestruzzo armato (15 cm) | 70–100 | 5–7× base |
| Cartongesso su montanti in acciaio | 15–25 | 1–1,5× base |
| Bahareque convenzionale (intonaco di fango, senza telaio acciaio) | 3–8 | 0,3–0,5× base |
| Blocco in adobe | 5–10 | 0,4–0,7× base |

La miscela base del sistema a pannelli produce **~3 volte meno CO₂ rispetto ai blocchi di cemento o ai mattoni** — i due materiali murari più comuni nel mondo in via di sviluppo. La miscela bahareque ottimizzata si avvicina ai livelli dell'edilizia tradizionale in terra fornendo prestazioni strutturali e durata enormemente superiori.

## Carbonio per Anno di Servizio

Quando si considera la durata, il confronto diventa ancora più netto:

| Sistema murario | kg CO₂/m² | Durata (anni) | kg CO₂/m²/anno |
|---|---|---|---|
| **Questo sistema a pannelli** | 8 | 90 | **0,09** |
| Blocchi di cemento | 50 | 50 | 1,00 |
| Mattone cotto | 65 | 70 | 0,93 |
| Cartongesso su montanti in acciaio | 20 | 25 | 0,80 |
| Bahareque convenzionale | 5 | 20 | 0,25 |

**Nell'arco della sua vita utile, questo sistema a pannelli produce ~10 volte meno carbonio per anno di servizio rispetto ai blocchi di cemento.**

## Percorso verso la Neutralità o la Negatività Carbonica

Il sistema a pannelli è già a basso impatto carbonico. Con le seguenti sostituzioni, si avvicina alla neutralità carbonica:

| Sostituzione | CO₂ risparmiata per pannello | Fattibilità |
|---|---|---|
| Sostituire il 50% del cemento con pozzolana (cenere vulcanica, RHA) | −10 kg | Disponibile in regioni vulcaniche e risicole |
| Usare acciaio riciclato (forno ad arco elettrico) | −7 kg | Dipende dalla catena di approvvigionamento locale dell'acciaio |
| Sostituire la fibra PP con erba stella | −0,5 kg | Disponibile ovunque cresca l'erba |
| Aumentare il contenuto di bambù (listelli più spessi, più diagonali) | −3 a −5 kg di sequestro aggiuntivo | Il materiale è gratuito/economico |
| Usare calce biologica (forno a legna con combustibile da ceduo) | −3 kg | Metodo tradizionale di produzione della calce |
| **Riduzione potenziale totale** | **−20 a −25 kg** | |

Con queste sostituzioni, la CO₂ netta per pannello scende a **~0–5 kg** — effettivamente neutro in termini di carbonio. Se il contenuto di bambù viene ulteriormente aumentato o il bambuseto viene gestito come pozzo di carbonio, il sistema diventa **carbonio-negativo**: la parete assorbe più CO₂ durante la sua vita di quanta ne sia stata emessa per costruirla.

## Consumo d'Acqua

- **Miscelazione malta:** ~15–20 litri per pannello (acqua di stagionatura riutilizzata dove possibile)
- **Stagionatura:** ~50 litri in 7 giorni (metodo a nebulizzazione/tela di juta)
- **Miscelazione intonaco di calce:** ~10 litri per pannello
- **Totale:** ~75–80 litri per pannello, ovvero ~30 litri per m² di parete

Per confronto: la produzione di blocchi di cemento usa ~40–50 litri per m² di parete. La produzione di mattoni cotti usa ~100+ litri per m² (incluso il raffreddamento del forno).

## Rifiuti

- **Ritagli di acciaio:** Riciclati (valore come rottame)
- **Ritagli di bambù:** Compostati o usati come tutori da giardino/pacciamatura
- **Scarti di malta:** Minimi — il getto su tavolo vibrante è preciso. Eventuali eccedenze vengono riutilizzate nel pannello successivo.
- **Letto di sabbia:** Riutilizzato indefinitamente (la sabbia non viene consumata, solo compressa e smossa)
- **Ritagli di HDPE:** Riciclati o riutilizzati per blocchi più piccoli
- **Rifiuti di imballaggio:** Minimi — la maggior parte dei materiali arriva sfusa

Il sistema produce **rifiuti di costruzione quasi nulli**. Questa è una conseguenza diretta della prefabbricazione in laboratorio — ogni taglio è pianificato, ogni materiale è misurato.

## Fine Vita (dopo 80–100 anni)

Quando un pannello raggiunge eventualmente la fine della sua vita:

| Materiale | Smaltimento | Impatto ambientale |
|---|---|---|
| Telaio in acciaio | Riciclo (100% riciclabile) | Positivo — l'acciaio da rottame ha valore |
| Malta + bambù | Frantumare e usare come aggregato o riempimento | Inerte — la malta è calcio/silice/sabbia, il bambù è organico |
| Intonaco di calce | Ritorna a carbonato di calcio (calcare) | Neutro in carbonio — la CO₂ assorbita durante la carbonatazione viene rilasciata, bilancio netto zero |
| Distanziatori HDPE | Riciclo | Riciclabile |
| Cavi in rame | Riciclo (alto valore come rottame) | Positivo |
| Tubazione PVC | Riciclo dove esistono gli impianti | Riciclabile in principio |

**Nessun rifiuto pericoloso.** Nessun amianto, nessuna vernice al piombo, nessuna schiuma isolante sintetica, nessun legno trattato con sostanze chimiche. Il pannello è fatto di acciaio, bambù, sabbia, cemento e calce — ritorna alla terra o al flusso del riciclo in modo pulito.
