jreuteler/bahareque-modular/it/11-trasporto-movimentazione.md

# Trasporto e Movimentazione

## Specifiche del Pannello per la Movimentazione

| Proprietà | Valore |
|---|---|
| Dimensioni | 1,0 m × 2,5 m × 85 mm |
| Peso dell'assemblaggio a secco (così come spedito in cantiere) | **~75 kg** |
| Peso del pannello finito (miscela base, dopo getto in opera + stagionatura + intonaco) | ~440 kg |
| Peso del pannello finito (miscela bahareque ottimizzata) | ~360 kg |
| Baricentro | Centro (costruzione simmetrica) |
| Zone fragili | Angoli, bordi (la malta può scheggiarsi una volta gettata in caso di impatto) |
| Stagionatura minima prima della movimentazione | 7 giorni dopo il getto in opera |
| Stagionatura minima prima dell'installazione | 14 giorni raccomandati — nota: nel modello di getto in opera il pannello è eretto e la malta gettata sul posto, quindi «installazione» e «getto» avvengono insieme in cantiere |

## Modello di Produzione Primario: Getto in Opera

**Il modello di produzione primario consiste nello spedire l'assemblaggio a secco (~75 kg) in cantiere e gettare la malta in opera contro casseforme.** Il pannello finito da ~440 kg non viene mai spostato come unità — diventa direttamente parte della parete dell'edificio, risparmiando i costi di mezzi di sollevamento pesanti ed eliminando il rischio di fessurazione da trasporto. Vedere [Processo Costruttivo](04-processo-costruttivo.md) per il protocollo di getto verticale in opera.

La movimentazione di pannelli stagionati (sezioni seguenti) si applica al modello alternativo: getto della malta in laboratorio su tavolo vibrante, con pannelli totalmente stagionati spediti in cantiere come elementi finiti. Quest'approccio è mantenuto come opzione documentata per chi preferisce la produzione in laboratorio, ma aggiunge significativi costi di sollevamento, trasporto e tasso di scarto.

## Trasporto a Mano — assemblaggio a secco (~75 kg)

L'assemblaggio a secco (telaio acciaio angolare L + esterilla di bambù + rete + impianti, prima della malta) viene sollevato e posizionato da **2 persone con una semplice cinghia**. Nessuna dima di trasporto, nessuna gru, nessun muletto necessario — è uno dei vantaggi operativi centrali del modello di produzione con getto in opera.

### Cinghia singola (assemblaggio a secco)

1. Avvolgere una singola cinghia (50 mm × portata 500+ kg) attorno al pannello a metà altezza (~125 cm dal basso)
2. Ogni portatore afferra un'estremità della cinghia con entrambe le mani, sui lati lunghi opposti del pannello
3. Sollevare insieme; il pannello pende verticalmente tra loro
4. Camminare a passo normale; il pannello può essere portato 30–50 m prima di una pausa

**Peso per persona: ~38 kg** — completamente gestibile per i trasporti brevi tipici del laboratorio-camion, camion-deposito-cantiere e deposito-installazione.

## Trasporto a Mano — pannello finito stagionato (modello laboratorio alternativo)

Un pannello finito a ~360–440 kg **non può essere portato a mano**. Richiede sollevamento meccanico (paranco a catena, mini-pala o piccola gru mobile). Questo è il motivo principale per cui il modello di getto in opera è preferito.

Se i pannelli gettati in laboratorio devono essere spostati (ad es. produzione in fase pilota prima della validazione del protocollo in opera), usare:

### Dima di Trasporto (pannello stagionato, ~360–440 kg)

Due pali di bambù (3 m di lunghezza, 8–10 cm di diametro) infilati in asole di cinghia pesante avvolte attorno al pannello a 1/4 e 3/4 dell'altezza:

1. Stendere il pannello in piano
2. Avvolgere due cinghie (50 mm di larghezza, portata 1 000+ kg) attorno al pannello a ~60 cm e ~190 cm dal basso
3. Infilare un palo di bambù nelle due asole delle cinghie su ogni lato
4. **4 persone per palo, 8 portatori in totale** per un pannello miscela base a ~440 kg, oppure 6 portatori per un pannello miscela ottimizzata a ~360 kg
5. Il pannello pende verticalmente tra i pali

**Peso per persona: ~55 kg (base) / ~45 kg (ottimizzato)** — al limite superiore della movimentazione manuale sicura. Per lunghe distanze o scale, usare invece sollevamento meccanico.

### Sollevamento e Ribaltamento

- **Non sollevare mai un pannello da un solo bordo** — la malta può fessurarsi sotto il proprio peso se a sbalzo
- **Sollevare sempre da due punti** simmetrici, o dal basso con il retro appoggiato
- **Ribaltamento da orizzontale a verticale:** Due persone reggono il bordo superiore, due persone sollevano il fondo. Ruotare lentamente. Appoggiare il fondo su un blocco imbottito durante la rotazione.

## Stoccaggio in Laboratorio

Dopo la stagionatura, i pannelli vengono stoccati **verticalmente (di taglio)** in una rastrelliera a cavalletto:

- Appoggiare i pannelli su entrambi i lati di un telaio inclinato (come un libro aperto)
- 10–15 pannelli per lato della rastrelliera
- Separare i pannelli con piccoli distanziatori in legno per consentire la circolazione dell'aria
- Coprire con telo o tetto per proteggere dalla pioggia diretta (la malta in stagionatura può essere dilavata da pioggia forte prima della presa completa)
- Tenere sollevati da terra — appoggiare il bordo inferiore su ghiaia o guida in legno

**Spazio necessario:** ~3 m × 1 m di superficie a terra per 20–30 pannelli stoccati.

## Trasporto su Camion

### Caricamento

1. Posizionare i pannelli verticalmente nel cassone del camion, appoggiati a una parete laterale
2. Mettere distanziatori in legno (ritagli, bambù o schiuma) tra ogni pannello
3. Fissare i pannelli alla parete laterale del camion con cinghie a cricchetto a 1/3 e 2/3 dell'altezza
4. Non impilare mai i pannelli in piano uno sull'altro — il pannello inferiore si fessurerà sotto il peso della pila
5. Massimo ~15–20 pannelli per pickup standard (a seconda della capacità del camion e delle condizioni stradali)

### Considerazioni Stradali

- **Strade asfaltate:** Nessuna precauzione speciale oltre al fissaggio
- **Strade sterrate/accidentate:** Ridurre la velocità. Aggiungere imbottitura in schiuma o cartone tra i pannelli. Fissare saldamente — i pannelli possono spostarsi e scheggiarsi ai bordi sulle buche.
- **Pendenze ripide:** Assicurarsi che i pannelli si appoggino verso la salita (non verso il vuoto) per prevenire il ribaltamento
- **Distanza:** Nessun limite. I pannelli sono completamente stagionati e autonomi. Possono viaggiare qualsiasi distanza.

### Scaricamento

1. Rimuovere le cinghie dall'alto verso il basso
2. Due persone per pannello — una al bordo superiore, una a sostenere il fondo
3. Portare ogni pannello alla rastrelliera di stoccaggio in cantiere
4. Non far mai cadere o trascinare i pannelli — i bordi di malta si scheggiano facilmente

## Gru / Paranco (per i piani superiori)

Per edifici a due piani, i pannelli devono essere sollevati al secondo piano:

- **Semplice palo di sollevamento:** Un palo di bambù o acciaio con corda e puleggia. Due persone tirano la corda, una guida il pannello. Funziona per piccoli volumi.
- **Paranco a catena su trave:** Fissare un paranco a catena da 500 kg alla trave in acciaio dell'edificio. Agganciare alla cinghia di trasporto del pannello. Una persona manovra, una guida. Veloce e controllato.
- **Carrello elevatore (se disponibile):** Forche sotto il pannello (protetto con cartone). Sollevare e posizionare direttamente in posizione.

**Non lanciare, rotolare o trascinare i pannelli.** La malta è resistente a compressione ma può fessurarsi per impatto puntuale.

## Danni e Riparazioni

| Tipo di danno | Causa | Riparazione |
|---|---|---|
| Scheggiatura angolo (piccola) | Impatto durante il trasporto | Riempire con malta, intonacare sopra. Solo estetico. |
| Fessura al bordo (superficiale) | Urto durante la movimentazione | Riempire con intonaco di calce. Non influisce sulla struttura. |
| Fessura passante (malta) | Caduta o impatto severo | Pannello potenzialmente compromesso. Valutare: se il telaio in acciaio è intatto e la fessura è <2 mm, riempire con malta e monitorare. Se la fessura è >5 mm o il telaio è piegato, scartare il pannello. |
| Connettore a scatto rotto | Impigliato durante il trasporto | Sostituire il connettore (saldato a stagno o crimpato). |

**Tasso di scarto:** Con ragionevole cura, aspettarsi <5% dei pannelli con danni durante trasporto e movimentazione, e <1% che richiedano lo scarto. I pannelli scartati possono essere privati dei componenti elettrici e riciclati come materiale di riempimento.

## Lista di Controllo Prima del Trasporto

- [ ] Pannello stagionato almeno 7 giorni (14 raccomandati)
- [ ] Pannello marcato con tipo (P/O/S/W) e data di produzione
- [ ] Circuiti elettrici testati (verifica continuità 12V + 120V)
- [ ] Nessuna fessura visibile >1 mm
- [ ] Angoli integri
- [ ] Cinghie di trasporto o dima preparate
- [ ] Cassone del camion pulito, distanziatori pronti, cinghie disponibili
- [ ] Percorso verificato per le condizioni stradali (ponti, altezze di passaggio, pendenze)
