jreuteler/bahareque-modular/it/14-miglioramento-acustico.md

# Miglioramento acustico — Pareti esposte al rumore

> *Questo capitolo è stato ispirato da un suggerimento di Kim Hansson — grazie per aver spinto il design ad affrontare le condizioni urbane reali.*

Il pannello standard (STC 40–45) è adeguato per zone residenziali tranquille. Per edifici su strade trafficate, vicino ad autostrade o adiacenti a zone commerciali/industriali, le pareti esposte al rumore possono essere migliorate singolarmente. Non è necessario migliorare ogni parete — la maggior parte degli edifici ha solo uno o due lati esposti a rumore significativo. Le pareti sul lato tranquillo rimangono con pannelli standard.

## Guida all'esposizione al rumore

| Situazione | Trattamento consigliato | STC obiettivo |
|---|---|---|
| Strada residenziale tranquilla | Pannello standard — nessun miglioramento necessario | 40–45 |
| Traffico stradale moderato | Malta densa + strato smorzante in argilla | 48–52 |
| Strada urbana trafficata, linee autobus | Doppio pannello con cavità in fibra | 55–62 |
| Autostrada, zona industriale, quartiere della vita notturna | Doppio pannello con cavità in fibra + strato di argilla | 58–65 |

**Applicare il miglioramento solo dove necessario.** Una casa tipica su una strada trafficata ha una o due pareti esposte al rumore (10–15 m²). Le pareti rimanenti affacciano su giardino, cortile o lato tranquillo e usano pannelli standard. Questo mantiene il sovracosto proporzionale al problema reale di rumore.

## Opzione 1: Miscela di malta più densa (la più economica, +3–5 STC)

La sabbia di fiume standard viene sostituita con aggregati più pesanti nella miscela di malta. Stesso processo produttivo, stesso telaio, stesso getto su tavola vibrante. Il pannello è semplicemente più pesante.

| Aggregato | Aumento di densità | Costo vs. sabbia standard | Disponibilità |
|---|---|---|---|
| Basalto frantumato o granito fine | +15–20% | Simile | Universale — qualsiasi cava |
| Scoria di ferro (*escoria*) | +25–30% | Spesso gratuita | Vicino ad acciaierie, fonderie |
| Sabbia magnetitica (*arena negra*) | +40% | Basso | Letti fluviali vulcanici (Ande, America Centrale) |

- **Peso del pannello:** finito ~490–530 kg miscela di base (vs. ~440 kg base standard) / ~405–440 kg miscela ottimizzata (vs. ~360 kg ottimizzata standard). Peso di assemblaggio a secco invariato a ~75 kg (l'aggregato denso viene aggiunto durante il getto in-situ, non durante l'assemblaggio in officina)
- **Costo aggiuntivo:** ~$1–2 per pannello
- **STC:** ~43–48
- **Modifica alla produzione:** Nessuna — si sostituisce solo l'aggregato. Il rapporto di miscela rimane 1:4 cemento:aggregato.

**Ideale per:** Pareti laterali che necessitano di un miglioramento modesto senza modificare lo spessore della parete o il processo costruttivo.

## Opzione 2: Strato smorzante in argilla (+5–8 STC)

Si aggiunge uno strato di 10–15 mm di **intonaco di argilla e paglia** sulla faccia interna della parete esposta al rumore, applicato in cantiere tra la superficie di malta e la finitura in intonaco di calce.

### Perché l'argilla funziona

L'argilla ha uno smorzamento acustico superiore rispetto alla malta cementizia. Quando le onde sonore colpiscono uno strato di argilla, più energia viene convertita in calore (attrito interno nelle particelle di argilla) anziché essere trasmessa attraverso la parete. Le fibre di paglia tritata nell'argilla aggiungono ulteriore attrito interno.

Questa è la tecnica bahareque più tradizionale — l'intonaco di argilla (*pañete de tierra*) è stato usato sulle pareti di bambù per secoli. Funziona acusticamente per la stessa ragione per cui funziona termicamente: l'argilla è un assorbitore naturale di energia.

### Applicazione

1. Preparare la miscela di argilla e paglia: argilla locale + erba secca o paglia tritata (pezzi da 5–10 cm), miscelati fino a ottenere una pasta densa
2. Applicare 10–15 mm sulla faccia interna della parete esposta al rumore, sopra la superficie di malta
3. Lasciare asciugare (3–7 giorni a seconda dell'umidità)
4. Applicare intonaco di calce (3–5 mm) sopra lo strato di argilla come finitura
5. Tinteggiatura a calce come di consueto

### Specifiche

- **Spessore totale della parete:** ~100 mm (vs. 85 mm standard)
- **Costo aggiuntivo:** ~$2–4 per area di pannello (l'argilla è normalmente gratuita — scavata durante i lavori di fondazione)
- **STC:** ~45–50
- **Modifica alla produzione:** Nessuna al pannello stesso. Lo strato di argilla viene applicato in cantiere dopo l'installazione.

**Ideale per:** Miglioramento a basso costo. Usa materiale locale gratuito. Nessuna modifica alla produzione del pannello. Migliora anche la regolazione dell'umidità.

## Opzione 3: Doppio pannello con cavità in fibra (migliore prestazione acustica, +15–20 STC)

Due pannelli standard con una cavità di 50–100 mm tra loro, riempita con fibra organica sciolta. Questa è l'opzione ad alte prestazioni per ambienti davvero rumorosi.

### Perché funziona

Si combinano tre principi acustici:

1. **Doppia massa** — due pareti in malta invece di una. La legge della massa dice che raddoppiare la massa aggiunge ~6 dB di riduzione sonora.
2. **Disaccoppiamento** — la cavità d'aria interrompe il percorso della vibrazione. Il suono si trasmette efficientemente attraverso i materiali solidi ma con difficoltà attraverso un'intercapedine d'aria. I due pannelli vibrano indipendentemente.
3. **Assorbimento** — la fibra sciolta nella cavità assorbe l'energia sonora che altrimenti rimbalzerebbe tra i due pannelli (risonanza a onda stazionaria).

### Materiali di riempimento della cavità

Usate ciò che è disponibile localmente ed economico. Il riempimento deve essere **sciolto, non compattato** — le sacche d'aria all'interno della fibra sono quelle che assorbono il suono.

| Materiale | Qualità acustica | Costo | Disponibilità regionale |
|---|---|---|---|
| **Lolla di riso** (*cascarilla de arroz*) | Eccellente | Gratis–$2/sacco | Regioni risicole (Asia, America Latina) |
| **Fibra di cocco** (*fibra de coco*) | Eccellente | $3–5/sacco | Regioni costiere tropicali |
| **Erba stella essiccata** (*pasto estrella*) | Buona | Gratis | Americhe tropicali (invasiva, rimossa dai campi) |
| **Trucioli di legno** (*viruta*) | Buona | Gratis–$1/sacco | Falegnamerie |
| **Ghiaia vulcanica sciolta** (*gravilla volcánica*) | Buona (per massa) | $2–3/sacco | Regioni vulcaniche (Ande, America Centrale, Sud-est asiatico) |
| **Fibra di foglia di banano essiccata** | Buona | Gratis | Regioni bananiere |

**La lolla di riso è la migliore opzione complessiva** dove disponibile: leggera, non si compatta nel tempo, naturalmente resistente al fuoco (alto contenuto di silice) ed estremamente economica o gratuita dalle riserie.

### Costruzione

1. Installare il pannello esterno come di consueto (imbullonato al telaio strutturale o cordolo perimetrale)
2. Lasciare uno spazio di 50–100 mm (definito da distanziali o colonna/staffa di montaggio più larga)
3. Riempire la cavità in modo sciolto con il materiale fibroso — non compattare
4. Installare il pannello interno, chiudendo la cavità
5. Entrambi i pannelli si imbullonano alla stessa struttura portante

La larghezza della cavità dipende dallo spazio disponibile e dalla prestazione desiderata:

| Larghezza cavità | Miglioramento STC | Spessore totale parete |
|---|---|---|
| 50 mm | +12–15 STC | ~220 mm |
| 75 mm | +15–18 STC | ~245 mm |
| 100 mm | +18–20 STC | ~270 mm |

### Specifiche

- **Spessore totale della parete:** 220–270 mm (vs. 85 mm standard)
- **Costo aggiuntivo:** ~$65–70 per m² (un pannello aggiuntivo) + $2–5 per riempimento cavità = ~$70–75 extra per m²
- **STC:** 55–62
- **Modifica alla produzione:** Nessuna — usa due pannelli standard

**Ideale per:** Fronti su strade trafficate, edifici adiacenti ad autostrade, camere da letto su strade rumorose, sale musicali, laboratori adiacenti a spazi abitativi.

## Opzioni combinate

Le opzioni si sommano. Per la massima prestazione acustica su una parete critica:

| Combinazione | STC | Costo extra/m² | Caso d'uso |
|---|-----|---|---|
| Pannello standard | 40–45 | Base | Lato tranquillo |
| Solo malta densa | 43–48 | +$1–2 | Rumore lieve, miglioramento più economico |
| Malta densa + strato di argilla | 48–52 | +$3–6 | Rumore stradale moderato, parete singola |
| Doppio pannello + cavità in fibra | 55–62 | +$70–75 | Strada trafficata |
| Doppio pannello (malta densa) + cavità in fibra + argilla interna | 58–65 | +$75–80 | Autostrada, industria, locale notturno accanto |

## Esempio tipico di edificio

Una casa a un piano su un angolo trafficato, con giardino su due lati:

| Parete | Affaccia su | Trattamento | STC | Costo extra |
|---|---|---|-----|---|
| Parete nord (10 m²) | Strada trafficata | Doppio pannello + lolla di riso | 55–60 | ~$700–750 |
| Parete est (6 m²) | Strada secondaria | Malta densa + strato di argilla | 48–52 | ~$20–36 |
| Parete sud (10 m²) | Giardino | Pannello standard | 42–45 | $0 |
| Parete ovest (6 m²) | Giardino del vicino | Pannello standard | 42–45 | $0 |
| **Costo extra totale** | | | | **~$720–790** |

Per ~$750, la parete più rumorosa ottiene un isolamento acustico di livello professionale mentre le pareti tranquille restano standard. Il miglioramento acustico aggiunge meno del 10% al costo totale della casa dal [preventivo di spesa](09-preventivo-spesa.md).

## Note sui materiali

### Sicurezza antincendio del riempimento della cavità

- **Lolla di riso:** Alto contenuto di silice, naturalmente resistente al fuoco. Non alimenta la fiamma. Si carbonizza ma si autoestingue.
- **Fibra di cocco:** Lenta ad accendersi, si autoestingue quando sciolta.
- **Erba/paglia secca:** Più infiammabile. Trattare con soluzione di borato (stesso trattamento del bambù) per la resistenza al fuoco se utilizzata nella cavità. La cavità è sigillata tra due pannelli di malta, quindi il rischio di innesco è comunque molto basso.
- **Ghiaia vulcanica:** Incombustibile.

### Umidità nella cavità

La cavità deve rimanere asciutta. Entrambi i pannelli sono sigillati con malta e intonacati a calce — l'umidità non dovrebbe entrare. Tuttavia:

- Non utilizzare il sistema a doppio pannello sotto il livello del terreno o in zone soggette ad allagamento
- Assicurarsi che la parte superiore della cavità sia sigillata (cordolo perimetrale o cappetta in malta)
- In climi estremamente umidi, lasciare piccole aperture di ventilazione nella parte superiore e inferiore della cavità (coperte con rete per impedire l'ingresso di insetti) per consentire la circolazione dell'aria

### Retrofit

Il miglioramento acustico può essere **aggiunto in seguito** a una parete esistente con pannello standard:

1. Costruire una seconda parete di pannelli 50–100 mm all'interno della parete esistente
2. Riempire la cavità con fibra
3. Lo spazio interno si riduce della larghezza della cavità + spessore del pannello (~135–185 mm per parete migliorata)

Questo permette di costruire con pannelli standard ora e migliorare pareti specifiche in seguito se il rumore diventa un problema — ad esempio, se una strada tranquilla diventa trafficata dopo un intervento di sviluppo urbano.
