jreuteler/bahareque-modular/pt/04-processo-construtivo.md

# Processo Construtivo

> **Atualização de SVG pendente:** alguns diagramas deste capítulo foram gerados para a especificação anterior de estrutura em cantoneira L e foram temporariamente desvinculados até serem regenerados para a especificação atual de **cantoneira L 40×40×4 mm**. Veja [`SVG-STATUS.md`](../SVG-STATUS.md) na raiz do repositório.

## Configuração da Oficina

Todos os painéis são construídos em uma oficina coberta — independente do clima, com controle de qualidade, eficiência de linha de montagem. Requisitos mínimos da oficina:

- Área coberta: ~6 × 4 m (telhado, laterais abertas aceitável)
- Estação de soldagem (apenas para fabricação das estruturas)
- Furadeira de bancada ou furadeira manual
- 2× mesas vibratórias (~1,2 × 2,7 m cada)
- Suprimento de areia para o leito
- Betoneira (elétrica ou manual)
- Ferramentas manuais básicas: chaves de fenda, alicates de corte, alicates, grampeador

Sequência de Montagem

## Etapas de Produção

### Etapa 1: Fabricação da Estrutura

1. Cortar a cantoneira L 40×40×4 no comprimento: 2× 1,0 m (superior/inferior) + 2× 2,5 m (laterais). Estoque comercial em barras de 6 m
2. Cortar os cantos em meia-esquadria a 45° (ou cortar reto com uma aba sobreposta à outra). Soldar em gabarito — todas as estruturas idênticas. Cartelas de canto opcionais para rigidez no manuseio
3. Furar os orifícios de fixação a cada ~70 mm ao longo das almas das cantoneiras L superior e inferior (um para cada duas tiras de bambu, ~14 furos por barra, ~28 no total)
4. Galvanizar a quente a estrutura completa (processo em lote — enviar 20–50 estruturas de uma vez)

**Todas as estruturas são idênticas independentemente da variante do painel.** O gabarito garante dimensões consistentes. Um gabarito, uma estrutura, para sempre.

### Etapa 2: Blocos de PEAD

1. Cortar o PEAD em peças de 30 × 30 mm × 1.000 mm (2 por painel)
2. Cortar entalhes nos cantos: 10 × 10 mm em cada extremidade (4 entalhes por bloco, 8 por painel)
3. Montar os blocos nas almas dos cantoneiras L superior e inferior usando parafusos ou adesivo

### Etapa 3: Instalação Elétrica

1. Passar o cabo 12V pelo eletroduto de PVC
2. Passar o cabo 120V por eletroduto de PVC separado
3. Montar os soquetes E10 (3 próximos ao topo, cada lado)
4. Para Tipo T: montar caixa de tomada, conectar rabicho ao cabo principal
5. Para Tipo I: montar caixa de interruptor a 120 cm de altura
6. Para Tipo H: montar tubulações de água (CPVC/PEX para abastecimento, PVC para esgoto) com esperas tamponadas
7. Fixar conectores rápidos em ambas as bordas verticais (2 pinos para 12V, 3 pinos para 120V)

### Etapa 4: Tiras de Bambu (Lado 1)

1. Colocar a estrutura do painel deitada na mesa de trabalho, lado 1 para cima
2. Dispor as tiras verticais de bambu contra a alma, entre os blocos de PEAD
3. Deixar ~20 mm de espaço entre tiras para penetração da argamassa
4. Colocar o eletroduto de PVC com cabos entre as tiras, contra a alma
5. Passar a tira diagonal pelo entalhe inferior esquerdo do PEAD, cruzando até o entalhe superior direito (no nível da alma)
6. Pré-tensionar a diagonal e fixar em ambas as extremidades

Sistema de Fixação por Parafusos

### Etapa 5: Fixação por Parafusos (Lado 1)

1. Colocar a tira de fixação de aço (2 mm × 30 mm × 1.000 mm) sobre as tiras de bambu no cantoneira L superior
2. Alinhar os furos da tira de fixação com os furos da alma do cantoneira L
3. Parafusar com parafusos de aço inoxidável através de: tira de fixação → tiras de bambu → furos da alma
4. A tira de fixação flexiona para acomodar a variação natural de espessura — autoajustável
5. Repetir no cantoneira L inferior
6. Amarrar a diagonal a cada tira vertical nos cruzamentos com arame (~8–10 amarrações)

**Tempo: ~5 minutos por lado para fixação, ~3 minutos para amarrações**

### Etapa 6: Virar e Repetir (Lado 2)

1. Virar o painel
2. Repetir as etapas 4–5 no outro lado
3. A diagonal do lado 2 vai do canto superior esquerdo ao inferior direito (oposta à diagonal do lado 1 — juntas formam um X)

### Etapa 7: Tela

1. Colocar tela de galinheiro sobre o lado 1, estendendo 20 mm além das bordas da estrutura (para sobreposição com painéis adjacentes)
2. Grampear ou amarrar com arame à estrutura e às tiras de bambu
3. Se usar tela de alumínio contra insetos: colocar sob a tela de galinheiro
4. Virar e repetir no lado 2

### Etapa 8: Vertimento da Argamassa

Processo de Vertimento da Argamassa

Esta é a inovação principal no método de aplicação:

1. **Preparar a mesa vibratória:** Superfície nivelada, motor montado embaixo
2. **Espalhar leito de areia:** ~30 mm de areia limpa e seca na superfície da mesa. A areia se acomoda a quaisquer irregularidades da face do painel e impede a aderência da argamassa à mesa.
3. **Colocar o painel com a face para baixo** sobre o leito de areia (lado da tela de galinheiro tocando a areia)
4. **Misturar a argamassa:** 1:4 cimento:areia + fibra de PP + aditivo pozolânico, A/C ~0,45–0,50 (consistência de vertimento mas não líquida)
5. **Verter argamassa** sobre a parte traseira exposta do painel, preenchendo entre as tiras e cobrindo a tela
6. **Ligar a vibração:** Operar a mesa por 30–60 segundos. A vibração:
   - Empurra a argamassa através dos espaços entre as tiras
   - Preenche completamente a cavidade central
   - Elimina vazios e bolsas de ar
   - A argamassa penetra até a tela da face frontal (agora apoiada sobre a areia)
7. **Nivelar** o excesso de argamassa rente às bordas da estrutura
8. **Alisar** com desempenadeira (isto se torna a face interna)

> **Guia de construção da mesa vibratória:** Um projeto de mesa vibratória DIY (motor, plataforma, molas) será publicado neste repositório assim que o projeto tiver sido testado e comprovado seguro na prática. Até lá, qualquer plataforma plana com um vibrador de concreto fixado na borda funcionará para experimentos iniciais.

**Por que mesa vibratória sobre leito de areia?**
- Gravidade + vibração = preenchimento completo, sem vazios
- Leito de areia = sem necessidade de forma, a areia se acomoda ao formato do painel
- Sem necessidade de equipamento de pulverização (mais barato que argamassa pulverizada)
- Vertimento por um lado preenche ambos os lados — a argamassa flui pelos espaços entre as tiras
- Qualidade consistente — a vibração elimina erro humano

### Etapa 9: Cura

1. Cobrir o painel com lona plástica para reter umidade
2. Manter úmido por no mínimo 7 dias (borrifação ou estopa úmida)
3. Resistência total em 28 dias
4. Os painéis podem ser empilhados verticalmente (de lado) após 7 dias para economizar espaço
5. Marcar cada painel com tipo de variante e data de produção

**Taxa de produção: 3–4 painéis por dia** com 2 mesas vibratórias operando em paralelo, equipe de 4–6 pessoas. Trabalho ativo por painel: ~15–20 minutos. Cura passiva: 7–28 dias (painéis curam enquanto novos são produzidos).

### Etapa 10: Transporte e Instalação

1. Transportar painéis ao canteiro usando carrinho de transporte tipo A ou caminhão
2. Parafusar painéis na estrutura metálica da edificação nas posições dos pilares (abas de fixação pré-soldadas nos pilares)
3. Painéis adjacentes encostam argamassa com argamassa
4. Conectar eletricamente entre painéis adjacentes (12V + 120V por conexão rápida)
5. Testar circuitos antes do acabamento

### Etapa 11: Acabamento no Local

1. Preencher quaisquer juntas entre painéis com argamassa
2. Aplicar tela de galinheiro sobre as juntas (se ainda não houver sobreposição das bordas dos painéis)
3. Aplicar reboco de cal: 3–5 mm, aplicado à mão, ambas as faces
4. Deixar curar (manter úmido por 3–5 dias)
5. Aplicar caiação: 2–3 demãos finas com broxa

A parede acabada é contínua — sem juntas visíveis, sem aço visível, sem parafusos visíveis. Apenas reboco de cal liso com a textura de uma parede feita à mão.

## Lista de Verificação de Qualidade

- [ ] Dimensões da estrutura dentro de ±2 mm
- [ ] Todos os furos de fixação perfurados e alinhados
- [ ] Tiras de bambu tratadas com borato (tonalidade verde/azulada visível)
- [ ] Diagonal pré-tensionada (deve ressoar quando batida)
- [ ] Todas as amarrações de arame apertadas
- [ ] Circuitos elétricos testados antes da argamassa (12V e 120V)
- [ ] Consistência da argamassa correta (teste de abatimento)
- [ ] Vibração operada por 30–60 segundos completos
- [ ] Sem vazios visíveis na face de vertimento após vibração
- [ ] Painel marcado com tipo e data
- [ ] Curado no mínimo 7 dias antes do manuseio
