jreuteler/bahareque-modular/pt/05-desempenho-estrutural.md

# Desempenho Estrutural

## Arquitetura do Sistema

Este sistema de painéis foi projetado para funcionar **com uma estrutura de aço pilar-viga** — a configuração que recomendamos para edificações de múltiplos pavimentos em zonas sísmicas. Nessa configuração, a estrutura de aço suporta cargas gravitacionais e sísmicas enquanto os painéis fornecem contraventamento lateral, fechamento contra intempéries, massa térmica e serviços integrados.

No entanto, os painéis são **estruturalmente capazes de funcionar sem uma estrutura de aço**. Com capacidade de compressão que excede amplamente as cargas residenciais típicas (dois montantes laterais em cantoneira L L 40×40×4), uma fileira de painéis pode confortavelmente suportar um segundo pavimento e telhado sem uma estrutura de aço independente. Uma viga de cintamento simples de madeira ou bambu no topo conecta os painéis e distribui a carga do telhado.

**Duas configurações:**

| Configuração | Caso de uso | Função do painel |
|---|---|---|
| **Com estrutura de aço** (recomendada) | Múltiplos pavimentos, zonas de alta sismicidade, comercial/institucional | Preenchimento — painéis são parafusados na estrutura, o aço suporta as cargas primárias |
| **Sem estrutura de aço** (mais simples, menor custo) | Térreo + mezanino, sismicidade moderada, residencial | Autoportante — painéis suportam o telhado e pavimento superior diretamente |

As estimativas de capacidade de carga abaixo se aplicam a ambas as configurações. A estrutura de aço adiciona redundância e resistência a momento, mas não é necessária para os painéis funcionarem estruturalmente.

## Desempenho Sísmico

### Contraventamento Diagonal

Cada painel contém duas tiras diagonais de bambu (uma por lado, cantos opostos), formando um X quando visto de frente. Sob carregamento sísmico:

1. **Conversão cisalhamento → tração:** Quando a estrutura da edificação se deforma lateralmente, uma diagonal entra em tração enquanto a oposta entra em compressão. A diagonal de bambu em tração resiste à força de deformação eficientemente — o bambu tem excelente resistência à tração (150–200 MPa para Guadua angustifolia).
2. **Pré-tensão:** As diagonais são instaladas com leve pré-tensão, eliminando folga e garantindo engajamento imediato sob carga.
3. **Grade de amarrações de arame:** Amarrações de arame galvanizado em cada cruzamento diagonal-vertical (~16–20 amarrações no total) distribuem a força diagonal por toda a face do painel, prevenindo falha localizada.

**Melhoria estimada: 3–5× na resistência ao esforço cortante** comparado a painéis sem contraventamento diagonal.

### O Perfil )(

Os blocos de PEAD mantêm as tiras de bambu a 30 mm da alma nas partes superior e inferior. Na meia-altura, as tiras flexionam para dentro em direção à alma. A argamassa preenche esse espaço variável, criando uma seção transversal natural em arco:

- **Resistência fora do plano:** O arco de argamassa funciona como uma abóbada rasa, distribuindo eficientemente cargas de vento ou impacto para as bordas rígidas da estrutura.
- **Travamento mecânico:** A argamassa de espessura variável trava as tiras de bambu no lugar — elas não podem ser arrancadas sem quebrar a argamassa.

### Modo de Falha Dúctil

A combinação de tiras de bambu, amarrações de arame e argamassa cria um compósito que falha gradualmente:

1. Primeiro: a argamassa fissura (aviso visível)
2. Depois: as amarrações de arame se esticam (absorção de energia)
3. Depois: as tiras de bambu se deformam (alta ductilidade)
4. A estrutura de aço permanece intacta durante todo o processo — a edificação não colapsa

Isso é fundamentalmente diferente da alvenaria sem reforço, que falha de forma frágil (colapso súbito sem aviso).

## Resistência ao Fogo

- **Encapsulamento em argamassa:** As tiras de bambu são totalmente encapsuladas em argamassa (~85 mm de espessura de parede). A argamassa é não combustível e funciona como isolamento térmico para o bambu.
- **Carbonização do bambu:** Mesmo que o fogo penetre a argamassa, o bambu carboniza lenta e previsivelmente (similar à construção em madeira). A estrutura de aço por trás mantém a integridade estrutural.
- **Acabamento de reboco de cal:** Não combustível. Proporciona proteção adicional contra fogo.
- **Nenhum bambu exposto:** Uma vez instalado e acabado, nenhum bambu é visível ou acessível à chama.

## Desempenho Térmico

- **Massa térmica:** ~85 mm de argamassa proporcionam massa térmica significativa — absorve calor durante o dia, libera à noite. Reduz oscilações de temperatura em climas tropicais.
- **Respirabilidade:** O reboco de cal é permeável ao vapor. A umidade passa através da parede em vez de ficar presa, prevenindo condensação e mofo.
- **Sem camada de isolamento:** O sistema não inclui uma camada de isolamento térmico. Em climas tropicais (o alvo principal), a massa térmica é mais valiosa que o isolamento. Para climas temperados, uma camada de isolamento externo pode ser adicionada sobre o reboco de cal.

## Desempenho Acústico

O núcleo denso de argamassa proporciona boa atenuação sonora:

- **STC estimado (Classe de Transmissão Sonora):** 40–45 para uma parede de painel simples
- **Com reboco de cal em ambos os lados:** STC 42–48
- **Comparação:** Parede de bloco de concreto padrão: STC 40–45. O sistema de painéis é comparável.

## Capacidade de Carga

> **Aviso:** Os valores abaixo são estimativas analíticas conservadoras baseadas em propriedades dos materiais e geometria. NÃO são baseados em testes laboratoriais. Não utilize esses valores para engenharia estrutural sem verificação independente. O desempenho real depende da qualidade dos materiais, da mão de obra e dos detalhes de conexão. Veja [Testes Necessários](#testes-necessários) abaixo.

### Peso Próprio do Painel

| Componente | Peso |
|---|---|
| Estrutura de aço (cantoneira L 40×40×4, 7 m total a 2,42 kg/m + tiras de fixação + cartelas) | ~22 kg |
| Argamassa do núcleo (cavidade ~0,147 m³, curada, densidade ~2 000 kg/m³) | ~294 kg |
| Tiras de bambu + diagonais (~30 % cavidade) | ~38 kg |
| Blocos de PEAD, arame, tela, eletroduto, cabos | ~6 kg |
| Reboco de cal (10 mm em ambas as faces) | ~100 kg |
| **Peso total do painel, mistura base** | **~460 kg** |
| **Peso por m² de parede, base** | **~184 kg/m²** |
| Peso total do painel, mistura bahareque otimizada (cal pozolânica + capim-estrela + reboco 5 mm) | ~380 kg |
| Peso de envio da montagem a seco (estrutura + bambu + tela + instalações, antes do despejo) | ~75 kg |

Para comparação: parede de bloco de concreto de 150 mm ≈ 180 kg/m². O sistema de painéis (mistura base) pesa aproximadamente o mesmo que a alvenaria convencional por unidade de área; a mistura bahareque otimizada é ~15 % mais leve. Crítico para a logística: o **peso de envio da montagem a seco (~75 kg)** é a forma em que o painel é transportado da oficina ao canteiro (a argamassa é despejada in loco).

### Carga Axial (Vertical)

Cada painel possui dois montantes laterais verticais em cantoneira L que podem suportar cargas compressivas significativas:

| Elemento | Seção transversal | Capacidade axial conservadora |
|---|---|---|
| Montante lateral em cantoneira L (L 40×40×4 mm) | A ≈ 304 mm² | ~36 kN por montante (a σ = 120 MPa, ~50 % do escoamento A36) |
| Dois montantes laterais por painel | 2 × 304 mm² | ~72 kN por painel (~7 200 kg) |

**O que isso significa na prática:**

Uma casa típica de um pavimento com mezanino e telha cerâmica impõe aproximadamente 200–400 kg de carga por metro linear de parede (telhado + forro + piso do mezanino + carga viva). Um único painel de 1 m pode suportar **18–36× esse requisito**. **Os painéis não precisam de uma estrutura de aço separada para suportar um segundo pavimento e telhado.**

Quando usados **com uma estrutura de aço**, essa capacidade axial é pura margem de reserva — o aço suporta as cargas gravitacionais. Quando usados **sem uma estrutura de aço**, os painéis são a estrutura portante. Nesse caso, uma viga de cintamento de madeira ou bambu no topo da parede distribui a carga do telhado uniformemente por todos os painéis e os amarra.

A flambagem não é uma preocupação nesses níveis de carga **quando a cantoneira L está embebida no compósito do painel**: a espessura de parede de 85 mm de argamassa proporciona à estrutura angular rigidez lateral contínua. A relação altura/espessura do painel (~2 500/85 ≈ 29) está bem dentro dos limites de esbeltez aceitos para paredes armadas.

**Importante: limitação do eixo fraco de perfis abertos.** Perfis estruturais abertos — cantoneiras L, perfis T, perfis C — têm rigidez mínima em torno de seu eixo fraco. Um montante L 40×40×4 independente sem contraventamento do painel (I_min ≈ 3,8 × 10⁴ mm⁴) flambaria sob carga modesta. A capacidade de 36 kN por cantoneira L acima é a **capacidade de escoamento axial** e SÓ é alcançável quando a cantoneira está continuamente contraventada pelo preenchimento do painel (argamassa + guadua). Para colunas independentes em edificações de múltiplos pavimentos, perfis abertos não são apropriados — usar tubo quadrado oco (SHS).

### Carga Lateral (No Plano / Esforço Cortante)

Esta é a principal contribuição estrutural do painel — resistir a forças horizontais de vento e terremotos.

**Sem contraventamento diagonal (apenas argamassa + tiras verticais):**

Estimativa conservadora baseada na resistência ao cisalhamento da argamassa (τ ≈ 0,3 MPa para argamassa de cimento:areia 1:4) na seção transversal do painel:

- Área de cisalhamento: ~85 mm × 1.000 mm = 85.000 mm²
- Capacidade conservadora de cisalhamento: 85.000 × 0,3 = ~25 kN por painel
- Com fator de segurança 3: **~8 kN de carga de trabalho por painel**

**Com contraventamento diagonal (a configuração projetada):**

A tira diagonal de bambu (60 × 20 mm, Guadua angustifolia) em tração:

- Seção transversal: 1.200 mm²
- Resistência à tração conservadora: 80 MPa (usando ~50% dos 150–200 MPa publicados)
- Capacidade de tração diagonal: 1.200 × 80 = ~96 kN
- Componente horizontal (cos 69°): ~96 × 0,36 = ~34 kN por diagonal
- Duas diagonais (uma por lado, uma em tração): ~34 kN
- Amarrações de arame e travamento da argamassa adicionam resistência adicional
- Com fator de segurança 3: **~12–15 kN de carga de trabalho ao esforço cortante por painel**

**Para contexto:** Uma seção de parede de 3 m de largura (3 painéis) fornece ~36–45 kN de resistência ao esforço cortante. Uma edificação residencial de um pavimento em zona sísmica moderada (PGA 0,2g) com 30 kN de massa sísmica acima da parede necessita de aproximadamente 6 kN de resistência ao cisalhamento na base por metro linear de parede. Três painéis por metro fornecem 4–5× esse requisito.

Esses são números muito conservadores. A matriz de argamassa, a grade de amarrações e o perfil )( todos contribuem com resistência adicional não contabilizada acima.

### Carga Fora do Plano (Vento / Impacto)

O painel resiste à pressão perpendicular à face da parede (sucção/pressão de vento, impacto):

- O arco de argamassa criado pelo perfil )( funciona como uma abóbada rasa entre os cantoneiras L rígidos superior e inferior
- Estimativa conservadora para pressão uniforme de vento, tratando o painel como uma laje simplesmente apoiada:

| Parâmetro | Valor |
|---|---|
| Vão do painel (entre cantoneiras L superior/inferior) | 2,5 m |
| Largura do painel | 1,0 m |
| Espessura da argamassa (mínima, no centro) | ~55 mm |
| Resistência à flexão da argamassa (conservadora) | 1,0 MPa |
| Capacidade estimada de pressão uniforme | ~0,7 kPa |
| Com fator de segurança 2 | **~0,35 kPa carga de trabalho** |

**Para contexto:** 0,35 kPa ≈ velocidade de vento ~25 m/s (90 km/h). Para zonas de vento mais elevado, a estrutura de aço (não o painel) suporta a carga de vento através das conexões viga-pilar. O painel só precisa resistir à pressão local entre seus próprios elementos de estrutura.

A grade de tiras de bambu e as amarrações de arame proporcionam resistência adicional significativa fora do plano não capturada no modelo simples de laje — o painel é um compósito, não uma laje de argamassa simples.

### Cargas Pontuais (Fixações, Prateleiras, Armários)

| Tipo de fixação | Método de ancoragem | Capacidade conservadora |
|---|---|---|
| Itens leves (quadros, relógios, ganchos de toalha) | Prego ou parafuso para alvenaria na argamassa | 5–10 kg por ancoragem |
| Itens médios (prateleiras, espelhos, armários pequenos) | Bucha de expansão plástica na argamassa (6–8 mm) | 15–25 kg por ancoragem |
| Itens pesados (armários de cozinha, aquecedor de água, suporte de TV) | Parafuso passante na alma do cantoneira L | 50–100 kg por ancoragem |
| Itens muito pesados (estante, despensa cheia) | Múltiplos parafusos passantes no cantoneira L + placa de distribuição | 200+ kg por ponto de fixação |

**Dica:** A alma do cantoneira L está em uma posição conhecida (centro da espessura da parede). Um detector de metais ou ímã a localiza facilmente. O parafuso passante na alma proporciona ancoragem confiável e de alta capacidade comparável à estrutura de montantes de aço.

### Resumo — Capacidade Conservadora em kg por Painel

Para construtores e não-engenheiros, aqui estão os mesmos números expressos em quilogramas. Estas são **cargas de trabalho muito conservadoras** (já divididas por fatores de segurança de 2–3). As cargas reais de falha são 2–3× maiores.

| Tipo de carga | Direção | Capacidade conservadora de trabalho | O que isso significa na prática |
|---|---|---|---|
| **Esforço cortante (sismo/vento)** | Horizontal, no plano da parede | **~1.200–1.500 kg por painel** | Uma força horizontal de 1,2–1,5 toneladas aplicada no topo de um único painel antes de ser considerado no seu limite de trabalho. Uma casa típica de um pavimento precisa de ~600 kg de resistência ao esforço cortante por metro de parede — um painel fornece 2× isso. |
| **Fora do plano (pressão de vento)** | Perpendicular à face da parede | **~90 kg distribuídos pela face do painel** | Equivalente a ~36 kg/m² de pressão uniforme. Uma pessoa se apoiando com força na parede (~80 kg em ~0,3 m²) está bem dentro da capacidade. |
| **Axial (vertical)** | Para baixo, através do painel | **Excede amplamente as cargas residenciais (~7 200 kg de escoamento axial por painel em compósito)** | Os dois cantoneiras L laterais suportam muito mais do que um telhado + pavimento superior típico por metro de parede. Os painéis podem suportar um segundo pavimento e telhado sem estrutura de aço separada. |
| **Carga pontual na argamassa** | Arrancamento / cisalhamento na ancoragem | **~15–25 kg por ancoragem** | Um suporte de prateleira com 2 ancoragens segura 30–50 kg com segurança. |
| **Carga pontual no cantoneira L** | Parafuso passante | **~50–100 kg por parafuso** | Um armário de cozinha com 4 parafusos passantes segura 200–400 kg com segurança. |

> **Importante:** Estas são estimativas, não valores testados. Serão validadas através de testes físicos. Não utilize para engenharia estrutural sem verificação independente. Em caso de dúvida, fixe itens pesados na estrutura metálica da edificação, não no painel.

## Durabilidade (Vida Útil de Projeto de 80–100 Anos)

| Componente | Mecanismo de degradação | Prevenção | Vida útil esperada |
|---|---|---|---|
| Estrutura de aço | Corrosão | Galvanização a quente (85 μm+) | 80–100 anos (não costeiro) |
| Tiras de bambu | Ataque de insetos, decomposição fúngica | Tratamento com borato + encapsulamento em argamassa (alcalina, anaeróbica) | 80+ anos |
| Argamassa | Carbonatação, intemperismo | Protegida por reboco de cal (camada sacrificial) | 100+ anos |
| Reboco de cal | Erosão superficial, microfissuração | Autorregenerante (carbonatação preenche fissuras), caiação renovável | Indefinida com manutenção |
| Caiação | Degradação UV, erosão pluvial | Reaplicar a cada 5–10 anos | 5–10 anos por demão |
| Instalação elétrica | Degradação do isolamento | Eletroduto de PVC permite substituição de cabos sem abrir a parede | Cabos: 30–50 anos, substituíveis |
| Blocos de PEAD | Nenhum significativo | Protegidos de UV (dentro da parede) | 100+ anos |

### Cronograma de Manutenção

| Intervalo | Ação | Custo estimado |
|---|---|---|
| A cada 5–10 anos | Renovação da caiação | $50–100 por edificação |
| A cada 15–20 anos | Inspecionar reboco de cal, preencher fissuras | $100–300 por edificação |
| A cada 30–40 anos | Inspecionar instalação elétrica, substituir cabos se necessário | $200–500 por edificação |
| Aos 40 anos | Inspecionar estrutura de aço em pontos acessíveis (re-galvanizar pontualmente se necessário) | $200–400 |
| **Total na vida útil** | | **$1.400–2.000** |

## Testes Necessários

**Todos os valores de capacidade de carga acima são estimativas analíticas.** Serão validados através de testes físicos como parte do desenvolvimento deste projeto. Os primeiros painéis serão construídos e testados antes que qualquer edificação seja ocupada.

Programa de testes planejado:

- [ ] **Testes de cisalhamento no plano** (ASTM E564 ou equivalente) — painéis com e sem diagonais, para validar a estimativa de melhoria de 3–5×
- [ ] **Testes de carga fora do plano** — pressão uniforme e impacto pontual, para validar o benefício do perfil )(
- [ ] **Testes de resistência ao fogo** (ASTM E119 ou equivalente) — tempo até falha estrutural
- [ ] **Testes sísmicos cíclicos** — mesa vibratória em escala real ou carregamento cíclico quase estático, para verificar modo de falha dúctil
- [ ] **Testes de conexão** — capacidade da aba de fixação painel-pilar, durabilidade dos conectores rápidos
- [ ] **Testes de intemperismo de longo prazo** — envelhecimento acelerado de amostras de bambu encapsulado em argamassa
- [ ] **Testes de transmissão acústica** (ASTM E90) — medição de STC
- [ ] **Testes de arrancamento de carga pontual** — capacidade de ancoragem em alvenaria e parafuso passante na argamassa + cantoneira L

Os resultados dos testes serão publicados neste repositório à medida que ficarem disponíveis. Se você tem acesso a instalações de teste e quer contribuir, entre em contato — testes colaborativos com diferentes espécies de bambu e traços de argamassa tornarão este sistema mais forte para todos.
