jreuteler/bahareque-modular/pt/09-estimativa-custos.md

# Estimativa de Custos

> **Aviso:** Estas são estimativas apenas de custo de materiais, baseadas em preços de 2025 na Colômbia (região do Eje Cafetero). A mão de obra não está incluída — o sistema é projetado para produção comunitária onde a mão de obra é contribuída, não comprada. Os preços variam significativamente por região, moeda e cadeia de suprimentos. Use estas como ponto de partida, não como orçamento.

Neste projeto são documentadas duas especificações de mistura de argamassa: a **mistura base** (argamassa cimento-areia + 30 % de guadua + reboco de cal de 10 mm em ambas as faces) e a **mistura bahareque otimizada** (cal pozolânica + fibras de capim-estrela + 30 % de guadua + reboco de cal de 5 mm).

## Custo por Painel — mistura base (apenas materiais)

| Material | Especificação | Qtd por painel | Custo unitário (USD) | Total (USD) |
|---|---|---|---|---|
| Cantoneira L de aço | L 40×40×4 mm, ASTM A36 | 7,0 m | $4,00/m | $28,00 |
| Galvanização | A quente, processo em lote | 1 estrutura | $2,00 | $2,00 |
| Tiras de fixação | Chato 40×3 mm, galv. | 4,0 m | $1,00/m | $4,00 |
| Cartelas de canto + parafusos | Chato + M12/M8 | 1 conj. | $3,00 | $3,00 |
| Parafusos inox | Autoperfurantes, A2 | 40 pçs | $0,08 | $3,20 |
| Blocos de PEAD | Reciclado, 30×30 mm | 2,0 m | $1,50/m | $3,00 |
| Tiras de bambu (verticais + horizontais, 30 % densidade de cavidade) | Guadua tratada com borato | ~400 m total | $0,05/m | $20,00 |
| Tiras de bambu (diagonais) | 60×20 mm, tratada | ~5,4 m | $0,30/m | $1,60 |
| Amarrações de arame | Galvanizado | 5 m | $0,10/m | $0,50 |
| Eletroduto de PVC | 16 mm elétrico | 5 m | $0,30/m | $1,50 |
| Cabo 12V + soquetes | 2 condutores + 6× E10 | 1 conj. | $3,00 | $3,00 |
| Cabo 120V + conectores | 3 condutores + conectores rápidos | 1 conj. | $4,00 | $4,00 |
| Tela de galinheiro | Hexagonal galv., 25 mm | 5,5 m² | $0,80/m² | $4,40 |
| Cimento | Portland Tipo I | ~54 kg | $0,15/kg | $8,10 |
| Areia (argamassa) | Areia de rio limpa | ~240 kg | $0,02/kg | $4,80 |
| Fibra de PP | Picada 6–12 mm | 200 g | $5,00/kg | $1,00 |
| Aditivo pozolânico | Cinza vulcânica ou CCA | 2 kg | $0,50/kg | $1,00 |
| **Subtotal do painel — base** | | | | **~$93** |

### Acabamento no local, base (por área de painel)

| Material | Qtd por painel | Custo (USD) |
|---|---|---|
| Reboco de cal (10 mm em cada face) | ~25 kg cal + ~65 kg areia | $6,50 |
| Caiação (ambas as faces) | ~2 kg cal | $0,50 |
| **Subtotal acabamento — base** | | **$7,00** |

### **Custo total de material por painel — base: ~$100 USD**

### Custo por m² de parede acabada — base

- Área do painel: 1,0 m × 2,5 m = 2,5 m²
- Custo de material por m²: **~$40 USD/m²**

## Custo por Painel — mistura bahareque otimizada (apenas materiais)

A mistura otimizada substitui a argamassa de cimento Portland-areia por cal hidráulica + pozolana, substitui a fibra de PP por capim-estrela (grátis, coletado in loco) e usa reboco de cal mais fino de 5 mm. Mesma estrutura em cantoneira L, mesmo conteúdo de bambu, mesmos componentes elétricos e estruturais.

| Material | Especificação | Qtd por painel | Custo unitário (USD) | Total (USD) |
|---|---|---|---|---|
| Cantoneira L de aço + galvanização + tiras de fixação + cartelas | (igual à base) | | | $37,20 |
| Parafusos inox, PEAD, bambu, arames, eletroduto, cabos, tela | (igual à base) | | | $41,20 |
| Cal hidráulica (aglomerante principal) | NHL 3.5 ou NHL 5 | ~42 kg | $0,30/kg | $12,60 |
| Cinzas volantes ou cinza de casca de arroz (pozolana, 30 % equivalente cimento) | FA ou CCA | ~15 kg | $0,10/kg | $1,50 |
| Areia (argamassa) | Areia de rio limpa | ~200 kg | $0,02/kg | $4,00 |
| Fibra de capim-estrela (seca) | Coletada in loco | ~3 kg | grátis | $0,00 |
| **Subtotal do painel — otimizado** | | | | **~$96** |

### Acabamento no local, otimizado (por área de painel)

| Material | Qtd por painel | Custo (USD) |
|---|---|---|
| Reboco de cal (5 mm em cada face) | ~12 kg cal + ~33 kg areia | $3,30 |
| Caiação (ambas as faces) | ~2 kg cal | $0,50 |
| **Subtotal acabamento — otimizado** | | **$3,80** |

### **Custo total de material por painel — otimizado: ~$100 USD**

### Custo por m² de parede acabada — otimizado

- Custo de material por m²: **~$40 USD/m²**

> **As duas misturas custam aproximadamente o mesmo em materiais** (~$100/painel, ~$40/m²). A mistura otimizada troca um custo de ingredientes cal/pozolana ligeiramente mais alto (vs. cimento Portland mais barato) por menor custo de reboco de cal (mais fino), zero custo de fibra de PP, e CO₂ incorporado substancialmente menor (ver [Impacto Ambiental](10-impacto-ambiental.md)). A mistura otimizada é, portanto, **um claro ganho em carbono e autenticidade patrimonial a custo praticamente igual**.

## Comparação com Construção Convencional

| Sistema de parede | Custo de material por m² (USD) | Vida útil | Observações |
|---|---|---|---|
| **Este sistema de painéis** | **$26–28** | **80–100 anos** | Inclui estrutura, elétrica, acabamento |
| Bloco de concreto (15 cm) | $25–35 | 40–60 anos | Requer armadura, graute, reboco, tinta, elétrica separada |
| Tijolo cerâmico | $30–45 | 60–80 anos | Requer argamassa, reboco, tinta, elétrica separada |
| Drywall sobre montantes de aço | $20–30 | 20–30 anos | Sem massa térmica, não autoportante, requer tinta, elétrica separada |
| Bahareque convencional (in-situ) | $15–25 | 15–30 anos | Sem elétrica, qualidade de acabamento variável, vida útil curta sem engenharia |
| Bloco de adobe | $10–20 | 20–40 anos | Baixo desempenho sísmico, sem elétrica, requer paredes espessas |

**Percepção fundamental:** O sistema de painéis custa aproximadamente o mesmo que bloco de concreto por m² — mas inclui instalação elétrica integrada, tem o dobro da vida útil, proporciona melhor desempenho térmico e acústico, e produz um acabamento superior. Quando se contabiliza o custo de fazer a instalação elétrica de uma casa de bloco de concreto separadamente, o sistema de painéis é mais barato.

## Custo por Casa (estimativa aproximada)

Uma casa simples de um pavimento com mezanino (50 m² de área, ~70 m² habitáveis incluindo mezanino):

| Componente | Quantidade | Custo (USD) |
|---|---|---|
| Painéis de parede | ~40 painéis (100 m² de parede) | $2.600–2.800 |
| Fundação (concreto, armadura) | ~5 m³ de concreto | $800–1.200 |
| Viga de cintamento (madeira/bambu) | ~30 m | $200–400 |
| Telhado (telhas cerâmicas + terças) | ~65 m² | $1.200–1.800 |
| Piso (laje de concreto ou terra) | ~50 m² | $400–800 |
| Janelas + portas | ~8 aberturas | $600–1.200 |
| Quadro elétrico + transformador | 1 conj. | $200–400 |
| Hidráulica (básica) | Cozinha + banheiro | $300–600 |
| **Total de materiais** | | **$6.300–9.200** |

Isso é apenas materiais. No modelo de construção comunitária, a mão de obra é contribuída. No modelo de empreiteiro, adicione 40–60% para mão de obra.

**Para contexto:** Uma casa comparável de bloco de concreto na Colômbia rural custa $12.000–20.000 (materiais + mão de obra) e dura 40–60 anos. Este sistema alcança qualidade similar ou superior pela metade do custo com o dobro da vida útil.

## Estratégias de Redução de Custo

| Estratégia | Economia | Observações |
|---|---|---|
| Colher o próprio bambu | 30–40% do custo do bambu | Requer 1+ hectares de guadual, 4–5 anos de maturação |
| Reciclar PEAD de resíduos | 100% do custo do PEAD | Tábuas de corte, sobras de tubos, resíduos industriais |
| Usar cinza vulcânica (grátis) | 100% do custo da pozolana | Disponível em regiões andinas, coletar e peneirar |
| Usar fibra de grama-estrela em vez de PP | 100% do custo da fibra | Grama invasora, grátis, uso circular |
| Galvanização em lote (50+ estruturas) | 15–20% do custo de galv. | Desconto por volume na galvanizadora |
| Areeiro comunitário | 50–80% do custo da areia | Se houver acesso a areia de rio localmente |
| Produzir cal própria a partir de calcário | 50–70% do custo da cal | Requer forno (construção única), calcário local |

## Variações Regionais de Preço

Os custos de materiais variam dramaticamente por região. As estimativas acima são para a Colômbia. Multiplicadores aproximados:

| Região | Multiplicador | Observações |
|---|---|---|
| Colômbia (Eje Cafetero) | 1,0× (base) | Guadua abundante, cinza vulcânica disponível |
| Equador, Peru | 0,8–1,1× | Materiais similares, caña guadua disponível |
| América Central | 1,0–1,3× | Bambu disponível, aço pode custar mais |
| Filipinas, Indonésia | 0,7–1,0× | Bambu abundante e barato, mão de obra muito baixa |
| Índia | 0,6–0,9× | Bambu e mão de obra muito baixos, aço acessível |
| África Subsaariana | 0,8–1,2× | Espécies de bambu variam, cimento pode ser caro |
| Europa do Sul | 2,0–3,0× | Materiais disponíveis mas mais caros |

Esses multiplicadores são guias aproximados. A maior variável isolada é o custo do bambu — se você cultiva o seu, é praticamente de graça.
