jreuteler/bahareque-modular/pt/10-impacto-ambiental.md

# Impacto Ambiental

## Pegada de Carbono por Painel — mistura base

Os valores abaixo refletem a especificação base atual: estrutura de aço L 40×40×4 + 30 % de guadua na cavidade + argamassa cimento-areia (base) + reboco de cal de 10 mm em ambas as faces. Veja [Anatomia do Painel](02-anatomia-do-painel.md) e [Materiais](03-materiais.md) para detalhes.

| Material | Qtd por painel | CO₂ incorporado (kg) | Fonte da emissão |
|---|---|---|---|
| Cimento Portland (~18 % da massa de argamassa) | ~54 kg | 43,2 | Calcinação + combustível do forno (~0,8 kg CO₂/kg cimento) |
| Estrutura de aço cantoneira L + tiras de fixação | ~22 kg aço | 39,6 | Siderurgia (~1,8 kg CO₂/kg aço) |
| Galvanização (zinco) | ~0,7 kg zinco | 2,8 | Fundição de zinco (~4 kg CO₂/kg zinco) |
| Areia (~82 % da massa de argamassa) | ~240 kg | 1,2 | Extração + transporte |
| Tela de galinheiro + tela de alumínio | ~2 kg | 3,6 | Produção de arame de aço |
| Eletroduto de PVC | ~0,3 kg | 0,6 | Fabricação de PVC (~2 kg CO₂/kg) |
| Cabos + conectores | ~0,5 kg | 1,5 | Cobre + plástico |
| Blocos de PEAD | ~0,5 kg | 0,5 | Se reciclado: ~1 kg CO₂/kg (vs 3 para virgem) |
| Cal (no reboco, calcinação) | ~22 kg cal | 18,0 | Calcinação de calcário (~0,8 kg CO₂/kg cal) |
| Fibra de PP (aditivo da argamassa) | ~0,2 kg | 0,4 | Produção de polipropileno |
| **Subtotal de emissões** | | **~111 kg CO₂** | |
| Bambu (carbono sequestrado durante o crescimento) | ~38 kg peso seco (30 % cavidade) | **−60 a −75 kg CO₂** | Bambu sequestra ~1,6–2,0 kg CO₂ por kg de massa seca |
| Reboco de cal (reabsorve CO₂ durante carbonatação) | ~22 kg cal | **−6 a −9 kg CO₂** | Carbonatação da cal recaptura ~30–50 % do CO₂ da calcinação ao longo de décadas |
| **CO₂ líquido por painel, mistura base** | | **~30–45 kg CO₂** | |
| **CO₂ líquido por m² de parede, base** | | **~12–18 kg CO₂/m²** | |

## Pegada de Carbono por Painel — mistura bahareque otimizada

A mistura otimizada (cal pozolânica + capim-estrela + 30 % guadua + reboco 5 mm) reduz o carbono incorporado por meio de várias alavancas cumulativas:

| Alavanca | Delta CO₂ por painel vs base |
|---|---|
| Substituir 30 % do cimento por cinzas volantes ou CCA | −10 a −13 kg |
| Substituir argamassa de cimento Portland por cal hidráulica + pozolana | −8 a −12 kg |
| Substituir fibra de PP por capim-estrela | −0,5 kg |
| Reboco de cal de 5 mm em ambas as faces (−50 % volume de cal) | −9 kg de calcinação, +4 kg de menor recuperação por carbonatação = **−5 kg líquido** |
| **Redução total** | **−24 a −30 kg CO₂ por painel** |
| **CO₂ líquido por painel, mistura otimizada** | **~6 a 20 kg CO₂** |
| **CO₂ líquido por m² de parede, otimizada** | **~3 a 8 kg CO₂/m²** |

Com pozolanas disponíveis localmente (cinza vulcânica na região cafeeira colombiana, cinza de casca de arroz de Tolima/Valle del Cauca) e fibra de capim-estrela da própria propriedade, a mistura bahareque otimizada se aproxima de **carbono-neutra** por painel. Se o bambual for manejado como sumidouro de carbono (rotação com permanência da biomassa), o sistema se torna **carbono-negativo**: a parede absorve mais CO₂ ao longo da vida do que foi emitido para construí-la.

## Comparação com Sistemas de Parede Convencionais

| Sistema de parede | kg CO₂ por m² | Proporção vs painel base |
|---|---|---|
| **Este sistema de painéis — mistura base** | **12–18** | **1× (base)** |
| **Este sistema de painéis — mistura bahareque otimizada** | **3–8** | **~0,4× base** |
| Bloco de concreto (15 cm, rebocado) | 40–60 | 3–4× base |
| Tijolo cerâmico (rebocado) | 50–80 | 3–5× base |
| Parede de concreto armado (15 cm) | 70–100 | 5–7× base |
| Drywall sobre montantes de aço | 15–25 | 1–1,5× base |
| Bahareque convencional (reboco de barro, sem estrutura de aço) | 3–8 | 0,3–0,5× base |
| Bloco de adobe | 5–10 | 0,4–0,7× base |

A mistura base do sistema de painéis produz **~3× menos CO₂ que bloco de concreto ou tijolo** — os dois materiais de parede mais comuns no mundo em desenvolvimento. A mistura bahareque otimizada se aproxima dos níveis da construção tradicional de terra, fornecendo desempenho estrutural e vida útil vastamente superiores.

## Carbono por Ano de Serviço

Quando a vida útil é considerada, a comparação se torna ainda mais dramática:

| Sistema de parede | kg CO₂/m² | Vida útil (anos) | kg CO₂/m²/ano |
|---|---|---|---|
| **Este sistema de painéis** | 8 | 90 | **0,09** |
| Bloco de concreto | 50 | 50 | 1,00 |
| Tijolo cerâmico | 65 | 70 | 0,93 |
| Drywall sobre montantes de aço | 20 | 25 | 0,80 |
| Bahareque convencional | 5 | 20 | 0,25 |

**Ao longo de sua vida útil, este sistema de painéis produz ~10× menos carbono por ano de serviço do que bloco de concreto.**

## Caminho para Carbono Neutro ou Carbono Negativo

O sistema de painéis já é de baixo carbono. Com as seguintes substituições, ele se aproxima do carbono neutro:

| Substituição | CO₂ economizado por painel | Viabilidade |
|---|---|---|
| Substituir 50% do cimento por pozolana (cinza vulcânica, CCA) | −10 kg | Disponível em regiões vulcânicas e produtoras de arroz |
| Usar aço reciclado (forno elétrico a arco) | −7 kg | Depende da cadeia de suprimentos local de aço |
| Substituir fibra de PP por grama-estrela | −0,5 kg | Disponível onde a grama cresce |
| Aumentar conteúdo de bambu (tiras mais espessas, mais diagonais) | −3 a −5 kg sequestro adicional | Material é grátis/barato |
| Usar cal artesanal (forno a lenha com lenha manejada) | −3 kg | Método tradicional de produção de cal |
| **Redução potencial total** | **−20 a −25 kg** | |

Com essas substituições, o CO₂ líquido por painel cai para **~0–5 kg** — efetivamente carbono neutro. Se o conteúdo de bambu for aumentado ainda mais ou o bambuzal for manejado como sumidouro de carbono, o sistema se torna **carbono negativo**: a parede absorve mais CO₂ durante sua vida do que foi emitido para construí-la.

## Consumo de Água

- **Mistura da argamassa:** ~15–20 litros por painel (água de cura reutilizada quando possível)
- **Cura:** ~50 litros ao longo de 7 dias (método de borrifação/estopa)
- **Mistura do reboco de cal:** ~10 litros por painel
- **Total:** ~75–80 litros por painel, ou ~30 litros por m² de parede

Para comparação: produção de bloco de concreto usa ~40–50 litros por m² de parede. Produção de tijolo cerâmico usa ~100+ litros por m² (incluindo resfriamento do forno).

## Resíduos

- **Sobras de aço:** Recicladas (valor de sucata)
- **Sobras de bambu:** Compostadas ou usadas como tutores/cobertura morta
- **Resíduos de argamassa:** Mínimos — o vertimento em mesa vibratória é preciso. Qualquer excesso é reutilizado no próximo painel.
- **Leito de areia:** Reutilizado indefinidamente (a areia não é consumida, apenas comprimida e solta)
- **Sobras de PEAD:** Recicladas ou reutilizadas para blocos menores
- **Resíduos de embalagem:** Mínimos — a maioria dos materiais chega a granel

O sistema produz **resíduos de construção próximos de zero**. Isso é consequência direta da pré-fabricação em oficina — cada corte é planejado, cada material é medido.

## Fim de Vida (após 80–100 anos)

Quando um painel eventualmente chega ao fim de vida:

| Material | Destinação | Impacto ambiental |
|---|---|---|
| Estrutura de aço | Reciclar (100% reciclável) | Positivo — aço sucata tem valor |
| Argamassa + bambu | Triturar e usar como agregado ou aterro | Inerte — argamassa é cálcio/sílica/areia, bambu é orgânico |
| Reboco de cal | Retorna a carbonato de cálcio (calcário) | Carbono neutro — CO₂ absorvido durante carbonatação é re-liberado, saldo zero |
| Blocos de PEAD | Reciclar | Reciclável |
| Cabos de cobre | Reciclar (alto valor de sucata) | Positivo |
| Eletroduto de PVC | Reciclar onde existem instalações | Reciclável em princípio |

**Nenhum resíduo perigoso.** Sem amianto, sem tinta com chumbo, sem espuma de isolamento sintético, sem produtos químicos de madeira tratada sob pressão. O painel é feito de aço, bambu, areia, cimento e cal — retorna à terra ou ao ciclo de reciclagem de forma limpa.
