jreuteler/bahareque-modular/pt/11-transporte-manuseio.md

# Transporte e Manuseio

## Especificações do Painel para Manuseio

| Propriedade | Valor |
|---|---|
| Dimensões | 1,0 m × 2,5 m × 85 mm |
| Peso da montagem a seco (como enviado ao canteiro) | **~75 kg** |
| Peso do painel acabado (mistura base, após despejo in loco + cura + reboco) | ~440 kg |
| Peso do painel acabado (mistura bahareque otimizada) | ~360 kg |
| Centro de gravidade | Centro (construção simétrica) |
| Áreas frágeis | Cantos, bordas (a argamassa pode lascar uma vez despejada com impacto) |
| Cura mínima antes do manuseio | 7 dias após despejo in loco |
| Cura mínima antes da instalação | 14 dias recomendado — nota: no modelo de despejo in loco, o painel é erguido e a argamassa é despejada no local, então «instalação» e «despejo» ocorrem juntos no canteiro |

## Modelo de Produção Primário: Despejo In Loco

**O modelo de produção primário consiste em enviar a montagem a seco (~75 kg) ao canteiro e despejar a argamassa in loco contra cofragem.** O painel acabado de ~440 kg nunca é movido como unidade — torna-se diretamente parte da parede do edifício, economizando custos de equipamento de elevação pesada e eliminando o risco de fissuração durante o transporte. Veja [Processo Construtivo](04-processo-construtivo.md) para o protocolo de despejo vertical in loco.

O manuseio de painéis curados (seções abaixo) aplica-se ao modelo alternativo: despejo de argamassa em oficina sobre mesa vibratória, com painéis totalmente curados enviados ao canteiro como elementos acabados. Esta abordagem é mantida como opção documentada para construtores que preferem produção em oficina, mas adiciona custos significativos de elevação, transporte e taxa de rejeição.

## Transporte Manual — montagem a seco (~75 kg)

A montagem a seco (estrutura de aço cantoneira L + esterilla de bambu + tela + instalações, antes da argamassa) é levantada e posicionada por **2 pessoas com uma simples cinta**. Sem dispositivo de transporte, sem guindaste, sem empilhadeira — esta é uma das vantagens operacionais centrais do modelo de produção com despejo in loco.

### Cinta única (montagem a seco)

1. Enrolar uma única cinta (50 mm × capacidade 500+ kg) ao redor do painel à meia altura (~125 cm da base)
2. Cada carregador segura uma extremidade da cinta com ambas as mãos, em lados longos opostos do painel
3. Levantar juntos; o painel fica pendurado verticalmente entre eles
4. Caminhar em ritmo normal; o painel pode ser carregado 30–50 m antes de uma pausa

**Peso por pessoa: ~38 kg** — completamente administrável para os transportes curtos típicos da oficina-caminhão, caminhão-estoque-canteiro, estoque-instalação.

## Transporte Manual — painel acabado curado (modelo alternativo de oficina)

Um painel acabado de ~360–440 kg **não pode ser carregado à mão**. Requer elevação mecânica (talha de corrente, mini-carregadeira ou pequeno guindaste móvel). Esta é a razão central pela qual o modelo de despejo in loco é preferido.

Se painéis despejados em oficina precisarem ser movidos (p. ex. produção piloto antes da validação do protocolo in loco), use:

### Dispositivo de Transporte (painel curado, ~360–440 kg)

Duas varas de bambu (3 m de comprimento, 8–10 cm de diâmetro) passadas por laços de cinta de elevação pesada enrolados ao redor do painel a 1/4 e 3/4 da altura:

1. Deitar o painel
2. Enrolar duas cintas (50 mm de largura, capacidade de 1 000+ kg) ao redor do painel a ~60 cm e ~190 cm da base
3. Passar uma vara de bambu pelos laços de ambas as cintas de cada lado
4. **4 pessoas por vara, 8 carregadores no total** para um painel de mistura base a ~440 kg, ou 6 carregadores para um painel de mistura otimizada a ~360 kg
5. O painel fica pendurado verticalmente entre as varas

**Peso por pessoa: ~55 kg (base) / ~45 kg (otimizada)** — no limite superior do manuseio manual seguro. Para distâncias longas ou escadas, usar elevação mecânica em vez disso.

### Levantamento e Inclinação

- **Nunca levante um painel por uma borda** — a argamassa pode fissurar sob seu próprio peso em balanço
- **Sempre levante por dois pontos** simétricos, ou pela base com apoio por trás
- **Inclinar de deitado para vertical:** Duas pessoas seguram a borda superior, duas pessoas levantam a base. Girar lentamente. Apoiar a base sobre um bloco acolchoado durante a rotação.

## Armazenamento na Oficina

Após a cura, os painéis são armazenados **verticalmente (de lado)** em um cavalete tipo A:

- Apoiar painéis em ambos os lados de uma estrutura inclinada (como um livro aberto)
- 10–15 painéis por lado do cavalete
- Separar painéis com pequenos espaçadores de madeira para permitir circulação de ar
- Cobrir com lona ou telhado para proteger de chuva direta (argamassa em cura pode ser lavada por chuva forte antes da cura completa)
- Manter fora do contato com o solo — apoiar a borda inferior sobre cascalho ou travessa de madeira

**Espaço necessário:** ~3 m × 1 m de área de piso por 20–30 painéis armazenados.

## Transporte por Caminhão

### Carregamento

1. Colocar painéis verticalmente na carroceria do caminhão, apoiados contra uma lateral
2. Colocar espaçadores de madeira (sobras, bambu ou espuma) entre cada painel
3. Fixar painéis à lateral do caminhão usando cintas de catraca a 1/3 e 2/3 da altura
4. Nunca empilhar painéis deitados uns sobre os outros — o painel inferior vai fissurar sob o peso da pilha
5. Máximo ~15–20 painéis por caminhonete padrão (dependendo da capacidade do caminhão e condições da estrada)

### Considerações sobre a Estrada

- **Estradas pavimentadas:** Nenhuma precaução especial além das cintas
- **Estradas não pavimentadas/irregulares:** Reduzir velocidade. Adicionar espuma ou papelão entre painéis. Apertar bem as cintas — painéis podem se deslocar e lascar bordas em lombadas.
- **Aclives acentuados:** Garantir que os painéis estejam apoiados na direção do aclive (não na direção oposta) para evitar tombamento
- **Distância:** Sem limite. Os painéis estão totalmente curados e autossuficientes. Podem viajar qualquer distância.

### Descarregamento

1. Remover cintas de cima para baixo
2. Duas pessoas por painel — uma na borda superior, uma apoiando a base
3. Levar cada painel até o cavalete de armazenamento no canteiro
4. Nunca derrubar ou arrastar painéis — bordas de argamassa lascam facilmente

## Guincho / Talha (para pavimentos superiores)

Para edificações de dois pavimentos, os painéis devem ser levantados ao segundo andar:

- **Mastro simples com roldana:** Uma vara de bambu ou aço com corda e roldana. Duas pessoas puxam a corda, uma guia o painel. Funciona para volumes baixos.
- **Talha de corrente na viga:** Fixar uma talha de corrente de 500 kg na viga de aço da edificação. Prender à cinta de transporte do painel. Uma pessoa opera, uma guia. Rápido e controlado.
- **Empilhadeira (se disponível):** Garfo sob o painel (protegido com papelão). Levantar e posicionar diretamente.

**Não jogue, role ou arraste painéis.** A argamassa é resistente à compressão mas pode fissurar com impacto pontual.

## Danos e Reparos

| Tipo de dano | Causa | Reparo |
|---|---|---|
| Lasca no canto (pequena) | Impacto durante transporte | Preencher com argamassa, rebocar por cima. Apenas estético. |
| Fissura na borda (superficial) | Batida durante manuseio | Preencher com reboco de cal. Não afeta a estrutura. |
| Fissura passante (argamassa) | Queda ou impacto severo | O painel pode estar comprometido. Avaliar: se a estrutura de aço está intacta e a fissura é <2 mm, preencher com argamassa e monitorar. Se a fissura é >5 mm ou a estrutura está empenada, rejeitar o painel. |
| Conector rápido quebrado | Enganchado durante transporte | Substituir conector (soldado ou crimpado). |

**Taxa de rejeição:** Com cuidado razoável, espere <5% dos painéis sofrerem qualquer dano durante transporte e manuseio, e <1% requererem rejeição. Painéis rejeitados podem ter componentes elétricos removidos e ser reciclados como material de aterro.

## Lista de Verificação Antes do Transporte

- [ ] Painel curado no mínimo 7 dias (14 recomendado)
- [ ] Painel marcado com tipo (P/T/I/H) e data de produção
- [ ] Circuitos elétricos testados (verificação de continuidade 12V + 120V)
- [ ] Sem fissuras visíveis >1 mm
- [ ] Cantos intactos
- [ ] Cintas de transporte ou dispositivo preparados
- [ ] Carroceria do caminhão limpa, espaçadores prontos, cintas disponíveis
- [ ] Rota verificada para condições da estrada (pontes, gabaritos, aclives)
