jreuteler/bahareque-modular/pt/14-melhoria-acustica.md

# Melhoria acústica — Paredes expostas ao ruído

> *Este capítulo foi inspirado por uma sugestão de Kim Hansson — obrigado por incentivar o design a lidar com condições urbanas reais.*

O painel padrão (STC 40–45) é adequado para áreas residenciais tranquilas. Para edificações em ruas movimentadas, próximas a rodovias ou adjacentes a zonas comerciais/industriais, as paredes expostas ao ruído podem ser melhoradas individualmente. Não é necessário melhorar todas as paredes — a maioria das edificações tem apenas um ou dois lados expostos a ruído significativo. As paredes voltadas para o lado tranquilo permanecem com painéis padrão.

## Guia de exposição ao ruído

| Situação | Tratamento recomendado | STC alvo |
|---|---|---|
| Rua residencial tranquila | Painel padrão — sem necessidade de melhoria | 40–45 |
| Tráfego moderado | Argamassa densa + camada de amortecimento em argila | 48–52 |
| Via urbana movimentada, rotas de ônibus | Painel duplo com cavidade de fibra | 55–62 |
| Rodovia, zona industrial, área de vida noturna | Painel duplo com cavidade de fibra + camada de argila | 58–65 |

**Aplique a melhoria apenas onde necessário.** Uma casa típica em uma rua movimentada tem uma ou duas paredes expostas ao ruído (10–15 m²). As paredes restantes dão para o jardim, quintal ou lado tranquilo e usam painéis padrão. Isso mantém o custo adicional proporcional ao problema real de ruído.

## Opção 1: Mistura de argamassa mais densa (mais barata, +3–5 STC)

A areia de rio padrão é substituída por agregados mais pesados na mistura de argamassa. Mesmo processo de produção, mesmo quadro, mesmo preenchimento em mesa vibratória. O painel simplesmente fica mais pesado.

| Agregado | Aumento de densidade | Custo vs. areia padrão | Disponibilidade |
|---|---|---|---|
| Basalto britado ou finos de granito | +15–20% | Similar | Universal — qualquer pedreira |
| Escória de ferro (*escória*) | +25–30% | Frequentemente grátis | Próximo a siderúrgicas, fundições |
| Areia magnetítica (*areia preta*) | +40% | Baixo | Leitos de rios vulcânicos (Andes, América Central) |

- **Peso do painel:** acabado ~490–530 kg mistura base (vs. ~440 kg base padrão) / ~405–440 kg mistura otimizada (vs. ~360 kg otimizada padrão). Peso de montagem a seco inalterado em ~75 kg (o agregado denso é adicionado no vertido in-situ, não na montagem em oficina)
- **Custo extra:** ~$1–2 por painel
- **STC:** ~43–48
- **Mudança na produção:** Nenhuma — apenas substituir o agregado. A proporção da mistura permanece 1:4 cimento:agregado.

**Ideal para:** Paredes laterais que precisam de uma melhoria moderada sem alterar a espessura da parede ou o processo construtivo.

## Opção 2: Camada de amortecimento em argila (+5–8 STC)

Adiciona-se uma camada de 10–15 mm de **reboco de argila com palha** na face interna da parede exposta ao ruído, aplicada in loco entre a superfície de argamassa e o acabamento de reboco de cal.

### Por que a argila funciona

A argila tem um amortecimento acústico superior ao da argamassa de cimento. Quando as ondas sonoras atingem uma camada de argila, mais energia é convertida em calor (atrito interno nas partículas de argila) em vez de ser transmitida através da parede. Fibras de palha picada dentro da argila adicionam atrito interno extra.

Esta é a técnica de bahareque mais tradicional — o reboco de argila (*pañete de tierra*) é usado em paredes de bambu há séculos. Funciona acusticamente pela mesma razão que funciona termicamente: a argila é um absorvedor natural de energia.

### Aplicação

1. Preparar a mistura de argila e palha: argila local + capim ou palha seca picada (pedaços de 5–10 cm), misturados até formar uma pasta espessa
2. Aplicar 10–15 mm na face interna da parede exposta ao ruído, sobre a superfície de argamassa
3. Deixar secar (3–7 dias dependendo da umidade)
4. Aplicar reboco de cal (3–5 mm) sobre a camada de argila como acabamento final
5. Caiação como de costume

### Especificações

- **Espessura total da parede:** ~100 mm (vs. 85 mm padrão)
- **Custo extra:** ~$2–4 por área de painel (a argila normalmente é gratuita — escavada durante a fundação)
- **STC:** ~45–50
- **Mudança na produção:** Nenhuma no painel em si. A camada de argila é aplicada in loco após a instalação.

**Ideal para:** Melhoria econômica. Usa material local gratuito. Sem mudança na produção do painel. Melhora a regulação de umidade como bônus.

## Opção 3: Painel duplo com cavidade de fibra (melhor desempenho acústico, +15–20 STC)

Dois painéis padrão com uma cavidade de 50–100 mm entre eles, preenchida com fibra orgânica solta. Esta é a opção de alto desempenho para ambientes realmente ruidosos.

### Por que funciona

Três princípios acústicos se combinam:

1. **Massa dupla** — duas paredes de argamassa em vez de uma. A lei da massa diz que dobrar a massa adiciona ~6 dB de redução sonora.
2. **Desacoplamento** — a cavidade de ar interrompe o caminho da vibração. O som se transmite eficientemente através de materiais sólidos, mas com dificuldade através de um espaço de ar. Os dois painéis vibram independentemente.
3. **Absorção** — a fibra solta dentro da cavidade absorve a energia sonora que de outro modo ricochetearia entre os dois painéis (ressonância de onda estacionária).

### Materiais de preenchimento da cavidade

Use o que estiver disponível localmente e for barato. O preenchimento deve ser **solto, não compactado** — as bolsas de ar dentro da fibra é que absorvem o som.

| Material | Qualidade acústica | Custo | Disponibilidade regional |
|---|---|---|---|
| **Casca de arroz** (*cascarilla de arroz*) | Excelente | Grátis–$2/saco | Regiões arrozeiras (Ásia, América Latina) |
| **Fibra de coco** (*fibra de coco*) | Excelente | $3–5/saco | Regiões costeiras tropicais |
| **Capim-estrela seco** (*pasto estrella*) | Boa | Grátis | Américas tropicais (invasivo, removido dos campos) |
| **Raspas de madeira** (*viruta*) | Boa | Grátis–$1/saco | Marcenarias |
| **Cascalho vulcânico solto** (*gravilla volcánica*) | Boa (por massa) | $2–3/saco | Regiões vulcânicas (Andes, América Central, Sudeste Asiático) |
| **Fibra de folha de bananeira seca** | Boa | Grátis | Regiões produtoras de banana |

**A casca de arroz é a melhor opção geral** onde disponível: leve, não compacta com o tempo, naturalmente resistente ao fogo (alto teor de sílica) e extremamente barata ou gratuita em beneficiadoras de arroz.

### Construção

1. Instalar o painel externo como de costume (parafusado ao quadro estrutural ou viga de amarração)
2. Deixar um espaço de 50–100 mm (definido por espaçadores ou coluna/suporte de fixação mais largo)
3. Preencher a cavidade de forma solta com material de fibra — não compactar
4. Instalar o painel interno, fechando a cavidade
5. Ambos os painéis são parafusados à mesma estrutura portante

A largura da cavidade depende do espaço disponível e do desempenho desejado:

| Largura da cavidade | Melhoria STC | Espessura total da parede |
|---|---|---|
| 50 mm | +12–15 STC | ~220 mm |
| 75 mm | +15–18 STC | ~245 mm |
| 100 mm | +18–20 STC | ~270 mm |

### Especificações

- **Espessura total da parede:** 220–270 mm (vs. 85 mm padrão)
- **Custo extra:** ~$65–70 por m² (um painel adicional) + $2–5 para preenchimento da cavidade = ~$70–75 extra por m²
- **STC:** 55–62
- **Mudança na produção:** Nenhuma — usa dois painéis padrão

**Ideal para:** Fachadas em ruas movimentadas, edificações junto a rodovias, quartos voltados para vias ruidosas, salas de música, oficinas adjacentes a espaços residenciais.

## Opções combinadas

As opções são cumulativas. Para o máximo desempenho acústico em uma parede crítica:

| Combinação | STC | Custo extra/m² | Caso de uso |
|---|-----|---|---|
| Painel padrão | 40–45 | Base | Lado tranquilo |
| Apenas argamassa densa | 43–48 | +$1–2 | Ruído leve, melhoria mais barata |
| Argamassa densa + camada de argila | 48–52 | +$3–6 | Ruído de tráfego moderado, parede individual |
| Painel duplo + cavidade de fibra | 55–62 | +$70–75 | Via movimentada |
| Painel duplo (argamassa densa) + cavidade de fibra + argila interna | 58–65 | +$75–80 | Rodovia, indústria, casa noturna ao lado |

## Exemplo típico de edificação

Uma casa térrea em uma esquina movimentada, com jardim em dois lados:

| Parede | Voltada para | Tratamento | STC | Custo extra |
|---|---|---|-----|---|
| Parede norte (10 m²) | Via movimentada | Painel duplo + casca de arroz | 55–60 | ~$700–750 |
| Parede leste (6 m²) | Rua secundária | Argamassa densa + camada de argila | 48–52 | ~$20–36 |
| Parede sul (10 m²) | Jardim | Painel padrão | 42–45 | $0 |
| Parede oeste (6 m²) | Jardim do vizinho | Painel padrão | 42–45 | $0 |
| **Custo extra total** | | | | **~$720–790** |

Por ~$750, a parede mais ruidosa recebe isolamento acústico de nível profissional enquanto as paredes tranquilas permanecem padrão. A melhoria acústica adiciona menos de 10% ao custo total da casa conforme o [orçamento estimado](09-orcamento-estimado.md).

## Notas sobre materiais

### Segurança contra incêndio do preenchimento da cavidade

- **Casca de arroz:** Alto teor de sílica, naturalmente resistente ao fogo. Não sustenta chama. Carboniza mas se autoextingue.
- **Fibra de coco:** Ignição lenta, autoextinguível quando solta.
- **Capim/palha seca:** Mais inflamável. Tratar com solução de borato (mesmo tratamento do bambu) para resistência ao fogo se utilizada na cavidade. A cavidade é selada entre dois painéis de argamassa, então o risco de ignição é muito baixo de qualquer forma.
- **Cascalho vulcânico:** Incombustível.

### Umidade na cavidade

A cavidade deve permanecer seca. Ambos os painéis são selados com argamassa e rebocados com cal — a umidade não deveria entrar. Porém:

- Não usar o sistema de painel duplo abaixo do nível do solo ou em áreas sujeitas a inundação
- Garantir que o topo da cavidade esteja selado (viga de amarração ou capeamento de argamassa)
- Em climas extremamente úmidos, deixar pequenas aberturas de ventilação no topo e na base da cavidade (cobertas com tela para evitar entrada de insetos) para permitir circulação de ar

### Retrofit

A melhoria acústica pode ser **adicionada posteriormente** a uma parede existente de painel padrão:

1. Construir uma segunda parede de painel 50–100 mm por dentro da parede existente
2. Preencher a cavidade com fibra
3. O espaço interno diminui pela largura da cavidade + espessura do painel (~135–185 mm por parede melhorada)

Isso permite construir com painéis padrão agora e melhorar paredes específicas depois se o ruído se tornar um problema — por exemplo, se uma rua tranquila ficar movimentada após um desenvolvimento urbano.
