jreuteler/bahareque-modular/de/13-bambusbehandlung.md

# Bambusbehandlungsprotokoll

Unbehandelter Bambus wird in tropischen Klimazonen innerhalb von 1–5 Jahren von Nagekäfern zerfressen und von Pilzen abgebaut. Eine fachgerechte Behandlung verlängert die Lebensdauer von Bambus auf **Jahrzehnte** — und wenn er in Mörtel eingebettet ist, auf **80+ Jahre**.

Dieses Kapitel behandelt die Boratbehandlung — die sicherste, günstigste und wirksamste Methode für Bambus im Bauwesen.

## Warum Borat

| Eigenschaft | Borat | CCA (Chrom-Kupfer-Arsenat) | Kreosot |
|---|---|---|---|
| Toxizität für Menschen | Sehr niedrig (Borax wird in Seife verwendet) | Hoch (Arsen, Chrom) | Hoch (krebserregend) |
| Insektenschutz | Ausgezeichnet | Ausgezeichnet | Ausgezeichnet |
| Pilzschutz | Gut | Ausgezeichnet | Ausgezeichnet |
| Kosten | Sehr niedrig | Moderat | Moderat |
| Umwelt | Sicher, wasserlöslich | Sondermüll | Sondermüll |
| Eignung für Bambus | Ausgezeichnet (dringt gut ein) | Schlecht (Bambus widersteht ölbasierten Mitteln) | Schlecht |
| Kompatibilität mit Mörtel | Ausgezeichnet (keine chemische Reaktion) | Unbekannt | Inkompatibel |

**Borat ist die klare Wahl für Bambus im Bauwesen.** Es ist ungiftig, günstig, wirksam und kompatibel mit der Mörtelummantelung, die den sekundären Langzeitschutz bietet.

## Boratlösung herstellen

### Materialien

| Material | Menge pro 100 Liter | Anmerkungen |
|---|---|---|
| Borax (Natriumtetraborat, Na₂B₄O₇·10H₂O) | 3 kg | Erhältlich in Landwirtschaftsbedarfsläden, Apotheken oder bei Industriechemie-Lieferanten |
| Borsäure (H₃BO₃) | 2 kg | Gleiche Bezugsquellen wie Borax |
| Wasser | 100 Liter | Sauber, trinkbar. Warmes Wasser (40–50°C) löst schneller. |

Dies ergibt eine **~5% Boratlösung** (nach Gewicht der gelösten Feststoffe). Für Umgebungen mit hohem Insektendruck (tropisch feuchte Tieflagen) auf 4 kg Borax + 3 kg Borsäure pro 100 L erhöhen für eine **~7% Lösung**.

### Mischen

1. 20 Liter Wasser auf 50–60°C erwärmen (heiss, aber nicht kochend)
2. Borax hinzufügen, rühren bis vollständig gelöst (~5 Minuten)
3. Borsäure hinzufügen, rühren bis gelöst (~5 Minuten)
4. Restliche 80 Liter Wasser bei Raumtemperatur hinzufügen
5. Gut umrühren. Lösung sollte klar oder leicht trüb sein.
6. Lösung ist sofort einsatzbereit.

**Haltbarkeit:** Unbegrenzt bei Lagerung in geschlossenem Behälter. Borat baut sich nicht ab.

## Behandlungsmethoden

### Methode 1: Tauchen im Becken (einfachste, empfohlen für Streifen)

Am besten für: gespaltene Bambusstreifen (die in diesem Paneelsystem verwendete Form).

1. **Streifen vorbereiten:** Bambus spalten und reinigen. Verbleibende Innenhaut (Weichgewebe) entfernen. Streifen sollten ~20 mm breit, 2.500 mm lang sein.
2. **Becken bauen oder beschaffen:** Ein einfacher Trog aus Betonblöcken und Plastikfolie, ein längs aufgeschnittenes PVC-Rohr oder ein gekaufter Vieh-Wassertrog. Muss die Streifen vollständig untergetaucht halten können.
3. **Streifen vollständig in Boratlösung untertauchen.** Bei Auftrieb mit Steinen oder einem Bambusgitter beschweren.
4. **5–7 Tage bei Raumtemperatur tauchen.** Borat diffundiert in das Bambusgewebe. Dünnere Streifen (wie die hier verwendeten 20 mm Streifen) absorbieren schneller als ganze Halme.
5. **Herausnehmen und trocknen.** Streifen auf einem Gestell im Schatten mit Luftzirkulation stapeln. 3–7 Tage trocknen, bis der Feuchtigkeitsgehalt unter 15% fällt.
6. **Sichtkontrolle:** Behandelter Bambus zeigt oft einen leicht grünlichen oder bläulichen Farbton durch das Borat. Dies ist normal und bestätigt die Durchdringung.

**Wiederverwendung der Lösung:** Dasselbe Becken mit Lösung kann für mehrere Chargen verwendet werden. Bei sinkendem Pegel mit frischer Lösung auffüllen (Bambus absorbiert einen Teil). Konzentration mit einem Borat-Testkit prüfen falls verfügbar, oder alle 5–6 Chargen ersetzen.

**Kapazität:** Ein 3 m × 0,5 m × 0,3 m Trog fasst ~450 Liter und behandelt ~200 Streifen pro Charge — genug für ~4 Paneele.

### Methode 2: Modifizierte Boucherie (für ganze Halme vor dem Spalten)

Am besten für: Behandlung ganzer Guadua-Halme vor dem Spalten in Streifen. Schnellere Durchdringung durch das Gefässsystem.

1. **Frischen Bambus ernten** (innerhalb von 24 Stunden nach dem Schnitt — Saftfluss muss noch aktiv sein)
2. **Halm auf Länge schneiden.** Alle inneren Membranen (Knoten) mit einer Stahlstange durchstossen.
3. **Gummikappe oder Schlauch** am Fussende des Halms befestigen, verbunden mit einem erhöhten Boratlösungs-Tank (schwerkraftgespeist, 2–3 m Höhendifferenz).
4. **Lösung fliesst durch den Halm** über die Gefässbündel, angetrieben durch Schwerkraft. Die boratreiche Lösung verdrängt den natürlichen Saft und tritt als helle Tropfen am oberen Ende aus.
5. **Behandlungsdauer:** 3–5 Tage für einen 6 m Halm. Abgeschlossen, wenn die am oberen Ende austretende Flüssigkeit positiv auf Borat testet (Kurkuma-Indikator verwenden — färbt sich rot bei Borat).
6. **Herausnehmen, trocknen und spalten** in Streifen nach der Behandlung.

**Vorteile:** Gleichmässigere Durchdringung als Tauchen. Funktioniert für dickwandige Halme, bei denen Tauchen Wochen dauern würde. Bewahrt die Saftbahn-Feuchtigkeitskanäle, die die Boratverteilung unterstützen.

**Nachteile:** Erfordert frisch geschnittenen Bambus (nicht getrocknet). Erfordert erhöhten Tank und Schlauchanordnung. Nicht praktikabel für bereits gespaltene Streifen.

### Methode 3: Sprühen/Streichen (nur im Notfall, nicht empfohlen)

Oberflächenapplikation von Boratlösung durch Sprühen oder Streichen. Eindringtiefe begrenzt auf 1–3 mm. **Nicht ausreichend für Strukturbambus.** Nur als vorübergehende Massnahme verwenden, wenn kein Tauchbecken verfügbar ist, und bei nächster Gelegenheit fachgerecht nachbehandeln.

## Qualitätskontrolle

### Durchdringungstest

Nach Behandlung und Trocknung einen Musterstreifen testen:

1. Einen Querschnitt aus der Mitte eines behandelten Streifens schneiden
2. **Kurkumalösung** herstellen (1 Teelöffel Kurkumapulver in 50 ml Isopropanol auflösen)
3. Auf den geschnittenen Querschnitt pinseln
4. Borat-behandeltes Holz färbt sich bei Kontakt mit Kurkuma **rot/dunkelorange**
5. Unbehandeltes Holz bleibt **gelb**

Der gesamte Querschnitt sollte sich rot färben — dies bestätigt vollständige Durchdringung. Wenn die Mitte gelb bleibt, die Tauchzeit für die nächste Charge verlängern.

### Retentionstest (fortgeschritten)

Für formale Qualitätskontrolle behandelte Proben an ein Labor senden zur Borat-Retentionsanalyse (Zielwert: >4 kg BAE/m³ — Borsäureäquivalent pro Kubikmeter Bambus). Dieses Niveau ist ausreichend für alle holzbohrenden Insekten und die meisten Pilzarten.

## Sicherheit

- **Borat hat niedrige Toxizität.** Borax wird in handelsüblichen Reinigungsprodukten verwendet. Borsäure wird in Augenspüllösungen verwendet. Keines von beiden ist als gefährlich eingestuft bei den verwendeten Konzentrationen.
- **Handschuhe tragen** beim Umgang mit konzentrierter Lösung (leicht hautreizend bei längerem Kontakt).
- **Lösung nicht trinken.** Borat ist bei Aufnahme grösserer Mengen leicht toxisch (vergleichbar mit Kochsalz). Von Kindern und Tieren fernhalten.
- **Gebrauchte Lösung nicht in Gewässer einleiten.** Borat kann aquatische Organismen bei hohen Konzentrationen beeinträchtigen. Gebrauchte Lösung auf dem Boden abseits von Wasserquellen ausbringen (Bor ist ein Pflanzen-Mikronährstoff bei niedrigen Konzentrationen).

## Behandlungszusammenfassung für dieses Paneelsystem

| Bambuskomponente | Behandlungsmethode | Tauchzeit | Konzentration |
|---|---|---|---|
| Vertikalstreifen (20 mm × 2.500 mm) | Beckentauchung | 5–7 Tage | 5% (Standard) oder 7% (feuchte Tieflagen) |
| Diagonalstreifen (60 × 20 mm × 2.690 mm) | Beckentauchung | 7–10 Tage (dicker) | 5–7% |
| Ganze Halme (vor dem Spalten) | Modifizierte Boucherie | 3–5 Tage | 5% |

Nach Behandlung und Trocknung ist der Bambus bereit für die Paneelmontage. Das Borat bietet primären Insekten-/Pilzschutz. Die Mörtelummantelung bietet sekundären Schutz — sie schafft ein alkalisches, anaerobes Milieu, das biologischem Abbau feindlich gegenübersteht.

**Kombinierte Schutzlebensdauer: 80+ Jahre.**
