jreuteler/bahareque-modular/en/06-corrosion-prevention.md

# Corrosion Prevention

## Design Philosophy

The panel system uses multiple materials in intimate contact. Every material interface is a potential corrosion risk. This chapter documents the galvanic analysis of each interface and the prevention strategy.

**Design target: 80–100 years without structural corrosion failure.**

## Galvanic Series (relevant metals)

From anodic (corrodes first) to cathodic (protected):

1. Zinc (galvanizing coating)
2. Aluminum (insect mesh)
3. Mild steel (frame, clamping strips)
4. Stainless steel (screws)

When two metals are in electrical contact in the presence of an electrolyte (moisture), the more anodic metal corrodes preferentially. This is the basis of galvanic corrosion.

## Interface Analysis

### 1. Steel Frame ↔ Mortar

- **Contact:** Direct — mortar is poured onto and around the galvanized steel frame
- **Risk level:** LOW
- **Analysis:** The alkaline environment of cement mortar (pH 12–13) passivates the zinc coating, forming a stable zinc oxide layer. This is actually a *beneficial* combination — the mortar protects the zinc, and the zinc protects the steel. Same principle as rebar in reinforced concrete.
- **The pozzolanic admixture** gradually reduces mortar pH to 10–11 over decades. This remains well within the passivation range for zinc.
- **Prevention:** Hot-dip galvanizing per ISO 1461 (minimum 85 μm). No additional measures needed.

### 2. Stainless Steel Screws ↔ Galvanized Frame

- **Contact:** Direct — screws pass through the galvanized web
- **Risk level:** LOW-MEDIUM
- **Analysis:** Stainless steel is cathodic to zinc. In theory, this drives accelerated zinc corrosion at the contact point. In practice, the mortar encasement eliminates continuous moisture (the electrolyte), and the zinc coating at the screw hole is a sacrificial area — the surrounding zinc protects it cathodically.
- **Prevention:** Use A2 (304) stainless steel screws. The screw head is covered by the clamping strip and mortar. No moisture path.

### 3. Chicken Wire ↔ Steel Frame

- **Contact:** Indirect — chicken wire is stapled over the mortar face, separated from the frame by 30+ mm of mortar
- **Risk level:** NONE
- **Analysis:** Both are galvanized steel. No galvanic potential difference. Separated by mortar layer. No issue.

### 4. Aluminum Mesh ↔ Steel Frame

- **Contact:** Indirect — aluminum mesh sits between chicken wire and mortar, separated from frame by 30+ mm
- **Risk level:** NONE
- **Analysis:** Aluminum is anodic to steel (it would corrode first in direct contact). But there is no direct metal-to-metal contact — the mortar layer provides complete electrical isolation.
- **Prevention:** Ensure aluminum mesh does not contact the steel frame directly during installation. The mortar layer handles this naturally.

### 5. Aluminum Mesh ↔ Chicken Wire (Galvanized Steel)

- **Contact:** Direct — mesh layers touch during installation
- **Risk level:** LOW
- **Analysis:** Some galvanic potential exists. But both are embedded in mortar after installation, eliminating the moisture path. The aluminum mesh is a thin sacrificial layer — even if some corrosion occurs at contact points, the structural chicken wire remains intact.
- **Prevention:** No action needed. The mortar encasement is sufficient.

### 6. Clamping Strip ↔ Frame Web

- **Contact:** Direct — clamping strip is bolted against the web through bamboo strips
- **Risk level:** NONE
- **Analysis:** Both are hot-dip galvanized mild steel. Same material, same coating. No galvanic potential.

### 7. Steel Frame ↔ Bamboo Strips

- **Contact:** Direct — bamboo strips rest against the galvanized web
- **Risk level:** LOW
- **Analysis:** Bamboo is not a metal — no galvanic corrosion possible. The concern is moisture wicking through the bamboo creating a persistent damp zone on the steel. The mortar encasement eliminates this by sealing the interface. The borate treatment also reduces moisture absorption.

## Environmental Factors

### Coastal Environments (< 1 km from sea)

Salt-laden air accelerates zinc consumption dramatically. In coastal environments:
- Increase galvanizing thickness to 120+ μm
- Use 316L stainless steel screws (instead of 304)
- Consider additional epoxy coating on frame before galvanizing
- Expected frame life in coastal zone: 40–60 years (vs 80–100 inland)

### High Rainfall (> 2,000 mm/year)

- Ensure adequate roof overhang (minimum 1.5 m) to keep rain off wall surfaces
- Lime plaster acts as sacrificial layer — renew every 10–15 years in high-rainfall zones
- Interior of wall (mortar-encased) is unaffected by rainfall

### Tropical Humidity

- Lime plaster's breathability is critical — it allows moisture to pass through rather than trapping it
- Do NOT seal the wall with paint or waterproof coating — this traps moisture and accelerates degradation
- The wall must breathe: lime wash only

## Summary

| Interface | Risk | Prevention | Maintenance |
|---|---|---|---|
| Steel frame in mortar | Low | Hot-dip galvanizing | None (inspect at 40 years) |
| SS screws in galv. frame | Low-Medium | A2 stainless, mortar encasement | None |
| Chicken wire to frame | None | Same material, mortar separation | None |
| Aluminum mesh to frame | None | Mortar isolation | None |
| Al mesh to chicken wire | Low | Mortar encasement | None |
| Clamping strip to frame | None | Same material | None |
| Steel to bamboo | Low | Borate treatment, mortar encasement | None |

**The system's corrosion protection relies on three layers: galvanizing (primary), mortar encasement (secondary), and lime plaster (tertiary/sacrificial). Failure of any single layer does not compromise the system.**
