jreuteler/bahareque-modular/en/12-climate-adaptation.md

# Climate Adaptation

The panel system was developed for the Colombian Andes (~2,000 m altitude, ~2,500 mm annual rainfall, 15–25°C year-round). This chapter documents adaptations for other climates.

## Climate Zones

### Tropical Humid (0–1,000 m, >2,000 mm rain, 25–35°C)

*Examples: Pacific coast Colombia, Amazon basin, Philippines, Indonesia, West Africa*

| Factor | Adaptation |
|---|---|
| **Rain** | Minimum 2.0 m roof overhang on all sides. Rain splashing off ground erodes lime plaster at the base — raise panel bottom 30–50 cm above grade on a concrete or stone plinth. |
| **Humidity** | Lime plaster is critical — it breathes. **Never** seal the wall with paint, acrylic render, or waterproof coating. Trapped moisture destroys both bamboo and steel. |
| **Insects** | Borate treatment of bamboo is non-negotiable. Increase borate concentration to 8–10% (vs standard 5%). Mortar encasement provides secondary protection. Termite barriers at foundation level. |
| **Fungal growth** | Lime wash is naturally antifungal. Reapply every 3–5 years in humid lowlands (vs 5–10 in highlands). Add copper sulfate at 1–2% to lime wash for additional fungal resistance. |
| **Heat** | The 85 mm mortar core provides excellent thermal mass — absorbs heat during the day, releases at night. Combine with cross-ventilation (window openings on opposite walls). |
| **Mortar mix** | Standard 1:4 cement:sand works well. Increase pozzolan content to 15% (reduces heat of hydration and improves long-term durability in wet conditions). |
| **Lime plaster** | Use hydraulic lime (NHL 3.5 or NHL 5) rather than air lime — it sets faster and resists rain better during application. |

### Tropical Highland (1,000–2,500 m, 1,500–2,500 mm rain, 12–25°C)

*Examples: Colombian Eje Cafetero, Ecuadorian Sierra, Ethiopian highlands, Kenyan highlands*

This is the **design climate** — no significant adaptations needed.

| Factor | Notes |
|---|---|
| **Rain** | 1.5 m overhang sufficient. 2.0 m for exposed facades. |
| **Temperature** | Thermal mass smooths day-night swings. No insulation needed. |
| **Humidity** | Moderate — lime plaster breathes adequately. |
| **Insects** | Standard borate treatment (5%). |
| **Lime wash** | Every 5–10 years. |
| **Mortar mix** | Standard 1:4 + 10% pozzolan. |

### Tropical Dry / Semi-Arid (0–1,500 m, <800 mm rain, 25–40°C)

*Examples: Caribbean coast Colombia, Northeast Brazil, Sahel, Northern India, parts of Mexico*

| Factor | Adaptation |
|---|---|
| **Rain** | Less concern. 1.0 m overhang sufficient. |
| **Heat** | Thermal mass is excellent here — walls absorb daytime heat and release at night. Light-colored lime wash reflects solar radiation. |
| **UV exposure** | Intense sun degrades lime wash faster. Reapply every 3–5 years. Consider deeper overhangs on sun-facing walls. |
| **Mortar curing** | Critical — dry air causes rapid moisture loss during curing. Cover panels with wet burlap and plastic for 7+ days. Cure in shade, never in direct sun. |
| **Dust** | Fine dust accumulates in lime plaster texture. Periodic wash with water keeps surfaces clean. |
| **Bamboo sourcing** | Guadua may not grow locally. Use alternative species (see [Materials](03-materials.md)) or import treated bamboo. |

### Subtropical (25–35° latitude, seasonal temperature variation, 800–1,500 mm rain)

*Examples: Southern Brazil, Northern Argentina, Southern China, Southeast USA, Northern India, South Africa*

| Factor | Adaptation |
|---|---|
| **Winter cold** | The mortar core provides thermal mass but not insulation. For climates with sustained cold (<5°C for weeks), add external insulation: 30–50 mm of wood fiber board or cork outside the lime plaster, with a breathable render over it. **Never** insulate on the interior — this traps moisture in the wall. |
| **Freeze-thaw** | If temperatures drop below 0°C, use hydraulic lime (NHL 5) for plaster. Air lime can suffer freeze-thaw damage before full carbonation. Mortar core (inside the wall) is protected by plaster and thermal mass — not at risk. |
| **Seasonal rain** | Standard overhang. Ensure base of wall is raised above grade and protected from splash. |
| **Bamboo species** | Guadua angustifolia does not grow above ~30° latitude. Use *Phyllostachys* species (Moso, P. bambusoides) — smaller diameter, wider strips needed. See [Materials](03-materials.md). |

### Coastal (any latitude, <2 km from sea)

*Examples: Caribbean islands, Pacific coast, Mediterranean coast, Southeast Asian coast*

| Factor | Adaptation |
|---|---|
| **Salt air** | Dramatically accelerates zinc corrosion. Increase galvanizing to 120+ μm. Use 316L stainless steel screws (not 304). Consider additional epoxy primer on frames before galvanizing. |
| **Wind** | High wind zones require the steel frame configuration (not frameless). Design building frame for local wind code. Panel racking resistance contributes to overall building stiffness. |
| **Humidity + salt** | Lime wash every 3–5 years. Inspect plaster annually for salt crystallization damage (efflorescence). Brush off salt deposits before re-washing. |
| **Corrosion** | Expected frame life in coastal zone: 40–60 years (vs 80–100 inland). At 40 years, inspect and re-galvanize exposed steel if needed. See [Corrosion Prevention](06-corrosion-prevention.md). |
| **Storm surge / flooding** | Raise floor level well above flood line. Panels survive brief immersion (mortar is water-resistant) but prolonged submersion degrades embedded bamboo. Design for elevated construction. |

## Mortar Mix Adjustments by Climate

| Climate | Cement:Sand | Pozzolan | PP Fiber | W/C Ratio | Curing |
|---|---|---|---|---|---|
| Tropical humid | 1:4 | 15% | Standard | 0.45 | 7 days, covered |
| Tropical highland (default) | 1:4 | 10% | Standard | 0.45–0.50 | 7 days, moist |
| Tropical dry | 1:4 | 10% | Standard | 0.50 | 10 days, wet burlap + plastic, shade |
| Subtropical (cold winters) | 1:3.5 | 10% | Standard | 0.45 | 7 days; do NOT pour if temp <5°C |
| Coastal | 1:4 | 15% | Standard | 0.45 | 7 days; use fresh water only, no sea sand |

## Lime Plaster Adjustments

| Climate | Lime type | Mix | Fiber | Maintenance interval |
|---|---|-----|---|---|
| Tropical humid | NHL 3.5 or NHL 5 | 1:2.5 | Grass fiber | Every 3–5 years wash |
| Tropical highland | NHL 3.5 or air lime | 1:3 | Optional | Every 5–10 years wash |
| Tropical dry | Air lime or NHL 3.5 | 1:3 | Grass fiber (crack prevention) | Every 3–5 years wash (UV) |
| Subtropical | NHL 5 | 1:2.5 | Grass fiber | Every 5–7 years wash |
| Coastal | NHL 5 | 1:2.5 | Grass fiber | Every 3–5 years (salt) |

## Roof Overhang Summary

The single most important climate adaptation — protecting the wall from rain:

| Climate | Minimum overhang | Notes |
|---|---|---|
| Tropical humid | 2.0 m | Non-negotiable. Heavy rain + wind-driven spray. |
| Tropical highland | 1.5 m | Standard. 2.0 m on exposed facades. |
| Tropical dry | 1.0 m | Sun protection more important than rain. |
| Subtropical | 1.5 m | Rain protection + summer shade. |
| Coastal | 2.0 m | Rain + wind-driven salt spray. |

## Bamboo Species by Climate Zone

| Climate zone | Recommended species | Notes |
|---|---|---|
| Tropical Americas (0–2,000 m) | *Guadua angustifolia* | Strongest. Abundant in Colombia, Ecuador, Central America. |
| Tropical SE Asia | *Dendrocalamus asper*, *Bambusa bambos* | Large diameter. Direct substitute for guadua. |
| Tropical South Asia | *Bambusa bambos*, *Dendrocalamus strictus* | Widely available. D. strictus is denser but smaller. |
| Tropical Africa | *Bambusa vulgaris*, *Oxytenanthera abyssinica* | B. vulgaris is introduced but common. O. abyssinica is native. |
| Subtropical / Temperate | *Phyllostachys edulis* (Moso), *P. bambusoides* | Smaller diameter — use wider, thinner strips. |
| Temperate cool | Limited bamboo options | Consider importing treated bamboo strips, or substitute with other natural fibers/laths. |
