jreuteler/bahareque-modular/en/13-bamboo-treatment.md

# Bamboo Treatment Protocol

Untreated bamboo is eaten by powder-post beetles and degraded by fungi within 1–5 years in tropical climates. Proper treatment extends bamboo life to **decades** — and when encased in mortar inside a panel, to **80+ years**.

This chapter covers borate treatment — the safest, cheapest, and most effective method for bamboo used in construction.

## Why Borate

| Property | Borate | CCA (chromated copper arsenate) | Creosote |
|---|---|---|---|
| Toxicity to humans | Very low (borax is used in soap) | High (arsenic, chromium) | High (carcinogenic) |
| Insect protection | Excellent | Excellent | Excellent |
| Fungal protection | Good | Excellent | Excellent |
| Cost | Very low | Moderate | Moderate |
| Environmental | Safe, water-soluble | Toxic waste | Toxic waste |
| Suitability for bamboo | Excellent (penetrates well) | Poor (bamboo resists oil-based) | Poor |
| Compatibility with mortar | Excellent (no chemical reaction) | Unknown | Incompatible |

**Borate is the clear choice for bamboo in construction.** It is non-toxic, cheap, effective, and compatible with the mortar encasement that provides secondary long-term protection.

## Borate Solution Preparation

### Materials

| Material | Quantity per 100 liters | Notes |
|---|---|---|
| Borax (sodium tetraborate, Na₂B₄O₇·10H₂O) | 3 kg | Available at agricultural supply stores, pharmacies, or industrial chemical suppliers |
| Boric acid (H₃BO₃) | 2 kg | Same sources as borax |
| Water | 100 liters | Clean, potable. Warm water (40–50°C) dissolves faster. |

This produces a **~5% borate solution** (by weight of dissolved solids). For high-insect-pressure environments (tropical humid lowlands), increase to 4 kg borax + 3 kg boric acid per 100 L for an **~7% solution**.

### Mixing

1. Heat 20 liters of water to 50–60°C (hot but not boiling)
2. Add borax, stir until fully dissolved (~5 minutes)
3. Add boric acid, stir until dissolved (~5 minutes)
4. Add remaining 80 liters of room-temperature water
5. Stir well. Solution should be clear or slightly cloudy.
6. Solution is ready to use immediately.

**Shelf life:** Indefinite if stored in a closed container. Borate does not degrade.

## Treatment Methods

### Method 1: Tank Soaking (simplest, recommended for strips)

Best for: split bamboo strips (the form used in this panel system).

1. **Prepare strips:** Split and clean bamboo. Remove any remaining inner membrane (soft tissue). Strips should be ~20 mm wide, 2,500 mm long.
2. **Build or find a tank:** A simple trough from concrete blocks and plastic sheet, a PVC pipe cut lengthwise, or a purchased livestock water trough. Must hold strips fully submerged.
3. **Submerge strips completely** in borate solution. Weigh down with stones or a bamboo lattice if they float.
4. **Soak for 5–7 days** at room temperature. Borate diffuses into the bamboo tissue. Thinner strips (like the 20 mm strips used here) absorb faster than whole culms.
5. **Remove and dry.** Stack strips on a rack in shade with air circulation. Dry for 3–7 days until moisture content drops below 15%.
6. **Visual check:** Treated bamboo often shows a slight greenish or bluish tint from the borate. This is normal and confirms penetration.

**Solution reuse:** The same tank of solution can be used for multiple batches. Top up with fresh solution as the level drops (bamboo absorbs some). Test concentration with a borate test kit if available, or replace every 5–6 batches.

**Capacity:** A 3 m × 0.5 m × 0.3 m trough holds ~450 liters and treats ~200 strips per batch — enough for ~4 panels.

### Method 2: Modified Boucherie (for whole culms before splitting)

Best for: treating whole guadua culms before splitting into strips. Faster penetration through the vascular system.

1. **Harvest fresh bamboo** (within 24 hours of cutting — sap flow must still be active)
2. **Cut culm to length.** Pierce all internal diaphragms (nodes) with a steel rod.
3. **Attach a rubber cap or hose** to the base end of the culm, connected to a raised tank of borate solution (gravity-fed, 2–3 m elevation difference).
4. **Solution flows through the culm** via the vascular bundles, pushed by gravity. The borate-rich solution displaces the natural sap and exits from the top end as light-colored drips.
5. **Treatment time:** 3–5 days for a 6 m culm. Complete when the dripping liquid from the top tests positive for borate (use turmeric indicator — turns red in borate).
6. **Remove, dry, and split** into strips after treatment.

**Advantages:** More uniform penetration than soaking. Works for thick-walled culms where soaking would take weeks. Preserves sap-path moisture channels that aid borate distribution.

**Disadvantages:** Requires fresh-cut bamboo (not dried). Requires elevated tank and hose setup. Not practical for already-split strips.

### Method 3: Spray/Brush (emergency only, not recommended)

Surface application of borate solution by spraying or brushing. Penetration is limited to 1–3 mm. **Not adequate for structural bamboo.** Use only as a temporary measure if tank soaking is not available, and re-treat properly at the first opportunity.

## Quality Control

### Penetration Test

After treatment and drying, test a sample strip:

1. Cut a cross-section from the middle of a treated strip
2. Apply **turmeric solution** (dissolve 1 teaspoon turmeric powder in 50 ml rubbing alcohol)
3. Brush onto the cut cross-section
4. Borate-treated wood turns **red/dark orange** on contact with turmeric
5. Untreated wood remains **yellow**

The entire cross-section should turn red — confirming full penetration. If the center remains yellow, increase soak time for the next batch.

### Retention Test (advanced)

For formal quality control, send treated samples to a lab for borate retention analysis (target: >4 kg BAE/m³ — boric acid equivalent per cubic meter of bamboo). This level is sufficient for all wood-boring insects and most fungal species.

## Safety

- **Borate is low-toxicity.** Borax is used in commercial cleaning products. Boric acid is used in eye wash solutions. Neither is classified as hazardous at the concentrations used.
- **Wear gloves** when handling concentrated solution (mild skin irritant with prolonged contact).
- **Do not drink the solution.** Borate is mildly toxic if ingested in quantity (comparable to table salt). Keep away from children and animals.
- **Do not discharge used solution into waterways.** Borate can affect aquatic organisms at high concentrations. Dispose of used solution by applying it to the ground away from water sources (the boron is a plant micronutrient at low concentrations).

## Treatment Summary for This Panel System

| Bamboo component | Treatment method | Soak time | Concentration |
|---|---|---|---|
| Vertical strips (20 mm × 2,500 mm) | Tank soak | 5–7 days | 5% (standard) or 7% (humid lowland) |
| Diagonal strips (60 × 20 mm × 2,690 mm) | Tank soak | 7–10 days (thicker) | 5–7% |
| Whole culms (before splitting) | Modified Boucherie | 3–5 days | 5% |

After treatment and drying, bamboo is ready for panel assembly. The borate provides primary insect/fungal protection. The mortar encasement provides secondary protection — creating an alkaline, anaerobic environment hostile to biological degradation.

**Combined protection lifespan: 80+ years.**
