jreuteler/bahareque-modular/it/12-adattamento-climatico.md

# Adattamento Climatico

Il sistema a pannelli è stato sviluppato per le Ande colombiane (~2.000 m di altitudine, ~2.500 mm di precipitazioni annue, 15–25°C tutto l'anno). Questo capitolo documenta gli adattamenti per altri climi.

## Zone Climatiche

### Tropicale Umido (0–1.000 m, >2.000 mm pioggia, 25–35°C)

*Esempi: costa pacifica colombiana, bacino amazzonico, Filippine, Indonesia, Africa occidentale*

| Fattore | Adattamento |
|---|---|
| **Pioggia** | Sporgenza minima del tetto 2,0 m su tutti i lati. La pioggia che rimbalza dal suolo erode l'intonaco di calce alla base — alzare il fondo del pannello 30–50 cm dal suolo su un basamento in calcestruzzo o pietra. |
| **Umidità** | L'intonaco di calce è fondamentale — respira. **Non sigillare mai** la parete con pittura, intonaco acrilico o rivestimento impermeabilizzante. L'umidità intrappolata distrugge sia il bambù che l'acciaio. |
| **Insetti** | Il trattamento con borato del bambù è imprescindibile. Aumentare la concentrazione del borato all'8–10% (contro il 5% standard). L'inglobamento nella malta fornisce una protezione secondaria. Barriere anti-termiti a livello delle fondazioni. |
| **Crescita fungina** | Il latte di calce è naturalmente antifungino. Riapplicare ogni 3–5 anni nelle pianure umide (contro 5–10 nelle zone montane). Aggiungere solfato di rame all'1–2% al latte di calce per una resistenza fungina aggiuntiva. |
| **Calore** | Il nucleo di malta da 85 mm fornisce un'eccellente massa termica — assorbe il calore durante il giorno, lo rilascia di notte. Combinare con ventilazione trasversale (aperture su pareti opposte). |
| **Miscela di malta** | La standard 1:4 cemento:sabbia funziona bene. Aumentare il contenuto di pozzolana al 15% (riduce il calore di idratazione e migliora la durabilità a lungo termine in condizioni umide). |
| **Intonaco di calce** | Usare calce idraulica (NHL 3.5 o NHL 5) anziché calce aerea — fa presa più velocemente e resiste meglio alla pioggia durante l'applicazione. |

### Tropicale d'Altitudine (1.000–2.500 m, 1.500–2.500 mm pioggia, 12–25°C)

*Esempi: Eje Cafetero colombiano, Sierra ecuadoriana, altipiani etiopi, altipiani kenioti*

Questo è il **clima di progetto** — non sono necessari adattamenti significativi.

| Fattore | Note |
|---|---|
| **Pioggia** | Sporgenza 1,5 m sufficiente. 2,0 m per facciate esposte. |
| **Temperatura** | La massa termica smussa le escursioni giorno-notte. Nessun isolamento necessario. |
| **Umidità** | Moderata — l'intonaco di calce traspira adeguatamente. |
| **Insetti** | Trattamento standard con borato (5%). |
| **Latte di calce** | Ogni 5–10 anni. |
| **Miscela di malta** | Standard 1:4 + 10% pozzolana. |

### Tropicale Secco / Semi-arido (0–1.500 m, <800 mm pioggia, 25–40°C)

*Esempi: costa caraibica colombiana, Nordest brasiliano, Sahel, India settentrionale, parti del Messico*

| Fattore | Adattamento |
|---|---|
| **Pioggia** | Minore preoccupazione. Sporgenza 1,0 m sufficiente. |
| **Calore** | La massa termica è eccellente qui — le pareti assorbono il calore diurno e lo rilasciano di notte. Il latte di calce chiaro riflette la radiazione solare. |
| **Esposizione UV** | Il sole intenso degrada il latte di calce più rapidamente. Riapplicare ogni 3–5 anni. Considerare sporgenze più profonde sulle pareti esposte al sole. |
| **Stagionatura della malta** | Critica — l'aria secca causa una rapida perdita di umidità durante la stagionatura. Coprire i pannelli con tela di juta bagnata e plastica per 7+ giorni. Stagionare all'ombra, mai al sole diretto. |
| **Polvere** | La polvere fine si accumula nella texture dell'intonaco di calce. Un lavaggio periodico con acqua mantiene le superfici pulite. |
| **Approvvigionamento bambù** | La guadua potrebbe non crescere localmente. Usare specie alternative (vedi [Materiali](03-materiali.md)) o importare bambù trattato. |

### Subtropicale (25–35° di latitudine, variazione stagionale della temperatura, 800–1.500 mm pioggia)

*Esempi: Brasile meridionale, Argentina settentrionale, Cina meridionale, Sud-est USA, India settentrionale, Sudafrica*

| Fattore | Adattamento |
|---|---|
| **Freddo invernale** | Il nucleo di malta fornisce massa termica ma non isolamento. Per climi con freddo prolungato (<5°C per settimane), aggiungere isolamento esterno: 30–50 mm di pannello in fibra di legno o sughero all'esterno dell'intonaco di calce, con un intonaco traspirante sopra. **Non isolare mai** sul lato interno — questo intrappola l'umidità nella parete. |
| **Gelo-disgelo** | Se le temperature scendono sotto 0°C, usare calce idraulica (NHL 5) per l'intonaco. La calce aerea può subire danni da gelo-disgelo prima della completa carbonatazione. Il nucleo di malta (dentro la parete) è protetto dall'intonaco e dalla massa termica — non a rischio. |
| **Pioggia stagionale** | Sporgenza standard. Assicurarsi che la base della parete sia rialzata dal suolo e protetta dagli schizzi. |
| **Specie di bambù** | La Guadua angustifolia non cresce oltre ~30° di latitudine. Usare specie *Phyllostachys* (Moso, P. bambusoides) — diametro minore, servono listelli più larghi. Vedi [Materiali](03-materiali.md). |

### Costiero (qualsiasi latitudine, <2 km dal mare)

*Esempi: isole caraibiche, costa pacifica, costa mediterranea, costa del Sud-est asiatico*

| Fattore | Adattamento |
|---|---|
| **Aria salmastra** | Accelera drasticamente la corrosione dello zinco. Aumentare la zincatura a 120+ μm. Usare viti in acciaio inossidabile 316L (non 304). Considerare un primer epossidico aggiuntivo sui telai prima della zincatura. |
| **Vento** | Le zone ad alto vento richiedono la configurazione con telaio in acciaio (non senza telaio). Progettare il telaio dell'edificio secondo il codice del vento locale. La resistenza al taglio dei pannelli contribuisce alla rigidezza complessiva dell'edificio. |
| **Umidità + sale** | Latte di calce ogni 3–5 anni. Ispezionare l'intonaco annualmente per danni da cristallizzazione dei sali (efflorescenza). Spazzolare i depositi di sale prima di ri-lavare. |
| **Corrosione** | Vita attesa del telaio in zona costiera: 40–60 anni (contro 80–100 nell'entroterra). A 40 anni, ispezionare e ri-zincare l'acciaio esposto se necessario. Vedi [Prevenzione della Corrosione](06-prevenzione-corrosione.md). |
| **Mareggiata / allagamento** | Alzare il livello del pavimento ben sopra la linea di piena. I pannelli sopravvivono a brevi immersioni (la malta è resistente all'acqua) ma l'immersione prolungata degrada il bambù incorporato. Progettare per costruzione sopraelevata. |

## Regolazioni della Miscela di Malta per Clima

| Clima | Cemento:Sabbia | Pozzolana | Fibra PP | Rapporto A/C | Stagionatura |
|---|---|---|---|---|---|
| Tropicale umido | 1:4 | 15% | Standard | 0,45 | 7 giorni, coperto |
| Tropicale d'altitudine (default) | 1:4 | 10% | Standard | 0,45–0,50 | 7 giorni, umido |
| Tropicale secco | 1:4 | 10% | Standard | 0,50 | 10 giorni, juta bagnata + plastica, ombra |
| Subtropicale (inverni freddi) | 1:3,5 | 10% | Standard | 0,45 | 7 giorni; NON gettare se temp <5°C |
| Costiero | 1:4 | 15% | Standard | 0,45 | 7 giorni; usare solo acqua dolce, no sabbia marina |

## Regolazioni dell'Intonaco di Calce

| Clima | Tipo di calce | Miscela | Fibra | Intervallo manutenzione |
|---|---|---|---|---|
| Tropicale umido | NHL 3.5 o NHL 5 | 1:2,5 | Fibra d'erba | Lavaggio ogni 3–5 anni |
| Tropicale d'altitudine | NHL 3.5 o calce aerea | 1:3 | Opzionale | Lavaggio ogni 5–10 anni |
| Tropicale secco | Calce aerea o NHL 3.5 | 1:3 | Fibra d'erba (prevenzione fessure) | Lavaggio ogni 3–5 anni (UV) |
| Subtropicale | NHL 5 | 1:2,5 | Fibra d'erba | Lavaggio ogni 5–7 anni |
| Costiero | NHL 5 | 1:2,5 | Fibra d'erba | Lavaggio ogni 3–5 anni (sale) |

## Riepilogo Sporgenza del Tetto

Il singolo adattamento climatico più importante — proteggere la parete dalla pioggia:

| Clima | Sporgenza minima | Note |
|---|---|---|
| Tropicale umido | 2,0 m | Imprescindibile. Pioggia forte + schizzi spinti dal vento. |
| Tropicale d'altitudine | 1,5 m | Standard. 2,0 m sulle facciate esposte. |
| Tropicale secco | 1,0 m | La protezione dal sole è più importante di quella dalla pioggia. |
| Subtropicale | 1,5 m | Protezione dalla pioggia + ombra estiva. |
| Costiero | 2,0 m | Pioggia + schizzi salini spinti dal vento. |

## Specie di Bambù per Zona Climatica

| Zona climatica | Specie raccomandata | Note |
|---|---|----|
| Americhe tropicali (0–2.000 m) | *Guadua angustifolia* | La più resistente. Abbondante in Colombia, Ecuador, America Centrale. |
| SE asiatico tropicale | *Dendrocalamus asper*, *Bambusa bambos* | Grande diametro. Sostituto diretto della guadua. |
| Asia meridionale tropicale | *Bambusa bambos*, *Dendrocalamus strictus* | Ampiamente disponibili. D. strictus è più denso ma più piccolo. |
| Africa tropicale | *Bambusa vulgaris*, *Oxytenanthera abyssinica* | B. vulgaris è introdotta ma comune. O. abyssinica è autoctona. |
| Subtropicale / Temperato | *Phyllostachys edulis* (Moso), *P. bambusoides* | Diametro minore — usare listelli più larghi e sottili. |
| Temperato freddo | Opzioni bambù limitate | Considerare l'importazione di listelli di bambù trattati, o la sostituzione con altre fibre naturali/assicelle. |
