jreuteler/bahareque-modular/it/13-trattamento-bambu.md

# Protocollo di Trattamento del Bambù

Il bambù non trattato viene divorato dai tarli e degradato dai funghi entro 1–5 anni nei climi tropicali. Un trattamento adeguato estende la vita del bambù a **decenni** — e quando inglobato nella malta all'interno di un pannello, a **80+ anni**.

Questo capitolo tratta il trattamento con borato — il metodo più sicuro, economico ed efficace per il bambù utilizzato in edilizia.

## Perché il Borato

| Proprietà | Borato | CCA (arsenato di rame cromato) | Creosoto |
|---|---|---|---|
| Tossicità per l'uomo | Molto bassa (il borace si usa nel sapone) | Alta (arsenico, cromo) | Alta (cancerogeno) |
| Protezione dagli insetti | Eccellente | Eccellente | Eccellente |
| Protezione dai funghi | Buona | Eccellente | Eccellente |
| Costo | Molto basso | Moderato | Moderato |
| Impatto ambientale | Sicuro, idrosolubile | Rifiuto tossico | Rifiuto tossico |
| Idoneità per il bambù | Eccellente (penetra bene) | Scarsa (il bambù resiste ai prodotti a base oleosa) | Scarsa |
| Compatibilità con la malta | Eccellente (nessuna reazione chimica) | Sconosciuta | Incompatibile |

**Il borato è la scelta chiara per il bambù in edilizia.** È non tossico, economico, efficace e compatibile con l'inglobamento nella malta che fornisce la protezione secondaria a lungo termine.

## Preparazione della Soluzione di Borato

### Materiali

| Materiale | Quantità per 100 litri | Note |
|---|---|---|
| Borace (tetraborato di sodio, Na₂B₄O₇·10H₂O) | 3 kg | Disponibile presso negozi di forniture agricole, farmacie o fornitori di prodotti chimici industriali |
| Acido borico (H₃BO₃) | 2 kg | Stesse fonti del borace |
| Acqua | 100 litri | Pulita, potabile. L'acqua calda (40–50°C) scioglie più velocemente. |

Questo produce una **soluzione di borato al ~5%** (in peso di solidi disciolti). Per ambienti ad alta pressione di insetti (pianure tropicali umide), aumentare a 4 kg di borace + 3 kg di acido borico per 100 L per una **soluzione al ~7%**.

### Miscelazione

1. Riscaldare 20 litri d'acqua a 50–60°C (calda ma non bollente)
2. Aggiungere il borace, mescolare fino a completo scioglimento (~5 minuti)
3. Aggiungere l'acido borico, mescolare fino a scioglimento (~5 minuti)
4. Aggiungere i restanti 80 litri d'acqua a temperatura ambiente
5. Mescolare bene. La soluzione dovrebbe essere limpida o leggermente torbida.
6. La soluzione è pronta per l'uso immediato.

**Durata di conservazione:** Indefinita se conservata in un contenitore chiuso. Il borato non si degrada.

## Metodi di Trattamento

### Metodo 1: Immersione in Vasca (il più semplice, raccomandato per i listelli)

Ideale per: listelli di bambù spaccato (la forma usata in questo sistema a pannelli).

1. **Preparare i listelli:** Spaccare e pulire il bambù. Rimuovere eventuali residui di membrana interna (tessuto molle). I listelli dovrebbero essere ~20 mm di larghezza, 2.500 mm di lunghezza.
2. **Costruire o trovare una vasca:** Una semplice vasca in blocchi di cemento e telo di plastica, un tubo in PVC tagliato longitudinalmente, o un abbeveratoio per bestiame acquistato. Deve consentire l'immersione completa dei listelli.
3. **Immergere completamente i listelli** nella soluzione di borato. Appesantire con pietre o un'intelaiatura di bambù se galleggiano.
4. **Immergere per 5–7 giorni** a temperatura ambiente. Il borato si diffonde nel tessuto del bambù. I listelli più sottili (come quelli da 20 mm usati qui) assorbono più velocemente dei culmi interi.
5. **Rimuovere e asciugare.** Impilare i listelli su una rastrelliera all'ombra con circolazione d'aria. Asciugare per 3–7 giorni fino a quando il contenuto di umidità scende sotto il 15%.
6. **Controllo visivo:** Il bambù trattato mostra spesso una leggera sfumatura verdastra o bluastra dal borato. Questo è normale e conferma la penetrazione.

**Riutilizzo della soluzione:** La stessa vasca di soluzione può essere usata per più lotti. Reintegrare con soluzione fresca man mano che il livello scende (il bambù ne assorbe una parte). Testare la concentrazione con un kit di analisi del borato se disponibile, o sostituire ogni 5–6 lotti.

**Capacità:** Una vasca di 3 m × 0,5 m × 0,3 m contiene ~450 litri e tratta ~200 listelli per lotto — sufficienti per ~4 pannelli.

### Metodo 2: Boucherie Modificato (per culmi interi prima della spaccatura)

Ideale per: trattare culmi interi di guadua prima della spaccatura in listelli. Penetrazione più rapida attraverso il sistema vascolare.

1. **Raccogliere bambù fresco** (entro 24 ore dal taglio — il flusso linfatico deve essere ancora attivo)
2. **Tagliare il culmo a misura.** Perforare tutti i diaframmi interni (nodi) con un'asta d'acciaio.
3. **Fissare un cappuccio di gomma o un tubo** all'estremità basale del culmo, collegato a un serbatoio sopraelevato di soluzione di borato (alimentazione a gravità, 2–3 m di dislivello).
4. **La soluzione fluisce attraverso il culmo** tramite i fasci vascolari, spinta dalla gravità. La soluzione ricca di borato sostituisce la linfa naturale e fuoriesce dall'estremità superiore come gocce chiare.
5. **Durata del trattamento:** 3–5 giorni per un culmo di 6 m. Completato quando il liquido che gocciola dall'alto risulta positivo al borato (usare indicatore alla curcuma — diventa rosso in presenza di borato).
6. **Rimuovere, asciugare e spaccare** in listelli dopo il trattamento.

**Vantaggi:** Penetrazione più uniforme rispetto all'immersione. Funziona per culmi a parete spessa dove l'immersione richiederebbe settimane. Preserva i canali vascolari che facilitano la distribuzione del borato.

**Svantaggi:** Richiede bambù appena tagliato (non essiccato). Richiede serbatoio sopraelevato e configurazione con tubi. Non pratico per listelli già spaccati.

### Metodo 3: Spruzzo/Pennello (solo emergenza, non raccomandato)

Applicazione superficiale della soluzione di borato per spruzzatura o a pennello. La penetrazione è limitata a 1–3 mm. **Non adeguato per bambù strutturale.** Usare solo come misura temporanea se l'immersione in vasca non è disponibile, e ri-trattare adeguatamente alla prima opportunità.

## Controllo Qualità

### Test di Penetrazione

Dopo il trattamento e l'asciugatura, testare un listello campione:

1. Tagliare una sezione trasversale dal centro di un listello trattato
2. Applicare **soluzione di curcuma** (sciogliere 1 cucchiaino di curcuma in polvere in 50 ml di alcol denaturato)
3. Spennellare sulla sezione trasversale tagliata
4. Il legno trattato con borato diventa **rosso/arancio scuro** al contatto con la curcuma
5. Il legno non trattato resta **giallo**

L'intera sezione trasversale dovrebbe diventare rossa — confermando la penetrazione completa. Se il centro resta giallo, aumentare il tempo di immersione per il lotto successivo.

### Test di Ritenzione (avanzato)

Per un controllo qualità formale, inviare campioni trattati a un laboratorio per l'analisi di ritenzione del borato (obiettivo: >4 kg BAE/m³ — equivalente di acido borico per metro cubo di bambù). Questo livello è sufficiente per tutti gli insetti xilofagi e la maggior parte delle specie fungine.

## Sicurezza

- **Il borato ha bassa tossicità.** Il borace è usato nei prodotti di pulizia commerciali. L'acido borico è usato nei colliri. Nessuno dei due è classificato come pericoloso alle concentrazioni utilizzate.
- **Indossare guanti** quando si maneggia la soluzione concentrata (leggero irritante cutaneo con contatto prolungato).
- **Non bere la soluzione.** Il borato è moderatamente tossico se ingerito in quantità (paragonabile al sale da cucina). Tenere lontano da bambini e animali.
- **Non scaricare la soluzione usata nei corsi d'acqua.** Il borato può colpire gli organismi acquatici ad alte concentrazioni. Smaltire la soluzione usata applicandola al terreno lontano da fonti d'acqua (il boro è un micronutriente per le piante a basse concentrazioni).

## Riepilogo del Trattamento per Questo Sistema a Pannelli

| Componente in bambù | Metodo di trattamento | Tempo di immersione | Concentrazione |
|---|---|---|----|
| Listelli verticali (20 mm × 2.500 mm) | Immersione in vasca | 5–7 giorni | 5% (standard) o 7% (pianure umide) |
| Listelli diagonali (60 × 20 mm × 2.690 mm) | Immersione in vasca | 7–10 giorni (più spessi) | 5–7% |
| Culmi interi (prima della spaccatura) | Boucherie modificato | 3–5 giorni | 5% |

Dopo il trattamento e l'asciugatura, il bambù è pronto per l'assemblaggio del pannello. Il borato fornisce la protezione primaria contro insetti e funghi. L'inglobamento nella malta fornisce la protezione secondaria — creando un ambiente alcalino e anaerobico ostile al degrado biologico.

**Durata della protezione combinata: 80+ anni.**
