jreuteler/bahareque-modular/BaharequeModular-DE.pdf

# BaharequeModular

## Offenes Paneelsystem aus vorgefertigten Modulen

Entworfen von Jan Reuteler janreuteler@icloud.com

Erstveröffentlichung — März 2026

Hardware: CERN-OHL-S v2 · Documentation: CC BY-SA 4.0

BaharequeModular — 1

# Inhalt

### 01 Designphilosophie

Ursprung in kolumbianischer Permakultur, traditionelle Techniken weltweit, der hybride Ansatz, Schönheit, 80–100 Jahre Lebensdauer, Gemeinschaftsproduktion,

Stand der Technik, Open Source

### 02 Paneel-Aufbau

Vollständige technische Spezifikation: T-Profil-Rahmen, HDPE-Blöcke, Bambusstreifen, )(-Profil, diagonale Aussteifung, Drahtbindungen, Elektrik, Mörtel,

Oberflächenschichten

### 03 Materialien

Stückliste pro Paneel, alternative Bambusarten, Stahlspezifikationen, HDPE-Alternativen, Mörtelmischung, Kalkputz

### 04 Bauprozess

Schritt-für-Schritt-Produktion: Rahmenfertigung, Klemmung, Diagonalaussteifung, Gitter, Rütteltisch-Mörtelverguss, Aushärtung, Montage, Qualitätscheckliste

### 05 Tragverhalten

Zwei Konfigurationen, Erdbeben-, Brand-, Wärme-, Schallschutz, konservative Tragfähigkeitsschätzungen in kg, Prüfplan

### 06 Korrosionsschutz

Galvanische Analyse aller Materialgrenzflächen, Umweltfaktoren, Wartungsplan

### 07 Gebäudeintegration

Stahlrahmen- und rahmenlose Konfiguration, Anschlussdetails, Fenster, Türen, Trennwände

### 08 Mitwirken

Projektstatus, Beiträge, Prüfungen, Übersetzung, Lizenzierung

### 09 Kostenschätzung

Materialkosten pro Paneel, Vergleich mit konventionellem Bau, Gesamthausschätzung

### 10 Umweltbilanz

CO₂-Fussabdruck, Vergleich, Weg zur Klimaneutralität, Wasser, Abfall

### 11 Transport & Handhabung

Tragehilfe, Lagerung, LKW-Beladung, Kranoptionen, Schadensreparatur

### 12 Klimaanpassung

Tropisch feucht, Hochland, trocken, subtropisch, Küste — Anpassungstabellen

### 13 Bambusbehandlung

Boratlösung, Tauchbad, Boucherie-Methode, Qualitätskontrolle, Sicherheit

### 14 Akustik-Upgrade

Schallschutz für lärmbelastete Wände: dichterer Mörtel, Lehmdämpfung, Doppelpaneel mit Faserfüllung

### 16 Bodenpaneel-Konzept

Bambus-Bogenträger: Druckbogen + Zugband + Mörtel, Nullstahl in der Spannweite, Konzept zur Validierung

# BaharequeModular — Designphilosophie

## Ursprung — Lernen durch Tun

Dieses System wurde nicht am Schreibtisch entworfen. Es entstand aus praktischer Erfahrung mit Permakultur- und Biokonstruktionskursen im ländlichen Kolumbien — Bauen mit Guadua, Mörtel mischen, Wände verputzen und aus erster Hand sehen, was funktioniert, was scheitert und warum.

In diesen Kursen lernt man die aussergewöhnlichen Eigenschaften natürlicher Materialien zu schätzen: die Stärke von Guadua-Bambus, die Atmungsaktivität von Kalk, den thermischen Komfort von Lehmwänden, die Schönheit handverarbeiteter Oberflächen. Man lernt aber auch die Grenzen kennen. Biokonstruktionsprojekte — so gut gemeint sie auch sind — kämpfen oft mit:

Haltbarkeit. Lehmwände erodieren bei starkem tropischem Regen. Unbehandelter Bambus wird innerhalb weniger Jahre von Insekten zerfressen. Gebäude, die Monate an Gemeinschaftsarbeit kosteten, beginnen innerhalb eines Jahrzehnts zu verfallen.

Erdbebensicherheit. Traditioneller Bahareque und Adobe schneiden bei Erdbeben schlecht ab, sofern sie nicht sorgfältig ingenieurmässig geplant werden. Die meisten gemeinschaftlich errichteten Projekte haben keinen Zugang zu Bauingenieuren. Das Erdbeben von Armenia 1999 in Kolumbien tötete über 1.000 Menschen — viele in unbewehrtem Mauerwerk und schlecht gebauten traditionellen Strukturen.

Baubewilligungen und Versicherung. In den meisten Ländern können Lehm- und Bambusgebäude nicht offiziell bewilligt oder versichert werden. Familien, die mit natürlichen Materialien bauen, haben oft keinen rechtlichen Schutz für ihr Heim.

Oberflächenqualität. Biokonstruktions-Workshops produzieren schöne Demonstrationswände. Aber die Skalierung auf ein ganzes Haus — mit konsistenten Oberflächen, integrierter Elektrik, Sanitärinstallation und einer Ausführung, die Jahren von Witterung standhält — ist eine andere Herausforderung. Viele Projekte wirken im Vergleich zu konventioneller Bauweise rau, was die Wahrnehmung verstärkt, dass «natürlich = schlechte Qualität» bedeute.

Reproduzierbarkeit. Jedes Biokonstruktionsprojekt hängt von den Fähigkeiten der anwesenden Bauarbeiter ab. Es gibt kein standardisiertes Paneel, keine Produktionslinie, keinen Qualitätssicherungsprozess. Wenn der erfahrene Baumeister geht, sinkt die Qualität.

Dies sind keine Fehler der Materialien oder der Philosophie — es sind Fehler des Systems um sie herum. Guadua ist in der Zugfestigkeit so stark wie Stahl. Kalkputz hat Gebäude über Jahrtausende geschützt. Das Problem sind nicht die Zutaten. Das Problem ist, dass niemand sie in ein wiederholbares, qualitätskontrolliertes, statisch berechnetes, baunormkonformes System verpackt hatte, das eine Gemeinschaft ohne Abhängigkeit von einem Meisterbauer produzieren kann.

Das ist es, was dieses Projekt zu lösen versucht.

## Das Problem

Die meisten «bezahlbaren Wohnungen» in Entwicklungsländern stehen vor einem schwierigen Zielkonflikt:

Traditionelle Bauweise (Bambus, Adobe, Flechtwerk) ist schön, atmungsaktiv, kulturell bedeutsam und nutzt lokale Materialien — aber sie bricht bei Erdbeben, verfällt bei starkem Regen und erhält selten Baubewilligungen oder Versicherungen.

Moderne Bauweise (Betonblock, Stahlbetonrahmen) erhält Bewilligungen und übersteht Erdbeben — ist aber teuer, erfordert spezialisierte Arbeitskräfte, sieht überall gleich aus und hat keinen Bezug zu Ort oder Kultur.

Das Ergebnis: Milliarden von Menschen leben in Gebäuden, die entweder strukturell versagen oder den Menschen, die darin leben, nicht gerecht werden.

•

•

•

•

•

•

•

## Eine weltweite Tradition

Dieses System steht auf den Schultern jahrtausendealten Bauwissens. Auf jedem Kontinent entwickelten Kulturen die Rahmen-Fachwerk-Bauweise — ein tragender Rahmen, gefüllt mit natürlichen Materialien. Diese Techniken entstanden unabhängig voneinander, weil sie funktionieren. Sie sind erdbebensicher, thermisch komfortabel, reparierbar und schön.

### Bahareque (Kolumbien, Ecuador, Mittelamerika)

Bambusrahmen (Guadua), gefüllt mit Lehm, Mörtel oder Flechtwerk. Die traditionelle Bauweise der kolumbianischen Eje-Cafetero-Region, von der UNESCO als Kulturerbe anerkannt. Bahareque-Gebäude überlebten das Erdbeben von Armenia 1999 weit besser als unbewehrtes Mauerwerk. Die Kaffee-Kulturlandschaft Kolumbiens — ein UNESCO-Welterbe — wird durch ihre Bahareque-Architektur definiert. Dieses Paneelsystem ist eine direkte Weiterentwicklung des Bahareque: gleiche Materialien, gleiche Philosophie, für moderne Leistungsanforderungen ausgelegt.

### Quincha (Peru, Chile, Argentinien)

Bambus- oder Rohrrahmen mit Lehmputz, seit vorkolumbischer Zeit verwendet. Limas Kolonialzentrum wurde nach dem Erdbeben von 1746 in Quincha wiederaufgebaut — die flexiblen Rahmen überlebten nachfolgende Erdbeben, die starre Mauerwerkgebäude zerstörten. Quincha wird im ländlichen Peru weiterhin verwendet und erlebt ein Wiederaufleben in nachhaltigen Architekturkreisen.

### Flechtwerk (weltweit — Europa, Afrika, Asien, Amerika)

Die älteste bekannte Bautechnik, über 6.000 Jahre alt. Geflochtene Stäbe (Flechtwerk), beschichtet mit Lehm oder Ton (Bewurf). Zu finden in mittelalterlichen englischen Cottages, westafrikanischen Gehöften, japanischen Tsuchikabe-Wänden und

mesoamerikanischen Bauten. Viele Flechtwerkgebäude in Europa stehen seit über 500 Jahren. Das Prinzip — ein Gitterwerk aus organischem Material, eingebettet in eine mineralische Matrix — ist genau das, was dieses Paneelsystem verwendet.

### Fachwerk / Colombage (Deutschland, Frankreich, Nordeuropa)

Holzrahmen mit Ausfachungen (Ziegel, Stroh oder Lehm). In Deutschland als Fachwerk bekannt, in Frankreich als Colombage, in England als Half-Timbering. Tausende Gebäude aus dem 14.–18. Jahrhundert stehen noch und werden heute bewohnt. Die

zentrale Erkenntnis: Der Rahmen trägt die Struktur, die Ausfachung sorgt für die Gebäudehülle. Dies ist dasselbe Prinzip wie beim Stahlrahmen + Bahareque-Paneel.

### Dhajji-Dewari (Kaschmir, Pakistan, Nordindien)

Holzrahmen mit Stein- oder Lehm-Ausfachung, verwendet in der seismischen Zone des Himalaya. Das Wort bedeutet «Flickenteppich-Wand» auf Kaschmirisch. Dhajji-Dewari-Gebäude überlebten das verheerende Erdbeben von Kaschmir 2005, während moderne Betonbauten zusammenbrachen. Die eng gesetzten Holzelemente und diagonalen Verstrebungen schaffen eine duktile, energieabsorbierende Struktur — dasselbe Prinzip wie die diagonalen Bambusstreben in diesem Paneelsystem.

### Gaiola Pombalina (Lissabon, Portugal)

Nach dem katastrophalen Erdbeben und Tsunami von Lissabon 1755 beauftragte der Marquis von Pombal ein neues Bausystem: einen Holzkäfig (Gaiola) mit diagonaler Verstrebung innerhalb von Mauerwerkswänden. Dies war der weltweit erste

ingenieurmässige Erdbebenbaustandard. Die diagonale Verstrebung — die Scherkräfte in Zugkräfte umwandelt — ist ein direkter Vorläufer der diagonalen Bambusstreifen in diesem Paneelsystem. Gebäude mit dem Pombalinischen Käfig überlebten nachfolgende Erdbeben über 250 Jahre lang.

### Bajareque (Honduras, El Salvador, Guatemala)

Mittelamerikanische Variante des Bahareque, unter Verwendung von lokalem Bambus oder Rohr mit Lehmfüllung. Bajareque erfährt erneutes Interesse, da Gemeinschaften erdbebensichere, bezahlbare Alternativen zum Betonblock suchen.

### Taquezal (Nicaragua)

Ähnlich wie Bahareque — Holz- oder Bambusrahmen, gefüllt mit Lehm-/Strohmischung. Traditionell in der nicaraguanischen

Kolonialarchitektur. Die historischen Zentren von León und Granada zeigen Taquezal-Bauweise.

### Tabique (Mexiko, Philippinen)

In Mexiko: Bambus- oder Rohrrahmen (Carrizo) mit Lehmputz, verbreitet in Oaxaca, Guerrero und Chiapas. Auf den Philippinen: Bambus-Rahmenwände (Tabique Pampanga), verwendet in Kolonialgebäuden. Beide zeigen die Universalität der Bambusrahmen-

Bauweise in tropischen Regionen.

### Tsuchikabe (Japan)

Traditionelle japanische Lehmwände, auf einem Bambusgitter (Komai) aufgebaut. Mehrere Schichten Erdputz werden über den

geflochtenen Bambus aufgetragen — grober Grundputz, Zwischenschicht und feiner Oberputz. Derselbe Schichtansatz (strukturelles Gitter + mineralische Ummantelung + feiner Putzabschluss), der in diesem Paneelsystem verwendet wird.

### Pau-a-Pique (Brasilien)

Brasilianisches Flechtwerk mit Holzpfählen (Paus), die mit Bambus oder Ranken geflochten und mit Erde verputzt werden.

Verbreitet im ländlichen Brasilien seit der Kolonialzeit. Bekannt für thermischen Komfort in Brasiliens unterschiedlichen Klimazonen.

Dieses Paneelsystem übernimmt die Kernerkenntnis aller dieser Traditionen — ein Gitterwerk aus organischem Material, eingebettet in eine mineralische Matrix, getragen von einem strukturellen Rahmen — und macht sie fit für moderne Leistungsanforderungen: verzinkter Stahl statt Rohholz, behandelter Bambus statt unbehandeltem Rohr, puzzolanischer Mörtel statt rohem Lehm, Schraubklemmung statt Seilbindung. Die Weisheit ist alt. Die Ausführung ist modern. Das Ergebnis hält 80–100 Jahre.

## Der hybride Ansatz

Dieses Paneelsystem löst den Zielkonflikt zwischen traditioneller und moderner Bauweise:

Traditionell, wo es sichtbar ist. Die Aussenfläche ist Kalkputz über Bambus und Mörtel — dieselben Materialien, die seit Jahrhunderten in Bahareque, Quincha, Flechtwerk und Tsuchikabe verwendet werden. Die Textur ist handgefertigt. Die Oberfläche atmet. Das Gebäude gehört zu seinem Ort.

Modern, wo es zählt. Im Inneren jedes Paneels befindet sich ein feuerverzinkter L-Winkel-Stahlrahmen, der für seismische Lasten ausgelegt ist. Dieser Rahmen ist unsichtbar, sobald das Paneel fertiggestellt ist. Er trägt die strukturelle Realität, während die traditionellen Materialien die menschliche Erfahrung tragen.

## Permakultur-Integration

Das System verkörpert Permakultur-Prinzipien:

Lokale Ressourcen nutzen: Guadua angustifolia wächst natürlich in den tropischen Regionen Lateinamerikas auf 0–2.000 m Höhe. Sie erreicht Ernteformat in 4–5 Jahren. Ein Hektar kann jährlich genug Guadua für Dutzende von Paneelen liefern.

Probleme in Lösungen verwandeln: Invasives Sternengras (Cynodon nlemfuensis), ein häufiges landwirtschaftliches Unkraut,

wird getrocknet, gehäckselt und als Faserverstärkung im Kalkputz verwendet. Das Entfernen der invasiven Art verbessert das Land; die Verwendung im Bau schliesst den Kreislauf.

Boden aufbauen, nicht Abfall erzeugen: Ausgehobener vulkanischer Ascheboden (Andisol) von Fundamenten wird zum Premium-Substrat für Hochbeete und Waldgarten-Terrassierung.

•

•

•

Für Nachfolge planen: Ein 80–100 Jahre haltbares Gebäude überdauert den Erbauer. Die nächste Generation erbt ein Heim, kein Neubauprojekt.

## Biokonstruktion — ingenieurmässig umgesetzt

Biokonstruktion ist keine Nostalgie. Sie ist die Erkenntnis, dass natürliche Materialien — Bambus, Kalk, Erde, Stein — physikalische Eigenschaften besitzen, mit denen moderne Materialien kaum mithalten können:

Kalkputz ist antimykotisch, atmungsaktiv, selbstheilend (Karbonatisierung füllt Mikrorisse) und schön. Keine Farbe nötig.

Guadua-Bambus hat eine Zugfestigkeit vergleichbar mit Baustahl, wächst ohne Bewässerung und bindet beim Wachsen CO₂.

Mörtel mit puzzolanischem Zusatz (Vulkanasche, Reishülsenasche oder Metakaolin) reduziert die Alkalität im Laufe der Zeit und verlängert die Lebensdauer eingebetteter organischer Materialien.

Der Stahlrahmen ersetzt diese Materialien nicht — er trägt sie. Der Rahmen übernimmt, was Bambus und Mörtel nicht können: konzentrierte Punktlasten, biegesteife Verbindungen und normkonforme seismische Widerstandsfähigkeit.

## Nicht nur bezahlbar — schön

Dies ist kein Kompromiss-System. Die fertige Wand — handgeglätteter Kalkputz über dichtem Mörtel — erzeugt eine Oberflächenqualität, die mit Bautechniken konkurriert, die 5–10× mehr kosten.

Kalkputz ist seit Jahrtausenden das Finish der Wahl für Paläste, Kathedralen und Luxusvillen. Dasselbe Material, das ein toskanisches Bauernhaus oder eine kolumbianische Hacienda bedeckt, bedeckt diese Paneele. Jede Wand hat die subtile Textur von Handarbeit — keine zwei Oberflächen sind identisch.

Kalkanstrich entwickelt eine Tiefe und Wärme, die Farbe nicht erreichen kann. Er interagiert zu jeder Tageszeit anders mit Licht. Er altert graziös — entwickelt eine Patina, statt abzublättern.

Die Wand ist massiv. Klopfen Sie daran — sie klingt und fühlt sich wie Stein an. Es gibt keinen hohlen Hohlraum, kein Gipskarton-Durchbiegen. Der 85 mm Mörtelkern verleiht der Wand eine Beständigkeit, die Leichtbauweise nicht nachahmen kann.

Keine sichtbaren Befestigungen, Fugen oder Nähte. Einmal verputzt, ist die Wand durchgehend. Niemand kann erkennen, wo ein Paneel endet und das nächste beginnt. Niemand kann erkennen, dass sich ein Stahlrahmen im Inneren befindet. Das Gebäude sieht aus und fühlt sich an wie traditionelles Mauerwerk.

Ein Gast in einem Hotel, das mit diesen Paneelen gebaut wurde, würde nicht wissen — und sich nicht darum kümmern —, dass die Wände in einer Werkstatt von einem Gemeinschaftsteam vorgefertigt wurden. Er würde glatten Putz sehen, solide Wände fühlen und ein Gebäude mit dem Charakter handgefertigter Baukunst erleben. Dass das Gebäude auch Erdbeben übersteht, 80–100 Jahre hält und zu einem Bruchteil der Kosten konventioneller Bauweise errichtet wurde, ist unsichtbar.

Das ist der Punkt: Bezahlbar und schön sind keine Gegensätze. Genau die Techniken, die die Kosten niedrig halten — Kalk statt Farbe, Mörtel statt Gipskarton, Bambus statt Stahlständer — sind die Techniken, die das schönste Ergebnis produzieren.

## Einmal bauen — 80–100 Jahre Lebensdauer

Ein Haus, das 15 Jahre hält, ist nicht bezahlbar. Es ist eine Schuldenfalle mit Dach.

Ein Haus, das 80–100 Jahre hält, wird einmal gebaut. Die Familie investiert einmal. Die Gemeinschaft baut einmal. Die Materialien werden einmal verbraucht. Alles danach ist Instandhaltung — Kalkanstrich alle 5–10 Jahre, Putzinspektion alle 15–20 Jahre.

Die Kosten pro Jahr eines 100-jährigen Gebäudes sind ein Bruchteil derer eines 15-jährigen Gebäudes, selbst wenn die anfänglichen Baukosten höher sind.

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
## Gemeinschaftsproduktion

Das Schraubklemmsystem wurde speziell für die Gemeinschaftsproduktion entwickelt:

Kein Schweissen erforderlich bei der Paneelmontage (Rahmen werden in einer Werkstatt vorgeschweisst, aber die Montage erfolgt nur mit Schrauben)

Kein Spezialwerkzeug — Bohrmaschine, Schraubenzieher, einfaches Handwerkzeug

Selbstjustierend — die Klemmleiste biegt sich, um natürliche Dickenunterschiede bei Guadua-Streifen auszugleichen

In Tagen erlernbar — ein Gemeinschaftsteam kann die Paneelproduktion in 2–3 Tagen Schulung erlernen

Produktionsrate — ein Team von 4–6 Personen mit 2 Rütteltischen produziert 3–4 Paneele pro Tag

## Bestehende Arbeiten und verwandte Systeme

Dieses Projekt existiert nicht im luftleeren Raum. Mehrere Systeme haben bambubasierte vorgefertigte oder ingenieurmässig berechnete Bauweisen erforscht. Wir bauen auf ihrer Arbeit auf und anerkennen ihre Beiträge.

### Engineered Bahareque — Sebastian Kaminski (Arup / INBAR)

Die meistzitierte akademische Arbeit zum modernen Bahareque. Kaminskis Design Guide for Engineered Bahareque Housing (https://www.researchgate.net/publication/311583390_Design_Guide_for_Engineered_Bahareque_Housing) (veröffentlicht mit INBAR und Fundación Redes) liefert die statische Grundlage für zementierte Bahareque-Wände — Guadua-Skelettrahmen mit Bambusmatte als Ausfachung, Drahtgitterverstärkung und Zementmörtelputz. Seine Arbeit liegt dem kolumbianischen Baucode NSR-10 für Bahareque Encementado (Kapitel G-1) zugrunde. Über 4.000 Häuser wurden in Kolumbien,

Costa Rica, Nepal, Ecuador, Peru, Mexiko, El Salvador und den Philippinen gebaut.

Wie sich dieses System unterscheidet: Kaminskis Ansatz ist Vor-Ort-Konstruktion — Wände werden auf der Baustelle von erfahrenen Handwerkern Schicht für Schicht aufgebaut. Die Ausführungsqualität hängt stark von der Verarbeitungsqualität ab. Unser System industrialisiert dies zu standardisierten vorgefertigten Paneelen: T-bar-Stahlrahmen (nicht Holz/Bambus), schraubgeklemmte Streifen (nicht genagelte Matten), Rütteltisch-Mörtelverguss (nicht handaufgetragen vor Ort) und integrierte Snap-Connect-Elektrik. Das Ziel ist gleichbleibende Qualität in Gemeinschafts-Produktionsgeschwindigkeit, mit einer fertigen Wandoberfläche, die für Wohn- und Gewerbegebäude geeignet ist.

### Cement Bamboo Frame Technology (CBFT) — BASE Bahay / Hilti Foundation

Das weltweit am stärksten skalierte Bambus-Bausystem: über 2.400 Wohneinheiten auf den Philippinen, in Nepal, Indien und Sri Lanka gebaut. CBFT verwendet behandelte Bambusrahmen mit Metallverbindungen, geflachten Bambus (Esterilla) als Ausfachung, Drahtgitter und Zementmörtel. Paneele werden in Werkstätten vorgefertigt. Ausgelegt für Taifunwinde bis 300 km/h und Erdbeben bis Magnitude 7–8. Angestrebte Lebensdauer: ~60 Jahre. Schulung über die Bamboo Academy.

Wie sich dieses System unterscheidet: CBFT verwendet Bambus/Holz als Rahmenstruktur. Unser System verwendet verzinkten L-Winkel-Stahl — mit höherer axialer Tragfähigkeit, längerer korrosionsgeschützter Lebensdauer (80–100 Jahre vs. 60) und einer gleichmässigen Klemmfläche für das Schraubsystem. CBFT enthält keine integrierte Elektrik. CBFT ist proprietär (schulungsbasierter Zugang); unser System ist Open Hardware.

BASE Bahay — Hilti Foundation (https://www.hiltifoundation.org/basebahaybamboo)
BASE Builds (https://base-builds.com/tag/cement-bamboo-frame-technology-2/)

### Bamboo Composite Shear Walls — Chinesische akademische Forschung

Neuere Forschung chinesischer Universitäten hat gesprühte Komposit-Mörtelwände mit originalen Bambusständern und diagonaler Bambusverebung getestet — strukturell die engste Übereinstimmung mit dem diagonalen Verstrebungskonzept unseres Paneels.

Quasi-statische zyklische Belastungstests zeigten gute Energiedissipation und duktiles Versagensverhalten mit diagonalen Streifen. Der Mörtel wird gesprüht statt rüttelvergossen, und es gibt keinen Stahlrahmen.

•

•

•

•

•

•

•

Wie sich dieses System unterscheidet: Unser Vor-Ort-Vertikalguss (oder alternativer Werkstatt-Rütteltisch-Verguss) erreicht eine vollständigere Mörtelfüllung (keine Hohlräume) ohne Sprühausrüstung. Der L-Winkel-Stahlrahmen fügt axiale Tragfähigkeit hinzu und bietet eine standardisierte Klemmfläche. Die chinesische Forschung liefert jedoch die beste veröffentlichte Validierung, dass diagonale Bambusverstrebung im Mörtelverbund strukturell funktioniert — wir bauen auf dieser Evidenz auf.

Diagonal bamboo strips seismic study (ScienceDirect) (https://www.sciencedirect.com/science/article/abs/pii/S2352710223020090)

### Housing NOW / Blue Temple — Myanmar

Modularer Bambuswohnungsbau mit ineinandergreifenden gewölbten gebündelten Bambusrahmen. 26 Häuser mit Gemeinschaftsarbeit für ~1.000 $ pro Einheit gebaut. Im März 2025 überstanden alle 26 ein Erdbeben der Stärke 7,7 ohne strukturelle Schäden — die eindrucksvollste reale seismische Validierung eines Bambus-Wohnungsbausystems bis heute.

Wie sich dieses System unterscheidet: Vollständig anderer struktureller Ansatz (gewölbter gebündelter Bambus, kein Mörtel, kein Stahl). Aber ihr Gemeinschafts-Produktionsmodell und die bewiesene Erdbeben-Überlebensfähigkeit sind eine starke Validierung

des seismischen Potenzials von Bambus. Wenn gebündelte Bambusbögen ein M7,7-Erdbeben überstehen, sollten mörtelumhüllte Bambusstreifen in einem Stahlrahmen mindestens ebenso gut abschneiden.

Housing NOW (https://www.housing-now.org/)

Dezeen — Blue Temple bamboo housing (https://www.dezeen.com/2025/12/30/blue-temple-housing-now-bamboo-housing-myanmar/)

### WikiHouse — UK

Open-Source-CNC-gefrästes Sperrholz-Bausystem. Creative-Commons-lizenzierte Baupläne auf GitHub. Gemeinschaftsmontiert. Nicht bambusbasiert, aber das nächste Modell dafür, wie ein Open-Source-Bausystem dokumentiert, lizenziert und verbreitet werden kann. WikiHouse zeigt, dass Open-Source-Bauen realisierbar ist.

Wie sich dieses System unterscheidet: Andere Materialien (Sperrholz vs. Bambus+Mörtel+Stahl), anderes Zielklima (gemässigt vs. tropisch), andere Produktionsmethode (CNC vs. Werkstatt). Aber WikiHouses Lizenzierungsansatz (CC-Dateien auf GitHub) und Gemeinschaftsmodell haben die Struktur dieses Repositories beeinflusst.

WikiHouse (https://www.wikihouse.cc/faq)

### Quincha Prefabricada — Peru

Vorgefertigte Quincha-Paneele — gesägte Holzrahmen, gefüllt mit geflochtenem Rundrohr in ineinandergreifenden Mustern (keine Nägel für die Ausfachung nötig), verputzt mit Lehm-Stroh-Mischung. Bauanleitungen öffentlich verfügbar (PREDES). Limas Kolonialzentrum wurde nach dem Erdbeben von 1746 in Quincha wiederaufgebaut — diese flexiblen Rahmen überlebten nachfolgende Erdbeben, die starres Mauerwerk zerstörten.

Wie sich dieses System unterscheidet: Quincha verwendet Holzrahmen (nicht Stahl), Lehmputz (nicht puzzolanischen Mörtel) und geflochtenes Rohr (nicht schraubgeklemmte Streifen). Keine integrierte Elektrik. Aber Quincha Prefabricada beweist, dass vorgefertigte Bambus-/Rohrpaneele mit Putzfüllung eine praktikable, erdbebensichere Bauweise sind — eine direkte genealogische Validierung des Ansatzes dieses Systems.

Quincha Prefabricada (ResearchGate) (https://www.researchgate.net/publication/270074951_Sistema_constructivo_Quincha_Prefabricada)
Manual Quincha Mejorada (PREDES) (https://www.predes.org.pe/wp-content/uploads/2017/11/manual_quincha_mejorada.pdf)

### Kolumbianische NSR-10 — Bahareque-Encementado-Norm

Kein System, sondern der regulatorische Rahmen: Der kolumbianische Erdbebencode NSR-10, Kapitel G-1 (vormals E-7), regelt die zementierte Bahareque-Bauweise. Jedes Gebäude, das dieses Paneelsystem in Kolumbien verwendet, würde auf diese Norm verweisen. Der Code erkennt Guadua-Rahmen + Bambusmatte + Drahtgitter + Zementmörtel als normkonforme Wandkonstruktion an.

Manual Bahareque Encementado (PDF) (https://www.desenredando.org/public/libros/2001/csrvbe/guadua_lared.pdf)

•

•

•

•

•

•

•

### Was in diesem System neu ist

Zur Klarstellung: Die folgenden Merkmale haben kein dokumentiertes Äquivalent in einem bestehenden System:

Merkmal | Status
Verzinkter L-Winkel-Stahlrahmen für Bambuspaneele (Standard-Lagerprofil) | Neuartig
Schraubklemmsystem (selbstjustierend bei Dickenvariation) | Neuartig
Rütteltisch-Mörtelverguss auf Sandbett | Neuartig
Integrierte 12V + 120V Snap-Connect-Elektrik | Neuartig
Open-Hardware-Lizenz (CERN-OHL-S) für Bambusbau | Neuartig
80–100 Jahre Auslegungslebensdauer für Bambus-Mörtel-Paneele | Neuartig (CBFT zielt auf 60)
)( Flex-Profil durch HDPE-Distanzblöcke | Neuartig
Diagonale Bambusverstrebung durch eckgekerbte Distanzblöcke | Neuartige Kombination

Dieses System ist eine Evolution, keine Erfindung aus dem Nichts. Es kombiniert bewährte Prinzipien aus Bahareque, Quincha, Fachwerk und Pombalinischer Bauweise mit moderner Ingenieurwissenschaft, Materialwissenschaft und Open-Source-Verbreitung.

## Open Source

Dieses System ist Open Source, weil:

Wohnen ist ein Menschenrecht. Das Wissen, sicheres, menschenwürdiges Obdach zu bauen, sollte kein Geschäftsgeheimnis sein.

Das System wird besser mit jeder Gemeinschaft, die damit baut. Ein Zimmermann in Manizales, ein Baumeister in Indonesien, ein Ingenieur in Nepal — jeder kann das Design verbessern und zurückgeben.

Patente auf Bautechniken schaffen künstliche Knappheit von Wissen. Die Veröffentlichung des Designs als Open Hardware schafft dauerhaften Stand der Technik, den niemand schliessen kann.

Die besten Bausysteme der Geschichte verbreiteten sich durch offenes Teilen — Volksarchitektur entwickelte sich über Jahrhunderte durch genau diesen Prozess. Wir machen es einfach mit Versionskontrolle.

Dieses Projekt steht unter CERN-OHL-S v2 (Hardware) und CC BY-SA 4.0 (Dokumentation). Das bedeutet: Alle Ableitungen müssen offen bleiben. Das Wissen bleibt frei, für immer.

1.

2.

3.

4.

# Paneelaufbau

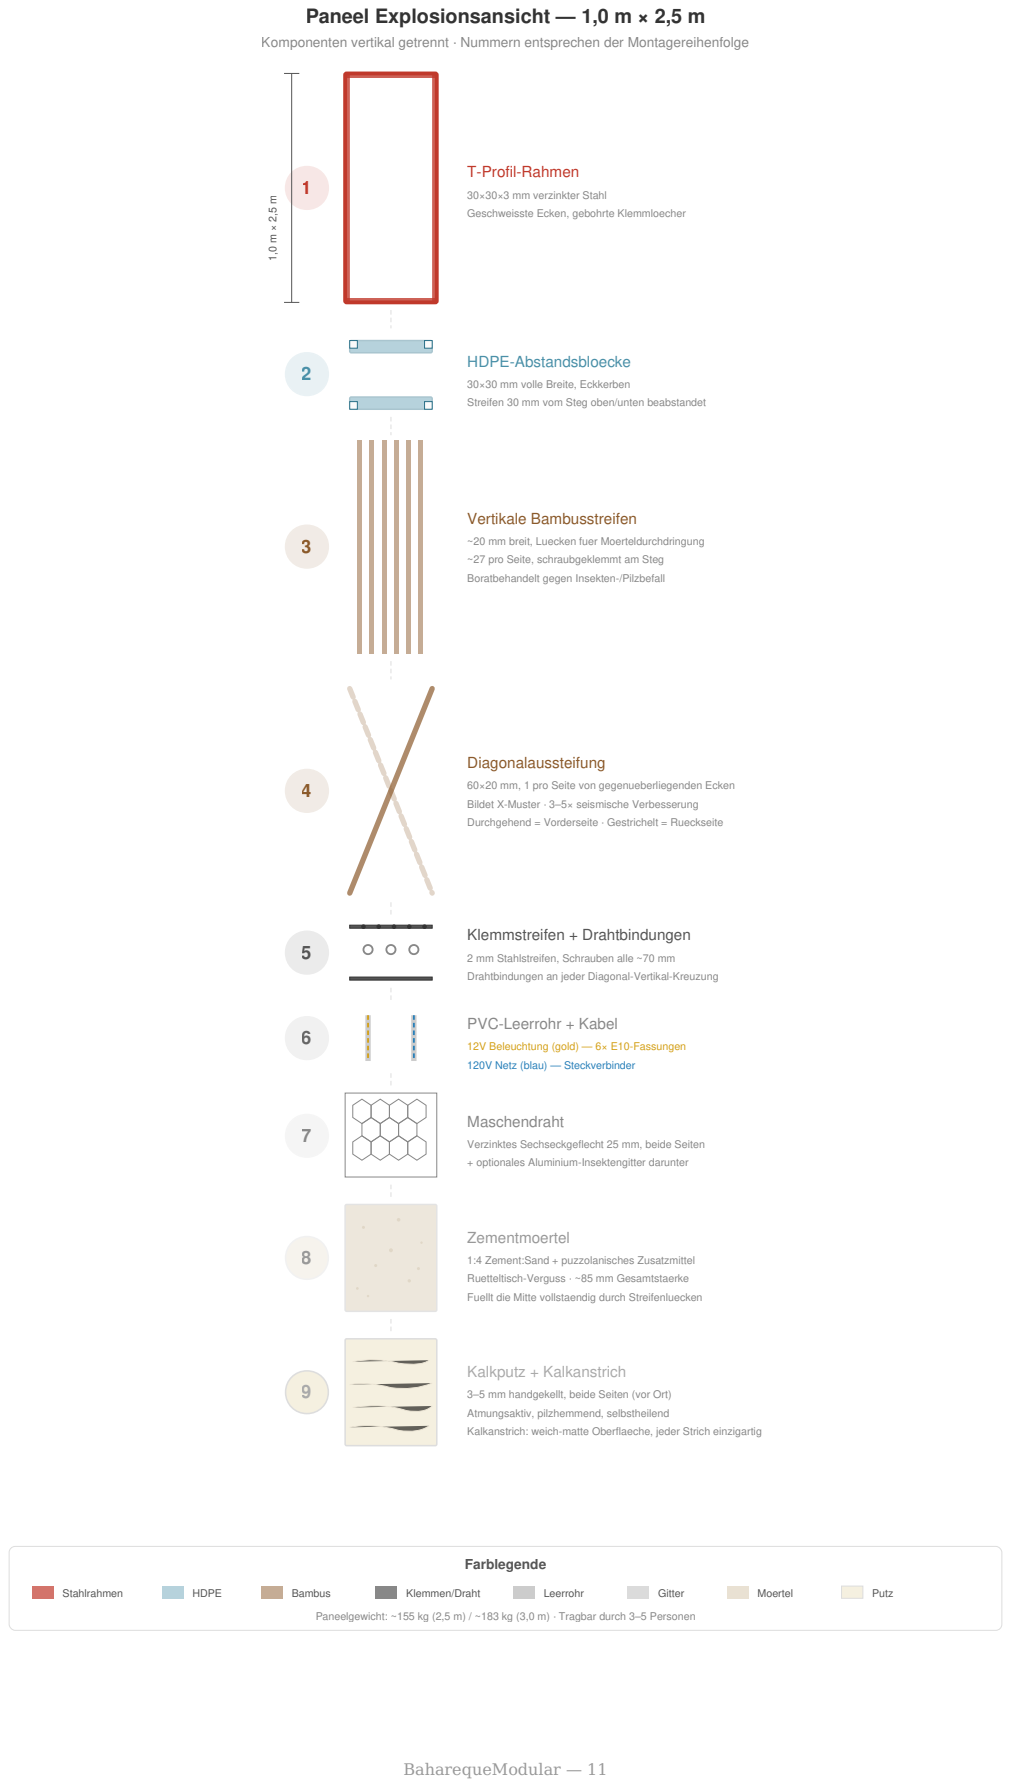
[picture p1: page 11]
Paneel Explosionsansicht — 1,0 m × 2,5 m; T-Profil-Rahmen; HDPE-Abstandsbloecke; Vertikale Bambusstreifen; Diagonalaussteifung; Klemmstreifen + Drahtbindungen; Maschendraht; Zementmoertel; Kalkputz + Kalkanstrich; Farblegende; Stahlrahmen; HDPE; Bambus; Klemmen/Draht; Leerrohr; Gitter; Moertel; Putz

Komponenten vertikal getrennt · Nummern entsprechen der Montagereihenfolge

30×30×3 mm verzinkter Stahl
Geschweisste Ecken, gebohrte Klemmloecher

30×30 mm volle Breite, Eckkerben
Streifen 30 mm vom Steg oben/unten beabstandet

~20 mm breit, Luecken fuer Moerteldurchdringung
~27 pro Seite, schraubgeklemmt am Steg
Boratbehandelt gegen Insekten-/Pilzbefall

60×20 mm, 1 pro Seite von gegenueberliegenden Ecken
Bildet X-Muster · 3–5× seismische Verbesserung
Durchgehend = Vorderseite · Gestrichelt = Rueckseite

2 mm Stahlstreifen, Schrauben alle ~70 mm
Drahtbindungen an jeder Diagonal-Vertikal-Kreuzung

PVC-Leerrohr + Kabel

12V Beleuchtung (gold) — 6× E10-Fassungen
120V Netz (blau) — Steckverbinder

Verzinktes Sechseckgeflecht 25 mm, beide Seiten
+ optionales Aluminium-Insektengitter darunter

1:4 Zement:Sand + puzzolanisches Zusatzmittel
Ruetteltisch-Verguss · ~85 mm Gesamtstaerke
Fuellt die Mitte vollstaendig durch Streifenluecken

3–5 mm handgekellt, beide Seiten (vor Ort)
Atmungsaktiv, pilzhemmend, selbstheilend
Kalkanstrich: weich-matte Oberflaeche, jeder Strich einzigartig

Paneelgewicht: ~155 kg (2,5 m) / ~183 kg (3,0 m) · Tragbar durch 3–5 Personen

SVG-Aktualisierung ausstehend: Einige Diagramme in diesem Kapitel werden von der früheren T-Profil-Spezifikation auf die aktuelle L 40×40×4 mm Winkelprofil-Spezifikation umgestellt. Einige T-Profil-spezifische SVGs wurden vorübergehend entfernt, bis sie neu erzeugt sind. Siehe SVG-STATUS.md im Repository-Stammverzeichnis für die vollständige SVG-Neuerzeugungsliste.

## Übersicht

Jedes Wandpaneel ist 1,0 m breit × 2,5 m hoch (Hochformat). Das Paneelgewicht hängt von der Produktionsphase ab: Eine Trockenmontage (Rahmen + Bambus + Gitter + Installationen, vor dem Mörtelguss) wiegt ungefähr ~75 kg und ist die Form, die von der Werkstatt zur Baustelle geliefert wird, um Mörtel vor Ort zu giessen. Sobald der Mörtel gegossen und ausgehärtet ist und die Vor-Ort-Oberflächen (Putz, Kalkanstrich) aufgebracht sind:

Basis-Gewicht der fertigen Wand: ungefähr ~440 kg pro Paneel (≈ 176 kg/m²) mit der dokumentierten Standardmischung (30 % Guadua-Anteil im Hohlraum + Zement-Sand-Mörtel + 10 mm Kalkputz auf beiden Seiten).

Optimierte Bahareque-Mischung: ungefähr ~360 kg pro Paneel (≈ 144 kg/m²) mit puzzolanischem Kalkmörtel mit Pasto-estrella-Fasern + 30 % Guadua + 5 mm Kalkputz auf beiden Seiten. Traditionelle kolumbianische Bahareque-Praxis auf das modulare System übertragen; leicht geringere graue Energie, etwas niedrigere Kosten, volle strukturelle Leistungsfähigkeit erhalten.

Jedes Paneel enthält integrierte Tragstruktur, Isolierung und Elektrosysteme. Eine Grösse. Vier Varianten.

Skalierbarkeit: Die 2,5 m Höhe eignet sich für Standardwohnraumhöhen weltweit. Das System skaliert auf jede Höhe — 3,0 m für hohe Decken, 2,7 m für Gewerberäume, 2,0 m für Trennwände. Nur die vertikalen L-Winkel und Bambusstreifen ändern die Länge. Die Rahmenlehre, das Klemmsystem, der Mörtelprozess und das Elektrolayout bleiben identisch.

## Rahmen: L-Winkel 40×40×4 mm

Rahmenprofil-Diagramm ausstehend — SVG-Neuerzeugung für L 40×40×4 noch nicht verfügbar. Siehe SVG-STATUS.md .

Der Paneelrahmen ist ein handelsüblicher L-Winkel (warmgewalztes gleichschenkliges Winkelprofil, ASTM A36 / ICONTEC-Äquivalent, feuerverzinkt):

Profil: L 40×40×4 mm (beide Schenkel 40 mm breit, 4 mm dick)

Ein Schenkel (Flansch): 40 mm × 4 mm — zeigt nach aussen, bündig mit der Mörteloberfläche

Anderer Schenkel (Steg): 40 mm × 4 mm — ragt nach innen, bietet strukturelle Tiefe und Klemmfläche für Bambusstreifen und Gitter

Wandstärke: ~85 mm (der L-Winkel-Steg sitzt im Mörtelkern, Mörtel füllt ~41 mm beiderseits der Stegebene)

Ecken: Auf Gehrung 45° geschnitten und in einer Lehre geschweisst — alle Rahmen identisch. Optionale Eckbleche für zusätzliche Steifigkeit

Klemmlöcher: Alle ~70 mm entlang der oberen und unteren Schenkel gebohrt (ein Loch pro zwei Bambusstreifen). Bambus-Klemmleisten (Flachstahl 40×3) werden an diesen Löchern verschraubt

Verfügbarkeit: Massenartikel, weltweit bei jedem grösseren Stahlhändler verfügbar. In Kolumbien: Gerdau Diaco, Aceros Arequipa, Acesco, Ferrasa, Colmena/Sidenal. In 6-m-Stangen vorrätig, mit Trennschleifer auf Mass geschnitten. Keine Sonderanfertigung, keine asymmetrischen Stege

Warum L-Winkel statt T-Profil: Strukturell gleichwertig für den dauerhaft im Mörtel eingebetteten Rahmen (siehe Tragverhalten), deutlich geringeres Stahlgewicht (~22 kg/Paneel gegenüber ~45 kg bei T 60×60×7), niedrigere Kosten, niedrigere graue CO₂-Emissionen und — entscheidend — als Lagermaterial verfügbar statt als bespoke asymmetrische

Anfertigung

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
Der Rahmen ist das strukturelle Rückgrat. Alles andere wird daran befestigt.

## HDPE-Distanzblöcke

Grösse: 30 × 30 mm Querschnitt, volle 1 m Breite

Position: Auf oberen und unteren L-Winkel-Stegen montiert (2 pro Paneel)

Funktion: Halten die Bambusstreifen oben und unten 30 mm vom Steg fern

Eckkerben: 10 × 10 mm Aussparungen an jeder Ecke verankern die Diagonalstreifen auf Steghöhe

Material: Recyceltes HDPE (aus Platte oder Rohr). Keine Fäulnis, keine Korrosion, formstabil

## Guadua-Vertikalstreifen

Material: Borat-behandelte Guadua angustifolia, in Streifen gespalten

Masse: ~20 mm breit × 2.500 mm lang

Abstand: ~20 mm Lücken zwischen den Streifen (Mörteldurchdringung)

Menge: ~27 Streifen pro Seite, ~54 total pro Paneel

Befestigung: Schraubgeklemmt an den L-Winkel-Steg oben und unten über Klemmleisten

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
## Frontansicht

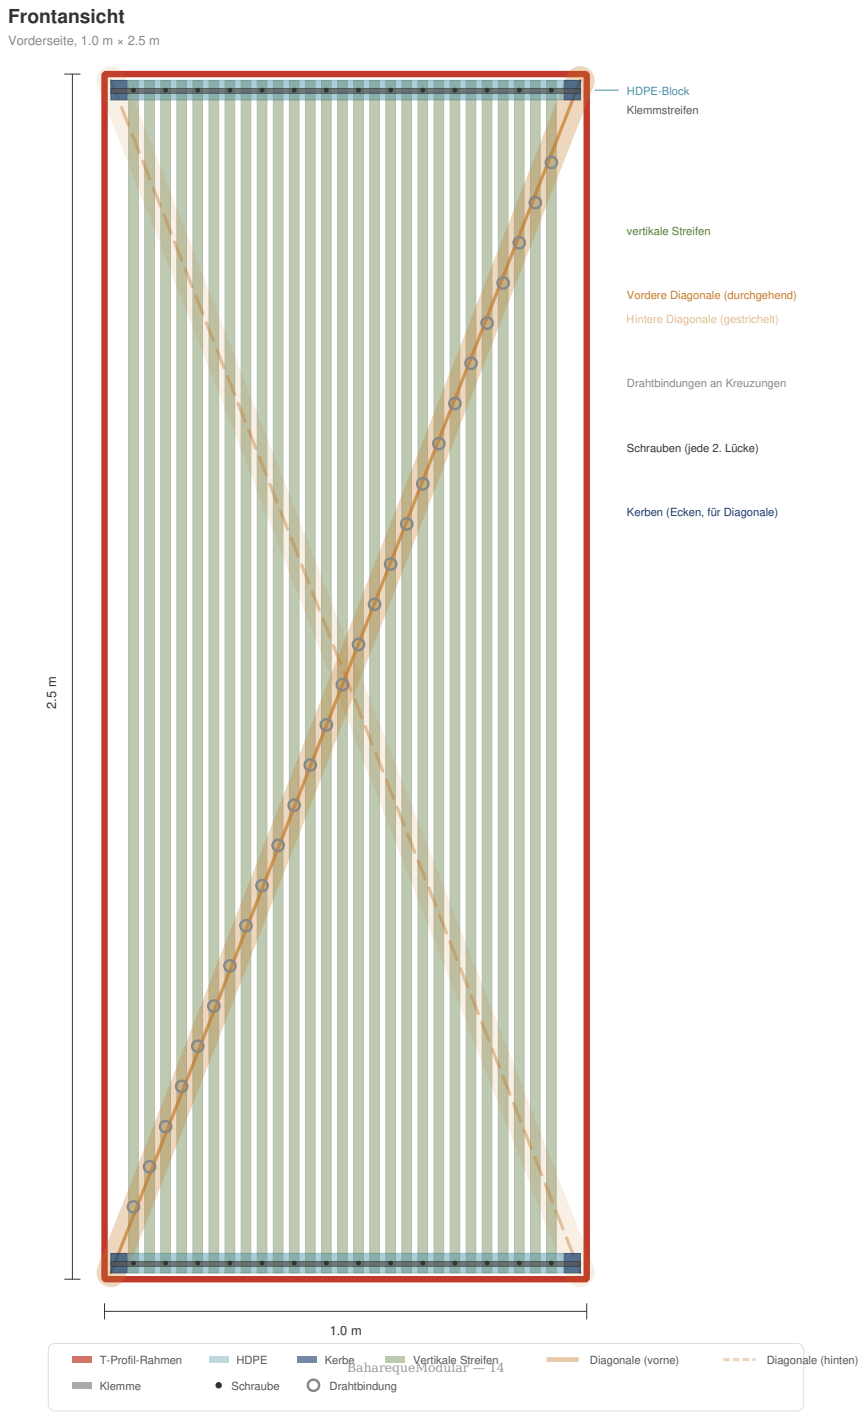
[picture p2: page 14]
Vorderseite, 1.0 m × 2.5 m; HDPE-Block; Klemmstreifen; vertikale Streifen; T-Profil-Rahmen; HDPE; Kerbe; Vertikale Streifen; Diagonale (vorne); Diagonale (hinten); Klemme; Schraube; Drahtbindung

Vordere Diagonale (durchgehend)

Hintere Diagonale (gestrichelt)

Drahtbindungen an Kreuzungen

Schrauben (jede 2. Lücke)

Kerben (Ecken, für Diagonale)

### Das )( Profil

## Seitenprofil

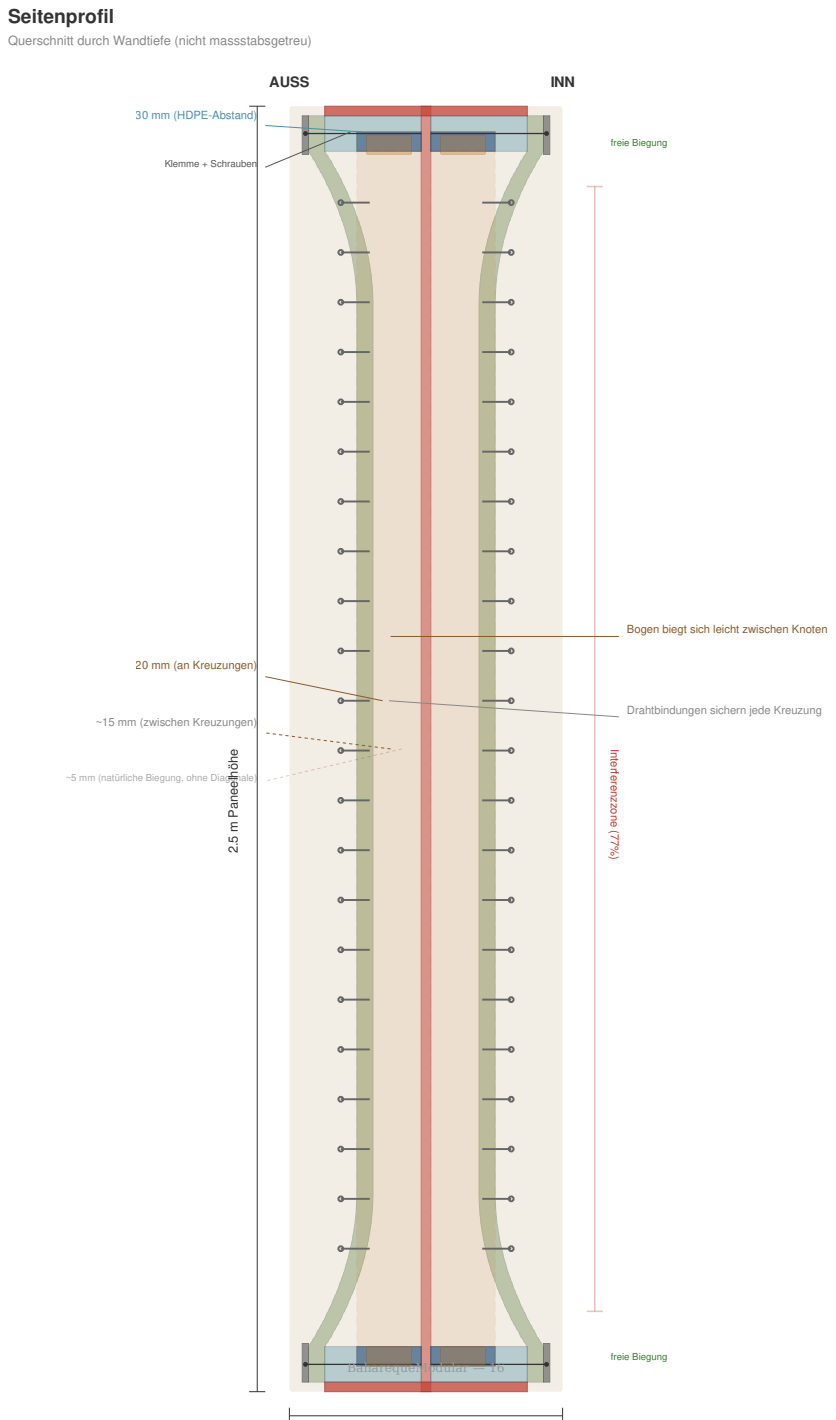
[picture p3: page 16]
AUSS; INN; freie Biegung; Klemme + Schrauben; 2.5 m Paneelhöhe

Querschnitt durch Wandtiefe (nicht massstabsgetreu)

30 mm (HDPE-Abstand)

Interferenzzone (77%) freie Biegung

Bogen biegt sich leicht zwischen Knoten

20 mm (an Kreuzungen)

~15 mm (zwischen Kreuzungen)

Drahtbindungen sichern jede Kreuzung

~5 mm (natürliche Biegung, ohne Diagonale)

Oben und unten halten die HDPE-Blöcke die Streifen 30 mm vom Steg entfernt. Auf halber Höhe biegen sich die Streifen natürlich nach innen zum Steg — wodurch ein )( Querschnittprofil entsteht. Das ist kein Fehler; es ist das Design:

Der Mörtel füllt den variierenden Spalt und erzeugt eine natürliche Bogenform

Der Bogen widersteht Kräften senkrecht zur Wandebene (Wind, Stoss)

Der Mörtel mit variabler Dicke verankert die Streifen mechanisch

## Bambus-Diagonalstreifen

Masse: 60 × 20 mm, ~2.690 mm lang (Ecke zu Ecke diagonal)

Menge: 1 pro Seite, von gegenüberliegenden Ecken (bildet ein X von vorne betrachtet)

Position: Verläuft auf Steghöhe, durch die HDPE-Block-Eckkerben gefädelt

Vorgespannt: Vor dem Befestigen stramm gezogen

Funktion: Wandelt seismische Scherkräfte in Zug in der Diagonale um. Bietet 3–5× Verbesserung der Schubsteifigkeit gegenüber Paneelen ohne Diagonalen.

### Drahtbindungen

Verzinkte Drahtbindungen an jeder Diagonal-Vertikal-Kreuzung (~8–10 pro Seite). Diese verriegeln die vertikalen und diagonalen Streifen zu einem starren Gitter, verteilen Punktlasten über die gesamte Paneelfläche und erzeugen ein duktiles Versagensmuster.

## PVC-Leerrohr

Grösse: 16 mm Standard-Elektroleerrohr

Position: Zwischen den Bambusstreifen, am Steg anliegend

Funktion: Schützt 12V- und 120V-Kabel vor Mörtel und Schraubendruck. Ermöglicht Kabelaustausch durch Einziehen neuer Leitungen, ohne das Paneel zu öffnen.

## Elektrosysteme

Jedes Paneel enthält zwei unabhängige Stromkreise:

### 12V Beleuchtung

2-adriges Kabel im PVC-Leerrohr

6× E10-Schraubfassungen (3 pro Seite) nahe dem oberen Paneelrand

Warmtonige Glüh- oder LED-Lampen (0,5–1W pro Stück) — Wandflutbeleuchtung

2-polige Snap-Stecker an beiden Vertikalkanten

### 120V Netz (je nach Variante)

3-adriges Kabel (L + N + PE) im PVC-Leerrohr

3-polige Snap-Stecker an beiden Vertikalkanten

Wenn Paneele nebeneinander verschraubt sind, rasten die Stecker zusammen = durchgehender Stromkreis

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
## Paneelvarianten

Typ | Anteil | Inhalt
P — Durchleitung | ~60% | 12V Beleuchtung + 120V Durchleitungskabel. Keine Steckdosen.
O — Steckdose | ~18% | 12V Beleuchtung + Doppelsteckdose auf ~40 cm Höhe
S — Schalter + Steckdose | ~9% | 12V Beleuchtung + Schalter auf ~120 cm + Steckdose auf ~40 cm
W — Wasser + Steckdose | ~13% | 12V Beleuchtung + Steckdose + Kalt-/Warmwasser-Steigleitungen + Grauwasserabfluss

Alle Varianten teilen denselben Rahmen, dieselbe Bambus-Ausfachung, denselben Mörtel. Nur die eingebetteten Installationen unterscheiden sich.

## Mörtel

Mischung: 1:4 Portlandzement : sauberer Flusssand

Zusätze: Polypropylenfaser (6–12 mm) zur Rissverhinderung in der Aushärtungsphase + puzzolanischer Zusatz (Vulkanasche, Reishülsenasche oder Metakaolin)

Auftrag: Verguss auf Rütteltisch (siehe Bauprozess)

Gesamte Wanddicke: ~85 mm (Mörtel + Guadua + Mörtel)

Das Puzzolan reduziert den Mörtel-pH-Wert über die Zeit und verlangsamt den Abbau des eingebetteten Bambus

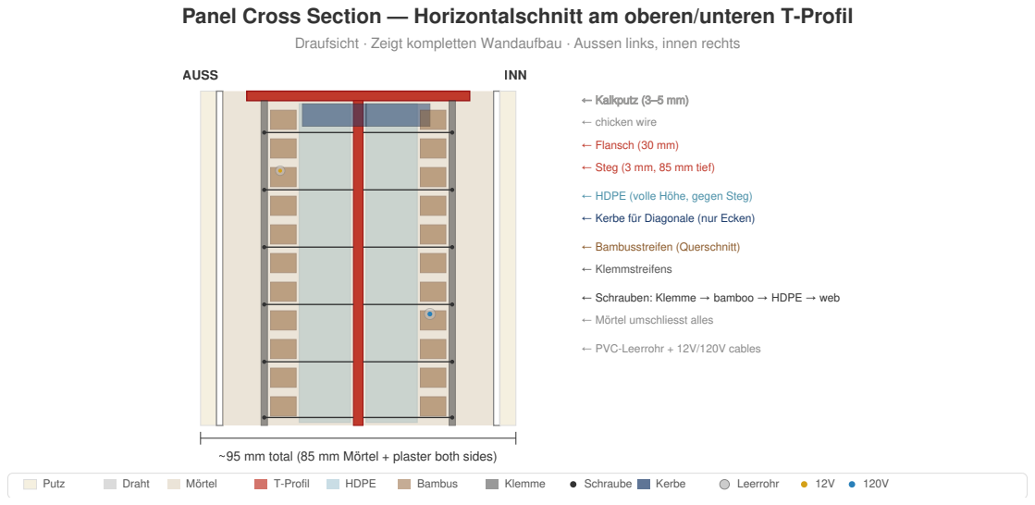
[picture p4: figure]
AUSS; INN; ← Kalkputz (3–5 mm); ← chicken wire; ← Flansch (30 mm); ← Steg (3 mm, 85 mm tief); ← HDPE (volle Höhe, gegen Steg); ← Kerbe für Diagonale (nur Ecken); ← Bambusstreifen (Querschnitt); ← Klemmstreifens; ← Mörtel umschliesst alles; ← PVC-Leerrohr + 12V/120V cables; Putz; Draht; Mörtel; T-Profil; HDPE; Bambus; Klemme; Schraube; Kerbe; Leerrohr

## Deckschichten (auf der Baustelle nach der Installation aufgetragen)

Hühnerdrahtgeflecht — verzinktes Sechseckgeflecht (25 mm Maschenweite), auf beide Seiten geklammert. Bietet mechanischen Verbund für die Mörtel-/Putzhaftung.

Feines Aluminiumgitter (optional) — Standard-Insekten-/Staubschutzgitter, 1–1,5 mm Maschenweite. Blockiert Insekten, Feinstaub und Pollen am Eindringen durch die Mörtelmatrix. Als sekundäre Eigenschaft bietet die Aluminiumschicht auch messbare Hochfrequenzdämpfung.

Kalkputz — 3–5 mm, handgeglättet. Atmungsaktiv, antimykotisch, selbstheilend. Optional: gehäckselte getrocknete Grasfaser für Rissbeständigkeit.

Kalkanstrich — Kalk + Wasser, mit Pinsel aufgetragen. Sanftes mattes Finish. Jeder Pinselstrich einzigartig.

•

•

•

•

•

Panel Cross Section — Horizontalschnitt am oberen/unteren T-Profil

Draufsicht · Zeigt kompletten Wandaufbau · Aussen links, innen rechts

← Schrauben: Klemme → bamboo → HDPE → web

~95 mm total (85 mm Mörtel + plaster both sides)

1.

2.

3.

4.

## Gewichtsaufschlüsselung (ungefähr)

Komponente | Gewicht
Stahlrahmen | ~18 kg
HDPE-Blöcke | ~1 kg
Bambusstreifen + Diagonalen | ~12 kg
Mörtel (85 mm × 1 m × 2,5 m) | ~120 kg
Draht, Gitter, Leerrohr, Kabel | ~6 kg
Total | ~155 kg

Tragbar von 3–4 Personen mit einer einfachen Tragelehre.

# Materialien

## Stückliste (pro Paneel)

Material | Spezifikation | Menge | Anmerkungen
L-Winkelstahl | L 40×40×4 mm, feuerverzinkt (ASTM A36 / ICONTEC NTC 2542 äquivalent) | 2× 1,0 m + 2× 2,5 m = 7,0 m | Kolumbianisches Lagermaterial (Gerdau Diaco, Aceros Arequipa, Acesco, Ferrasa). 6-m-Standardlängen, mit Trennschleifer geschnitten
Klemmleisten | 40×3 mm Flachstahl, verzinkt, passende Löcher | 4× 1,0 m = 4,0 m | Oben + unten, beide Seiten
Eckbleche + Schrauben | Flachblech-Verstärkungen + M12/M8 Schrauben | 1 Set | Steifere Eckverbindung anstelle reiner Schweissnaht
Schrauben | Edelstahl, selbstschneidend | ~28 pro Paneel | Durch Klemmleiste → Bambus → HDPE → Steg (alle ~70 mm, eine pro zwei Streifen)
HDPE-Blöcke | 30×30 mm Querschnitt, recycelt | 2× 1,0 m = 2,0 m | Auf oberen + unteren L-Winkel-Stegen
Bambusstreifen (vertikal) | Borat-behandelt, ~20 mm breit | ~54 Streifen × 2,5 m | ~27 pro Seite
Bambusstreifen (diagonal) | Borat-behandelt, 60×20 mm | 2× ~2,69 m | 1 pro Seite, gegenüberliegende Ecken
Verzinkter Draht | Bindedraht | ~5 m | ~16–20 Bindungen an Kreuzungen
PVC-Leerrohr | 16 mm Elektro | ~5 m | Kabelschutz
12V-Kabel | 2-adrig | ~6 m | Beleuchtungsstromkreis
120V-Kabel | 3-adrig (L+N+PE) | ~6 m | Netzstromkreis
E10-Fassungen | Schraubfassungen | 6 | 3 pro Seite
Snap-Stecker | 2-polig (12V) + 3-polig (120V) | 2 + 2 | An beiden Vertikalkanten
Hühnerdraht | Verzinktes Sechseckgeflecht, 25 mm | ~5,5 m² | Beide Seiten + Überlappung
Zementmörtel (Basis) | 1:4 Zement:Sand + Zusätze | ~0,147 m³ Netto-Hohlraum (nach 30 % Guadua + Stahlverdrängung) | ~310 kg nass / ~294 kg ausgehärtet (Dichte ~2 000 kg/m³)
Puzzolanischer Kalkmörtel mit Pasto estrella (optimiert) | Hydraulischer Kalk + 30 % Flugasche/RHA + Pasto-estrella-Fasern | ~0,147 m³ gleicher Hohlraum | ~270 kg nass / ~257 kg ausgehärtet (Dichte ~1 750 kg/m³)
PP-Faser | 6–12 mm gehäckselt | ~200 g | Rissverhinderung bei Aushärtung
Puzzolanischer Zusatz | Vulkanasche / Reishülsenasche / Metakaolin | ~2 kg | pH-Senkung, Dauerhaftigkeit

Kalkputz und Kalkanstrich werden auf der Baustelle nach der Paneelinstallation aufgetragen — sie sind nicht Teil des Paneels selbst.

## Materialdetails

### Strukturbambus

Das System verwendet gespaltene Struktur-Bambusstreifen als primäres Ausfachungsmaterial. Die Referenzart ist Guadua angustifolia (in Lateinamerika als Guadua bekannt, in Ecuador als Caña Guadua, in einigen Regionen als Tacuara) — der stärkste

Strukturbambus Amerikas. Jedoch kann jede grosskalibrige Struktur-Bambusart angepasst werden.

Schlüsseleigenschaften von Guadua angustifolia:

Zugfestigkeit: 150–200 MPa (vergleichbar mit Baustahl)

Wachstum: Erreicht Erntedurchmesser (10–15 cm) in 4–5 Jahren

Verbreitung: 0–2.000 m Höhe in den tropischen Amerikas (Kolumbien, Ecuador, Mittelamerika)

Ernte: Schnitt nach 4–6 Jahren (maximale Lignifizierung). Jüngere Halme sind zu weich; ältere werden spröde.

Behandlung: Boratlösung (Borax + Borsäure) nach modifizierter Boucherie-Methode oder Tauchen. Verhindert Insektenbefall und Pilzfäule. Ungiftig, wirksam für 20+ Jahre wenn in Mörtel eingebettet.

Alternativen für andere Regionen

Art | Region | Anmerkungen
Dendrocalamus asper | Südostasien | Grosser Durchmesser, stark. Direkter Ersatz.
Bambusa bambos | Süd-/Südostasien | Dornig, stark. Erfordert breitere Streifen.
Phyllostachys edulis (Moso) | China, gemässigte Zonen | Kleinerer Durchmesser. Breitere, dünnere Streifen verwenden.
Phyllostachys bambusoides | Japan, gemässigte Zonen | Gute Festigkeit. Kleinere Halme.
Guadua chacoensis | Argentinien, Paraguay | Naher Verwandter von G. angustifolia.

Das System funktioniert mit jedem Strukturbambus, der in Streifen gespalten werden kann. Passen Sie Streifenbreite und -abstand an die verfügbare Art an.

### Stahl-L-Winkelrahmen

Profil: L 40×40×4 mm gleichschenkliges Winkelprofil (ASTM A36 / ICONTEC NTC 2542)

Masse: ~2,42 kg/m; Paneelrahmen total ~17 kg + ~4 kg Klemmleisten + ~1 kg Eckbleche/Verbindungselemente = ~22 kg pro Paneel

Verzinkung: Feuerverzinkt nach ISO 1461, mindestens 85 μm Zinkbeschichtung

Lebensdauer: 80–100 Jahre in nicht-küstennahen tropischen Umgebungen bei der angegebenen Zinkdicke (der Paneeldienst ist innerhalb der alkalischen Mörtelmatrix kontinuierlich abgestützt, die freiliegenden Stahl selbst passiviert)

Beschaffung: Massenartikel weltweit. In Kolumbien: Gerdau Diaco, Aceros Arequipa, Acesco, Ferrasa, Colmena/Sidenal, Perfilamos del Cauca. Lagerware in 6-m-Längen bei praktisch jedem Stahlbauhändler. Keine Sonderbestellung, keine Sonderanfertigung, keine asymmetrischen Stege

Alternative Profile: L 50×50×4 oder L 50×50×5 (etwas schwerer, ebenfalls Lagerware) sind direkte Ersatzprofile. SHS (quadratisches Hohlprofil) 40×40×2 funktioniert strukturell ebenfalls, erfordert aber Klemmleisten, die geschweisst statt durch den Steg geschraubt werden

Warum nicht T-Profil: Frühere Versionen dieses Dokuments spezifizierten T 60×60×7 mm (~45 kg pro Paneel). Kontinuierlich abgestützter Paneeldienst erfordert nicht den symmetrischen Steg des T-Profils — ein einseitiger L-Winkel-Steg ist strukturell gleichwertig bei etwa der halben Stahlmasse, halben Kosten und dramatisch besserer Verfügbarkeit. Offene T-Profile bleiben nur dort die richtige Wahl, wo Schwachachs-Knickwiderstand wichtig ist (z. B. freistehende Stützen — geschlossenes Vierkantrohr wird in diesem System bevorzugt gegenüber T-Profil).

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
### HDPE-Distanzblöcke

Quelle: Recycelte HDPE-Schneidbretter, Rohrabschnitte oder Plattenmaterial

Eigenschaften: Keine Wasseraufnahme, fäulnissicher, formstabil, leicht zu bearbeiten

Bearbeitung: Tischkreissäge oder Bandsäge zum Zuschneiden. Oberfräse oder Stemmeisen für Eckkerben.

Alternativen zu HDPE

Material | Vorteile | Nachteile
Recyceltes HDPE (bevorzugt) | Fäulnissicher, keine Wasseraufnahme, weit verbreitet aus Abfallstrom | Erfordert Schneidwerkzeuge
Marine-Hartholz (Teak, Ipe, Greenheart) | Stark, natürlich fäulnisbeständig, leicht zu bearbeiten | Teuer, degradiert dennoch über Jahrzehnte in feuchter Umgebung
Behandeltes Weichholz (CCA- oder Borat-behandelte Kiefer) | Günstig, weit verbreitet | Kürzere Lebensdauer (20–40 Jahre), muss evtl. ersetzt werden
Dichte Gummiblöcke (recycelter Reifengummi) | Fäulnissicher, stossabsorbierend, gratis aus Altreifen | Schwieriger präzise zu bearbeiten, kann sich über Zeit komprimieren
Beton-/Mörtelblöcke | Keine Kosten, in Formen gegossen, permanent | Spröde, schwieriger für Diagonalkerben, schwer
3D-gedruckte Blöcke (PETG oder ASA) | Präzise Geometrie inkl. Kerben, reproduzierbar | Erfordert 3D-Drucker, UV-Degradation bei Exposition

Die kritische Anforderung ist: Der Block muss sein 30-mm-Mass über die Gebäudelebensdauer beibehalten, um das )( Streifenprofil zu erhalten. HDPE erfüllt dies am besten, aber jedes Material, das feuchtigkeits- und druckbeständig ist, funktioniert.

### Mörtel

Basismischung: 1 Teil Portlandzement Typ I : 4 Teile sauberer Flusssand (gut abgestuft, 0–4 mm)

PP-Faser: 200 g pro Paneel (~1 kg pro m³). Verhindert plastische Schwindrisse bei der Aushärtung.

Puzzolanischer Zusatz: 5–10% Zementersatz.

Vulkanasche — verfügbar in Andenregionen, natürlich puzzolanisch

Reishülsenasche (RHA) — verfügbar in Reisanbaugebieten (Asien, Lateinamerika)

Metakaolin — verarbeiteter Kaolinton, weltweit verfügbar aber teurer

Funktion: Reagiert mit Calciumhydroxid im Zement, senkt den pH-Wert von ~12,5 auf ~10–11 über die Zeit. Dies verlangsamt den Abbau eingebetteter Guadua.

Wasser: Sauber, trinkbar. W/Z-Wert ~0,45–0,50 für giessfähige Konsistenz auf dem Rütteltisch.

### Kalkputz (vor Ort)

Typ: Hydraulischer Kalk (NHL 3.5 oder NHL 5) oder gelöschter Kalk (Sumpfkalk) + Sand

Mischung: 1:2,5 bis 1:3 Kalk:Sand

Optionale Faser: Gehäckseltes getrocknetes Gras (Sternengras, Sisal, Hanf) bei ~1 cm Länge. Erhöht Zugfestigkeit und Rissbeständigkeit. Natürliche Zellulose hält 30+ Jahre in Kalk (pH ~10, viel weniger aggressiv als Zement).

Auftrag: Handgeglättet, 3–5 mm. Die Textur ist die Schönheit — maschinenperfekt ist nicht das Ziel.

### Kalkanstrich (vor Ort)

Gelöschter Kalk + Wasser, mit Pinsel in dünnen Schichten aufgetragen

Dringt ein und verbindet sich chemisch mit dem Kalkputz (Karbonatisierung)

Alle 5–10 Jahre erneuern zur Instandhaltung

Kann mit natürlichen Pigmenten (Erdoxiden) eingefärbt werden

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
### Hühnerdraht

Verzinktes Sechseckgeflecht, 25 mm Maschenweite, 0,7–0,9 mm Draht

Auf die Paneelfläche geklammert oder gebunden vor dem Mörtelauftrag

Bietet mechanischen Verbund für Mörtelhaftung

Beide Seiten

### Feines Aluminiumgitter (optional)

Standard-Insekten-/Staubschutzgitter, 1–1,5 mm Maschenweite, Aluminium

Unter dem Hühnerdraht auf beiden Seiten platziert

Blockiert Insekten, Feinstaub und Pollen am Eindringen durch die Mörtelmatrix

Als sekundäre Eigenschaft bietet es auch messbare Hochfrequenzdämpfung

Nicht erforderlich für die strukturelle Funktion — je nach lokalen Insekten-/Staubverhältnissen hinzufügen

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
# Bauprozess

SVG-Aktualisierung ausstehend: Einige Diagramme in diesem Kapitel wurden für die frühere T-Profil-Rahmenspezifikation erzeugt und sind vorübergehend entkoppelt, bis sie für die aktuelle L 40×40×4 mm Winkel-Spezifikation neu erzeugt sind. Siehe SVG-STATUS.md im Repository-Stammverzeichnis.

## Werkstatteinrichtung

Alle Paneele werden in einer überdachten Werkstatt gebaut — wetterunabhängig, qualitätskontrolliert, fliessbandeffizient. Mindestanforderungen an die Werkstatt:

Überdachte Fläche: ~6 × 4 m (Dach, offene Seiten akzeptabel)

Schweissstation (nur für Rahmenfertigung)

Ständerbohrmaschine oder Handbohrmaschine

2× Rütteltische (~1,2 × 2,7 m pro Stück) für das Werkstatt-Verguss-Produktionsmodell, oder Schalung + Vor-Ort-Mörtelpumpe für das bevorzugte Vor-Ort-Verguss-Modell (siehe Paneelaufbau § Gewichtsaufschlüsselung)

Sandvorrat für Bett

Mörtelmischer (elektrisch oder von Hand)

Einfaches Handwerkzeug: Schraubenzieher, Drahtschneider, Zangen, Klammergerät

•

•

•

•

•

•

•

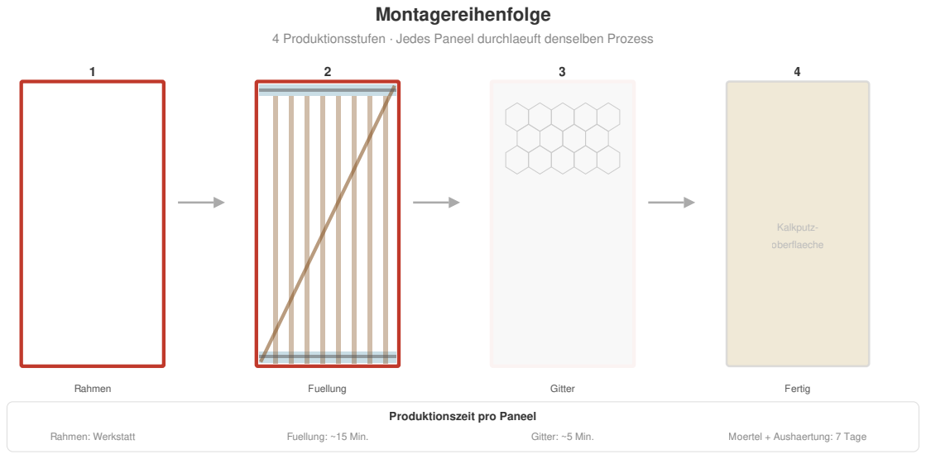
[picture p5: figure]
Montagereihenfolge; Rahmen; T-Profil geschweisst + verzinkt; Loecher gebohrt; Fuellung; Bambus + Diagonalen; Geklemmt + verdrahtet; Kabel im Leerrohr; Gitter; Maschendraht beidseitig; (+ optionales Al-Gitter); Bereit fuer Moertel; Kalkputz-; oberflaeche; Fertig; Moertel gegossen + ausgehaertet; Kalkputz + Kalkanstrich; ~155 kg, einbaubereit; Produktionszeit pro Paneel; Rahmen: Werkstatt; Fuellung: ~15 Min.; Gitter: ~5 Min.; Moertel + Aushaertung: 7 Tage

4 Produktionsstufen · Jedes Paneel durchlaeuft denselben Prozess

## Produktionsschritte

### Schritt 1: Rahmenfertigung

Wandpaneel-Rahmen-Diagramm ausstehend — die frühere Rahmen-SVG zeigt T-Profil-Geometrie und ist nicht repräsentativ für den L-Winkelrahmen. Siehe SVG-STATUS.md .

L 40×40×4 Winkel auf Länge schneiden: 2× 1,0 m (oben/unten) + 2× 2,5 m (Seiten). Lagermaterial von Gerdau Diaco / Acesco / Ferrasa, 6-m-Stangen

Ecken auf 45° auf Gehrung schneiden (oder gerade schneiden mit einem Schenkel über dem anderen — beides ergibt einen sauberen rechteckigen Rahmen)

Ecken in einer Lehre schweissen — alle Rahmen identisch. Optionale kleine Eckbleche (60×60×3 Blech) können über jede Innenecke geschweisst werden für Steifigkeit beim Handhaben

Klemmlöcher alle ~70 mm entlang der oberen und unteren Winkel-Stege bohren (eines pro zwei Bambusstreifen, ~14 Löcher pro Leiste, ~28 total)

Den fertigen Rahmen feuerverzinken (Chargenprozess — 20–50 Rahmen auf einmal versenden)

Alle Rahmen sind identisch, unabhängig von der Paneelvariante. Die Lehre gewährleistet konsistente Masse. Eine Lehre, ein Rahmen, für immer.

### Schritt 2: HDPE-Blöcke

HDPE-Material auf 30 × 30 mm × 1.000 mm zuschneiden (2 pro Paneel)

Eckkerben schneiden: 10 × 10 mm an jedem Ende (4 Kerben pro Block, 8 pro Paneel)

Blöcke auf obere und untere L-Winkel-Stege montieren mit Schrauben oder Klebstoff

### Schritt 3: Elektrik

12V-Kabel durch PVC-Leerrohr führen

120V-Kabel durch separates PVC-Leerrohr führen

E10-Fassungen montieren (3 nahe am oberen Rand, jede Seite)

Für Typ O/S: Steckdosendose montieren, Anschlusskabel zum Hauptkabel

Für Typ S: Schalterdose auf 120 cm Höhe montieren

Für Typ W: Wasser-Steigleitungen montieren (CPVC/PEX-Versorgung, PVC-Abfluss) mit verschlossenen Anschlussstutzen

Snap-Stecker an beiden Vertikalkanten anbringen (2-polig für 12V, 3-polig für 120V)

### Schritt 4: Bambusstreifen (Seite 1)

Paneelrahmen flach auf Arbeitstisch legen, Seite 1 nach oben

Vertikale Bambusstreifen gegen den Steg legen, zwischen den HDPE-Blöcken

~20 mm Lücken zwischen den Streifen lassen für Mörteldurchdringung

PVC-Leerrohr mit Kabeln zwischen die Streifen legen, am Steg anliegend

Diagonalstreifen durch die untere linke HDPE-Kerbe fädeln, quer zur oberen rechten Kerbe (auf Steghöhe)

Diagonale vorspannen und an beiden Enden sichern

Schraubklemm-Diagramm ausstehend — die frühere Klemm-SVG zeigt T-Profil-Steggeometrie; das L-Winkel-Klemmdetail ist im Prinzip ähnlich (Klemmleiste → Bambus → Schraube durch Steg), aber geometrisch anders. Siehe SVG-STATUS.md .

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
### Schritt 5: Schraubklemmung (Seite 1)

Stahl-Klemmleiste (Flachstahl 3 mm × 40 mm × 1.000 mm) über die Bambusstreifen am oberen Winkel-Steg legen

Löcher in der Klemmleiste mit Löchern im L-Winkel-Steg ausrichten

Edelstahlschrauben eindrehen durch: Klemmleiste → Bambusstreifen → Steglöcher

Die Klemmleiste biegt sich, um natürliche Dickenvariation auszugleichen — selbstjustierend

Am unteren Winkel wiederholen

Diagonale an jeder Vertikalstreifen-Kreuzung mit Draht binden (~8–10 Bindungen)

Zeit: ~5 Minuten pro Seite für die Klemmung, ~3 Minuten für die Drahtbindungen

### Schritt 6: Wenden und wiederholen (Seite 2)

Paneel wenden

Schritte 4–5 auf der anderen Seite wiederholen

Diagonale auf Seite 2 verläuft von oben links nach unten rechts (gegenüber der Diagonalen auf Seite 1 — zusammen bilden sie ein X)

### Schritt 7: Gitter

Hühnerdraht über Seite 1 legen, 20 mm über den Rahmenrand hinausragend (für Überlappung mit benachbarten Paneelen)

Am Rahmen und an den Bambusstreifen klammern oder binden

Bei Verwendung von Aluminium-Insektengitter: unter dem Hühnerdraht platzieren

Wenden und auf Seite 2 wiederholen

### Schritt 8: Mörtelverguss

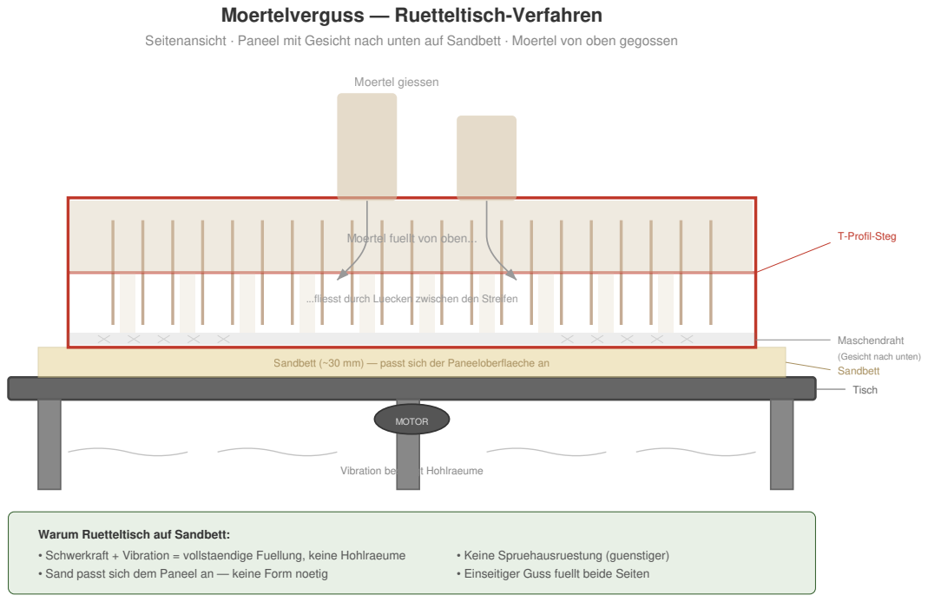
[picture p6: figure]
Moertelverguss — Ruetteltisch-Verfahren; MOTOR; Vibration beseitigt Hohlraeume; Moertel fuellt von oben...; Moertel giessen; T-Profil-Steg; Maschendraht; (Gesicht nach unten) Sandbett; Tisch; Warum Ruetteltisch auf Sandbett:; • Keine Spruehausruestung (guenstiger); • Einseitiger Guss fuellt beide Seiten

Dies ist die zentrale Innovation in der Anwendungsmethode:

Rütteltisch vorbereiten: Ebene Fläche, Motor darunter montiert

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
Seitenansicht · Paneel mit Gesicht nach unten auf Sandbett · Moertel von oben gegossen

Sandbett (~30 mm) — passt sich der Paneeloberflaeche an

...fliesst durch Luecken zwischen den Streifen

- Schwerkraft + Vibration = vollstaendige Fuellung, keine Hohlraeume
- Sand passt sich dem Paneel an — keine Form noetig

1.

Sandbett ausbreiten: ~30 mm sauberer, trockener Sand auf der Tischfläche. Der Sand passt sich allen Unregelmässigkeiten der Paneelfläche an und verhindert das Anhaften des Mörtels am Tisch.

Paneel mit der Vorderseite nach unten auf das Sandbett legen (Hühnerdrahtseite berührt Sand)

Mörtel mischen: 1:4 Zement:Sand + PP-Faser + puzzolanischer Zusatz, W/Z ~0,45–0,50 (giessfähig aber nicht flüssig)

Mörtel über die offene Rückseite des Paneels giessen, Lücken zwischen Streifen füllen und das Gitter bedecken

Vibration starten: Tisch 30–60 Sekunden laufen lassen. Die Vibration:

Treibt Mörtel durch die Lücken zwischen den Streifen

Füllt den zentralen Hohlraum vollständig

Eliminiert Hohlräume und Lufteinschlüsse

Mörtel dringt bis zum Frontflächengitter vor (das jetzt auf Sand liegt)

Abziehen — überschüssigen Mörtel bündig mit den Rahmenkanten abstreichen

Glätten (dies wird die Innenseite)

Rütteltisch-Bauanleitung: Eine DIY-Rütteltisch-Konstruktion (Motor, Plattform, Federn) wird in diesem Repository veröffentlicht, sobald das Design getestet und als sicher bestätigt wurde. Bis dahin funktioniert jede flache Plattform mit einem Betonrüttler, der an der Kante befestigt wird, für erste Versuche.

Warum Rütteltisch auf Sandbett? - Schwerkraft + Vibration = vollständige Füllung, keine Hohlräume - Sandbett = keine Form nötig, Sand passt sich der Paneelform an - Keine Sprühausrüstung nötig (günstiger als Sprühmörtel) - Einseitiger Verguss füllt beide Seiten — Mörtel fliesst durch die Streifenlücken - Gleichbleibende Qualität — Vibration eliminiert menschliche Fehler

### Schritt 9: Aushärtung

Paneel mit Plastikfolie abdecken, um Feuchtigkeit zu halten

Mindestens 7 Tage feucht halten (Sprühnebel oder feuchte Jutesäcke)

Volle Festigkeit nach 28 Tagen

Paneele können nach 7 Tagen vertikal (hochkant) gestapelt werden, um Platz zu sparen

Jedes Paneel mit Variantentyp und Produktionsdatum beschriften

Produktionsrate: 3–4 Paneele pro Tag mit 2 parallel laufenden Rütteltischen, Team von 4–6 Personen. Aktive Arbeit pro Paneel: ~15–20 Minuten. Passive Aushärtung: 7–28 Tage (Paneele härten aus, während neue produziert werden).

### Schritt 10: Transport und Installation

Paneele zur Baustelle transportieren mittels einfachem A-Rahmen-Wagen oder Lastwagen

Paneele in den Stahlgebäuderahmen an den Stützenpositionen verschrauben (vorgeschweisste Schraubwinkel an Stützen)

Benachbarte Paneele berühren sich Mörtel an Mörtel

Snap-Connect-Elektrik zwischen benachbarten Paneelen verbinden (12V + 120V)

Stromkreise vor dem Verputzen testen

### Schritt 11: Fertigstellung vor Ort

Fugen zwischen Paneelen mit Mörtel füllen

Hühnerdrahtstreifen über Fugen anbringen (falls nicht bereits durch die Paneelränder überlappend)

Kalkputz auftragen: 3–5 mm, handgeglättet, beide Seiten

Aushärten lassen (3–5 Tage feucht halten)

Kalkanstrich auftragen: 2–3 dünne Schichten mit Pinsel

Die fertige Wand ist fugenlos — keine sichtbaren Fugen, kein sichtbarer Stahl, keine sichtbaren Schrauben. Nur glatter Kalkputz mit der Textur einer handgefertigten Wand.

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
### Schritt 12: Bad-Abdichtung

Bad- und Duschbereiche erfordern eine wasserdichte Behandlung anstelle von Kalkputz:

Duschwände: Flüssige Abdichtungsmembran (Sika-1 oder ähnlich) direkt auf die Mörtel-Paneelfläche auftragen — 2 Anstriche, mit Pinsel. Dann flexibler Fliesenkleber + Keramik-/Porzellanfliesen. Kein Kalkputz im Duschbereich.

Badezimmerboden (gesamt): Abdichtungsmembran auf der Plattenoberfläche + Keramikfliesen. Die Platte muss ein Gefälle von 2 % zum Bodenablauf aufweisen (während des Plattengusses geformt).

Badezimmerwände ausserhalb der Dusche: Kalkputz ist akzeptabel, oder Fliesen für leichte Reinigung.

Decke (unter Galerie): Kalkputz — nicht direkt besprüht.

Die Mörtel-Paneeloberfläche bietet ausgezeichnete Haftung für die Flüssigmembran — keine zusätzliche Vorbereitung nötig. Einfach die Paneelfläche reinigen und auftragen.

### Entwässerung (in der Platte geplant)

Alle Entwässerungen müssen VOR dem Guss der Fundamentplatte installiert werden:

Toilettenabfluss: 4" (100 mm) PVC-Rohr zur Klärgrube. Position ist fix — kann später nicht verschoben werden.

Duschbodenablauf: 2" (50 mm) PVC mit Geruchsverschluss. Platte im Duschbereich um ~20 mm vertieft, um Wasser zurückzuhalten.

Spülbeckenabflüsse: 1,5" (40 mm) PVC mit Geruchsverschluss. Spülbecken Küche durch die Platte; Waschbecken Bad durch das W-Typ-Wasserpaneel oder die Platte.

Reinigungsöffnung: Zugängliche Armatur ausserhalb des Gebäudes an der Abflussleitung.

Das W-Typ-Paneel liefert Versorgungs-Steigleitungen (warm/kalt CPVC). Entwässerung ist immer in der Platte — Schwerkraftentwässerung benötigt Gefälle, das Paneele nicht bieten können.

## Qualitätscheckliste

[ ] Rahmenmasse innerhalb ±2 mm

[ ] Alle Klemmlöcher gebohrt und ausgerichtet

[ ] Bambusstreifen Borat-behandelt (grünlich/bläulicher Farbton sichtbar)

[ ] Diagonale vorgespannt (sollte beim Klopfen klingen)

[ ] Alle Drahtbindungen straff

[ ] Elektrostromkreise vor Mörtelverguss getestet (12V und 120V)

[ ] Mörtelkonsistenz korrekt (Setztest)

[ ] Vibration volle 30–60 Sekunden gelaufen

[ ] Keine sichtbaren Hohlräume auf der Vergussseite nach Vibration

[ ] Paneel mit Typ und Datum beschriftet

[ ] Mindestens 7 Tage ausgehärtet vor Handhabung

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
# Tragverhalten

## Systemarchitektur

Dieses Paneelsystem wurde für die Zusammenarbeit mit einem Stahl-Stützen-Riegel-Rahmen konzipiert — die Konfiguration, die wir für mehrstöckige Gebäude in Erdbebenzonen empfehlen. In dieser Konfiguration übernimmt der Stahlrahmen die Schwerkraft-und seismischen Lasten, während die Paneele seitliche Aussteifung, Wetterschutz, thermische Masse und integrierte Installationen liefern.

Die Paneele sind jedoch strukturell in der Lage, ohne Stahlrahmen zu funktionieren. Mit einer Drucktragfähigkeit, die typische Wohnlasten weit übersteigt (zwei seitliche L-Winkel-Posten L 40×40×4), kann eine Paneelreihe bequem ein Obergeschoss und Dach tragen, ohne eine unabhängige Stahlstruktur. Ein einfacher Holz- oder Bambus-Ringbalken am oberen Rand verbindet die Paneele und verteilt die Dachlast.

Zwei Konfigurationen:

Konfiguration | Einsatzbereich | Rolle der Paneele
Mit Stahlrahmen (empfohlen) | Mehrstöckig, hohe Erdbebenzonen, Gewerbe/ Institutionen | Ausfachung — Paneele werden in den Rahmen geschraubt, Stahl trägt Primärlasten
Ohne Stahlrahmen (einfacher, kostengünstiger) | Eingeschossig + Galerie/Zwischengeschoss, moderate Erdbebenzonen, Wohnbau | Tragend — Paneele tragen Dach und Obergeschoss direkt

Die folgenden Tragfähigkeitsschätzungen gelten für beide Konfigurationen. Der Stahlrahmen fügt Redundanz und Biegesteifigkeit hinzu, ist aber nicht erforderlich, damit die Paneele strukturell funktionieren.

## Seismisches Verhalten

### Diagonalverstrebung

Jedes Paneel enthält zwei diagonale Bambusstreifen (einen pro Seite, gegenüberliegende Ecken), die von vorne betrachtet ein X bilden. Unter seismischer Belastung:

Schub → Zug-Umwandlung: Wenn sich der Gebäuderahmen seitlich verformt, gerät eine Diagonale auf Zug, während die gegenüberliegende auf Druck beansprucht wird. Die Bambusdiagonale auf Zug widersteht der Schubkraft effizient — Bambus hat eine ausgezeichnete Zugfestigkeit (150–200 MPa für Guadua angustifolia).

Vorspannung: Diagonalen werden mit leichter Vorspannung eingebaut, wodurch Schlaffheit eliminiert und sofortige Lastabtragung gewährleistet wird.

Drahtbindungsgitter: Verzinkte Drahtbindungen an jeder Diagonal-Vertikal-Kreuzung (~16–20 Bindungen total) verteilen die Diagonalkraft über die gesamte Paneelfläche und verhindern lokales Versagen.

Geschätzte Verbesserung: 3–5× Schubsteifigkeit im Vergleich zu Paneelen ohne Diagonalverstrebung.

### Das )( Profil

Die HDPE-Blöcke halten die Bambusstreifen oben und unten 30 mm vom Steg entfernt. Auf halber Höhe biegen sich die Streifen nach innen zum Steg. Der Mörtel füllt diesen variierenden Spalt und erzeugt einen natürlichen Bogenquerschnitt:

Widerstand gegen Kräfte senkrecht zur Wandebene: Der Mörtelbogen wirkt wie ein flaches Gewölbe und verteilt Wind- oder Stossbelastungen effizient auf die steifen Rahmenkanten.

Mechanische Verzahnung: Der Mörtel mit variabler Dicke verriegelt die Bambusstreifen — sie können nicht herausgezogen werden, ohne den Mörtel zu brechen.

1.

2.

3.

•

•

### Duktiles Versagensverhalten

Die Kombination aus Bambusstreifen, Drahtbindungen und Mörtel erzeugt einen Verbundwerkstoff, der schrittweise versagt:

Zuerst: Mörtel reisst (sichtbare Warnung)

Dann: Drahtbindungen dehnen sich (Energieabsorption)

Dann: Bambusstreifen verformen sich (hohe Duktilität)

Der Stahlrahmen bleibt durchgehend intakt — das Gebäude stürzt nicht ein

Dies unterscheidet sich grundlegend von unbewehrtem Mauerwerk, das spröde versagt (plötzlicher Einsturz ohne Vorwarnung).

## Brandwiderstand

Mörtelummantelung: Die Bambusstreifen sind vollständig in Mörtel eingebettet (~85 mm Wanddicke). Mörtel ist nicht brennbar und wirkt als Wärmeisolierung für den Bambus.

Bambusverkohlung: Selbst wenn Feuer den Mörtel durchdringt, verkohlt Bambus langsam und vorhersagbar (ähnlich wie Holzbau). Der dahinterliegende Stahlrahmen behält seine strukturelle Integrität.

Kalkputz-Finish: Nicht brennbar. Bietet zusätzlichen Brandschutz.

Kein freiliegender Bambus: Nach Installation und Verputzen ist kein Bambus sichtbar oder für Flammen zugänglich.

## Thermisches Verhalten

Thermische Masse: ~85 mm Mörtel bieten erhebliche thermische Masse — absorbiert tagsüber Wärme, gibt sie nachts ab. Reduziert Temperaturschwankungen in tropischen Klimazonen.

Atmungsaktivität: Kalkputz ist dampfdiffusionsoffen. Feuchtigkeit durchdringt die Wand, statt eingeschlossen zu werden, was Kondenswasser und Schimmel verhindert.

Keine Dämmschicht: Das System enthält keine thermische Dämmschicht. In tropischen Klimazonen (dem primären Zielgebiet) ist thermische Masse wertvoller als Dämmung. Für gemässigte Klimazonen kann eine äussere Dämmschicht ausserhalb des Kalkputzes hinzugefügt werden.

## Akustisches Verhalten

Der dichte Mörtelkern bietet gute Schalldämmung:

Geschätzter STC (Sound Transmission Class): 40–45 für eine einzelne Paneelwand Mit Kalkputz auf beiden Seiten: STC 42–48

Vergleich: Standard-Betonblockwand: STC 40–45. Das Paneelsystem ist vergleichbar.

## Tragfähigkeit

Haftungsausschluss: Die untenstehenden Werte sind konservative analytische Schätzungen basierend auf Materialeigenschaften und Geometrie. Sie basieren NICHT auf Labortests. Verwenden Sie diese Werte nicht für die Tragwerksplanung ohne unabhängige Überprüfung. Die tatsächliche Leistung hängt von Materialqualität, Verarbeitungsqualität und Anschlussdetails ab. Siehe Erforderliche Tests weiter unten.

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
### Paneeleigengewicht

Komponente | Gewicht
Stahl-L-Winkelrahmen (L 40×40×4, 7 m bei 2,42 kg/m + Klemmleisten + Eckbleche) | ~22 kg
Mörtel-Kernfüllung (Basis: Zement-Sand, ~0,147 m³, ausgehärtete Dichte ~2 000 kg/m³) | ~294 kg
Bambusstreifen + Diagonalen (~30 % Hohlraumdichte) | ~38 kg
HDPE-Blöcke, Draht, Gitter, Leerrohr, Kabel | ~6 kg
Kalkputz (10 mm beidseitig) | ~100 kg
Gesamtgewicht Paneel, Basismischung | ~460 kg
Gewicht pro m² Wand, Basis | ~184 kg/m²
Gesamtgewicht Paneel, optimierte Bahareque-Mischung (puzzolanischer Kalk + Pasto estrella + 5 mm Putz) | ~380 kg
Gewicht pro m² Wand, optimiert | ~152 kg/m²
Trockenmontage-Versandgewicht (Rahmen + Bambus + Gitter + Installationen, vor dem Mörtelguss) | ~75 kg

Zum Vergleich: 150 mm Betonblockwand ≈ 180 kg/m². Das Paneelsystem (Basismischung) ist etwa gleich schwer wie konventionelles Mauerwerk pro Flächeneinheit, die optimierte Bahareque-Mischung etwa 15 % leichter. Entscheidend für die Logistik: das Trockenmontage-Versandgewicht (~75 kg) ist die Form, in der das Paneel von der Werkstatt zur Baustelle transportiert wird (Mörtel wird vor Ort gegossen).

### Axiale (vertikale) Last

Jedes Paneel hat zwei vertikale seitliche L-Winkel-Posten, die erhebliche Drucklasten tragen können:

Element | Querschnitt | Konservative axiale Tragfähigkeit
Seitlicher L-Winkel-Posten (L 40×40×4 mm) | A ≈ 304 mm² | ~36 kN pro Posten (bei σ = 120 MPa, ~50 % der A36-Fliessgrenze)
Zwei seitliche Posten pro Paneel | 2 × 304 mm² | ~72 kN pro Paneel (~7 200 kg)

Was das in der Praxis bedeutet:

Ein typisches eingeschossiges Haus mit Galerie/Zwischengeschoss und Dachziegeldach erzeugt ungefähr 200–400 kg Last pro Laufmeter Wand (Dach + Decke + Zwischengeschossdecke + Nutzlast). Ein einzelnes 1-m-Paneel kann das 18–36-Fache dieses Bedarfs tragen. Die Paneele benötigen keinen separaten Stahlrahmen, um ein Obergeschoss und Dach zu tragen.

Bei Verwendung mit Stahlrahmen ist diese axiale Tragfähigkeit reine Sicherheitsreserve — der Stahl trägt die Schwerkraftlasten. Bei Verwendung ohne Stahlrahmen sind die Paneele die tragende Struktur. In diesem Fall verteilt ein Holz- oder Bambus-Ringbalken am oberen Wandrand die Dachlast gleichmässig über alle Paneele und verbindet sie miteinander.

Knicken ist bei diesen Laststufen kein Problem wenn der L-Winkel im Paneelverbund eingebettet ist: Die 85 mm Mörtelwanddicke bietet dem Winkelrahmen kontinuierliche Seitensteifigkeit, und das Verhältnis von Paneelhöhe zu Wanddicke (~2 500/85 ≈ 29) liegt deutlich innerhalb akzeptierter Schlankheitsgrenzen für bewehrte Wände.

Wichtig: Schwachachs-Limitation offener Profile. Offene Strukturprofile — L-Winkel, T-Profile, C-Profile — haben minimale Steifigkeit um ihre Schwachachse. Ein freistehender L 40×40×4 Posten ohne Paneelabstützung (I_min ≈ 3,8 × 10⁴ mm⁴ um die Schwachachse durch die Ferse) würde unter mässiger Last knicken. Die oben angegebene Tragfähigkeit von 36 kN pro L-Winkel ist die axiale Fliessgrenze und ist NUR erreichbar, wenn der Winkel kontinuierlich durch die Paneelfüllung (Mörtel + Guadua) abgestützt wird. Diese Unterscheidung ist entscheidend für die Bauablauffolge — der L-Winkelrahmen darf nicht axial belastet werden, bevor die Paneele gegossen, ausgehärtet sind und die Verbundlast tragen. Für freistehende Stützen in mehrgeschossigen Gebäuden sind offene Profile nicht geeignet — verwenden Sie stattdessen quadratisches Hohlprofil (SHS).

### Laterale (horizontale / Schub-) Last

Dies ist der primäre strukturelle Beitrag der Paneele — der Widerstand gegen horizontale Kräfte aus Wind und Erdbeben.

Ohne Diagonalverstrebung (nur Mörtel + Vertikalstreifen):

Konservative Schätzung basierend auf der Mörtelschubfestigkeit (τ ≈ 0,3 MPa für 1:4 Zement:Sand-Mörtel) über den Paneelquerschnitt:

Schubfläche: ~85 mm × 1.000 mm = 85.000 mm²

Konservative Schubtragfähigkeit: 85.000 × 0,3 = ~25 kN pro Paneel

Mit Sicherheitsfaktor 3: ~8 kN Gebrauchslast pro Paneel

Mit Diagonalverstrebung (die ausgelegte Konfiguration):

Der diagonale Bambusstreifen (60 × 20 mm, Guadua angustifolia) auf Zug:

Querschnitt: 1.200 mm²

Konservative Zugfestigkeit: 80 MPa (bei ~50% der publizierten 150–200 MPa)

Diagonale Zugtragfähigkeit: 1.200 × 80 = ~96 kN

Horizontalkomponente (cos 69°): ~96 × 0,36 = ~34 kN pro Diagonale

Zwei Diagonalen (eine pro Seite, eine auf Zug): ~34 kN Drahtbindungen und Mörtelverzahnung liefern zusätzlichen Widerstand

Mit Sicherheitsfaktor 3: ~12–15 kN Gebrauchsschublast pro Paneel

Im Kontext: Ein 3 m breiter Wandabschnitt (3 Paneele) liefert ~36–45 kN Schubwiderstand. Ein eingeschossiges Wohngebäude in einer moderaten Erdbebenzone (PGA 0,2g) mit 30 kN seismischer Masse über der Wand benötigt ungefähr 6 kN Fundamentschubwiderstand pro Laufmeter Wand. Drei Paneele pro Meter liefern das 4–5-Fache dieses Bedarfs.

Dies sind sehr konservative Zahlen. Die Mörtelmatrix, das Drahtbindungsgitter und das )( Profil tragen alle zusätzlichen Widerstand bei, der oben nicht berücksichtigt wurde.

### Querlast (Wind / Stoss)

Das Paneel widersteht Druck senkrecht zur Wandfläche (Windsog/-druck, Stoss):

Der durch das )( Profil erzeugte Mörtelbogen wirkt als flaches Gewölbe zwischen den steifen oberen und unteren L-Winkeln

Konservative Schätzung für gleichmässigen Winddruck, wobei das Paneel als einseitig eingespannte Platte behandelt wird:

Parameter | Wert
Paneelspannweite (zwischen oberem/unterem L-Winkel) | 2,5 m
Paneelbreite | 1,0 m
Mörteldicke (Minimum, in der Mitte) | ~55 mm
Mörtelbiegezugfestigkeit (konservativ) | 1,0 MPa
Geschätzte gleichmässige Drucktragfähigkeit | ~0,7 kPa
Mit Sicherheitsfaktor 2 | ~0,35 kPa Gebrauchslast

Im Kontext: 0,35 kPa ≈ Windgeschwindigkeit ~25 m/s (90 km/h). Für höhere Windzonen übernimmt der Stahlrahmen (nicht das Paneel) die Windlast über die Riegel-Stützen-Verbindungen. Das Paneel muss nur den lokalen Druck zwischen seinen eigenen Rahmenelementen aufnehmen.

Das Bambusstreifen-Gitter und die Drahtbindungen bieten erheblichen zusätzlichen Querlastwiderstand, der im einfachen Plattenmodell nicht erfasst wird — das Paneel ist ein Verbundwerkstoff, keine reine Mörtelplatte.

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
### Punktlasten (Einrichtungsgegenstände, Regale, Schränke)

Befestigungsart | Ankermethode | Konservative Tragfähigkeit
Leichte Gegenstände (Bilder, Uhren, Handtuchhaken) | Mauernagel oder Schraube in Mörtel | 5–10 kg pro Anker
Mittlere Gegenstände (Regale, Spiegel, kleine Schränke) | Kunststoff-Spreizdübel in Mörtel (6–8 mm) | 15–25 kg pro Anker
Schwere Gegenstände (Küchenschränke, Warmwasserspeicher, TV-Halterung) | Durchgangsschraube zum L-Winkel-Steg | 50–100 kg pro Anker
Sehr schwere Gegenstände (Bücherregal, voller Vorratsschrank) | Mehrere Durchgangsschrauben zum L-Winkel + Verteilplatte | 200+ kg pro Befestigungspunkt

Tipp: Der L-Winkel-Steg verläuft an einer bekannten Position (entlang einer Paneelseite, in der Wandtiefe). Balkensucher oder Magnet lokalisieren ihn leicht. Durchgangsschrauben zum Steg bieten zuverlässige, hochbelastbare Verankerung, vergleichbar mit Stahlständer-Rahmenbau.

### Zusammenfassung — Konservative Tragfähigkeit in kg pro Paneel

Für Bauherren und Nicht-Ingenieure hier dieselben Zahlen in Kilogramm. Dies sind sehr konservative Gebrauchslasten (bereits durch Sicherheitsfaktoren von 2–3 geteilt). Die tatsächlichen Bruchlasten liegen 2–3× höher.

Lastart | Richtung | Konservative Gebrauchslast | Was das in der Praxis bedeutet
Schub (Erdbeben/ Wind) | Horizontal, in der Wandebene | ~1.200–1.500 kg pro Paneel | Eine horizontale Kraft von 1,2–1,5 Tonnen am oberen Rand eines einzelnen Paneels, bevor es als an der Gebrauchsgrenze betrachtet werden sollte. Ein typisches eingeschossiges Haus benötigt ~600 kg Schubwiderstand pro Laufmeter Wand — ein Paneel liefert das 2-Fache davon.
Querlast (Winddruck) | Senkrecht zur Wandfläche | ~90 kg verteilt über die Paneelfläche | Entspricht ~36 kg/m² gleichmässigem Druck. Eine sich stark gegen die Wand lehnende Person (~80 kg auf ~0,3 m²) liegt deutlich innerhalb der Kapazität.
Axial (vertikal) | Abwärts, durch das Paneel | Übertrifft Wohnlasten weit (~7 200 kg axiale Fliessgrenze pro Paneel im Verbund) | Die zwei seitlichen L-Winkel tragen weit mehr als ein typisches Dach + Obergeschoss pro Laufmeter Wand. Paneele können ein Obergeschoss und Dach ohne separaten Stahlrahmen tragen.
Punktlast auf Mörtel | Auszug / Abscheren am Anker | ~15–25 kg pro Anker | Ein Regalbrett mit 2 Ankern hält 30–50 kg sicher.
Punktlast auf L-Winkel | Durchgangsschraube | ~50–100 kg pro Schraube | Ein Küchenschrank mit 4 Durchgangsschrauben hält 200–400 kg sicher.

Wichtig: Dies sind Schätzungen, keine geprüften Werte. Sie werden durch physische Tests validiert. Verwenden Sie sie nicht für die Tragwerksplanung ohne unabhängige Überprüfung. Im Zweifelsfall schwere Gegenstände am Stahlgebäuderahmen befestigen, nicht am Paneel.

## Dauerhaftigkeit (80–100 Jahre Auslegungslebensdauer)

Komponente | Abbauprozess | Prävention | Erwartete Lebensdauer
Stahlrahmen | Korrosion | Feuerverzinkung (85 μm+) | 80–100 Jahre (nicht küstennah)

Komponente | Abbauprozess | Prävention | Erwartete Lebensdauer
Bambusstreifen | Insektenbefall, Pilzfäule | Boratbehandlung + Mörtelummantelung (alkalisch, anaerob) | 80+ Jahre
Mörtel | Karbonatisierung, Verwitterung | Geschützt durch Kalkputz (Opferschicht) | 100+ Jahre
Kalkputz | Oberflächenerosion, Mikrorisse | Selbstheilung (Karbonatisierung füllt Risse), erneuerbarer Kalkanstrich | Unbegrenzt bei Instandhaltung
Kalkanstrich | UV-Abbau, Regenerosion | Alle 5–10 Jahre erneuern | 5–10 Jahre pro Anstrich
Elektrik | Isolationsabbau | PVC-Leerrohr ermöglicht Kabelaustausch ohne Wandöffnung | Kabel: 30–50 Jahre, austauschbar
HDPE-Blöcke | Keine nennenswerten | UV-geschützt (innerhalb der Wand) | 100+ Jahre

### Instandhaltungsplan

Intervall | Massnahme | Geschätzte Kosten
Alle 5–10 Jahre | Kalkanstrich erneuern | 50–100 $ pro Gebäude
Alle 15–20 Jahre | Kalkputz inspizieren, Risse ausbessern | 100–300 $ pro Gebäude
Alle 30–40 Jahre | Elektrik inspizieren, Kabel bei Bedarf ersetzen | 200–500 $ pro Gebäude
Nach 40 Jahren | Stahlrahmen an zugänglichen Stellen inspizieren (bei Bedarf punktuell nachverzinken) | 200–400 $
Lebensdauer total | | 1.400–2.000 $

## Erforderliche Tests

Alle oben genannten Tragfähigkeitswerte sind analytische Schätzungen. Sie werden durch physische Tests im Rahmen der Projektentwicklung validiert. Die ersten Paneele werden gebaut und getestet, bevor ein Gebäude bezogen wird.

Geplantes Testprogramm:

[ ] Schubtests (ASTM E564 oder gleichwertig) — Paneele mit und ohne Diagonalen, zur Validierung der geschätzten 3–5× Verbesserung

[ ] Querbelastungstests — gleichmässiger Druck und Punktstoss, zur Validierung des )( Profil-Vorteils

[ ] Brandwiderstandstests (ASTM E119 oder gleichwertig) — Zeit bis zum Tragversagen
[ ] Zyklische Erdbebentests — massstäblicher Rütteltisch oder quasi-statische zyklische Belastung, zur Überprüfung des

duktilen Versagensverhaltens

[ ] Verbindungstests — Paneel-zu-Stützen-Schraubwinkel-Tragfähigkeit, Snap-Stecker-Dauerhaftigkeit

[ ] Langzeit-Verwitterungstests — beschleunigte Alterung von mörtelummantelten Bambusproben
[ ] Schalldämmungstests (ASTM E90) — STC-Messung

[ ] Punktlast-Auszugstests — Mauerwerksanker- und Durchgangsschrauben-Tragfähigkeit in Mörtel + L-Winkel

Testergebnisse werden in diesem Repository veröffentlicht, sobald sie vorliegen. Wenn Sie Zugang zu Prüfeinrichtungen haben und beitragen möchten, melden Sie sich bitte — gemeinschaftliches Testen mit verschiedenen Bambusarten und Mörtelmischungen macht dieses System für alle besser.

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
# Korrosionsschutz

## Designphilosophie

Das Paneelsystem verwendet mehrere Materialien in engem Kontakt. Jede Materialschnittstelle ist ein potenzielles Korrosionsrisiko. Dieses Kapitel dokumentiert die galvanische Analyse jeder Schnittstelle und die Präventionsstrategie.

Auslegungsziel: 80–100 Jahre ohne strukturelles Korrosionsversagen.

## Galvanische Reihe (relevante Metalle)

Von anodisch (korrodiert zuerst) zu kathodisch (geschützt):

Zink (Verzinkungsbeschichtung)

Aluminium (Insektengitter)

Baustahl (Rahmen, Klemmleisten)
Edelstahl (Schrauben)

Wenn zwei Metalle in elektrischem Kontakt in Gegenwart eines Elektrolyten (Feuchtigkeit) stehen, korrodiert das anodischere Metall bevorzugt. Dies ist die Grundlage der galvanischen Korrosion.

## Schnittstellenanalyse

### 1. Stahlrahmen ↔ Mörtel

Kontakt: Direkt — Mörtel wird auf und um den verzinkten Stahlrahmen gegossen
Risikoniveau: NIEDRIG

Analyse: Das alkalische Milieu des Zementmörtels (pH 12–13) passiviert die Zinkbeschichtung und bildet eine stabile Zinkoxidschicht. Dies ist tatsächlich eine vorteilhafte Kombination — der Mörtel schützt das Zink, und das Zink schützt den

Stahl. Dasselbe Prinzip wie Bewehrungsstahl in Stahlbeton.

Der puzzolanische Zusatz senkt den Mörtel-pH-Wert über Jahrzehnte graduell auf 10–11. Dies bleibt deutlich im Passivierungsbereich für Zink.

Prävention: Feuerverzinkung nach ISO 1461 (mindestens 85 μm). Keine zusätzlichen Massnahmen erforderlich.

### 2. Edelstahlschrauben ↔ Verzinkter Rahmen

Kontakt: Direkt — Schrauben durchdringen den verzinkten Steg
Risikoniveau: NIEDRIG-MITTEL

Analyse: Edelstahl ist kathodisch gegenüber Zink. Theoretisch treibt dies beschleunigte Zinkkorrosion am Kontaktpunkt an. In der Praxis eliminiert die Mörtelummantelung kontinuierliche Feuchtigkeit (den Elektrolyten), und die Zinkbeschichtung am Schraubenloch ist eine Opferfläche — das umgebende Zink schützt sie kathodisch.

Prävention: A2 (304) Edelstahlschrauben verwenden. Der Schraubenkopf wird von der Klemmleiste und dem Mörtel bedeckt. Kein Feuchtigkeitspfad.

### 3. Hühnerdraht ↔ Stahlrahmen

Kontakt: Indirekt — Hühnerdraht wird über die Mörteloberfläche geklammert, 30+ mm Mörtel vom Rahmen entfernt Risikoniveau: KEINES

Analyse: Beide sind verzinkter Stahl. Kein galvanischer Potentialunterschied. Durch Mörtelschicht getrennt. Kein Problem.

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
### 4. Aluminiumgitter ↔ Stahlrahmen

Kontakt: Indirekt — Aluminiumgitter liegt zwischen Hühnerdraht und Mörtel, 30+ mm vom Rahmen entfernt
Risikoniveau: KEINES

Analyse: Aluminium ist anodisch gegenüber Stahl (es würde bei direktem Kontakt zuerst korrodieren). Aber es besteht kein direkter Metall-auf-Metall-Kontakt — die Mörtelschicht bietet vollständige elektrische Isolation.

Prävention: Sicherstellen, dass das Aluminiumgitter bei der Installation nicht direkt den Stahlrahmen berührt. Die Mörtelschicht übernimmt dies natürlich.

### 5. Aluminiumgitter ↔ Hühnerdraht (verzinkter Stahl)

Kontakt: Direkt — Gitterschichten berühren sich bei der Installation
Risikoniveau: NIEDRIG

Analyse: Ein gewisses galvanisches Potential besteht. Aber beide sind nach der Installation in Mörtel eingebettet, wodurch der Feuchtigkeitspfad eliminiert wird. Das Aluminiumgitter ist eine dünne Opferschicht — selbst wenn etwas Korrosion an Kontaktpunkten auftritt, bleibt der strukturelle Hühnerdraht intakt.

Prävention: Keine Massnahmen erforderlich. Die Mörtelummantelung reicht aus.

### 6. Klemmleiste ↔ Rahmensteg

Kontakt: Direkt — Klemmleiste ist durch Bambusstreifen hindurch gegen den Steg geschraubt
Risikoniveau: KEINES

Analyse: Beide sind feuerverzinkter Baustahl. Gleiches Material, gleiche Beschichtung. Kein galvanisches Potential.

### 7. Stahlrahmen ↔ Bambusstreifen

Kontakt: Direkt — Bambusstreifen liegen am verzinkten Steg an
Risikoniveau: NIEDRIG

Analyse: Bambus ist kein Metall — keine galvanische Korrosion möglich. Die Sorge betrifft Feuchtigkeitsdochtwirkung durch den Bambus, die eine dauerhafte Feuchtigkeitszone am Stahl erzeugt. Die Mörtelummantelung eliminiert dies durch Abdichten der Schnittstelle. Die Boratbehandlung reduziert ausserdem die Feuchtigkeitsaufnahme.

## Umgebungsfaktoren

### Küstenumgebungen (< 1 km vom Meer)

Salzhaltige Luft beschleunigt den Zinkverbrauch dramatisch. In Küstenumgebungen: - Verzinkungsdicke auf 120+ μm erhöhen -316L Edelstahlschrauben verwenden (statt 304) - Zusätzliche Epoxid-Grundierung auf dem Rahmen vor der Verzinkung erwägen -Erwartete Rahmenlebensdauer in Küstenzone: 40–60 Jahre (vs. 80–100 im Binnenland)

### Hoher Niederschlag (> 2.000 mm/Jahr)

Für ausreichenden Dachüberstand sorgen (mindestens 1,5 m), um Regen von den Wandflächen fernzuhalten

Kalkputz wirkt als Opferschicht — alle 10–15 Jahre erneuern in Zonen mit hohem Niederschlag

Das Wandinnere (mörtelummantelt) ist vom Niederschlag nicht betroffen

### Tropische Luftfeuchtigkeit

Die Atmungsaktivität des Kalkputzes ist entscheidend — er lässt Feuchtigkeit durchdringen, statt sie einzuschliessen

Die Wand NICHT mit Farbe oder wasserabweisender Beschichtung versiegeln — dies schliesst Feuchtigkeit ein und beschleunigt den Abbau

Die Wand muss atmen: nur Kalkanstrich

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
## Zusammenfassung

Schnittstelle | Risiko | Prävention | Instandhaltung
Stahlrahmen in Mörtel | Niedrig | Feuerverzinkung | Keine (Inspektion nach 40 Jahren)
Edelstahlschrauben in verzinktem Rahmen | Niedrig-Mittel | A2 Edelstahl, Mörtelummantelung | Keine
Hühnerdraht zum Rahmen | Keines | Gleiches Material, Mörteltrennung | Keine
Aluminiumgitter zum Rahmen | Keines | Mörteltrennung | Keine
Aluminiumgitter zum Hühnerdraht | Niedrig | Mörtelummantelung | Keine
Klemmleiste zum Rahmen | Keines | Gleiches Material | Keine
Stahl zu Bambus | Niedrig | Boratbehandlung, Mörtelummantelung | Keine

Der Korrosionsschutz des Systems beruht auf drei Schichten: Verzinkung (primär), Mörtelummantelung (sekundär) und Kalkputz (tertiär/Opferschicht). Das Versagen einer einzelnen Schicht gefährdet das System nicht.

# Mitwirken

## Projektstatus

Dieses Projekt befindet sich in aktiver Entwicklung. Das Paneelsystem wurde entworfen und dokumentiert, aber noch nicht in voller Grösse gebaut. Der erste physische Bau ist in Kolumbien (Region Eje Cafetero) geplant.

Das bedeutet: - Die Dokumentation beschreibt ein Design, kein getestetes Produkt - Angaben zur strukturellen Leistung basieren auf ingenieurtechnischer Analyse, nicht auf Labortests - Ihr Feedback und Ihre praktische Erfahrung sind entscheidend für die Verbesserung des Systems

## Wie Sie beitragen können

### Probleme melden

Einen Fehler, eine Inkonsistenz oder einen Designmangel gefunden? Eröffnen Sie ein Issue. Geben Sie an: - In welchem Dokument oder Diagramm das Problem liegt - Was Ihrer Meinung nach falsch ist - Ihren Korrekturvorschlag (falls vorhanden)

### Verbesserungen vorschlagen

Haben Sie eine Idee, die das System verbessern könnte? Eröffnen Sie eine Diskussion oder ein Issue mit: - Dem Problem, das Sie lösen möchten - Ihrem Lösungsvorschlag - Allfälligen Kompromissen oder Bedenken

### Bauerfahrung teilen

Wenn Sie mit diesem System bauen (auch nur ein einzelnes Testpaneel): - Dokumentieren Sie Ihren Prozess mit Fotos - Notieren Sie Abweichungen von der dokumentierten Methode - Berichten Sie, was gut funktioniert hat und was nicht - Teilen Sie Materialkosten in Ihrer Region

Diese realen Daten sind wertvoller als jede Simulation.

### Strukturelle Tests

Wenn Sie Zugang zu Prüfeinrichtungen haben: - Schubtests (mit und ohne Diagonalverstrebung) - Querbelastungstests -Brandwiderstandstests - Zyklische Erdbebentests - Schalldämmungstests

Testergebnisse — auch informelle — helfen, die Evidenzbasis für die Normkonformität in verschiedenen Ländern aufzubauen.

### Bambusarten-Anpassung

Das System wurde für Guadua angustifolia entworfen, sollte aber mit anderen Struktur-Bambusarten funktionieren. Wenn Sie es für

eine andere Art anpassen: - Dokumentieren Sie die Art, Streifenmasse und allfällige Prozessänderungen - Notieren Sie Unterschiede im Verhalten (Biegsamkeit, Spaltung, Festigkeit) - Teilen Sie Ihre Ergebnisse, damit andere in Ihrer Region davon profitieren können

### Übersetzung

Helfen Sie, die Dokumentation in weitere Sprachen zu übersetzen. Derzeit verfügbar: - Englisch - Deutsch - Spanisch (Español)

Zum Übersetzen: Repository forken, neuen Sprachordner anlegen (z. B. fr/ , pt/ , id/ ), alle .md -Dateien übersetzen und

einen PR einreichen.

Die SVG-Diagramme sind sprachneutral gestaltet (nummerierte Beschriftungen mit Legenden) und müssen nicht übersetzt werden.

### Fotografie und Visualisierung

Fotos vom Bauprozess

Nahaufnahmen fertiger Paneele

Fotos der Gebäudeintegration

3D-Renderings

Montageanimationen

Visuelle Dokumentation hilft den Menschen, das System schneller zu verstehen als reiner Text.

## Lizenzierung

Alle Beiträge übernehmen die Doppellizenz des Projekts: - Hardware-Designs: CERN-OHL-S v2 (stark reziprok) - Dokumentation: CC BY-SA 4.0 (Weitergabe unter gleichen Bedingungen)

Mit dem Einreichen eines Beitrags stimmen Sie zu, ihn unter diesen Bedingungen zu lizenzieren.

Was das für Beitragende bedeutet: - Ihre Arbeit bleibt offen — niemand (auch wir nicht) kann sie schliessen - Andere müssen Sie nennen und Ableitungen unter derselben Lizenz teilen - Ihre Verbesserungen kommen jeder Gemeinschaft zugute, die mit diesem System baut

## Verhaltenskodex

Dieses Projekt existiert, um Menschen beim Bau sicherer, menschenwürdiger Behausungen zu helfen. Beiträge sollten diesem Zweck entsprechen:

Seien Sie konstruktiv — Kritik am Design ist willkommen, aber machen Sie sie konkret und umsetzbar

Seien Sie inklusiv — das System ist für Gemeinschaften mit unterschiedlichen Fähigkeiten und Ressourcen gedacht

Seien Sie ehrlich — wenn etwas nicht funktioniert, sagen Sie es. Falsche Leistungsangaben helfen niemandem.

Teilen Sie frei — reichen Sie keine Beiträge ein, die Beschränkungen durch geistiges Eigentum Dritter enthalten

## Kontakt

Designer: Jan Reuteler (janreuteler@icloud.com)

Repository Issues: Der beste Weg, technisch beizutragen

Allgemeine Fragen: Direkt an den Designer per E-Mail

BaharequeModular ist ein kleines Projekt mit grossen Ambitionen. Jeder Beitrag — von einer Tippfehlerkorrektur bis zu einem strukturellen Testbericht — bringt es voran.

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
# Kostenschätzung

Haftungsausschluss: Dies sind reine Materialkostenschätzungen, basierend auf Preisen von 2025 in Kolumbien (Region Eje Cafetero). Arbeitskosten sind nicht enthalten — das System ist für Gemeinschaftsproduktion konzipiert, bei der Arbeit beigetragen, nicht gekauft wird. Die Preise variieren erheblich nach Region, Währung und Lieferkette. Verwenden Sie diese als Ausgangspunkt, nicht als Budget.

In diesem Projekt werden zwei Mörtelmischungen dokumentiert: die Basismischung (Zement-Sand-Mörtel + 30 % Guadua-Anteil + 10 mm Kalkputz beidseitig) und die optimierte Bahareque-Mischung (puzzolanischer Kalk + Pasto-estrella-Fasern + 30 % Guadua + 5 mm Kalkputz). Beide Kostenaufstellungen sind unten gezeigt.

## Kosten pro Paneel — Basismischung (nur Material)

Material | Spezifikation | Menge pro Paneel | Stückpreis (USD) | Total (USD)
L-Winkelstahl | L 40×40×4 mm, ASTM A36 | 7,0 m | 4,00 $/m | 28,00 $
Verzinkung | Feuerverzinkt, Chargenprozess | 1 Rahmen | 2,00 $ | 2,00 $
Klemmleisten | 40×3 mm Flachstahl, verzinkt | 4,0 m | 1,00 $/m | 4,00 $
Eckbleche + Schrauben | Flachblech + M12/M8 | 1 Set | 3,00 $ | 3,00 $
Edelstahlschrauben | Selbstschneidend, A2 | 40 Stk. | 0,08 $ | 3,20 $
HDPE-Blöcke | Recycelt, 30×30 mm | 2,0 m | 1,50 $/m | 3,00 $
Bambusstreifen (vertikal + horizontal, 30 % Hohlraumdichte) | Borat-behandelte Guadua | ~400 m total | 0,05 $/m | 20,00 $
Bambusstreifen (diagonal) | 60×20 mm, behandelt | ~5,4 m | 0,30 $/m | 1,60 $
Drahtbindungen | Verzinkt | 5 m | 0,10 $/m | 0,50 $
PVC-Leerrohr | 16 mm Elektro | 5 m | 0,30 $/m | 1,50 $
12V-Kabel + Fassungen | 2-adrig + 6× E10 | 1 Set | 3,00 $ | 3,00 $
120V-Kabel + Stecker | 3-adrig + Snap-Stecker | 1 Set | 4,00 $ | 4,00 $
Hühnerdrahtgeflecht | Verzinktes Sechseck, 25 mm | 5,5 m² | 0,80 $/m² | 4,40 $
Zement | Portland Typ I | ~54 kg | 0,15 $/kg | 8,10 $
Sand (Mörtel) | Sauberer Flusssand | ~240 kg | 0,02 $/kg | 4,80 $
PP-Faser | Gehäckselt 6–12 mm | 200 g | 5,00 $/kg | 1,00 $
Puzzolanischer Zusatz | Vulkanasche oder RHA | 2 kg | 0,50 $/kg | 1,00 $
Paneel-Zwischensumme — Basis | | | | ~93 $

### Fertigstellung vor Ort, Basis (pro Paneelfläche)

Material | Menge pro Paneel | Kosten (USD)
Kalkputz (10 mm beidseitig) | ~25 kg Kalk + ~65 kg Sand | 6,50 $
Kalkanstrich (beidseitig) | ~2 kg Kalk | 0,50 $
Fertigstellung Zwischensumme — Basis | | 7,00 $

### Gesamte Materialkosten pro Paneel — Basis: ~100 USD

### Kosten pro m² fertige Wand — Basis

Paneelfläche: 1,0 m × 2,5 m = 2,5 m²

Materialkosten pro m²: ~40 USD/m²

## Kosten pro Paneel — optimierte Bahareque-Mischung (nur Material)

Die optimierte Mischung ersetzt Portland-Zement-Sand-Mörtel durch hydraulischen Kalk + Puzzolan, ersetzt PP-Faser durch Pasto-estrella (gratis, vor Ort gesammelt) und verwendet dünneren 5 mm Kalkputz. Gleicher L-Winkelrahmen, gleicher Bambusanteil, gleiche elektrische und tragende Komponenten.

Material | Spezifikation | Menge pro Paneel | Stückpreis (USD) | Total (USD)
L-Winkelstahl + Verzinkung + Klemmleisten + Eckbleche | (wie Basis) | | | 37,20 $
Edelstahlschrauben, HDPE, Bambus, Drahtbindungen, Leerrohr, Kabel, Geflecht | (wie Basis) | | | 41,20 $
Hydraulischer Kalk (Hauptbindemittel) | NHL 3.5 oder NHL 5 | ~42 kg | 0,30 $/kg | 12,60 $
Flugasche oder Reishülsenasche (Puzzolan, 30 % Zement-Äquivalent) | FA oder RHA | ~15 kg | 0,10 $/kg | 1,50 $
Sand (Mörtel) | Sauberer Flusssand | ~200 kg | 0,02 $/kg | 4,00 $
Pasto-estrella-Faser (getrocknetes Sterngras) | Vor Ort gesammelt | ~3 kg | gratis | 0,00 $
Paneel-Zwischensumme — optimiert | | | | ~96 $

### Fertigstellung vor Ort, optimiert (pro Paneelfläche)

Material | Menge pro Paneel | Kosten (USD)
Kalkputz (5 mm beidseitig) | ~12 kg Kalk + ~33 kg Sand | 3,30 $
Kalkanstrich (beidseitig) | ~2 kg Kalk | 0,50 $
Fertigstellung Zwischensumme — optimiert | | 3,80 $

### Gesamte Materialkosten pro Paneel — optimiert: ~100 USD

### Kosten pro m² fertige Wand — optimiert

Materialkosten pro m²: ~40 USD/m²

Beide Mischungen liegen materialkostenmässig etwa gleich (~100 $/Paneel, ~40 $/m²). Die optimierte Mischung tauscht leicht höhere Kalk-/Puzzolan-Zutatenkosten (gegenüber günstigerem Portlandzement) gegen niedrigere Kalkputzkosten (dünner), null PP-Faserkosten und deutlich geringere graue CO₂-Emissionen (siehe Umweltbilanz). Die optimierte Mischung ist daher ein klarer Gewinn bei CO₂ und Heritage-Authentizität bei praktisch gleichen Kosten.

•

•

•

## Vergleich mit konventioneller Bauweise

Wandsystem | Materialkosten pro m² (USD) | Lebensdauer | Anmerkungen
Dieses Paneelsystem — Basis | ~40 $ | 80–100 Jahre | Beinhaltet Tragstruktur, Elektrik, Finish
Dieses Paneelsystem — optimiert | ~40 $ | 80–100 Jahre | Gleicher Preis, weniger CO₂
Betonblock (15 cm) | 25–35 $ | 40–60 Jahre | Erfordert Bewehrung, Verguss, Putz, Farbe, separate Elektrik
Gebrannter Ziegel | 30–45 $ | 60–80 Jahre | Erfordert Mörtel, Putz, Farbe, separate Elektrik
Gipskarton auf Stahlständern | 20–30 $ | 20–30 Jahre | Keine thermische Masse, nicht tragend, erfordert Farbe, separate Elektrik
Konventioneller Bahareque (vor Ort) | 15–25 $ | 15–30 Jahre | Keine Elektrik, Oberflächenqualität variabel, kurze Lebensdauer ohne Ingenieurberechnung
Adobe-Block | 10–20 $ | 20–40 Jahre | Schlechtes Erdbebenverhalten, keine Elektrik, erfordert dicke Wände

Zentrale Erkenntnis: Das Paneelsystem kostet pro m² etwa 20–35 % mehr als Betonblock — beinhaltet aber integrierte Elektrik, hat die 1,5–2-fache Lebensdauer, bietet bessere thermische und akustische Leistung und erzeugt eine hochwertigere Oberfläche. Wenn man die Kosten für die separate Verkabelung eines Betonblockhauses einrechnet (~8–15 $/m² für Leerrohre, Kabel, Steckdosen und deren Installationsarbeit), ist das Paneelsystem auf Basis vollständig-fertige-Wand-bezugsbereit kostenwettbewerbsfähig.

## Kosten pro Haus (Grobschätzung)

Ein einfaches eingeschossiges Haus mit Galerie (50 m² Grundfläche, ~70 m² Nutzfläche inkl. Galerie):

Komponente | Menge | Kosten (USD)
Wandpaneele | ~40 Paneele (100 m² Wand) | 2.600–2.800 $
Fundament (Beton, Bewehrung) | ~5 m³ Beton | 800–1.200 $
Ringbalken (Holz/Bambus) | ~30 m | 200–400 $
Dach (Dachziegel + Pfetten) | ~65 m² | 1.200–1.800 $
Boden (Betonplatte oder Lehm) | ~50 m² | 400–800 $
Fenster + Türen | ~8 Öffnungen | 600–1.200 $
Elektroverteilung + Transformator | 1 Set | 200–400 $
Sanitär (einfach) | Küche + Bad | 300–600 $
Material total | | 6.300–9.200 $

Dies sind reine Materialkosten. Im Gemeinschaftsbau-Modell wird Arbeit beigetragen. Im Unternehmermodell kommen 40–60% für Arbeit hinzu.

Zum Vergleich: Ein vergleichbares Betonblockhaus im ländlichen Kolumbien kostet 12.000–20.000 $ (Material + Arbeit) und hält 40–60 Jahre. Dieses System erreicht vergleichbare oder bessere Qualität zu ungefähr der Hälfte der Kosten bei doppelter Lebensdauer.

## Strategien zur Kostenreduktion

Strategie | Einsparung | Anmerkungen
Eigenen Bambus ernten | 30–40% der Bambuskosten | Erfordert 1+ Hektar Guadua-Bestand, 4–5 Jahre Reife
HDPE aus Abfall recyceln | 100% der HDPE-Kosten | Schneidbretter, Rohrreste, Industrieabfall
Vulkanasche verwenden (gratis) | 100% der Puzzolankosten | Verfügbar in Andenregionen, sammeln und sieben
Sternengras-Faser statt PP | 100% der Faserkosten | Invasives Gras, gratis, zirkuläre Nutzung
Chargen-Verzinkung (50+ Rahmen) | 15–20% der Verzinkungskosten | Mengenrabatt vom Verzinkungswerk
Gemeinschafts-Sandgrube | 50–80% der Sandkosten | Falls lokaler Flusssandzugang verfügbar
Eigenen Kalk aus Kalkstein brennen | 50–70% der Kalkkosten | Erfordert Ofen (einmaliger Bau), lokaler Kalkstein

## Regionale Preisunterschiede

Materialkosten variieren stark nach Region. Die obigen Schätzungen gelten für Kolumbien. Grobe Multiplikatoren:

Region | Multiplikator | Anmerkungen
Kolumbien (Eje Cafetero) | 1,0× (Referenz) | Guadua reichlich, Vulkanasche verfügbar
Ecuador, Peru | 0,8–1,1× | Ähnliche Materialien, Caña Guadua verfügbar
Mittelamerika | 1,0–1,3× | Bambus verfügbar, Stahl evtl. teurer
Philippinen, Indonesien | 0,7–1,0× | Bambus reichlich und günstig, Arbeit sehr günstig
Indien | 0,6–0,9× | Bambus und Arbeit sehr günstig, Stahl erschwinglich
Subsahara-Afrika | 0,8–1,2× | Bambusarten variieren, Zement evtl. teuer
Südeuropa | 2,0–3,0× | Materialien verfügbar aber teurer

Diese Multiplikatoren sind grobe Richtwerte. Die grösste Einzelvariable sind die Bambuskosten — wenn Sie Ihren eigenen anbauen, ist er nahezu gratis.

# Umweltbilanz

## CO₂-Fussabdruck pro Paneel — Basismischung

Die Werte unten beziehen sich auf die aktuelle Basisspezifikation: L 40×40×4 Stahlrahmen + 30 % Guadua-Hohlraumanteil + Zement-Sand-Mörtel (Basis) + 10 mm Kalkputz beidseitig. Siehe Paneelaufbau und Materialien für Details.

Material | Menge pro Paneel | Gebundenes CO₂ (kg) | Emissionsquelle
Portlandzement (~18 % der Mörtelmasse) | ~54 kg | 43,2 | Kalzinierung + Brennstoff (~0,8 kg CO₂/kg Zement)
Stahl L-Winkelrahmen + Klemmleisten | ~22 kg Stahl | 39,6 | Stahlherstellung (~1,8 kg CO₂/kg Stahl)
Verzinkung (Zink) | ~0,7 kg Zink | 2,8 | Zinkverhüttung (~4 kg CO₂/kg Zink)
Sand (~82 % der Mörtelmasse) | ~240 kg | 1,2 | Gewinnung + Transport
Hühnerdraht + Aluminiumgitter | ~2 kg | 3,6 | Stahldrahtproduktion
PVC-Leerrohr | ~0,3 kg | 0,6 | PVC-Herstellung (~2 kg CO₂/kg)
Kabel + Stecker | ~0,5 kg | 1,5 | Kupfer + Kunststoff
HDPE-Blöcke | ~0,5 kg | 0,5 | Bei Recycling: ~1 kg CO₂/kg (vs. 3 für Neuware)
Kalk (im Putz, Kalzinierung) | ~22 kg Kalk | 18,0 | Kalkstein-Kalzinierung (~0,8 kg CO₂/kg Kalk)
PP-Faser (Mörtelzusatz) | ~0,2 kg | 0,4 | Polypropylen-Herstellung
Zwischensumme Emissionen | | ~111 kg CO₂
Bambus (beim Wachstum gespeicherter Kohlenstoff) | ~38 kg Trockengewicht (30 % Hohlraumanteil) | −60 bis −75 kg CO₂ | Bambus bindet ~1,6–2,0 kg CO₂ pro kg Trockenmasse
Kalkputz (absorbiert CO₂ bei Karbonatisierung) | ~22 kg Kalk | −6 bis −9 kg CO₂ | Kalkkarbonatisierung erfasst ~30–50 % des Kalzinierungs-CO₂ über Jahrzehnte zurück
Netto-CO₂ pro Paneel, Basismischung | | ~30–45 kg CO₂
Netto-CO₂ pro m² Wand, Basis | | ~12–18 kg CO₂/ m²

## CO₂-Fussabdruck pro Paneel — optimierte Bahareque-Mischung

Die optimierte Mischung (puzzolanischer Kalk + Pasto-estrella + 30 % Guadua + 5 mm Putz) liefert geringere graue CO₂-

Emissionen über mehrere Hebel:

Hebel | CO₂-Differenz pro Paneel gegenüber Basis
30 % Zement durch Flugasche oder RHA-Puzzolan ersetzen | −10 bis −13 kg
Portlandzement-Mörtel durch hydraulische Kalkbasis + Puzzolan ersetzen | −8 bis −12 kg
PP-Faser durch Pasto estrella (Sterngras) ersetzen | −0,5 kg
Dünnerer 5 mm Kalkputz beidseitig (−50 % Kalkvolumen) | −9 kg Kalzinierung, +4 kg geringere Karbonatisierungsrückgewinnung = −5 kg netto

Hebel | CO₂-Differenz pro Paneel gegenüber Basis
Gesamtreduktion | −24 bis −30 kg CO₂ pro Paneel
Netto-CO₂ pro Paneel, optimierte Mischung | ~6 bis 20 kg CO₂
Netto-CO₂ pro m² Wand, optimiert | ~3 bis 8 kg CO₂/m²

Mit lokal verfügbaren Puzzolanen (Vulkanasche in der kolumbianischen Kaffeeregion, Reishülsenasche aus Tolima/Valle del Cauca) und Pasto-estrella-Faser vom Grundstück selbst nähert sich die optimierte Bahareque-Mischung der Klimaneutralität pro Paneel. Wenn der Bambusbestand als bewirtschaftete CO₂-Senke geführt wird (Niederwaldrotation mit Biomasse-Permanenz), wird das System CO₂-negativ: Die Wand absorbiert über ihre Lebensdauer mehr CO₂ als beim Bau emittiert wurde.

## Vergleich mit konventionellen Wandsystemen

Wandsystem | kg CO₂ pro m² | Verhältnis zu Basis-Paneel
Dieses Paneelsystem — Basismischung | 12–18 | 1× (Referenz)
Dieses Paneelsystem — optimierte Bahareque-Mischung | 3–8 | ~0,4× Basis
Betonblock (15 cm, verputzt) | 40–60 | 3–4× Basis
Gebrannter Ziegel (verputzt) | 50–80 | 3–5× Basis
Stahlbetonwand (15 cm) | 70–100 | 5–7× Basis
Gipskarton auf Stahlständern | 15–25 | 1–1,5× Basis
Konventioneller Bahareque (Lehmputz, kein Stahlrahmen) | 3–8 | 0,3–0,5× Basis
Adobe-Block | 5–10 | 0,4–0,7× Basis

Die Basismischung des Paneelsystems erzeugt ~3× weniger CO₂ als Betonblock oder Ziegel — die beiden häufigsten

Wandmaterialien in Entwicklungsländern. Die optimierte Bahareque-Mischung erreicht das Niveau traditioneller Erdbauweise bei weit überlegener struktureller Leistung und Lebensdauer.

## Kohlenstoff pro Nutzungsjahr

Wenn die Lebensdauer einbezogen wird, wird der Vergleich noch deutlicher (bei 80–100 Jahren Auslegungslebensdauer für dieses System):

Wandsystem | kg CO₂/m² | Lebensdauer (Jahre) | kg CO₂/m²/Jahr
Dieses Paneelsystem — Basis | 15 | 90 | 0,17
Dieses Paneelsystem — optimiert | 5 | 90 | 0,06
Betonblock | 50 | 50 | 1,00
Gebrannter Ziegel | 65 | 70 | 0,93
Gipskarton auf Stahlständern | 20 | 25 | 0,80
Konventioneller Bahareque | 5 | 20 | 0,25

Über seine Lebensdauer erzeugt dieses Paneelsystem ~5–15× weniger Kohlenstoff pro Nutzungsjahr als Betonblock.

## Weg zur Klimaneutralität oder CO₂-Negativität

Das Paneelsystem ist bereits in der Basis kohlenstoffarm. Mit der optimierten Bahareque-Mischung und den folgenden weiteren Substitutionen wird es CO₂-negativ:

Substitution | CO₂-Einsparung pro Paneel | Machbarkeit
Puzzolanischen Kalkmörtel verwenden (optimierte Mischung) | −20 bis −25 kg | Kernspezifikation — siehe oben
Recycelten Stahl verwenden (Elektrolichtbogenofen) | −8 bis −12 kg | Abhängig von lokaler Stahl-Lieferkette
Bambusanteil weiter erhöhen (45 % Hohlraum) | −5 bis −8 kg zusätzliche Sequestrierung | Material ist gratis/günstig
Bio-Kalk verwenden (holzbefeuerter Ofen mit Niederwald-Brennstoff) | −5 kg | Traditionelle Kalkproduktionsmethode
Dünnerer Putz (5 mm → 3 mm) | −5 kg | Traditionelle Bahareque-Praxis
Gesamtes Reduktionspotenzial über das Optimierte hinaus | −43 bis −55 kg

Bei maximaler Reduktion sinkt das Netto-CO₂ pro Paneel in den Bereich −5 bis +5 kg — klimaneutral bis leicht negativ. Wenn der Bambusbestand als permanente CO₂-Senke bewirtschaftet wird, ist das System über seine Nutzungsdauer zuverlässig CO₂-

negativ.

## Wasserverbrauch

Mörtelmischung: ~15–20 Liter pro Paneel (Aushärtungswasser wo möglich wiederverwendet)

Aushärtung: ~50 Liter über 7 Tage (Sprühnebel-/Jutemethode)

Kalkputzmischung: ~10 Liter pro Paneel

Total: ~75–80 Liter pro Paneel, oder ~30 Liter pro m² Wand

Zum Vergleich: Betonblockproduktion verbraucht ~40–50 Liter pro m² Wand. Ziegelproduktion verbraucht ~100+ Liter pro m² (inklusive Ofenkühlung).

## Abfall

Stahlabschnitte: Recycelt (Schrottwert)

Bambusabschnitte: Kompostiert oder als Gartenstäbe/Mulch verwendet
Mörtelabfall: Minimal — Rütteltisch-Verguss ist präzise. Überschuss wird im nächsten Paneel wiederverwendet.

Sandbett: Unbegrenzt wiederverwendbar (Sand wird nicht verbraucht, nur verdichtet und gelockert)

HDPE-Abschnitte: Recycelt oder für kleinere Blöcke wiederverwendet

Verpackungsabfall: Minimal — die meisten Materialien kommen in Grossgebinden

Das System erzeugt nahezu keinen Bauabfall. Dies ist eine direkte Folge der Werkstatt-Vorfertigung — jeder Schnitt ist geplant, jedes Material ist abgemessen.

## Lebensende (nach 80–100 Jahren)

Wenn ein Paneel schliesslich das Ende seiner Lebensdauer erreicht:

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
Material | Entsorgung | Umweltauswirkung
Stahlrahmen | Recyceln (100% recycelbar) | Positiv — Stahlschrott hat Wert
Mörtel + Bambus | Zerkleinern und als Zuschlag oder Füllmaterial verwenden | Inert — Mörtel ist Kalzium/Silizium/Sand, Bambus ist organisch
Kalkputz | Kehrt zu Kalziumkarbonat (Kalkstein) zurück | Klimaneutral — das bei der Karbonatisierung absorbierte CO₂ wird wieder freigesetzt, netto null
HDPE-Blöcke | Recyceln | Recycelbar
Kupferkabel | Recyceln (hoher Schrottwert) | Positiv
PVC-Leerrohr | Recyceln wo Anlagen vorhanden | Prinzipiell recycelbar

Kein Sondermüll. Kein Asbest, keine Bleifarbe, kein synthetischer Isolierschaum, keine Druckimprägnierungschemikalien. Das Paneel besteht aus Stahl, Bambus, Sand, Zement und Kalk — es kehrt sauber in die Erde oder den Recyclingkreislauf zurück.

# Transport und Handhabung

## Paneelspezifikationen für die Handhabung

Eigenschaft | Wert
Masse | 1,0 m × 2,5 m × 85 mm
Trockenmontage-Gewicht (wie zur Baustelle geliefert) | ~75 kg
Fertiges Paneelgewicht (Basismischung, nach Vor-Ort-Verguss + Aushärtung + Putz) | ~440 kg
Fertiges Paneelgewicht (optimierte Bahareque-Mischung) | ~360 kg
Schwerpunkt | Mitte (symmetrische Bauweise)
Empfindliche Bereiche | Ecken, Kanten (Mörtel kann nach dem Verguss bei Stoss abplatzen)
Mindest-Aushärtung vor Handhabung | 7 Tage nach Vor-Ort-Verguss
Mindest-Aushärtung vor Installation | 14 Tage empfohlen — Hinweis: Beim Vor-Ort-Verguss-Modell wird das Paneel aufgestellt und der Mörtel an Ort und Stelle gegossen, sodass „Installation" und „Verguss" auf der Baustelle gemeinsam stattfinden, nicht nacheinander

## Primäres Produktionsmodell: Vor-Ort-Verguss

Das primäre Produktionsmodell ist, die Trockenmontage (~75 kg) zur Baustelle zu liefern und den Mörtel vor Ort gegen Schalung zu giessen. Das fertige ~440 kg Paneel wird nie als Einheit bewegt — es wird direkt Teil der Gebäudewand, was die Kosten für schwere Hebezeuge spart und das Transport-Risskrisiko eliminiert. Siehe Bauprozess für das vertikale Vor-Ort-Verguss-Protokoll.

Die Handhabung ausgehärteter Paneele (Abschnitte unten) gilt für das alternative Produktionsmodell: Werkstatt-Mörtelverguss auf einem Rütteltisch, mit vollständig ausgehärteten Paneelen, die als fertige Elemente zur Baustelle geliefert werden. Dieser Ansatz wird als dokumentierte Option für Bauherren beibehalten, die die Werkstattproduktion bevorzugen, fügt aber erheblichen Hebe-, Transport- und Ausschussraten-Aufwand hinzu.

## Tragen von Hand — Trockenmontage (~75 kg)

Die Trockenmontage (Stahl-L-Winkelrahmen + Bambus-Esterilla + Gitter + Installationen, vor dem Mörtel) wird von 2 Personen mit einem einfachen Gurtband angehoben und positioniert. Keine Tragelehre, kein Kran, kein Gabelstapler erforderlich — dies ist einer der zentralen Betriebsvorteile des Vor-Ort-Verguss-Produktionsmodells.

### Einfaches Gurtband-Tragen (Trockenmontage)

Ein einzelnes 50 mm × 500+ kg belastbares Gurtband um das trockene Paneel auf halber Höhe wickeln (~125 cm vom unteren Rand)

Jeder Träger greift ein Ende des Gurtbands mit beiden Händen, auf gegenüberliegenden Längsseiten des Paneels stehend

Gemeinsam anheben; das Paneel hängt vertikal zwischen ihnen

Im normalen Tempo gehen; das Paneel kann 30–50 m getragen werden, bevor eine Pause nötig ist

1.

2.
3.
4.

Gewicht pro Person: ~38 kg — vollständig handhabbar für die Kurzdistanz-Transporte, die typisch sind für Werkstatt-zu-Lastwagen, Lastwagen-zu-Baustellenlager und Lager-zu-Installation.

## Tragen von Hand — ausgehärtetes fertiges Paneel (alternatives Werkstatt-Verguss-

## Modell)

Ein fertiges Paneel mit ~360–440 kg kann nicht von Hand getragen werden. Es erfordert mechanisches Heben (Kettenzug, Kompaktlader oder kleiner Mobilkran). Dies ist der Hauptgrund, warum das Vor-Ort-Verguss-Modell bevorzugt wird.

Wenn werkstattgegossene Paneele bewegt werden müssen (z. B. Pilotphasen-Produktion bevor das Vor-Ort-Protokoll validiert ist), verwenden Sie:

### Einfache Tragelehre (ausgehärtetes Paneel, ~360–440 kg)

Zwei Bambusstangen (3 m lang, 8–10 cm Durchmesser), durch Schlaufen aus schwerem Gurtband gefädelt, das um das Paneel auf 1/4 und 3/4 Höhe gewickelt ist:

Paneel flach hinlegen

Zwei Gurtbänder (50 mm breit, belastbar 1 000+ kg) um das Paneel wickeln bei ~60 cm und ~190 cm vom unteren Rand

Auf jeder Seite eine Bambusstange durch beide Gurtschlaufen fädeln

4 Personen pro Stange, insgesamt 8 Träger für ein Paneel mit Basismischung bei ~440 kg, oder 6 Träger für ein Paneel mit optimierter Mischung bei ~360 kg

Paneel hängt vertikal zwischen den Stangen

Gewicht pro Person: ~55 kg (Basis) / ~45 kg (optimiert) — am oberen Rand der sicheren manuellen Handhabung. Lange Strecken oder Treppen sollten stattdessen mechanisches Heben verwenden.

Für jeden routinemässigen Produktionsablauf Gabelstapler, Kompaktlader oder Kettenzug statt manuellem Tragen für ausgehärtete Paneele verwenden. Manuelles Tragen ausgehärteter Paneele ist nur eine Notfall-/Pilotoption.

### Anheben und Kippen

Ein Paneel niemals an einer Kante anheben — der Mörtel kann unter Eigengewicht reissen, wenn er frei auskragt

Immer an zwei symmetrischen Punkten anheben, oder von unten mit Abstützung an der Rückseite

Kippen von flach zu vertikal: Zwei Personen halten die Oberkante, zwei heben die Unterkante. Langsam drehen. Unterkante während des Drehens auf einem gepolsterten Block abstützen.

## Werkstattlagerung

Nach der Aushärtung werden Paneele vertikal (hochkant) in einem A-Rahmen-Gestell gelagert:

Paneele gegen beide Seiten eines Winkelrahmens lehnen (wie ein offenes Buch)

10–15 Paneele pro Gestellseite

Paneele mit kleinen Holzdistanzstücken trennen für Luftzirkulation

Mit Plane oder Dach vor direktem Regen schützen (aushärtender Mörtel kann durch starken Regen vor vollständiger Aushärtung ausgewaschen werden)

Vom Boden fernhalten — untere Kante auf Kies oder Holzschiene stellen

Platzbedarf: ~3 m × 1 m Grundfläche pro 20–30 gelagerte Paneele.

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
## Lastwagentransport

### Beladen

Paneele vertikal im Laderaum aufstellen, an eine Seitenwand gelehnt

Holzdistanzstücke (Abschnitte, Bambus oder Schaumstoff) zwischen jedes Paneel legen

Paneele mit Ratschengurten an der Lastwagen-Seitenwand befestigen auf 1/3 und 2/3 Höhe

Paneele niemals flach aufeinander stapeln — das unterste Paneel bricht unter dem Gewicht des Stapels

Maximal ~15–20 Paneele pro Standard-Pickup (abhängig von Ladekapazität und Strassenverhältnissen)

### Strassenverhältnisse

Befestigte Strassen: Keine besonderen Vorsichtsmassnahmen ausser Gurten

Unbefestigte/raue Strassen: Geschwindigkeit reduzieren. Schaumstoff- oder Kartonpolster zwischen die Paneele legen. Fest gurten — Paneele können verrutschen und bei Stössen Kanten abplatzen.

Steile Steigungen: Sicherstellen, dass Paneele zum Hang geneigt sind (nicht davon weg), um Umkippen zu verhindern

Distanz: Keine Begrenzung. Paneele sind vollständig ausgehärtet und selbsttragend. Sie können jede Distanz transportiert werden.

### Entladen

Gurte von oben nach unten lösen

Zwei Personen pro Paneel — eine an der Oberkante, eine stützt die Unterkante

Jedes Paneel zum A-Rahmen-Lagergestell auf der Baustelle tragen

Paneele niemals fallen lassen oder schleifen — Mörtelkanten platzen leicht ab

## Kran / Hebezeug (für Obergeschosse)

Für zweigeschossige Gebäude müssen Paneele ins Obergeschoss gehoben werden:

Einfacher Mastbaum: Eine Bambus- oder Stahlstange mit Seil und Rolle. Zwei Personen ziehen das Seil, eine führt das Paneel. Funktioniert für geringe Mengen.

Kettenzug am Riegel: Einen 1 000 kg Kettenzug am Stahlriegel des Gebäudes befestigen (500-kg-Kettenzüge reichen für ausgehärtete Paneele nicht aus). Am Traggurt des Paneels einhaken. Eine Person bedient, eine führt. Schnell und kontrolliert. Für Trockenmontage-Hübe (~75 kg) reicht ein 500-kg-Kettenzug reichlich.

Gabelstapler (falls verfügbar): Gabel unter das Paneel (mit Karton geschützt). Anheben und direkt in Position setzen.

Paneele nicht werfen, rollen oder schleifen. Der Mörtel ist stark auf Druck, kann aber bei Punktbelastung reissen.

## Schäden und Reparatur

Schadensart | Ursache | Reparatur
Eckabplatzung (klein) | Stoss beim Transport | Mit Mörtel füllen, überputzen. Nur kosmetisch.
Kantenriss (oberflächlich) | Anstossen bei Handhabung | Mit Kalkputz füllen. Beeinträchtigt Struktur nicht.
Durchgehender Riss (Mörtel) | Fallenlassen oder schwerer Stoss | Paneel evtl. beeinträchtigt. Prüfen: Wenn Stahlrahmen intakt und Riss <2 mm, mit Mörtel füllen und beobachten. Wenn Riss >5 mm oder Rahmen verbogen, Paneel ablehnen.
Gebrochener Snap-Stecker | Verhaken beim Transport | Stecker ersetzen (gelötet oder gecrimpt).

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
Ausschussrate: Bei vernünftiger Sorgfalt ist mit <5% beschädigten Paneelen bei Transport und Handhabung zu rechnen, und <1% müssen abgelehnt werden. Abgelehnte Paneele können von Elektrokomponenten befreit und als Füllmaterial recycelt werden.

## Checkliste vor Transport

[ ] Paneel mindestens 7 Tage ausgehärtet (14 empfohlen)

[ ] Paneel mit Typ (P/O/S/W) und Produktionsdatum beschriftet

[ ] Elektrostromkreise getestet (12V + 120V Durchgangsprüfung)

[ ] Keine sichtbaren Risse >1 mm

[ ] Ecken intakt

[ ] Tragehilfen oder Tragelehre vorbereitet

[ ] Laderaum sauber, Distanzstücke bereit, Gurte verfügbar

[ ] Route geprüft auf Strassenverhältnisse (Brücken, Durchfahrtshöhe, Steigung)

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
# Klimaanpassung

Das Paneelsystem wurde für die kolumbianischen Anden (~2.000 m Höhe, ~2.500 mm Jahresniederschlag, 15–25°C ganzjährig) entwickelt. Dieses Kapitel dokumentiert Anpassungen für andere Klimazonen.

## Klimazonen

### Tropisch feucht (0–1.000 m, >2.000 mm Niederschlag, 25–35°C)

### Beispiele: Pazifikküste Kolumbien, Amazonasbecken, Philippinen, Indonesien, Westafrika

Faktor | Anpassung
Niederschlag | Mindestens 2,0 m Dachüberstand auf allen Seiten. Regenspritzer vom Boden erodiert Kalkputz am Sockel — Paneelunterkante 30–50 cm über Gelände auf einem Beton- oder Steinsockel anheben.
Luftfeuchtigkeit | Kalkputz ist entscheidend — er atmet. Die Wand niemals mit Farbe, Acrylatputz oder wasserabweisender Beschichtung versiegeln. Eingeschlossene Feuchtigkeit zerstört sowohl Bambus als auch Stahl.
Insekten | Boratbehandlung des Bambus ist nicht verhandelbar. Boratkonzentration auf 8–10% erhöhen (vs. Standard 5%). Mörtelummantelung bietet sekundären Schutz. Termitenbarrieren auf Fundamenthöhe.
Pilzwachstum | Kalkanstrich ist natürlich antimykotisch. In feuchten Tieflagen alle 3–5 Jahre erneuern (vs. 5–10 im Hochland). Kupfersulfat mit 1–2% zum Kalkanstrich hinzufügen für zusätzliche Pilzresistenz.
Hitze | Der 85 mm Mörtelkern bietet ausgezeichnete thermische Masse — absorbiert tagsüber Wärme, gibt sie nachts ab. Mit Querlüftung kombinieren (Fensteröffnungen an gegenüberliegenden Wänden).
Mörtelmischung | Standard 1:4 Zement:Sand funktioniert gut. Puzzolananteil auf 15% erhöhen (reduziert Hydratationswärme und verbessert Langzeitdauerhaftigkeit bei feuchten Bedingungen).
Kalkputz | Hydraulischen Kalk (NHL 3.5 oder NHL 5) statt Luftkalk verwenden — er härtet schneller und widersteht Regen besser während der Applikation.

### Tropisches Hochland (1.000–2.500 m, 1.500–2.500 mm Niederschlag, 12–25°C)

Beispiele: Kolumbianische Eje Cafetero, ecuadorianische Sierra, äthiopisches Hochland, kenianisches Hochland

Dies ist das Auslegungsklima — keine wesentlichen Anpassungen nötig.

Faktor | Anmerkungen
Niederschlag | 1,5 m Überstand reicht aus. 2,0 m für exponierte Fassaden.
Temperatur | Thermische Masse glättet Tag-Nacht-Schwankungen. Keine Dämmung nötig.
Luftfeuchtigkeit | Moderat — Kalkputz atmet ausreichend.
Insekten | Standard-Boratbehandlung (5%).
Kalkanstrich | Alle 5–10 Jahre.
Mörtelmischung | Standard 1:4 + 10% Puzzolan.

### Tropisch trocken / semi-arid (0–1.500 m, <800 mm Niederschlag, 25–40°C)
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
