jreuteler/bahareque-modular/BaharequeModular-EN.pdf

# BaharequeModular

## Open-Source Prefabricated Panel System

Designed by Jan Reuteler
janreuteler@icloud.com

First Publication — March 2026

Hardware: CERN-OHL-S v2 · Documentation: CC BY-SA 4.0

BaharequeModular — 1

# Contents

### 01 Design Philosophy

Origin in Colombian permaculture, traditional techniques worldwide, the hybrid approach, beauty, 80–100 year lifespan, community production, prior art, open

source

### 02 Panel Anatomy

Complete technical spec: T-bar frame, HDPE blocks, bamboo strips, )( profile, diagonal bracing, wire ties, electrical, mortar, finish layers, weight breakdown

### 03 Materials

Bill of materials per panel, bamboo species alternatives, steel specs, HDPE alternatives, mortar mix, lime plaster, chicken wire, aluminum mesh

### 04 Construction Process

Step-by-step production: frame fabrication, clamping, diagonal bracing, mesh, vibration table mortar pour, curing, installation, finishing, quality checklist
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
